jakeholland/firefly/docs/specs/S03-meshclient.md

# S03 · meshclient — embedded Meshtastic client library

## Purpose
A clean, reusable C library that makes this device a Meshtastic *client* — same role as the phone apps — over any byte transport. Wraps framing, the config handshake, node/position/message events, and sending. **Extraction-grade: no firefly includes.**

## Reference
Meshtastic client API docs + the archived Swift client in this repo's `archive/meshtastic-ios-app` branch (working handshake & framing to crib from). Protobufs: `meshtastic/protobufs` pinned submodule-free — vendored generated nanopb sources under `meshclient/proto/` with the generator script `meshclient/tools/gen_nanopb.sh`.

## Interface (`meshclient/include/mc_client.h`)
```c
typedef struct {           // byte transport vtable — UART, TCP, later BLE
  int  (*write)(void *io, uint8_t const *buf, size_t len);
  int  (*read) (void *io, uint8_t *buf, size_t maxlen);   // nonblocking, 0 = nothing
  void *io;
} mc_transport_t;

// Packet metadata Meshtastic already gives a client, translated at this
// boundary into firefly-side enums (issues #33, #35). Protobuf enum values
// never reach core/.
typedef enum { MC_LOC_UNKNOWN, MC_LOC_MANUAL,                 // asserted, not measured
               MC_LOC_INTERNAL, MC_LOC_EXTERNAL } mc_loc_source_t;
typedef enum { MC_RX_PATH_UNKNOWN, MC_RX_PATH_DIRECT,
               MC_RX_PATH_INDIRECT } mc_rx_path_t;

typedef struct {          // per-packet radio measurements, all presence-flagged
  bool has_rssi;  int16_t rssi_dbm;
  bool has_snr;   float   snr_db;
  mc_rx_path_t rx_path;   // rssi/snr attributable to `from` only when DIRECT
} mc_rx_meta_t;

typedef struct {
  void (*on_state)(void *u, mc_state_t s);                     // DISCONNECTED/HANDSHAKE/READY
  void (*on_node)(void *u, mc_nodeinfo_t const *n);            // id, names, hw, battery, rx_path
  void (*on_position)(void *u, uint32_t node, mc_position_t const *p);  // p.loc_source, p.precision_bits
  void (*on_text)(void *u, uint32_t from, uint32_t to, char const *utf8, size_t len);
  void (*on_private)(void *u, uint32_t from, uint32_t to, uint32_t portnum,
                     uint8_t const *payload, size_t len);      // firefly protocol rides here
                     // `to` added by issue #123 ([api]): the MeshPacket's destination,
                     // delivered exactly as on_text delivers it (broadcast / node id /
                     // MC_ADDR_UNKNOWN), so 1:1 private traffic classifies DIRECT.
  void (*on_my_info)(void *u, uint32_t my_node_id);
  void (*on_rx_meta)(void *u, uint32_t from, mc_rx_meta_t const *m);  // every packet w/ a sender
  void *user;
} mc_events_t;

void mc_init(mc_client_t *c, mc_transport_t t, mc_events_t ev, ff_clock_t const *clock);
void mc_tick(mc_client_t *c, uint32_t now_ms);   // pump read/parse/heartbeat; call ~50 Hz
void mc_connect(mc_client_t *c);                  // starts want_config handshake
int  mc_send_text(mc_client_t *c, uint32_t dest, char const *utf8);      // dest=0xFFFFFFFF broadcast
int  mc_send_private(mc_client_t *c, uint32_t dest, uint32_t portnum,
                     uint8_t const *payload, size_t len, bool want_ack);
int  mc_send_position(mc_client_t *c, ff_latlon_t p);        // rarely needed; comms brain owns GPS
mc_state_t mc_state(mc_client_t const *c);
```

## Behavior
- **Framing:** stream protocol `0x94 0xC3 [len_hi] [len_lo] [protobuf FromRadio/ToRadio]`; resync on garbage by scanning for magic; max frame 512 B.
- **Handshake:** on connect send `ToRadio.want_config_id = random`; consume NodeInfo/Config/Channel dump; READY on `config_complete_id` match. Auto-reconnect with 2 s backoff if transport errors or 30 s silence (send heartbeat every 15 s).
- **Decode scope v1:** MyNodeInfo, NodeInfo, Position, MeshPacket(decoded: TEXT_MESSAGE_APP, POSITION_APP, PRIVATE range). Everything else skipped silently but counted (`mc_stats`).
- **nanopb** with static allocation; callback fields sized: names 40 B, text 237 B (Meshtastic max).
- **Packet metadata (added for #33/#35).** Meshtastic already hands a client more than the payload; this library surfaces it instead of dropping it, translated into firefly-side enums:
  - **Position provenance.** `Position.location_source` → `mc_position_t.loc_source`. MANUAL means the position was *asserted* (an installer typed it in), not measured — a fixed-position landmark re-broadcasts the same asserted point forever, so freshness is a category error for it (#33). `LOC_UNSET` and an absent field are the same bytes on the wire (proto3 implicit presence); both fold to `MC_LOC_UNKNOWN`, which is a distinct enum member, not a sentinel. Unrecognized future wire values also fold to UNKNOWN rather than leaking a raw number.
  - **Per-packet RSSI/SNR.** `MeshPacket.rx_rssi`/`rx_snr` → `on_rx_meta`, fired for **every** inbound packet naming a sender — including encrypted payloads and out-of-decode-scope portnums, since the radio measured the signal regardless. Breadth is deliberate: position broadcasts alone arrive on a multi-minute interval, far too slow for a 5 s RSSI trend window. Fires *before* the payload event for the same packet, so callers can correlate by `from` without buffering.
  - **Hop path is the qualifier, not a nicety.** RSSI is measured against whatever signal actually arrived — for a relayed packet that is the *relay's* transmission, not the originator's. `mc_rx_path_t` says whether the reading may be attributed to `from` at all. Derived from `hop_start`/`hop_limit`, plus the sender's `Data.bitfield` as the tell for firmware new enough to populate `hop_start` (pre-2.3.0 never did, so a bare `hop_start == 0` reads UNKNOWN, never DIRECT); `via_mqtt` forces INDIRECT. `NodeInfo` gets the same field from its explicit-presence `hops_away`.
  - **Unknown stays unknown.** Every added field is presence-flagged or has an explicit UNKNOWN member; none uses an in-band sentinel. One irreducible gap is documented rather than papered over: `rx_snr` has implicit presence, so a genuine 0.0 dB reading is byte-identical to an absent field and is therefore reported as `has_snr == false` — under-claiming rather than fabricating.
  - **Implausible is not a measurement.** Both readings are decoded from unvalidated wire bytes, so both are range-gated (`MC_RSSI_MIN_DBM`/`MC_SNR_MIN_DB` and friends, set far wider than any real radio) and reported **absent** when they fall outside — never clamped, never truncated. `rx_snr` additionally rejects NaN, which compares unequal to everything including `0.0f` and would otherwise pass a bare presence test while silently failing every downstream comparison. Saturating instead of absenting would be actively harmful here: `ff_crew`'s close-range predicate is `rssi_dbm > -60dBm`, which a clamped `INT16_MAX` or a truncated `0` both satisfy, fabricating a CLOSE lock out of a malformed packet.
  - **Coordinate precision (#47).** `Position.precision_bits` → `mc_position_t.has_precision_bits`/`precision_bits`, on both decode paths. Meshtastic channels truncate outgoing coordinates to the channel's `positionPrecision` high bits — 13 on the default public channel, a ~5.8 km grid that produced a measured 2.7 km error indistinguishable from a full fix in the coordinates alone; this field is the only wire-level tell. Present ⇒ 1..32. Implicit presence again: wire `0` is byte-identical to absent (and `0` means "position disabled" in channel config, so it never legitimately accompanies coordinates) — both read absent. A value `> 32` is untrusted-RF garbage and reads **absent, not clamped** (a clamp to 32 would assert full precision for a malformed packet). Absent is never "full precision" — it means the sender didn't say. Presence is *not* uniform across paths in practice (hardware-verified, 2× Heltec V3 @ 2.7.26): live packets stamp the field affirmatively even at full precision (`precisionBits: 32` observed on a `positionPrecision: 32` channel), while the same node's nodeDB row replays with the field absent on both truncated and full-precision channels — stock firmware's `PositionLite → Position` conversion never copies it. NodeInfo positions therefore typically read absent even for senders whose live packets state it, and the replay is the cold-boot path.
  - **Deliberately not surfaced:** `NodeInfo.snr`. It is a cached "SNR of the last message we heard" with implicit presence and no reception timestamp (the same path already hardcodes `has_rx_time = false` for want_config replays). A signal reading that cannot be timestamped cannot feed a trend window, and exposing it would invite treating replayed history as a live measurement.
- Transports shipped: `mc_transport_tcp` (POSIX, sim) and `mc_transport_uart` stub landing with S15.

## Acceptance criteria
1. Framing: byte-dribble (1 byte per read) and garbage-prefix fixtures both yield the framed protobuf exactly once; oversize len resyncs without overflow.
2. Handshake against recorded meshtasticd byte capture (`tests/fixtures/handshake.bin`) reaches READY and emits ≥1 on_node + on_my_info.
3. Position packet fixture → `on_position` with correct 1e-7 degree conversion and rx_time.
4. `send_text` produces a ToRadio frame that meshtasticd accepts (e2e, S14 nightly) and byte-golden matches fixture (unit).
5. `on_private` fires for portnum 256–511 with payload passed through untouched.
6. Silence 30 s → reconnect: state sequence READY→DISCONNECTED→HANDSHAKE observed with mock transport.
7. Library has zero includes from `core/` or `app/` except `ff_clock_t` (moves to a shared `platform/` header).
8. Fuzz smoke: 10k random-byte frames parse without crash/UBSan findings.
9. **Position provenance (#33).** Each `LocSource` value reaches `mc_position_t.loc_source` as its firefly-side counterpart, on both the live-packet and the NodeInfo-replay path. An **absent** field, an explicit `LOC_UNSET`, and an unrecognized future value all read `MC_LOC_UNKNOWN` — never `MC_LOC_INTERNAL`, i.e. "the sender said nothing" is never reported as a GPS measurement. `mc_nodeinfo_t.rx_path` follows `hops_away`'s explicit presence: absent reads UNKNOWN, not DIRECT.
10. **Per-packet radio metadata (#35).** `on_rx_meta` fires with `has_rssi`/`rssi_dbm` and `has_snr`/`snr_db` for decoded, out-of-scope, and encrypted packets alike, and before the payload event for the same packet; never for `from == 0`; and a client that leaves the callback NULL is unaffected. Absent RSSI reads `has_rssi == false` while a genuine **0 dBm** reading reads present-and-zero (the case an in-band sentinel would corrupt). Implausible readings read **absent, not clamped**: an RSSI outside `[MC_RSSI_MIN_DBM, MC_RSSI_MAX_DBM]` (notably `65536`, which truncates to the protected `0`), and an SNR that is NaN, ±infinity, or outside `[MC_SNR_MIN_DB, MC_SNR_MAX_DB]`; `snr_db` is zeroed whenever `has_snr` is false, so an ignored flag never yields NaN. Readings at the edge of the physically plausible (−150/+20 dBm, −30/+15 dB) must still read **present**, so the gate can only reject garbage. `rx_path` is DIRECT only when positively established — `hop_start == 0` without the sender's bitfield, and `hop_limit > hop_start`, both read UNKNOWN; `via_mqtt` reads INDIRECT.

11. **Coordinate precision (#47).** `precision_bits` reaches `mc_position_t` presence-flagged, on both the live-packet and the NodeInfo-replay path. Stated values 1–32 read present (1 and 32 inclusive — boundaries are statements, not garbage); wire `0` reads absent (byte-identical to an absent field, proto3 implicit presence); `33` and arbitrarily large values read **absent, not clamped and not reduced mod 32** (`0xFFFFFFFF` would otherwise read 31). When absent, `precision_bits` is zeroed so a flag-ignoring caller can never pass a `>= N` precision gate on leftover wire bytes.

## Slices
a) framing+resync · b) protobuf gen + decode path · c) handshake state machine · d) send path · e) TCP transport + fixture capture tool (Python script recording meshtasticd session) · f) packet metadata: position provenance + per-packet RSSI/SNR/hop path (AC9, AC10; issues #33, #35) · g) coordinate precision (AC11; issue #47).

**f and g make the data available; they do not consume it.** Wiring `on_rx_meta` into `ff_crew_on_rssi`, and giving `ff_crew` an asserted-position state off the live/stale/lost axis, both belong to S16 slice b1 (callback wiring) — see `docs/specs/S16-app-shell.md`. Until that lands, the Radar face's CLOSE mode still has no path from a radio to the screen. Likewise the *consumer* of precision — the Radar face refusing to render a confident metre-level distance from kilometre-level data — stays with issue #47, alongside the Firefly-channel provisioning that makes full precision available at all.

## Amendments

### `mc_transport_t.write()` backpressure contract (debt/meshclient-contracts)

The vtable's `write()` had no documented contract for a partial or zero
return: `mc_write_bytes`/`mc_send_frame` (`mc_client.c`) treated any
`write() <= 0` as a hard failure and escalated straight to reconnect. Only
`mc_transport_tcp` happened to satisfy that, by retrying `EAGAIN`/
`EWOULDBLOCK` internally up to 200 times so its own `write()` never
actually returns 0. The UART transport landing with S15 will naturally
return 0 for "TX ring full" — treating that as a hard failure would fire a
reconnect storm every time the device's own output momentarily outpaced
the ring.

**Contract, now stated in `mc_client.h`'s `mc_transport_t` doc comment:**
`write()` returns the number of bytes accepted, `0..len`. `0` means
"accepted nothing right now, try again later" — **not** an error. A
negative return is a hard transport failure and is escalated immediately,
no retry.

`mc_write_bytes()` now retries a `0` return up to `MC_WRITE_ZERO_RETRY_BUDGET`
(64, `mc_client.c`) times — a *call* budget, not a wall-clock one: the
retry loop has no clock of its own in scope, no yield point, and no sleep
between attempts, so a millisecond-resolution deadline could read the same
timestamp for the entire loop and fail to bound anything. 64 calls is
chosen to comfortably outlast one transport's momentary stall (a UART TX
ring draining at its own pace) without turning a single frame's
back-pressure into a spurious reconnect, while a permanently stuck
transport still fails in a small, bounded number of calls rather than
spinning forever. `mc_transport_tcp` is unchanged — it still never returns
0, so this budget is never exercised on the shipped dev transport.

Tests: `S03_debt_write_backpressure_below_budget_sends_frame_no_reconnect`,
`S03_debt_write_backpressure_budget_exhausted_triggers_reconnect`,
`S03_debt_write_backpressure_transport_stuck_forever_fails_at_exactly_budget`
(a transport that returns 0 unconditionally, forever — added after review
on #170 so the budget pin isn't coincidental to a countdown mock that
happens to recover exactly at the boundary),
`S03_debt_write_negative_return_fails_immediately`
(`meshclient/tests/test_meshclient.c`).

### Honest `decode_errors` on the live Position path (debt/meshclient-contracts)

`mc_process_mesh_packet`'s `POSITION_APP` branch counted `decode_errors++`
whenever `pb_decode()` succeeded but the message lacked
`latitude_i`/`longitude_i` — indistinguishable, in the stats, from genuine
protobuf corruption. A Position broadcast with no coordinates is a
legitimate "no GPS fix yet" message (both fields are proto3 implicit
presence, so "absent" and "explicit zero" are the same wire bytes); it is
not malformed. The NodeInfo replay path already got this right — it
silently emits nothing for the same missing-coordinates condition, with no
counter touched at all.

**Fix:** `decode_errors` now increments *only* when `pb_decode()` itself
fails. A well-formed, no-fix Position emits no `on_position` event and
touches no counter — matching the NodeInfo path exactly, not even
`decode_skipped` (the portnum *is* in decode scope; nothing was skipped,
there was simply nothing to report).

Tests: `S03_debt_position_no_fix_yet_does_not_count_as_decode_error`,
`S03_debt_position_corrupt_protobuf_counts_decode_error`
(`meshclient/tests/test_meshclient.c`). Mutation-tested: reverting to the
old single-branch `decode_errors++` makes
`S03_debt_position_no_fix_yet_does_not_count_as_decode_error` fail
(`Expected 0 Was 1`) and nothing else.

### Bounded `mc_tick()` drain — `MC_TICK_MAX_FRAMES` (debt/meshclient-contracts)

`mc_tick()`'s read loop previously drained the transport completely in one
call. meshtasticd's `want_config` response can burst a NodeInfo dump of
the whole mesh's node database in one delivery, and `mc_tick()` shares its
calling tick with UI rendering (`ff_shell.c`'s `ff_shell_tick`) — decoding
an unbounded burst back-to-back in one call could stall that shared tick.

**Fix:** `mc_tick()` now dispatches at most `MC_TICK_MAX_FRAMES` (32,
documented in `mc_client.h` next to `mc_client_t`) complete frames per
call. 32 is chosen against the largest realistic burst: even a 100-node
want_config dump (on the order of Meshtastic's stock node-database size on
typical hardware) finishes draining in ~4 calls — well under 100 ms at the
spec's ~50 Hz cadence — while any single `mc_tick()` call never does more
than 32 frames' worth of `pb_decode()` + dispatch.

**Implementation (revised after review on #170):** the first version of
this fix read the transport one byte at a time to make "nothing lost when
the cap lands mid-burst" trivially true, but that traded away the actual
goal — a 4160-byte/40-frame burst went from 66 `transport.read()` calls
(pre-fix, 64-byte chunks) to 4161 (one recv() syscall per byte on TCP), a
regression on cheap-per-tick-work on the shared UI tick. `mc_tick()` now
reads `MC_TICK_READ_CHUNK`-sized chunks again (64 bytes, matching the
pre-existing chunk size), and the "nothing lost" guarantee is carried by
`mc_client_t.tick_carry_buf`/`tick_carry_len`/`tick_carry_pos` instead of
by the read granularity: `mc_framer_t.buf` only ever accumulates the ONE
frame currently in progress, so it can't hold raw leftover bytes spanning
a chunk boundary — when the cap lands mid-chunk, the unconsumed remainder
is copied into `tick_carry_buf` and fed to the framer FIRST on the next
`mc_tick()` call, before any further `transport.read()`. No byte is ever
read from the transport without being fed to the framer either within the
same call or (via the carry) the next one, and frame order is preserved
because the carry is always drained before fresh reads resume.

Tests (`test_meshclient.c`):
- `S03_debt_mc_tick_bounded_drain_caps_frames_per_call` — feeds
  `MC_TICK_MAX_FRAMES + 8` (40) frames / 1000 bytes into a fake transport;
  the first `mc_tick()` call dispatches exactly 32, the second dispatches
  the remaining 8, payload ordering checked end-to-end. The same test also
  pins the read-call-count regression: total `transport.read()` calls
  across both `mc_tick()` calls equals `ceil(1000/64) + 1 = 17` (both the
  formula and the literal `17` are asserted), never the review's reported
  4161-calls-for-a-similar-burst shape.
- The existing byte-dribble/resync (AC1) tests exercise `mc_framer_feed()`
  directly and are unaffected; the AC8 fuzz-smoke test calls `mc_tick()`
  in a loop until its mock transport drains, since a single call is not
  guaranteed to drain everything.

Mutation-tested:
- Dropping the carry (stashing nothing, just `break`ing on cap-mid-chunk)
  → `S03_debt_mc_tick_bounded_drain_caps_frames_per_call` fails
  (`Expected 40 Was 38`, frames genuinely lost).
- Restoring byte-at-a-time reads → the same test's read-call-count pin
  fails (`Expected 17 Was 1001`).
Both mutations were reverted with targeted edits after a fresh rebuild
confirmed the failure (object-file hash checked to rule out a stale
binary).

### `FromRadio.rebooted` is an immediate session loss, not a silence timeout (debt/S03-reboot-session-loss, NAME-in-Settings bench finding 2026-09-06)

Bench finding, real puck + comms brain (Meshtastic 2.7.26), frame-level
instrumentation: pushing a Meshtastic `set_owner` admin write (S11's NAME
feature, `mc_send_set_owner`) a second time in the same session got no
routing ack and no `get_owner_response` reply, forever — even though the
comms brain's owner really changed every time (confirmed via the CLI).
Root cause: Meshtastic's `AdminModule` schedules a device reboot a few
seconds after `set_owner` (`saveChanges()` → `rebootAtMsec()`, when no
edit transaction is open). The PhoneAPI session on the other side of
that reboot is fresh and silently ignores this client's packets until a
new `want_config` handshake — but this library's own 30 s no-RX-bytes
watchdog (`mc_tick()`, above) never noticed, because OTHER `FromRadio`
traffic (`queueStatus` frames) kept arriving right through the reboot
and kept resetting `last_rx_ms`.

**Fix**: `mc_process_from_radio()` now handles `FromRadio.rebooted`
(tag 8 — Meshtastic's own explicit "the radio just rebooted" tell) as an
immediate session loss: it calls `mc_begin_handshake()` directly rather
than waiting on the silence watchdog that this exact scenario defeats.
`mc_begin_handshake()` already does everything a fresh reconnect needs —
`mc_framer_init()` (drop anything mid-frame), a brand-new random
`want_config_id` (never reuses the pre-reboot nonce), and
`mc_set_state(MC_STATE_HANDSHAKE)`, which fires `on_state` through the
SAME path an ordinary link drop uses. No second, reboot-specific event
was added: a caller watching link state alone (e.g. `ff_shell.c`'s
`FF_SHELL_LINK_*`) sees the ordinary RECONNECTING → CONNECTED sequence
around a reboot. Not counted as `mc_stats_t.reconnects` (that counter is
for the backoff-reconnect path specifically) or as
`decode_skipped`/`decode_errors` — a well-formed, understood message,
not a failure this library itself experienced. `mc_process_from_radio()`
and the internal `mc_tick_feed_byte()` helper both gained a `now_ms`
parameter to thread the tick's own timestamp through to
`mc_begin_handshake()` rather than re-reading the clock a second time.

Tests (`test_meshclient.c`):
- `S03_debt_reboot_frame_after_ready_drops_state_and_reissues_want_config`
  — a `rebooted` frame after READY drops straight to HANDSHAKE with a
  brand-new `want_config_id` (asserted different from the pre-reboot
  one) and a real `want_config` `ToRadio` frame is re-encoded onto the
  wire (decoded back off `mock_io_t.tx_buf` — real encode/decode, not a
  mock assertion). `my_node_id`/`has_my_node_id` are unaffected (same
  device, same session identity) and `mc_stats_t.reconnects` stays 0.
- `S03_debt_reboot_stale_config_complete_is_ignored_per_handshake_rules`
  — "frames before the new config_complete are handled per the
  handshake rules": a `config_complete` naming the STALE, pre-reboot
  nonce must not complete the NEW handshake, the same rule
  `S03_AC2_handshake_wrong_nonce_stays_in_handshake` already pins for an
  ordinary connect.
- `S03_debt_reboot_then_matching_config_complete_reaches_ready_again` —
  the full round trip: rebooted → fresh handshake → the NEW
  `config_complete` (matching the nonce the reboot handling just picked)
  reaches READY again, exactly like an ordinary cold connect.

The app-level consequence (NAME confirmation polling must not waste a
`get_owner_request` while mid-reboot, and a self-`NodeInfo` replay from
the reconnect's own `want_config` dump is a first-class confirmation) is
`ff_shell.c`'s concern, documented in `docs/specs/S11-settings.md`'s
"Confirmation fix round 4" amendment and `docs/hardware/comms-brain.md`.

### A handshake needs its own deadline — the silence watchdog cannot see a stalled one (debt/S15c-handshake-stall, bench finding 2026-09-13)

Bench finding, real puck (Waveshare ESP32-S3 UI brain) + XIAO comms
brain running Meshtastic 2.7.26 over UART1 GPIO43/44. A fresh boot
handshaked normally (`NONE → RECONNECTING` at 2.86 s, `→ CONNECTED` at
2.88 s). About 7 minutes later, with no USB console attached and the
display dimmed to idle, the link dropped once and then sat in
`RECONNECTING` for 20+ minutes. Throughout that window `diag` reported
`frames_ok` climbing steadily (84 → 92 → 138), `decode_err=0`,
`last_frame_ms` 0.4–11 s, `reconnects=1`, and the `heard` list still
gaining new nodes — so `FromRadio` frames were arriving, framing,
decoding and dispatching the entire time. Only `send`/`dm` were affected,
reporting "queued" and never transmitting, because the shell gates sends
on READY. A reset returned to CONNECTED in 20 ms.

**Root cause** (`mc_client.c`, `mc_tick()`): the client's only liveness
watchdog was "no bytes read for 30 s", measured against `last_rx_ms` —
and `last_rx_ms` is refreshed by ANY inbound byte, in ANY state. A
handshake whose `want_config` went unanswered (the request lost on the
wire, or the `config_complete` reply lost — the drop coincided with S26f
light-sleep/idle dimming, and with a saved owner change on the XIAO)
therefore kept its own watchdog permanently fed by the radio's ordinary
traffic, which `mc_process_from_radio()` happily dispatches regardless of
state. Nothing re-issued `want_config`, and nothing could: the client
only ever sent one per handshake. This is the same blind spot the
`FromRadio.rebooted` amendment above was written for, reached without any
reboot to announce — so no explicit tell exists to key off, and a
deadline is the only honest answer.

**Fix**: a second watchdog, on the handshake itself, measured from when
the `want_config` frame actually went out (`mc_client_t.want_config_sent_ms`)
rather than from the last byte in. After `MC_HANDSHAKE_TIMEOUT_MS`
(10 s — ~11x the SLOWEST answer actually observed, the 0.9 s deliberate
re-handshake, and ~500x the 20 ms cold-boot one) with no `config_complete`,
the client re-sends `want_config`, up to `MC_HANDSHAKE_MAX_RETRIES` (3)
times per handshake; a spent budget escalates to the ordinary
`mc_fail_and_schedule_reconnect()` path, which re-dials with a fresh
nonce and a fresh budget. The retry budget bounds one ATTEMPT; the
reconnect loop outside it is what never gives up, so a drop always
converges to READY while the radio is alive.

Two deliberate choices inside the retry:
- **The nonce is held still, not rotated.** Meshtastic's PhoneAPI echoes
  back whatever `want_config_id` it was given, so keeping it means BOTH
  possible answers complete the handshake: a reply to the re-send, and a
  reply to the original request that was merely slow rather than lost. A
  rotated nonce would discard the latter at the
  `config_complete_id == want_config_id` gate (counting it
  `decode_skipped`) and buy another full timeout of stall. Rotation is
  only correct when the session is KNOWN to be gone — a reboot or a full
  reconnect — and both of those go through `mc_begin_handshake()`, which
  does rotate.
- **The framer is not re-initialized.** By construction of this bug,
  framing is working; re-initing could only discard a legitimate frame
  currently mid-flight.

**`[api]`**: `mc_stats_t` gains `handshake_retries` (monotonic since
boot, re-sends across every handshake), surfaced through
`ff_app_diag_t.handshake_retries`, the bench console's `diag` (a new
`frames_ok/decode_err/reconnects/hs_retries` counters line — the Link
section is now split identity/counters for the same `-Wformat-truncation`
budget reason the Mesh section already is), and
`ff_shell_handshake_retries()` (a cheap accessor the esp32s3 target reads
once per frame to log each retry as it happens, since `meshclient` and
`app` stay target-agnostic and cannot log for themselves). The
distinction from `reconnects` is the diagnostic value: `reconnects`
counts times the link was declared dead and re-dialled; this counts times
the link was ALIVE but the session handshake on top of it went
unanswered — precisely the shape that used to be invisible.

Tests (`test_meshclient.c`), all driving a scripted `FromRadio` stream:
- `S03_debt_handshake_stall_reissues_want_config_and_reaches_ready` — the
  repro. Handshake OK → drop → frames RESUME with no `config_complete` in
  them → the client re-asks on the wire and reaches READY once the stream
  finally answers. The load-bearing assertion is that `reconnects` stays
  at 1 across the whole stall: the flowing traffic must keep the 30 s
  silence watchdog asleep, or the test would pass on the old re-dial path
  while the real bug stood.
- `S03_debt_handshake_retry_keeps_nonce_so_a_late_answer_still_lands` —
  pins the nonce decision: a late answer to the ORIGINAL request still
  reaches READY, with `reconnects` at 0.
- `S03_debt_handshake_retry_budget_escalates_to_a_fresh_reconnect` — a
  handshake nobody ever answers spends exactly `MC_HANDSHAKE_MAX_RETRIES`
  and then escalates to a full reconnect (new nonce, budget reset), which
  completes normally when answered.
- `S03_debt_handshake_answered_within_timeout_never_retries` — the
  negative: a busy handshake (a multi-tick NodeInfo dump) is not a
  stalled one, and a READY link never re-issues `want_config` however
  long it runs.

Retry counts are asserted by decoding every `ToRadio` frame back off
`mock_io_t.tx_buf` and counting the `want_config` ones, not by trusting
`mc_stats_t.handshake_retries` — a retry that bumps a counter without
actually re-asking the radio would fix nothing, and is exactly the
mutation a stats-only assertion would wave through.

The shell half (`test_shell.c`,
`feat_outbox_flushes_after_a_stalled_handshake_recovers`) pins the other
symptom: texts queued during the stall stay queued while the link is
reconnecting — a tick is not a ready edge — and all of them flush, oldest
first, on the not-ready → ready edge when the link converges.

Mutation checks (fresh rebuilds each time; `mc_client.c.o` hashed rather
than the executable, and reverted with targeted edits — both per
`AGENTS.md`'s standing brief):
1. Handshake watchdog disabled outright → the repro plus the nonce and
   budget tests fail (3/4); the negative test correctly still passes.
2. Deadline measured against `last_rx_ms` instead of `want_config_sent_ms`
   — i.e. the original defect reintroduced → identical 3/4 failure. This
   is the proxy check that matters: it proves the scripted stream really
   does keep `last_rx_ms` alive, so a traffic-fed deadline can never fire
   and the tests are not passing for the wrong reason.
3. Nonce rotated on retry → only
   `S03_debt_handshake_retry_keeps_nonce_so_a_late_answer_still_lands`
   fails, exactly the property it exists for.
After reverting, `mc_client.c.o` hashed back to the pre-mutation value
and all 107 `test_meshclient` cases passed.

### Mid-frame resync timeout — a byte gap now costs one frame, not two (debt/link-churn-2026-09-16, festival field-test finding)

Bench finding, real puck + comms brain, 4h17m uptime: `diag` showed 315
`reconnects` / 662 `hs_retries` / 45 `decode_err` out of 1879 frames — a
reconnect roughly every 49s, suspiciously close to the handshake-stall
ladder's own ~42s escalation ceiling (§2 of
`scratchpad/link-churn-2026-09-16.md`, the investigation this fix
implements), meaning the true disruption rate was almost certainly much
higher than the counter showed. Root cause, established by that
investigation and confirmed here: `docs/specs/S26-device-lifecycle.md`'s
own slice (f) says outright that ESP32-S3 light sleep loses in-flight
inbound UART bytes ("the RX bytes that trigger a wake are lost"), and
this file's framer (`mc_framing.c`, `MC_FRAMER_PAYLOAD` state) had **no
timeout on a mid-frame byte gap** — it kept writing whatever arrived next
into the accumulator regardless of how long the wait was, so a light-sleep
window landing mid-frame spliced the FOLLOWING frame's own magic/length
header onto the tail of the frame in progress. That Frankenstein blob
then failed `pb_decode()` in `mc_tick_feed_byte()` (`decode_errors++`) —
and critically, it also consumed the next frame's header, so **one byte
gap cost TWO frames**, not one: the truncated frame, and the well-formed
one immediately after it that never got a chance to be recognized.

**The fix**: `mc_framer_feed()` gains a third parameter, `now_ms` — the
same explicit-caller-supplied-clock convention every other `mc_client`
entry point already uses (`ff_clock_t`; the framer itself still never
calls a clock). `mc_framer_t` tracks `last_byte_ms`, the timestamp of the
most recent byte accepted while a frame is in progress (any state other
than `MC_FRAMER_START1`); if the next byte arrives more than
`MC_FRAMER_RESYNC_TIMEOUT_MS` (50 ms — a judgement call, not a derived
constant; see that macro's own doc comment in `mc_framing.h` for the
full justification against the wire's actual byte time at 115200 baud,
firmware scheduling jitter, and the light-sleep window durations that
actually cause the gaps) after the last one, the frame in progress is
discarded and the state machine resets to `START1` **before** the new
byte is processed — so if that byte happens to be the next frame's own
`0x94` (exactly the splice scenario above), it is recognized as a fresh
frame start immediately, rather than being eaten as bogus payload. Net
effect: a byte gap now costs exactly the ONE frame it interrupted; the
parser resynchronizes on the very next header instead of the one after
that. This is a per-byte INACTIVITY timeout, not a total-frame deadline —
the clock resets on every byte accepted while mid-frame — so a
legitimately slow-but-continuous sender (real, if unlikely, on this
fixed-baud board-to-board link) is never punished, only an actual gap
longer than the timeout is.

**`[api]`**: `mc_framer_feed()`'s signature changes (adds `now_ms`) — every
call site in-tree updated (`mc_client.c`, `fuzz_mc_framing.c`,
`test_meshclient.c`'s existing AC1 tests, none of which needed behavioral
changes beyond supplying a monotonically-nondecreasing clock value).
`mc_framer_t` gains `last_byte_ms` (internal bookkeeping) and
`timeout_discards` — a counter **distinct from `resync_count`**, which
already existed and keeps its existing, narrower meaning ("garbage-prefix
or oversize declared length seen while scanning"); `timeout_discards`
means "a frame that legitimately began was abandoned because it stalled
too long," a different failure shape a bench operator needs told apart
from ordinary line noise. `mc_stats_t` gains `frames_timeout_discarded`
(mirroring the existing `frames_resynced` ← `resync_count` passthrough in
`mc_get_stats()`), and both counters are now surfaced through `diag` (see
this repo's `docs/specs/S26-device-lifecycle.md` amendment for the
sleep-inhibit half of this same fix, and `ff_debug_console.c`'s own
comment for the exact `resync=`/`timeout=` field names appended to the
existing `frames_ok=… decode_err=… reconnects=… hs_retries=…` line —
appended, not reordered, since a bench script parses that line).

**Rejected**: raising the timeout "for safety" — the whole point is to
detect a stall well before the NEXT scheduled light-sleep wake (300ms-
1500ms, `ff_idle.h`'s fast/slow windows) could deliver the colliding
frame, so a timeout anywhere near that scale would defeat the fix for the
fast-window case specifically. Also rejected: applying the timeout only
inside `MC_FRAMER_PAYLOAD` (not the 2-byte magic / 2-byte length header
states) — a gap could in principle land inside the 4-byte header just as
easily as inside the payload, and excluding those states would leave that
narrow but real window unprotected for no benefit; the fix applies the
same per-byte check uniformly to every state except `START1` (ordinary
idle scanning between frames, never a stall).

Tests (`test_meshclient.c`, new `S03_AC1_timeout_*` cases — the existing
`S03_AC1_*` byte-dribble/garbage/oversize-len tests were updated in place
to pass a monotonically-increasing `now_ms` and are otherwise unchanged):
- `S03_AC1_timeout_frame_interrupted_past_timeout_is_discarded_and_resyncs`
  — THE REPRO: frame A truncated mid-payload, a gap past the timeout,
  then frame B arrives in full immediately after. Frame B is recovered
  intact; `timeout_discards` is exactly 1; `resync_count` (the OTHER
  counter) stays 0, confirming this is a clean timeout discard, not
  garbage-scanning.
- `S03_AC1_timeout_frame_interrupted_within_timeout_still_completes` — a
  pause comfortably under the timeout must not lose the frame: the
  "legitimately slow-but-continuous sender" case.
- `S03_AC1_timeout_gap_exactly_at_boundary_is_not_a_timeout` — pins the
  exact comparison (`>`, not `>=`): gap == timeout completes normally,
  gap == timeout + 1 discards. Both halves live in one test so a future
  change to the comparison operator cannot flip one half green by
  accident.
- `S03_AC1_timeout_back_to_back_frames_no_gap_not_regressed` — ordinary
  continuous traffic (no artificial gap at all) must keep working exactly
  as before this fix.
- The AC8 fuzz harness (`fuzz_mc_framing.c`) now advances a simulated
  `now_ms` per byte, occasionally jumping past the timeout, so the
  resync-on-stall path is fuzzed alongside the garbage/oversize-len paths
  it already covered; `timeout_discards` joins `resync_count` in that
  harness's monotonic-counter invariant.

Companion fix (report's #3, `docs/specs/S26-device-lifecycle.md`'s own
amendment): inhibiting light sleep while a handshake is in flight reduces
how OFTEN this mechanism gets exercised in the first place, but does not
replace it — a byte gap can still land mid-frame from other causes (a
forced bench `sleep` command, a future wake source, ordinary scheduling
jitter), so the framer-level fix stands on its own regardless of what
inhibits sleep.
