jakeholland/firefly/docs/specs/S25-power-latch.md

# S25 — Power latch + soft power button (`ff_power`)

Status: draft (2026-09-01). Device-target only (`targets/esp32s3`). Slice (a)
— the battery keep-alive latch — is the whole of this first cut; the button
slices (b+) are scoped here but deferred.

## Why

The Waveshare ESP32-S3-Touch-LCD-1.46 does **not** hard-wire the battery to
the system rail. A soft-latch power circuit gates it: pressing **PWR**
momentarily powers the rail (enough to start booting), and firmware must then
drive the **SYS_EN** hold line high to keep the latch closed. Release SYS_EN
(or hold PWR past the panel's ~6 s hardware force-off) and the rail drops.

The firmware never drove SYS_EN, so on battery the puck died the instant the
user released PWR — it only ran while the button was physically held (the user
was closing the latch by hand) or while USB fed the rail directly (bypassing
the latch entirely). This is fatal for the Lost Lands field test, which is
battery-only. Waveshare's own board driver
([`PWR_Key.c`](https://github.com/yaosy1997/ESP32-S3-Touch-LCD-1.46-Test/blob/main/main/PWR_Key/PWR_Key.c))
is the authority for the pins and sequence.

## Hardware contract (from the board's reference driver)

Both signals are **direct ESP32-S3 GPIOs**, not TCA9554 expander pins — so the
latch has no dependency on the I2C bus / expander bring-up and can be asserted
in the first microseconds of `app_main`:

- **GPIO7 — SYS_EN / PWR_Control** (output). Drive **HIGH** to latch battery
  power on; drive **LOW** for a soft power-off (cuts the rail on battery; on
  USB the board stays up but the latch is released).
- **GPIO6 — PWR key** (input). The PWR button state, read for press /
  long-press detection. Reserved for slice (b); not touched in slice (a).

Neither pin is in the display/touch pin map (`ff_display.c`: 4, 5, 10, 11, 18,
21, 40–46) nor an ESP32-S3 strapping/flash pin, so both are free.

## Slice (a) — the latch (this cut)

A device-only `ff_power` component exposing one call:

```c
esp_err_t ff_power_latch_on(void); /* configure GPIO7 output, drive HIGH */
```

`app_main` calls it as its **first statement**, before the shell alloc and all
peripheral bring-up: on battery the window is only until the user's finger
lifts, so the latch must beat the display init's tens-of-ms of delays. Pure
I/O — no `core/` logic (there is no domain decision here, only a pin drive).

### Acceptance criteria

- **AC1** `ff_power_latch_on` configures GPIO7 as a push-pull output and drives
  it high, returning the `gpio_config`/`gpio_set_level` error verbatim on
  failure (logged); success is logged with the pin number.
- **AC2** It is the first thing `app_main` does — before `s_shell_p` alloc and
  before `ff_bringup_panel`. A latch failure is logged but **non-fatal**: the
  puck keeps booting (on USB it runs regardless; on battery it was going to
  die anyway, and a running-but-unlatched puck on the bench is more debuggable
  than a park loop).
- **AC3** Device-only: the component lives under `targets/esp32s3/components`
  and is never compiled into the sim; the sim build + goldens are unaffected.
- **AC4** No behavior change on USB (the rail is USB-fed; the extra latch is
  harmless), and the field/demo split is untouched (this is config-agnostic —
  it runs in every device build, demo or field).

### Verification

No sim unit test is possible (pure GPIO HAL, no host path) — the honest gate,
matching the other `targets/esp32s3` HAL code (`ff_display`), is:
- device `idf.py build` links STAGE 3, both demo and field configs;
- **on glass**: with the battery connected and USB unplugged, the puck stays
  running after the PWR button is released (the symptom that motivated this).

## Deferred slices (scoped, not built)

- **(b) PWR button read + soft power-off.** Poll GPIO6 (debounced) on a
  periodic task; a long press drives GPIO7 low (`ff_power_off`). The
  press-duration state machine (short / long / the reference driver's
  sleep→restart→shutdown tiers) is **domain logic and belongs in `core/`** as a
  pure, unit-tested `ff_power_fsm` fed tick + level; the target only samples
  the pin and enacts the FSM's decision. Ties to the `ff_button` GPIO0 idea so
  PWR (power) and BOOT (UI) share one input-forwarding shape.
- **(c) Battery gauge.** `BAT_Driver` reads pack voltage via ADC; feed an
  honest charge estimate into the status bar (unknown-until-read, never a faked
  full — the honest-data value). Its own slice — see this spec's Amendments
  for the CORE + SHELL half; the device ADC read (Waveshare ADC1 ch7 / GPIO8,
  12 dB atten, 1:3 divider) and the sim hook are a follow-up PR, not built
  here.
- **(d) Deep sleep.** A long-press "off" that `esp_deep_sleep`s with GPIO wake
  instead of cutting the rail, for faster resume. Depends on (b).

## Amendments

- **2026-09-03, PR #180, S25 slice c, core + shell half (`ff_batt`, `ff_shell_set_batt_mv`).**
  Lands the platform-neutral half of the battery gauge — everything the
  device-side ADC-read PR (this slice's own deferred bullet above) will call
  into. No `targets/esp32s3` change in this PR; the sim still never calls the
  new seam and its `batt_pct` stays honestly -1, same as before. **Revised
  during PR review** (two blocking findings, two should-fixes — see below);
  the design described here is the FINAL one that landed, not the PR's first
  draft.

  - `core/include/ff_batt.h` / `core/src/ff_batt.c`: `int8_t
    ff_batt_pct_from_mv(uint16_t pack_mv)` — a single-cell LiPo open-circuit
    voltage table (3300→0%, 3500→5%, 3600→10%, 3700→30%, 3800→50%, 3900→65%,
    4000→80%, 4100→92%, 4200→100%, piecewise-linear between points, clamped
    at the ends), sourced from the same breakpoints this project's own
    fuel-gauge reference guides (Adafruit's MAX1704x/LC709203F "Custom
    Battery Profile" learn guides, SparkFun's near-identical LiPo Fuel Gauge
    table) already point to — not a datasheet for a specific cell, since this
    project has not picked one. Returns -1 (unknown) for `pack_mv == 0` or
    outside a `[2500, 4600]` mV plausibility window — a reading out there is
    a broken/absent sense line, not an extreme charge level, and is reported
    as unknown rather than clamped into a plausible-looking percent
    (CLAUDE.md's "honest data over pretty data").
  - `ff_batt_filter_t` + `ff_batt_filter_init`/`ff_batt_filter_push`: a
    4-sample PRE-FILLED moving AVERAGE in the mV domain (not a moving
    median — the review's first blocking finding, below) plus Schmitt-style
    hysteresis on the resulting percent, so the shown percent does not
    visibly tick on ordinary ADC noise. The first-ever real reading shows
    immediately (no warm-up wait — "unknown-until-read, then real", this
    spec's own slice (c) framing: a freshly pre-filled window's average
    equals that one sample). A gap of >= 30 s since the previous push resets
    the averaging window instead of blending a stale pre-gap reading with a
    fresh post-wake one (`FF_BATT_FILTER_STALE_GAP_MS`). A sense line that
    goes dead (an implausible/zero reading `FF_BATT_FILTER_DEAD_AFTER` (3)
    times in a row) reverts the display to -1 rather than continuing to show
    a number frozen from before it died (the review's should-fix #3).
  - `app/include/ff_shell.h` / `ff_shell.c`: `[api] void
    ff_shell_set_batt_mv(ff_shell_t *sh, uint16_t pack_mv, uint32_t now_ms)`
    — a push API (`ff_shell_set_heading`'s precedent), running the reading
    through the core filter IMMEDIATELY at push time (not deferred to the
    next tick, unlike `heading_deg`/`my_pos`: the filter needs to see every
    actual reading as its own timed event, not resampled at the shell's tick
    rate — see `ff_shell.c`'s `batt_filter` field comment). `now_ms` is the
    CALLER's own clock reading at the moment of the read, not (as the PR's
    first draft had it) `sh`'s own last-tick clock — the review's should-fix
    #4: `sh->now_ms` defaults to 0 before the shell's first tick, so a
    battery read before that first tick, followed by an ordinary tick and a
    second read shortly after, could look like a many-second gap against the
    stale "time 0" the first read was recorded at and spuriously trip the
    stale-gap reset. The filtered result reaches `ff_shell_view()`'s
    `radar.batt_pct` on the next `ff_shell_tick`, replacing the `-1`
    `ff_shell.c` hardcoded at ~line 1630 ("no battery ADC on either target
    yet"). Before the first push, `batt_pct` stays -1, honestly rendering
    "--%" on both Radar's status bar and the launcher's status row.
  - `shell_render_key`'s LAUNCHER branch (the opaque-overlay render-key mask
    that keeps a live radar arrow / feed churn underneath the launcher from
    rebuilding its tree under a finger) gained a THIRD restored scalar,
    `radar.batt_pct`, alongside the pre-existing `active_face` and unread-
    badge/banner exceptions: the launcher's status row (S26 slice e) renders
    `batt_pct` verbatim, so before this fix a battery reading that changed
    while the launcher was showing (the common case — the launcher is home)
    left the render key byte-identical and the row sat stale, the same
    clobber class the banner exception (issue/PR #157) already fixed for a
    different field.

  **Review findings that changed the design** (docs/review/code-review.md
  item 6, "the proxy" — both blocking findings were measured, not reasoned
  about: the reviewer ran the actual filter against an adversarial input and
  counted displayed transitions):
  - **Blocking #1 — moving-median oscillation.** The PR's first draft used a
    5-sample moving MEDIAN. Fed an input alternating between two mV values
    every push (3720 mV / 3650 mV, 2 s apart — the load-sag pattern a radio
    TX duty cycle actually produces), a median's majority flips every single
    sample once the window is full of alternating values, producing 29/29
    displayed changes over a 60 s run — the exact flicker the hysteresis was
    supposed to prevent. Fixed by switching to a small (4-sample) PRE-FILLED
    moving AVERAGE in the mV domain: averaging is far less sensitive to
    perfect alternation (an even-sized window of alternating inputs
    converges toward the true mean instead of flip-flopping), and
    pre-filling every window slot with the first reading (rather than
    growing the window one sample at a time) avoids a SECOND, unrelated
    instability the growing-mean design change introduced on its own first
    pass — a variable per-sample weight (1/2, then 1/3, then 1/4) during
    warm-up that bounced the display through 3 values before settling. The
    window size (4, not the original draft's 5 or the review's own
    example-suggested 8) was chosen by literally simulating this filter
    against a battery of alternating stress pairs spanning the OCV table and
    picking the smallest window whose worst case held to the review's
    <= 2-change budget.
  - **Blocking #2 — symmetric low-threshold exemption strobed the alert.**
    The PR's first draft exempted BOTH directions of a `FF_BATT_LOW_PCT`
    crossing from the ordinary hysteresis (prompt on the way down, equally
    prompt on the way back up). Fed an input alternating right at the
    boundary (3625 mV = 15% / 3630 mV = 16%), that produced 29/29 flips of
    the amber low-battery state. Fixed by making the exemption ASYMMETRIC:
    a downward crossing into low still promotes immediately and
    unconditionally (the alert must never be delayed, even by 1 point), but
    an upward exit from low now requires the filtered value to clear
    `FF_BATT_LOW_PCT + FF_BATT_HYSTERESIS_PCT` (17) — a full hysteresis
    margin past the boundary, not merely past it — before the display is
    allowed to leave the low band. The 3625/3630 alternation now settles at
    15% (or 16%, phase-dependent) and never leaves it once it lands.

  **Acceptance criteria** (mirroring this spec's own "unknown-until-read,
  never a faked full" framing for slice (c)):
  - **AC1** `batt_pct` is `-1` (unknown) until the first
    `ff_shell_set_batt_mv` call; the very first real reading then shows
    immediately, no multi-sample warm-up delay. Tests:
    `before_any_push_display_is_unknown`, `first_sample_shows_immediately`
    (`core/tests/test_batt.c`); `S25c_batt_mv_reflects_filtered_value_and_dirties_launcher_key`
    (`app/tests/test_shell.c`).
  - **AC2** the mV→percent table is honest and exact at its published
    points, interpolates linearly between them, and reports unknown (not a
    clamped guess) outside the plausibility window. Tests:
    `table_point_3700_is_30_pct`, `table_boundaries_by_literal`,
    `interpolation_midpoint`, `clamps_below_table_to_zero`,
    `clamps_above_table_to_hundred`, `unknown_when_zero`,
    `unknown_below_plausibility_window`, `unknown_above_plausibility_window`
    (`core/tests/test_batt.c`).
  - **AC3** ordinary reading noise (a sub-hysteresis wobble) never changes
    the displayed percent, so it never flickers the status bar/row or dirties
    a render key over noise alone — including ADVERSARIAL, perfectly
    alternating noise (the review's own literal simulation acceptance test:
    a 3720/3650 mV alternation every 2 s for 60 s must produce <= 2
    displayed changes after the first reveal; the fixed filter measures 2).
    Tests: `one_percent_wobble_does_not_move_display`,
    `S180_alternating_3720_3650_settles_within_two_changes`
    (`core/tests/test_batt.c`); the wobble assertion inside
    `S25c_batt_mv_reflects_filtered_value_and_dirties_launcher_key`
    (`app/tests/test_shell.c`).
  - **AC4** `FF_BATT_LOW_PCT` (`ff_radar.h`) crossing DOWNWARD into low is
    never masked by the display hysteresis, even for a sub-threshold move —
    but crossing back UP out of low requires clearing a full hysteresis
    margin past the boundary (asymmetric on purpose; see Blocking #2 above),
    so a reading hovering right at the boundary settles into the low band
    and holds rather than strobing the alert (the review's own literal
    simulation acceptance test: a 3625/3630 mV alternation every 2 s for
    60 s must settle at <= 15% and never leave the low band; the fixed
    filter measures 0 changes after the reveal). Tests:
    `crossing_to_low_shows_promptly_despite_small_delta`,
    `crossing_out_of_low_requires_the_full_exit_margin`,
    `S180_alternating_3625_3630_settles_at_or_below_low_and_stays`
    (`core/tests/test_batt.c`).
  - **AC5** (added by the review's should-fix #3) a sense line that stops
    reporting a plausible reading — `FF_BATT_FILTER_DEAD_AFTER` (3)
    consecutive implausible/zero pushes — reverts the display to -1 rather
    than continuing to show a stale percent as current. Tests:
    `dead_sense_line_reverts_to_unknown_after_the_threshold`,
    `fewer_than_threshold_bad_samples_does_not_revert`,
    `mutation_target_dead_revert_is_load_bearing` (`core/tests/test_batt.c`).
  - **AC6** (added by the review's should-fix #4) `ff_shell_set_batt_mv`
    uses its caller-supplied `now_ms` for every filter decision, never a
    cached shell clock reading — so a battery push before the shell's first
    tick, followed by a tick and a second push shortly after, does not
    spuriously trip the stale-gap reset. Test:
    `S25c_set_batt_mv_before_first_tick_does_not_spuriously_reset`
    (`app/tests/test_shell.c`).

- **2026-09-03, S25 slice c, device + sim half (`ff_power` battery-sense
  ADC, ctl `batt_mv`).** The follow-up this spec's slice (c) bullet (and
  PR #180's own amendment above) named: reads the Waveshare board's
  battery-sense ADC on `targets/esp32s3` and drives `ff_shell_set_batt_mv`
  from `app_main`'s render loop; gives the sim a `batt_mv` ctl command so
  the gauge can be exercised with no physical battery. No `core/`/`app/`
  change (that landed in PR #180) — this PR only samples and forwards.

  - **Hardware, cited** (Waveshare's own reference driver for this exact
    board, `BAT_Driver.c`:
    https://github.com/yaosy1997/ESP32-S3-Touch-LCD-1.46-Test/blob/main/main/BAT_Driver/BAT_Driver.c):
    ADC1 channel 7 (**GPIO8**), `ADC_ATTEN_DB_12`, `ADC_BITWIDTH_DEFAULT`,
    a 1:3 resistive divider, plus a small measured correction Waveshare's
    own code applies on top of the naive ×3 (divide by 0.990476 — their
    silicon's actual divider ratio is not exactly 3:1). Single-cell LiPo,
    no fuel-gauge IC — the divider math is the entire sensor.
  - `ff_power.h`/`.c` (`targets/esp32s3/components/ff_power`, +`esp_adc` in
    its `CMakeLists.txt` `REQUIRES`): `esp_err_t ff_power_batt_init(void)`
    brings up an ADC1 oneshot unit + channel 7, then tries calibration
    tiered curve-fit → line-fit → none (mirroring ESP-IDF's own `esp_adc`
    oneshot example; ESP32-S3 only ever compiles the curve-fit scheme in —
    the line-fit branch is inert on this chip, kept `#if`-guarded for the
    same portability reason the SDK's own example keeps it). Non-fatal on
    failure or on no calibration scheme (logged either way; a puck with no
    battery ADC still boots). `uint16_t ff_power_batt_mv(void)` averages
    `FF_BATT_ADC_SAMPLES` (8) raw `adc_oneshot_read`s, calibrates the
    average, then converts pin mV → PACK mV via ONE named integer constant
    (`FF_BATT_PACK_MV_PER_CAL_MV_X1E6` = round(3.0 / 0.990476 × 1e6) =
    3028847 at full double precision, composing the ×3 divider and the
    ÷0.990476 correction above; a `uint64_t` intermediate avoids
    overflow — review fix: an earlier revision truncated this to
    3028835, one part in ~33000 low). Returns 0 (unknown) on any
    failure or before calibration succeeds — never a fabricated figure.
    Pure HAL: no percent math here, matching `ff_power.h`'s existing
    house rule. Hoisted into its own ESP-free header,
    `ff_power_batt_conv.h`, specifically so a HOST test
    (`targets/sim/tests/test_batt_pack_mv.c`) can pin the conversion by
    literal — cal 1300 → 3938, cal 0 → 0, the `uint16_t` clamp, and the
    round-half-up rule at an exact tie (mutation-checked: the constant
    off by ±1% fails this test). The first successful reading logs
    (`ESP_LOGI`, once) the raw average, calibrated pin mV, and pack mV,
    labelled with which calibration scheme is actually in effect
    (curve / line / NONE), so bring-up can sanity-check against a
    multimeter.
  - `app_main.c`: `ff_power_batt_init()` is called right after the power
    latch (S25 slice a) and logged, non-fatal on failure. One reading is
    pushed via `ff_shell_set_batt_mv` immediately after `ff_shell_init`
    (so the very first face flushed to glass already has it), and again
    every `FF_BATT_SAMPLE_PERIOD_MS` (a named constant, 2000 ms) in the
    main render loop via `ff_time_reached` — the same wraparound-safe
    periodic-deadline convention every other FSM in this file uses.
    app_main only samples and forwards; the core filter (PR #180's
    `ff_batt_filter_t`) decides what is actually shown.
  - Sim: `targets/sim/ctl_server.h`/`.c` gain a `batt_mv` ctl command
    (`{"cmd":"batt_mv","mv":<0..65535>}`, documented in
    `firmware/tools/dev/CTL.md`) that forwards straight to
    `ff_shell_set_batt_mv` (`ctl_loop.c`'s `ctl_loop_batt_mv`) — the sim's
    own affordance for driving the gauge with no ADC hardware, same class
    as `wall`'s bench time-travel and `flare`'s synthetic inbound. New
    test `targets/sim/tests/test_ctl_batt.c` drives it end to end through
    a real ctl/LVGL session: `batt_mv 3700` renders Radar's "30%" (muted);
    `batt_mv 0` renders "--%"; `batt_mv 3400` renders "3%" amber (at/under
    `FF_BATT_LOW_PCT`). Mutation-checked: dropping the
    `ff_shell_set_batt_mv` forward inside `ctl_loop_batt_mv` fails the two
    positive-reading tests (`Expected 30 Was -1` / `Expected 3 Was -1`),
    confirming the test actually exercises the forward and not a proxy.

  **On-glass verification** (no sim unit test can reach the real ADC —
  same posture as slice (a)'s own Verification section):
  - **(a)** Boot log shows the S25c battery-ADC init line
    (`ok`/error name) and, once the render loop's first periodic sample
    fires, the "S25c first battery reading" line — raw average, which
    calibration scheme (curve/line/NONE), calibrated pin mV, and pack mV.
  - **(b)** With a charged battery connected, Radar's/the launcher's
    status bar shows a plausible, non-flickering percent. If a multimeter
    on the pack is available, its reading (mV) should be within ~50 mV of
    the boot log's `pack_mv` — a larger gap means the divider/correction
    constant needs re-deriving for this specific board rather than
    trusted from Waveshare's own measurement.
  - **(c)** Unplug USB (battery only) and watch the percent hold steady
    (no flicker) for at least a minute — the moving-average +
    Schmitt-hysteresis filter (PR #180) doing its job against real load
    noise (radio TX, backlight PWM, LVGL redraw).
  - **(d)** A reading at or under `FF_BATT_LOW_PCT` (15%) shows the amber
    low-battery tint on both Radar's status bar and the launcher's status
    row. May be verified either by draining a real pack to that range, or
    — faster, and what this PR's own CI coverage already exercises — by
    simulating it in the sim via `{"cmd":"batt_mv","mv":3400}` (interpolates
    to 3%) and confirming the same amber tint renders there; the on-glass
    step is only to confirm the real ADC path reaches the same low reading
    honestly when the pack is actually low, not to re-prove the color
    logic itself.

- **2026-09-16, puck/latch-hold-and-crash-evidence — the pad-hold fix
  (owner's field report) + crash/last-session evidence.**

  **The owner's report.** On battery at Lost Lands bring-up, the puck
  "went black; tapping didn't wake it; I held the PWR button a couple of
  seconds and saw the Firefly logo" — the boot splash, meaning the puck
  had gone fully OFF (the SYS_EN latch had opened and the rail had
  collapsed), not asleep. The next boot reported `ESP_RST_POWERON`,
  which is simply true of *that* boot (a real PWR press re-started a
  dead rail) and says nothing about what caused the ORIGINAL drop.

  **Mechanism.** Slice (a)'s `ff_power_latch_on()` (above) drove GPIO7
  high but never called `gpio_hold_en()`. On any digital-core reset —
  `CONFIG_ESP_TASK_WDT_EN=y`'s watchdog trip, a panic
  (`CONFIG_ESP_SYSTEM_PANIC_PRINT_REBOOT`), or a plain `esp_restart()` —
  every GPIO returns to its power-on-reset state for the moment between
  the old image releasing the pin and the new image's `app_main` calling
  `ff_power_latch_on()` again. On USB the rail is fed externally and
  simply reboots (this has never been observed on the bench, which had
  no way to catch it). On battery, nothing else holds SYS_EN during that
  window, so the rail collapses — the chip loses power before its own
  next boot can re-assert the latch, and that next boot is a real
  power-on, indistinguishable in `esp_reset_reason()` from a deliberate
  PWR press. The ORIGINAL reset reason (WDT trip vs. panic vs.
  `esp_restart()` vs. an actual brownout) is lost with it.

  **The fix — pad hold survives the reset (verified: host; expected:
  battery bench).** `ff_power_latch_on()` now calls `gpio_hold_en(GPIO7)`
  immediately after driving it high (`ff_power_latch_seq_on`,
  `targets/esp32s3/components/ff_power/include/ff_power_latch_seq.h`);
  `ff_power_off()` now calls `gpio_hold_dis(GPIO7)` *before* driving it
  low (`ff_power_latch_seq_off`) — reversing that order would make
  power-off return `ESP_OK` while silently not actually happening
  (ESP-IDF's own `gpio_hold_dis()` doc note: a write while still held
  does not reach the pad). Cited from ESP-IDF's `gpio_hold_en()` doc
  comment (`esp-idf/components/esp_driver_gpio` — fetched against this
  project's pinned v5.3.5): *"This function can be used to retain the
  state of GPIOs when the power domain of where GPIO/IOMUX belongs to
  becomes off. For example, chip or system is reset (e.g. watchdog
  time-out, Deep-sleep events are triggered), or peripheral power-down
  in Light-sleep."* That sentence names a watchdog reset explicitly; a
  panic reboot and `esp_restart()` take the same digital-core-reset path
  (the RTC/IO_MUX domain the hold state lives in is not powered off by
  any of the three), so GPIO7 is expected to stay high through all
  three. **Brown-out**: `CONFIG_SOC_BROWNOUT_RESET_SUPPORTED=y`'s BOD
  circuit also triggers a chip/system reset (not a full RTC-domain power
  cycle) on this SoC, so the same citation is expected to cover it too —
  this project has not found ESP-IDF documentation that says so in as
  many words for brownout specifically, so treat it as expected, not
  verified, same as the WDT/panic/`esp_restart` cases below. **What pad
  hold does NOT cover**: an actual loss of chip power (battery physically
  disconnected, or the rail collapsing before `ff_power_latch_on` ever
  runs on a cold boot) — a pad latch inside a chip that has lost power
  cannot preserve anything; this fix narrows the failure to "digital-core
  resets while already latched," it does not make every dark-puck report
  impossible. **Deep sleep**: this codebase does not use
  `esp_deep_sleep` anywhere today (only light sleep, in the BOOT-edge ISR
  interaction, `ff_power.h`'s `ff_power_boot_isr_suspend_for_sleep` doc
  comment) — `gpio_deep_sleep_hold_en()` is NOT called, and per ESP-IDF's
  own docs the per-pin `gpio_hold_en()` alone is not sufficient to
  survive actual Deep-sleep on this chip family; if deep sleep is ever
  added (the deferred slice (d) above), `gpio_deep_sleep_hold_en()` must
  be added alongside it.

  **Verified**: `firmware/targets/sim/tests/test_power_latch_seq.c`
  (host, `ctest`, both AppleClang and `gcc-14`) pins the ON sequence
  (set-high then hold-en, short-circuiting if set-high fails) and the
  OFF sequence (hold-dis then set-low, short-circuiting if hold-dis
  fails) against a recording mock HAL — this is a pure ordering test, not
  a hardware test; it cannot observe whether the real
  `gpio_hold_en`/`gpio_hold_dis` calls behave as ESP-IDF's docs describe
  on this specific board.

  **Still expected, not verified — the owner's own bench test**: on
  battery, Settings → POWER → REBOOT must show the Firefly splash and
  come back on its own, with no PWR press. This has not been run (no
  device build was available in the environment this fix was written
  in — see the PR body); it is the test that would have caught the
  original bug and is the one that should gate merging this.

  **Crash/last-session evidence (same incident, a second, independent
  mitigation)**: because a digital-core reset that beats this fix
  entirely (a true power loss before the hold is in place, or any
  reset type ESP-IDF's hold docs don't cover) still destroys the
  original reset reason, this same branch adds two independent ways to
  reconstruct what happened after the fact — an ESP-IDF core dump to
  flash (`CONFIG_ESP_COREDUMP_ENABLE_TO_FLASH`) surfaced as one line in
  `diag` and the Diagnostics face, and a `core/include/ff_session_log.h`
  NVS heartbeat + `clean_shutdown` flag (written every 60 s, and set
  just before the POWER OFF/REBOOT paths run) that reconstructs "the
  last session stopped unexpectedly, N hours in, at M mV" even when no
  panic/coredump fired at all (a silent brownout, e.g.). See those
  modules' own doc comments and the PR body for what's verified (host
  tests) vs. expected (needs the owner's device to confirm the on-glass
  summary lines actually render against a real crash/unclean stop).

  **Completing the wiring (same PR, finished after the environment's
  network outage).** The above landed as a WIP with the core `ff_power`
  latch-hold sequence and the `ff_session_log` module built and
  unit-tested, but not yet wired to a device build, a console command,
  or a screen. This pass closes those gaps:
  - `sdkconfig.defaults` — `CONFIG_ESP_COREDUMP_ENABLE_TO_FLASH=y` +
    `_DATA_FORMAT_ELF=y` + `_CHECKSUM_CRC32=y`. No custom
    `partitions.csv`: this repo's existing
    `CONFIG_PARTITION_TABLE_SINGLE_APP_LARGE=y` plus the coredump choice
    together resolve (ESP-IDF's own `partition_table/Kconfig.projbuild`
    default rule) to the SDK's built-in
    `partitions_singleapp_large_coredump.csv`. Layout confirmed by
    actually generating the table (`gen_esp32part.py`), not assumed:
    `nvs` 0x9000/24K, `phy_init` 0xf000/4K, `factory` 0x10000/1500K
    (**unchanged** from today), `coredump` 0x187000/64K — table ends at
    0x197000, ~14 MB of the 16 MB flash still free. See the PR body for
    the owner's local-sdkconfig drift-rule lines (S15's own rule: a
    generated `sdkconfig` that already has these keys decided will not
    pick up the new default from `idf.py reconfigure` alone).
  - `app_main.c` — `esp_reset_reason()` translated to
    `ff_reset_reason_t` and logged every boot; `esp_core_dump_image_
    check`/`get_summary`/`get_panic_reason` build the one-line "Last
    crash: ..." when a valid dump exists; `ff_session_log_load` reads
    the previous session's record before this session's first
    heartbeat overwrites it, formatting "Last time: ..." via
    `ff_session_log_format_last_time`. All three reach `ff_shell_diag_
    debug`/DIAGNOSTICS via one new push call, `ff_shell_set_boot_
    evidence` (called once, right after `ff_shell_init`). The 60 s
    heartbeat and the two `clean_shutdown` save sites
    (`ff_power_off_cb`, and immediately before the render loop's own
    `esp_restart()` call) are also new in this pass.
  - `diag`/DIAGNOSTICS — `ff_app_diag_t` gained an eighth section, "Boot
    evidence": `boot_reset_reason` (always known), `last_crash`/
    `last_session` (each "none" until there is something honest to
    report). Rendered as three new DEVICE rows in `scr_settings.c`
    (RESET REASON / LAST CRASH / LAST TIME, after MIC ON-TIME) and one
    new reply line in `dbgconsole_diag`. A new bench command, `diag
    clear` (`FF_DBGCMD_DIAG_CLEAR`), erases the crash evidence — the
    device core dump (`esp_core_dump_image_erase()`, via a new
    `ff_shell_cfg_t.diag_clear_crash` hook, NULL/no-op on the sim) and
    the live `last_crash` line (`ff_shell_diag_clear_crash`) — so a
    read crash does not keep reporting itself forever.
  - Interpretation call: `ff_session_log.h`'s own top comment originally
    scoped `ff_reset_reason_name` to "the boot-time startup LOG line...
    and nowhere else", deliberately excluding it from the Diagnostics/
    `diag` "last time" line (which describes the PREVIOUS session's
    stop, not this boot's own start). The owner's brief asked for THIS
    boot's reset reason to also appear in `diag`/Diagnostics — done as
    a SEPARATE field (`boot_reset_reason`) alongside, never folded into
    `ff_session_log_format_last_time`'s own string, so that module's
    "describes the previous session only" contract still holds; only
    the caller-facing scope note was wrong, not the module design.
  - Brown-out level (item 4 of the owner's brief) — **no change**. The
    owner's local `sdkconfig` has `CONFIG_ESP_BROWNOUT_DET_LVL_SEL_7=y`
    (`CONFIG_ESP_BROWNOUT_DET_LVL=7`, ~2.44 V) — read directly from that
    file, not assumed. That is ESP-IDF's own stock default
    (`default ESP_BROWNOUT_DET_LVL_SEL_7`,
    `esp_system/port/soc/esp32s3/Kconfig.system`), and `sdkconfig.
    defaults` in this repo has never overridden it, so there is no
    drift to report and nothing to change here — a brownout-level
    change is exactly the kind of physical-margin tradeoff this repo's
    "no change unless clearly safe" rule reserves for the owner's own
    call, and there is no evidence in this incident (a >=10 min runtime
    on a full battery, per the owner's own report) that the detector
    threshold itself was the problem.
  - Still not run: the owner's own on-glass bench test (Settings ->
    POWER -> REBOOT on battery). See the PR body.
