jakeholland/firefly/docs/hardware/comms-brain.md

# Comms brain: wiring and setup

The UI puck (Waveshare ESP32-S3-Touch-LCD-1.46) talks to the comms brain
(Seeed XIAO ESP32S3 + Wio-SX1262 running stock Meshtastic) over a 4-wire UART
link at 115200 8N1, 3.3 V logic both sides, no level shifter. Wiring diagram
(same content, drawn): https://claude.ai/code/artifact/3fcda222-93b5-41fb-9b63-eed48aa1336a

Pin facts verified 2026-09-04 from docs.waveshare.com (ESP32-S3-Touch-LCD-1.46),
wiki.seeedstudio.com (XIAO ESP32S3) and meshtastic/firmware
`variants/esp32s3/seeed_xiao_s3/variant.h`.

## Pin map

| Wire | Puck header | XIAO pin | Meshtastic setting |
|---|---|---|---|
| data | TXD · GPIO43 | D3 · GPIO4 | `serial.rxd 4` |
| data | RXD · GPIO44 | D1 · GPIO2 | `serial.txd 2` |
| ground | GND | GND | |
| power  | 3V3 (or shared battery, see below) | 3V3 (or BAT+) | |

- The puck's console is USB-Serial-JTAG ONLY as of the S15c review round (`firmware/targets/esp32s3/sdkconfig.defaults`/`sdkconfig.ci`: `CONFIG_ESP_CONSOLE_USB_SERIAL_JTAG=y`, secondary NONE) — a fresh checkout's UART header pins GPIO43/44 are free for exactly this reason. ESP-IDF's stock default before that fix kept UART0 (GPIO43/44's own default peripheral) as the PRIMARY console with USB-Serial/JTAG only a secondary mirror, so the boot log was actually sharing these pins; see `docs/specs/S15-esp32s3-target.md`'s Amendments for the full reasoning (shared-FIFO corruption risk) and the maintainer action items below.
- **If your board's `sdkconfig` predates this fix** (drift rule, `docs/specs/S15-esp32s3-target.md`): a fresh `sdkconfig.defaults` entry does not reach an already-generated `sdkconfig`. Delete every `CONFIG_ESP_CONSOLE_*` key from the board's `sdkconfig` (or `idf.py fullclean` + reconfigure) and set `CONFIG_FF_LINK_UART=y` by hand before wiring up the comms brain — otherwise the boot log is still on GPIO43/44 despite this file's own claim above, and `FF_LINK` silently stays `NONE`.
- **Same drift rule, new instance (A02 slice D, 2026-09-13):** the SHOW CODE face needs `CONFIG_LV_USE_QRCODE=y`. It is in `sdkconfig.defaults`, but a board `sdkconfig` generated before that entry existed still holds `# CONFIG_LV_USE_QRCODE is not set` and that value wins — verified on the bring-up board, where the build fails to compile `scr_settings.c`. Enable it in `idf.py menuconfig` (Component config → LVGL configuration → 3rd party libraries → QR code), or delete the key from the board's `sdkconfig` and rebuild. `scr_settings.c` has an `#error` that says this, so the failure names the config rather than LVGL.
- A residual, un-Kconfig-able boot-garbage window remains regardless: the ROM's own first-stage boot banner is hardware-fixed to UART0's default pins and prints before any Kconfig setting is even read. Brief, one-time per boot, and absorbed by whichever side's framer resync counter sees it — see the S15 Amendment for the full reasoning. This is why the mesh link itself stays on UART1 (`FF_UART_PORT` default), not UART0, even with the console moved off it.
- **Do not use the XIAO's D6/D7 (GPIO43/44)**: Meshtastic's `seeed_xiao_s3` variant
  assigns them to the L76K GPS (`GPS_TX_PIN 43`, `GPS_RX_PIN 44`). This supersedes
  S15 deliverable 3's "D6/D7" wording.
- D2 (GPIO3) is skipped (strapping pin). D8–D10 (GPIO7/8/9) are the radio's SPI;
  NSS 41, RST 42, BUSY 40, DIO1 39, RXEN 38 are on the B2B connector.

## Power

- **Option B (recommended for the field):** one LiPo, Y-split to both boards'
  battery inputs (puck MX1.25; XIAO BAT+/BAT- pads on the back). Each board keeps
  its own regulator. Charge through ONE board's USB at a time (two chargers on
  one cell must not run together). The XIAO stays on when the puck latches off.
- **Option A (bench):** puck `3V3` header → XIAO `3V3` pin. The puck's MP1605 buck
  is rated 2 A; the SX1262 TX burst is ~120 mA. The XIAO's 3V3 pin is its
  regulator OUTPUT; back-feeding it is common on XIAO but not documented by Seeed —
  measure before trusting it in the field.
- Never use the puck's `5V` pin on battery (USB-only). Never power the Wio-SX1262
  without its antenna.

## Configure the XIAO once (USB, Python CLI)

Flash stock Meshtastic "Seeed XIAO S3" with the web flasher, then:

```
meshtastic --set lora.region US
meshtastic --set serial.enabled true --set serial.mode PROTO \
           --set serial.baud BAUD_115200 --set serial.txd 2 --set serial.rxd 4
meshtastic --set bluetooth.enabled false        # optional, saves power
meshtastic --set-owner "Jake"
meshtastic --ch-set name Firefly --ch-set psk random --ch-index 0   # SUPERSEDED 2026-09-13 - see "Pairing (crew roster)" below
meshtastic --set position.position_broadcast_secs 120 \
           --set position.position_broadcast_smart_enabled true \
           --set position.broadcast_smart_minimum_interval_secs 30
```

PROTO mode exposes the protobuf client API (the same one the phone app uses) on
those pins; the puck's meshclient (S03) speaks it.

**Position broadcast interval, 2026-09-07 (presence-heard-vs-position,
`docs/specs/S02-core-crew.md`'s amendment).** The last three `--set`s above
are new: stock Meshtastic's own default is `position_broadcast_secs 900`
(15 min), which is *longer* than this project's own (pre-amendment)
10-minute LOST threshold — a stationary friend was guaranteed to read LOST
on the Radar/CREW page between their own radio's broadcasts, independent of
anything the puck firmware did. `position_broadcast_secs 120` sets a 2-minute
worst-case interval; `position_broadcast_smart_enabled true` (already the
Meshtastic default, set explicitly here for clarity) means a STATIONARY node
sends far less often than that — smart broadcast only re-sends early on
meaningful movement, so this mostly matters for a moving node crossing the
mesh; `broadcast_smart_minimum_interval_secs 30` floors how often even a
constantly-moving node can re-send, so a jittery GPS fix can't spam the
channel. Field names verified against the installed `meshtastic` CLI
(`/Users/jakeholland/.local/bin/meshtastic`, v2.7.11)'s own protobuf config
definitions (`meshtastic.protobuf.config_pb2`): `position.position_broadcast_secs`,
`position.position_broadcast_smart_enabled`,
`position.broadcast_smart_minimum_interval_secs`.

**Airtime note for an 8-node crew.** A Meshtastic position packet is small
(tens of bytes); at the "Long Fast" default LoRa preset commonly used in
the US915 region (SF11/BW250), a packet that size occupies roughly a
quarter- to half-second of airtime — an approximation from public
Meshtastic community figures, not hardware-measured on this project's own
radios, and worth confirming in the field before committing to it. Worst
case (every one of 8 crew nodes moving continuously, all re-sending at the
120 s ceiling) is on the order of 8 packets per 2 minutes shared across the
whole channel — a small fraction of LoRa's air, well under typical regional
duty-cycle/fair-use expectations, but not zero: smart broadcast is what
keeps a STATIONARY festival crew's actual traffic far below this worst
case, which is the common case this interval is tuned for. If a future
festival's crew grows well past 8, or the interval is dropped further,
re-check this estimate rather than assuming it still holds.

## Bring-up order

1. Before the boards arrive: jumper puck TXD↔RXD on its header, flash with
   `CONFIG_FF_UART_LOOPBACK_SELFTEST=y`, confirm the loopback PASS line in the
   boot log (proves the driver + header pins alone).
2. Flash + configure the XIAO over USB (above). Antenna on. Confirm it in the
   Meshtastic app/CLI.
3. Power both off. Wire the four lines. Check the cross: puck TXD → XIAO D3,
   puck RXD ← XIAO D1.
4. Power up. Puck log: `link: UART… TXD=43 RXD=44 115200`, then the meshclient
   handshake and READY within a few seconds. Silence = TX/RX swapped; garbage +
   rising resync counters = wrong baud.
5. A second node (T1000-E / Heltec) sends a position → Radar within 10 s (S15 AC2).

## Pairing (crew roster) — superseded 2026-09-13 by auto-crew

**This section described a bench/field stopgap (`CONFIG_FF_DEV_TRUST_CHANNEL`)
that is now the shipped behaviour under a different name.** See
`docs/specs/S02-core-crew.md`'s 2026-09-13 amendment and
`docs/specs/A02-crew-join.md`.

What changed: membership is no longer "channel membership + an explicit
crew list". **Possession of the crew channel's key is membership** — a
node the radio decrypted on the crew channel has proved it holds a key
that only came from someone who had the crew code, and the roster may
grow on that proof. `CONFIG_FF_DEV_TRUST_CHANNEL` is replaced by
`CONFIG_FF_CREW_AUTO_ON_CHANNEL`, **default y**, with a per-node hide
list (`ff_hidden.h`) for stragglers. The old option is deleted rather
than deprecated; the sim's `ffsim --dev-trust-all` is unaffected and
keeps its single-node-harness meaning.

What that means for the setup block above: the `--ch-set name` line no
longer takes a free-text name. The crew channel's name **is** the crew
code (A02 §1.3 — Meshtastic mixes the channel name into the on-air
channel hash, so a name mismatch makes two radios with the same key
invisible to each other), and both the name and the PSK are derived
from the code:

```
# Provision a radio by hand onto crew code FIRE-4K9M7X
# (PSK from docs/specs/fixtures/A02-crew-codes.json — never retyped by hand)
meshtastic --ch-index 0 \
           --ch-set name FIRE-4K9M7X \
           --ch-set psk base64:dDzJg7oyaJL7kbZwC5/z0I1+ACVos/J420MkSiSecdo= \
           --ch-set module_settings.position_precision 32
```

The `position_precision` line is not optional and not decoration: A02
§1.5 requires the crew channel to state 32 explicitly. `--ch-set` edits
the slot in place, so a radio whose index 0 already carries a precision
(0, or a km-scale value from a previous import) keeps it unless this
line overwrites it — the crew would be encrypted, mutually audible, and
silently sharing positions truncated to a grid. Do not rely on the
"absent means 32" firmware default; absent is only absent on a *fresh*
slot.

or, equivalently and preferably, import the crew's Meshtastic link
(Firefly app → Crew → Advanced → **Copy Meshtastic link**), e.g. with
`meshtastic --seturl <link>`.

**The link carries LoRa config too — do not strip it.** This
contradicted an earlier draft of this doc (and of A02 §1.8), which said
the link carried "no LoRa config" on the theory that region/modem preset
on the importing radio are none of a crew join's business (A02 §1.7,
still true for Firefly's OWN join path — admin `set_channel` never
touches them). That reasoning does not extend to this link: bench-found
2026-09-14, `--seturl` (and the official apps' URL import) **replace**
the target radio's entire `lora_config` with whatever the URL carries —
an absent `lora_config` does not mean "leave it alone", it writes an
EMPTY one (`region UNSET`, `use_preset false`), and a radio with region
`UNSET` cannot hear anything (measured on a Heltec V3). So the exported
link now carries the *exporting* radio's own, current `lora_config`
(region, modem preset, hop limit, tx enabled), copied verbatim — never a
guess, and refused (Copy Meshtastic link is disabled) while the
exporting radio's own region is `UNSET`. If you are instead hand-editing
`--ch-set` as above, this does not apply: `--ch-set` only ever touches
the channel slot you name, never `lora_config`.

Region still comes from the flash-time setup above and is never
auto-set from a phone's locale; a radio with `region UNSET` blocks the
app's Start/Join flow on a one-step picker rather than being guessed
at.

## Field festpack (CONFIG_FF_FIELD_PACK)

A live (non-demo) build loads the real field festpack by default: `CONFIG_FF_FIELD_PACK=y`
(default `y`, `depends on !CONFIG_FF_DEMO_MODE` — mutually exclusive with demo
mode, enforced by both the Kconfig `depends on` and a compile-time `#error`
in `app_main.c`) embeds `firmware/assets/field/lost-lands-2026.festpack.json`
(a verbatim copy of fest-almanac's real Lost Lands 2026 pack — see that
directory's own README for how to refresh it; never hand-edit it) and, on
boot, parses it into the shell via `ff_shell_load_pack` at the same point a
demo build's `ff_demo_seed` runs. That is ALL it does: no crew, no
positions, and no clock are seeded (honest data — `CLAUDE.md`) — only the
festpack itself, so the MAP face gets a real origin and Settings gets a real
UTC offset, from the real mesh. Watch for `firefly: S05 field pack loaded: ...`
(or the parse-error log line) in the boot log to confirm it took.

**Wall-clock consequence:** loading the pack also tightens the S18 wall-clock
plausibility window to the festival's own dates via `ff_wall_window_from_pack`
(±14 days either side of `start_doy`/`end_doy`). For Lost Lands 2026 (Sep
18–20) that window is **2026-09-04T00:00:00Z through 2026-10-05T00:00:00Z**
(unix 1788480000 through 1791158400, exclusive ceiling) — every mesh
timestamp outside it is rejected by the plausibility gate at ANY trust tier
(the same gate `CONFIG_FF_DEV_TRUST_CHANNEL` above has no effect on). A bench
run before **2026-09-04** would have had every incoming timestamp rejected
and the wall clock stuck on the fixed bootstrap window — keep that in mind
scheduling any pre-field bench test.

## Bench console

An opt-in line-command console lets an end-to-end test (or a human at a
terminal) trigger sends, flares, and state dumps over the puck's USB
port — no touchscreen tap needed. Off by default (never ship it on for
a field build): set `CONFIG_FF_DEBUG_CONSOLE=y` (`idf.py menuconfig` →
Firefly bring-up → "Bench/debug console", or by hand in `sdkconfig`).

It reads line commands off the USB-Serial-JTAG port — the SAME port
that already carries the boot log — and is polled only while USB is
connected (the S26f amendment's own connection sample), so it changes
nothing about battery/field operation. Connect with any plain serial
terminal at the puck's USB-Serial-JTAG port (e.g. `idf.py monitor`, or
`screen /dev/tty.usbmodem* 115200` — the console doesn't care about
baud, it's USB-CDC), type a command, press Enter.

Commands (replies are `dbg: `-prefixed; an unrecognized or malformed
line replies `dbg: ? try help`):

| Command | Effect |
|---|---|
| `help` | list the commands below |
| `me` | my node id, link state, my position (ok/lat/lon/age), wall clock (latched?/trust/unix now) |
| `roster` | paired crew: id, name, presence, position |
| `heard` | heard-but-unpaired node ids |
| `send <text>` | crew broadcast — the same send mechanism the composer's SEND button uses |
| `dm <node_hex> <text>` | addressed send to one node (hex, optional `!` or `0x` prefix) |
| `flare` | start a quick flare (same path as the physical 5-tap gesture) |
| `flare cancel` | cancel a flare in progress |
| `wall` | wall-clock latch dump: latched, trust tier, UTC offset, last observation's source node |
| `i2c` | shared I2C bus scan (0x08-0x77, known addresses named) plus a one-shot compass status line |
| `cal` | compass calibration ritual status: active?, progress %, sample count, can-finish?, and whether a calibration is currently stored |
| `cal start` | begin a calibration session (S12 step 3, the figure-eight ritual) |
| `cal finish` | attempt to end the session: persists on >=70% octant coverage, otherwise leaves the old calibration untouched and the session active |
| `cal cancel` | abandon the session; the stored calibration (if any) is untouched |
| `cal clear` | drop the STORED calibration back to identity/uncalibrated |
| `name` | NAME in Settings: stored puck name, mesh-reported name (if any), confirmed/pending, and whether the name was silently adopted from the mesh at boot |
| `name <text>` | commit `<text>` through the EXACT SAME path the Settings NAME row's DONE button uses — sanitize (letters/digits/space), persist, push the Meshtastic owner update — so the mesh push can be bench-tested against real nodes over USB |
| `crew` | A02 slice D2: the crew code the radio reports, which channel index it resolved to, the radio's LoRa region (`?` = not reported yet, `unset` = the real UNSET reading), whether a pre-crew snapshot exists, which controls are offered, and the current/last START or LEAVE operation's phase, failure reason and attempt count |
| `crew start` | A02 slice D2: mint a crew code from the puck's CSPRNG, write the derived channel to the comms brain (`AdminMessage.set_channel`), and verify it by re-reading the channel table — the EXACT SAME path Settings → CREW → START CREW's confirm button uses. Replies with the `crew` status line |
| `crew leave` | A02 slice D2: restore the pre-crew channel snapshot through the same write-and-verify path. Fails honestly with `fail=no_snapshot` when nothing was ever recorded — it never resets to the factory default under the words "your old settings" |
| `diag` | DIAGNOSTICS: the SAME facts the Settings DIAGNOSTICS page shows — link, my position, mesh link-quality, wall clock, compass, device — as eight `dbg: diag ...` lines (Link split identity/counters, Mesh split roster-RF/airtime), plus (2026-09-16 S26f field fix) a ninth `dbg: diag wakes n=<count>; ...` line summarizing the last up to 8 light-sleep wake causes (both scheduled and forced by `sleep`) |
| `mic` | S30: one-shot mic status + level (present/running/rate/frames/errors/age, RMS/peak/envelope dBFS) — honest `present=0` when absent |
| `mic on` / `mic off` | S30: start/stop the onboard I2S1 mic reader (off by default) |
| `mic watch <secs>` | S30: print RMS/peak/envelope once per 250ms for `<secs>` (1-30) seconds, then stop — see `docs/specs/S30-audio-input.md` for the full command reference and the bench acceptance protocol |
| `sleep` / `sleep <ms>` | 2026-09-16 S26f field fix: force ONE light-sleep cycle right now, ignoring the USB-connected inhibit (every wake source stays armed) — reports the wake cause, the touch-INT GPIO level sampled just before sleep and just after wake, and the elapsed time. `<ms>` (50-60000) overrides the default 1500ms timer-wake period. The reply may be lost (USB drops during the sleep itself) — reconnect and read `diag`'s `wakes` line if so. See `docs/specs/S26-device-lifecycle.md` slice (f)'s dated amendment for the full bug + bench evidence |
| `tpint` | 2026-09-16 S26f field fix: poll the touch-INT GPIO level for a fixed 5s window — tap the glass during that window to see whether the line moves |

Every acting command dispatches through `ff_shell_intent` (the SAME
`FF_INTENT_QUICK_FLARE`/`FF_INTENT_FLARE_END` intents the physical
5-tap gesture and the sender overlay's CANCEL button use) or one of the
debug-only seams — `ff_shell_debug_send_text` for `send`/`dm`,
`ff_shell_debug_set_name` for `name <text>` (both `app/include/
ff_shell.h`) — never a new roster-growth path, never a direct mesh send
bypassing the shell. See that header's doc comment and
`app/include/ff_debug_console.h` for the full seam discipline, and
`core/include/ff_dbgcmd.h` for the line parser (table-driven, bounded,
CRLF-tolerant, unit-tested independent of any shell).

Example session (paired with one crew member, `Dana`, `!0000da1a`):

```
me
dbg: me node=!00001000 link=CONNECTED
dbg: me pos ok=1 lat=40.712800 lon=-74.006000 age_ms=1500
dbg: me wall latched=1 trust=TRUSTED unix=1789768900

roster
dbg: roster n=1
dbg: roster id=!0000da1a name=Dana presence=LIVE has_pos=1 lat=40.700000 lon=-74.010000

send crew, meet at the tent
dbg: send ok dest=broadcast

dm da1a on my way
dbg: dm ok dest=!0000da1a

flare
dbg: flare started dur_s=300

flare cancel
dbg: flare cancelled

wall
dbg: wall latched=1 latch_unix=1789768800 trust=TRUSTED offset_min=-240 assumed=0 last_src=!0000da1a rejected=0

i2c
dbg: i2c 0x20 io-expander, 0x2c qmc5883p, 0x51 rtc, 0x53 touch, 0x6b qmi8658
dbg: compass mag=qmc5883p imu=found heading=127 cal=identity

cal start
dbg: cal started

(rotate the puck in a figure eight, then check progress)
cal
dbg: cal active=1 progress_pct=88 samples=340 can_finish=1 cal=identity

cal finish
dbg: cal finished ok progress_pct=100 samples=390

cal
dbg: cal active=0 cal=custom

name
dbg: name stored=(unset) mesh=unknown confirmed=0

name Jake
dbg: name stored=Jake mesh=unknown confirmed=0

(the comms brain's own NodeInfo replay arrives a moment later)

name
dbg: name stored=Jake mesh=Jake confirmed=1

diag
dbg: diag link=CONNECTED node=!00001000 name=DANA/Dana last_frame_ms=800 frames_ok=12045 decode_err=2 reconnects=1
dbg: diag pos src=internal ok=1 lat=39.937100 lon=-82.415200 alt_m=287 sats=9 precision_bits=32 age_ms=4200
dbg: diag mesh crew=1 heard=0 rssi_dbm=-61 snr_db=7.5 direct=1 rf_age_ms=1500
dbg: diag mesh chan_util_pct=12 air_util_tx_pct=3 telemetry_age_ms=60000 pos_bcast_age_ms=4200
dbg: diag time latched=1 trust=trusted src_node=!00001000 offset_min=-300 assumed=0 local=9:46 pm
dbg: diag compass mag=QMC5883P present=1 imu=ok heading_deg=87 cal=set
dbg: diag device batt_mv=3900 batt_pct=82 uptime_s=5025 fw=8c94bef2057c/2026-09-07 free_heap=123456

xyzzy
dbg: ? try help
```

(The scan line above is a real bench capture, 2026-09-05, from a puck
with a current-production GY-273 clone wired up — see "Chip
auto-detection" below for why this board answers at `0x2c` rather than
the `0x0d`/`0x1e` an older clone would.)

`i2c` is a bench diagnostic, not a shell command in the seam-discipline
sense above — it reaches no `ff_shell_*` getter at all. Named addresses:
`0x0d qmc5883l` / `0x1e hmc5883l` / `0x2c qmc5883p` (GY-273
magnetometer — whichever chip `ff_compass_init` actually finds; see the
"Compass" section below), `0x20 io-expander` (TCA9554), `0x51 rtc` (an
aftermarket RTC module on the back header), `0x53 touch` (SPD2010),
`0x6b qmi8658` (onboard IMU). An address not in this list prints bare
(just the hex) rather than a guess. The scan is a two-line diagnostic
on purpose: the bus sweep (what is actually wired up and ACKing)
immediately followed by the compass driver's own one-shot status (what
it believes it found and its last heading/calibration state) — so a
bench engineer sees in one command whether an unresponsive
magnetometer is a wiring problem (never shows up in the scan) or a
driver problem (shows up in the scan but the compass line still
reports `mag=absent`). The compass line's `mag=` field names the
actual chip (`qmc5883l`/`hmc5883l`/`qmc5883p`) rather than a bare
"found", so a bench engineer doesn't have to cross-reference the scan
line above it to know which part responded. On a target with no I2C
bus at all (the sim build), the whole command replies with a single
honest line: `dbg: i2c unavailable on this target`.

## NAME → Meshtastic owner (how the puck's name reaches the mesh)

The Settings "NAME" row (and the bench console's `name <text>`) commit
to two places, in order:

1. **Locally** — `ff_settings_t.my_name`, persisted through the same
   `FF_SETTING_MY_NAME` write-through seam every other setting uses (S16
   slice e). This is what the puck itself remembers.
2. **The comms brain** — a Meshtastic `AdminMessage` carrying
   `set_owner: User{ long_name, short_name }`, sent over the SAME UART
   connection this device already uses as a Meshtastic *client* of the
   comms brain (S03's meshclient library — `mc_send_set_owner`,
   `firmware/meshclient/include/mc_client.h`), addressed to the comms
   brain's OWN node id (`ff_shell_my_node_id`). `want_ack` is always
   true and the packet id comes from the same seeded generator every
   other send on this connection uses.

**Why no admin key is needed.** A client attached over UART/Serial/BLE
— which is exactly this device's relationship to the comms brain, the
same one the official phone app has — gets its outgoing packets'
`MeshPacket.from` zeroed by the comms brain's own firmware before
anything else touches them:

```
// meshtastic/firmware, src/mesh/MeshService.cpp:188 (MeshService::handleToRadio)
p.from = 0;                          // We don't let clients assign nodenums to their sent messages
```

`AdminModule::handleReceivedProtobuf` (`src/modules/AdminModule.cpp`)
only requires a session passkey when `mp.from != 0`:

```
} else if (mp.from == 0) {
    if (config.security.is_managed) { ... }        // local admin: passkey NOT required
}
...
if (mp.from != 0 && !messageIsRequest(r) && !messageIsResponse(r)) {
    if (!checkPassKey(r)) { ... }                   // remote admin: passkey required
}
```

So a `set_owner` this device submits over its own UART connection to
the comms brain arrives with `from == 0` and is trusted without a key
exchange — the exact same "local admin" trust the phone app's own
`set_owner` flow relies on. Verified by reading `meshtastic/firmware`
tag `v2.7.26` (commit `54e0d8d0`) — the same firmware version this
repo's own S03 spec amendments hardware-verified other wire behavior
against (`docs/specs/S03-meshclient.md`, precision_bits/rx_snr).
`mc_send_set_owner`'s own doc comment (`mc_client.h`) carries this same
citation next to the code it justifies.

**Short name derivation** (`ff_meshname_derive_short`,
`core/include/ff_meshname.h`): the first 4 alphanumeric characters of
the long name, uppercased, in that order — non-alphanumeric characters
(spaces, punctuation) are dropped BEFORE truncating, not after, so a
name like "Jake H" derives from the full alphanumeric run ("JakeH")
rather than losing the H to an early space. A name with fewer than 4
alphanumeric characters is never padded with anything fabricated.
Examples: "Taylor" → "TAYL", "Jake" → "JAKE", "Jo" → "JO".

**Confirmation is never assumed.** Accepting a `set_owner` for send
proves nothing about whether the comms brain actually applied it —
`ff_shell.c` never marks the row confirmed until a matching reply
actually says so (`ff_shell_mesh_name_status`/`shell_mesh_name_confirmed`
— the ONE derivation both the Settings row's pill and the bench
console's `name` command read, never two independent guesses). See "How
confirmation works" immediately below for what "a matching reply" means
in practice and why the original design needed a fix.

**Changing your name restarts the comms brain (≈5–10 s off the mesh).**
Meshtastic's `AdminModule` reboots the comms brain a few seconds after
every `set_owner` admin write (see "Root cause found" below) — this is
normal Meshtastic behavior, not a puck bug, and it happens on every
name change, not just the first. During that window the comms brain is
briefly unreachable for everything, not just the name push (no
messages, no position updates either); the NAME row's pill honestly
reads `...` (pending) through it and flips to a checkmark once the
reconnect completes and either the mesh's own NodeInfo replay or a
follow-up `get_owner_request` confirms the new name.

### How confirmation works (bench fix, 2026-09-06)

**The bench finding.** A real puck + comms brain (Meshtastic 2.7.26)
proved the push itself works — `meshtastic --info` against the comms
brain showed the new owner immediately after a `name <text>` — but the
row's pill sat on `...` (pending) indefinitely. Cause: `AdminModule::
handleSetOwner` updates the comms brain's own `nodeDB`/owner in place
and does **not** re-broadcast a fresh self NodeInfo afterward. The next
one a connected client (this puck) would see is either the next
want_config handshake (a reconnect) or the periodic, hours-scale NodeInfo
broadcast — neither of which happens promptly after a wearer taps DONE.
The ORIGINAL "wait for a self NodeInfo" confirmation design (previous
section) was honest — it never confirmed something that hadn't
happened — but it was also useless, because the thing it was waiting for
essentially never arrived within a session.

**The fix.** A successful `set_owner` send now immediately follows up
with its own read: `AdminMessage.get_owner_request` addressed to this
node's own id (`mc_send_get_owner_request`, `meshclient/include/
mc_client.h` — same local-admin, no-key-needed path as `set_owner`
itself, `want_ack` false since the response payload IS the answer). The
reply (`get_owner_response`, a `User`) arrives via a new `mc_events_t.
on_owner` event, and `ff_shell.c`'s `shell_ev_owner` treats it EXACTLY
like a self NodeInfo for confirmation purposes — same cache
(`mesh_owner_name`), same comparison (`shell_mesh_name_confirmed`). The
original self-NodeInfo path (previous section — the want_config replay
on reconnect, or a live update following `MeshService::reloadOwner`'s
own `nodeDB->updateUser` push back to this connected client) is kept as
a SECOND, independent confirmation source — whichever arrives first (or
either one, on a later reconnect) can confirm.

**Retry/timeout.** If no `get_owner_response` arrives within ~10 s
(`FF_NAME_OWNER_REQ_TIMEOUT_MS`, `ff_shell.c`), the request is retried,
up to 3 retries (`FF_NAME_OWNER_REQ_MAX_RETRIES`) — 4 requests total. If
the budget is exhausted with still no reply, the row/console keep
reading the honest `...` pending state forever: this fix closes the
"confirmation never happens" gap, it does not open a new way to
FABRICATE one. A wearer/coordinator can always retry manually by
re-committing the same name (DONE, or the bench console's `name
<text>`), which starts a fresh push-and-poll cycle.

**Mesh-delivery ACK/NAK.** Independently of the `get_owner_response`
round trip, the `set_owner` WRITE's own mesh-level delivery outcome
(Meshtastic `Routing.error_reason`, correlated to the outgoing packet id
via a new `mc_events_t.on_routing_ack` event) is now surfaced too: a NAK
renders as a distinct `!` (amber) on the pill and `ack=nak` on the bench
console — honestly different from the ordinary `...` pending state,
which would otherwise look identical to "still waiting, give it a
moment". This is a ROUTING-layer fact (did the write reach the comms
brain's admin module at all), separate from and not a substitute for the
`get_owner_response`/self-NodeInfo confirmation above — a NAK'd write is
never treated as pending-but-fine, and an ACK'd write is never, by
itself, treated as confirmed (`ff_mesh_name_ack_t`'s own doc comment,
`ff_shell.h`, has the full three-state rationale: NONE/OK/NAK, where
NONE means "no routing reply yet", not "failed").

**Bench console.** `name`'s output line grows three fields:

```
dbg: name stored=<my_name> mesh=<mesh_owner_name|unknown> confirmed=<0|1>[ (from_node)] pushed=<none|long/short> ack=<none|ok|nak> reply=<none|long/short>
```

- `pushed=` — what the CURRENT push cycle actually sent (reset by the
  NEXT `name <text>`/DONE, never accumulated across pushes); `none`
  before any push this session.
- `ack=` — the routing outcome of that push's `set_owner` write; `none`
  until a routing reply for it arrives.
- `reply=` — the most recent `get_owner_response` this push's own
  follow-up request received, if any; `none` until it does. May differ
  from `mesh=`/`confirmed=` if something else changed the owner in
  between (that mismatch is itself honest bench info, not an error).

**Fallback.** The Meshtastic phone app and CLI (`meshtastic
--set-owner "<name>" --set-owner-short "<short>"`) remain a fully
independent way to set the SAME owner identity directly against the
comms brain — this feature is additive, not a replacement path, and
either one can correct the other's mistake.

### How confirmation works, round 2 (bench fix, 2026-09-06, after commit `51e4ae1`)

The round-1 fix above shipped, then a real bench run (real puck, real
comms brain, Meshtastic 2.7.26) found it neither worked nor was fully
honest. Two independent bugs:

**Bug 1 — `get_owner_request` never got a reply.** `name Jake H` showed
`pushed=Jake H/JAKE ack=ok` within 3 s (the `set_owner` write really
lands — `meshtastic --info` confirmed it) but `reply=none` after 21 s
and across every retry: this device's own follow-up question was never
answered. Cause, read straight from `meshtastic/firmware` tag
`v2.7.26.54e0d8d0`, `src/modules/AdminModule.cpp`:

```
void AdminModule::handleGetOwner(const meshtastic_MeshPacket &req)
{
    if (req.decoded.want_response) {
        meshtastic_AdminMessage res = meshtastic_AdminMessage_init_default;
        res.get_owner_response = owner;
        res.which_payload_variant = meshtastic_AdminMessage_get_owner_response_tag;
        setPassKey(&res);
        myReply = allocDataProtobuf(res);
        ...
    }
}
```

`AdminModule` only builds and queues a `get_owner_response` when the
INCOMING request's `Data.want_response` bit is set — the same bit the
Python CLI sets via `wantResponse=True` on every admin read. This
library's `mc_send_get_owner_request` never set it on any send, so a
real `AdminModule` silently declined to reply every time; the
mock-only test harness that originally validated round 1 doesn't
enforce this check the way real firmware does, so nothing caught it
before the bench.

**Fix**: `mc_send_data_packet_ex` (`meshclient/src/mc_client.c`) gained
a `want_response` parameter, threaded onto `meshtastic_Data.
want_response` on the encoded packet; `mc_send_get_owner_request` is
the ONE caller that passes `true`. Verified by decoding the actual
outgoing packet back off the wire in
`feat_get_owner_request_encodes_the_request`
(`meshclient/tests/test_meshclient.c`), not just asserting the call
returned 0.

**Bug 2 — a false positive**, found on the same bench run, independent
of bug 1: `name Jake` (re-pushing the puck's OWN CURRENT name — this
feature's documented retry mechanism for a push that may have silently
failed) reported `confirmed=1` **instantly**, with `ack=none
reply=none` — before any reply could possibly have arrived yet. Cause:
`shell_mesh_name_confirmed` compared the stored name against the
CACHED `mesh_owner_name` with no notion of *when* that cache was last
written relative to the push it was supposedly confirming. A value left
over from an EARLIER confirmation (or the boot prefill) that happened
to already equal the newly-pushed text read as "confirmed" for a
brand-new push nothing had actually answered yet.

**Fix**: a push-generation counter. `name_pushed_seq` (`ff_shell.c`)
increments once per attempted push; `mesh_owner_name_seq` is stamped
with the CURRENT generation every time `mesh_owner_name` is written —
both by the self-NodeInfo path (`shell_ev_node`) and the
`get_owner_response` path (`shell_ev_owner`). `shell_mesh_name_confirmed`
now additionally requires `mesh_owner_name_seq >= name_pushed_seq`: an
observation stamped from an EARLIER generation is stale and reads as
pending, never confirmed, regardless of what string it holds. Both
counters start at 0 and neither resets independently of the other, so
the pre-any-push case (an observation stamped 0 vs. generation 0) still
compares equal — this is exactly what keeps the boot-prefill
"(from_node)" ✓ semantics working: an observation arriving before the
wearer has ever pushed anything is not stale relative to "no push yet".

A new state, `mismatch`, was added alongside `confirmed`/pending/NAK: a
FRESH observation (same freshness test as `confirmed`) that does NOT
match the pushed name — e.g. someone else re-set the owner in between.
This is distinct from a routing NAK, which is silent on what the admin
module's owner actually ended up being; it is also distinct from plain
pending, which means no fresh observation has arrived at all yet.

**Bench console.** `name`'s output line gains two more fields:

```
dbg: name stored=<my_name> mesh=<mesh_owner_name|unknown> confirmed=<0|1>[ (from_node)] seq=<N> pushed=<none|long/short> ack=<none|ok|nak> reply=<none|long/short> mismatch=<0|1>
```

- `seq=` — the push-generation counter itself (0 before any push this
  session), the bench-visible form of the stale-equality fix above.
- `mismatch=` — see the state's own description just above.

**Mutation-verified, both bugs, against the pre-fix code**: removing
the `mesh_owner_name_seq >= name_pushed_seq` clause fails exactly
`S_name_recommitting_the_same_name_does_not_falsely_confirm_from_stale_mesh_state`
and `S_name_recommit_stale_self_nodeinfo_does_not_falsely_confirm_either`
(`test_shell.c`) plus
`dbgconsole_name_recommitting_the_same_name_does_not_falsely_confirm_from_stale_mesh_state`
(`test_debug_console.c`) — nothing else in either 248/34-test suite;
reverting `mc_send_get_owner_request`'s `want_response` back to `false`
fails exactly `feat_get_owner_request_encodes_the_request`
(`test_meshclient.c`) and nothing else in the 91-test meshclient suite.
Both mutations reverted after confirming.

### How confirmation works, round 3 (bench fix, 2026-09-06, after commit `eb1cb06`)

The round-2 fix above shipped. A real bench run (same puck, same comms
brain, Meshtastic 2.7.26) found: the FIRST `name` push after boot
confirmed perfectly — `ack=ok`, a reply within 3 s. Every push after
that, in the SAME session, sat on `ack=none reply=none` forever, even
past the app's full retry budget, despite the comms brain's owner
genuinely changing every time (`meshtastic --info` ended at
`Jake (JAKE)`, matching the LAST push):

```
name Jake H  → seq=1 … after 3 s:  ack=ok  reply=Jake H/JAKE  confirmed=1  (perfect)
name Jake    → seq=2 … after 5s, 30s: ack=none reply=none confirmed=0
name Jake Z  → seq=3 … after 4/12/24/36s: ack=none reply=none
name Jake    → seq=4 … after 4/16/28s: ack=none reply=none
```

**Root cause (found via the sim harness, not by guessing at
undocumented firmware behavior).** `ff_shell_tick`'s `get_owner_request`
retry loop discarded `send_get_owner_request`'s return code — it
counted every scheduled retry attempt against
`FF_NAME_OWNER_REQ_MAX_RETRIES`'s budget whether or not the send
actually reached the wire. A quiet two-node bench (just the puck and
the comms brain, no other mesh chatter) trips this device's own
`mc_client` 30 s no-RX-bytes watchdog into a silent reconnect once
nothing else arrives for that long — exactly the gap a bench operator
leaves between typed commands once a push has confirmed and the mesh
goes quiet again. Any retry attempted while that reconnect is in
flight legitimately fails (`send_get_owner_request` returns nonzero,
the same `state != MC_STATE_READY` gate `mc_send_get_owner_request`
itself already documents) — and the pre-fix code spent the ENTIRE
retry budget on those failed attempts. Once the reconnect completed and
the transport was READY again, there was no budget left to ever ask
again: the row read pending forever despite the comms brain being
perfectly reachable and answering-ready.

**Fix.** `ff_shell_tick`'s retry block (`ff_shell.c`) now only counts a
retry / advances the poll deadline when `send_get_owner_request`
actually returns 0 (a genuine send that reached the wire); a failed
attempt leaves the retry count and deadline untouched, so the SAME
timeout condition simply re-fires next tick — a cheap same-thread state
check, no I/O, while the transport stays down — until it recovers, with
the full retry budget still intact for the reply that follows.

**Tests.** `test_shell.c`'s
`S_name_owner_request_retry_failures_do_not_burn_the_retry_budget`
reproduces the exact bug (more transport-down retry attempts than the
whole budget would allow, then a recovery) and **must fail** on the
pre-fix code — mutation-verified: reverting the fix (restoring the
unconditional `retries++`/`sent_ms = now_ms`) fails exactly this test
and none of the other 250 in the 251-test suite. Two more tests close
the remaining task-brief scenarios and both **already passed before
this fix**, which is itself useful evidence about where the bug was
NOT: `S_name_second_push_in_the_same_session_also_confirms_via_its_own_reply`
(two different names pushed back to back in one session, each getting
its own fresh outgoing packet id, each independently confirming off its
own ack + reply) and `S_name_commit_abandons_a_still_pending_previous_poll`
(a second push committed while the first push's poll is still
outstanding — the old poll's late ack/reply must never confirm or
mismatch-flag the NEW push, which confirms only off its own round
trip). `test_meshclient.c` gains
`feat_two_consecutive_set_owner_round_trips_in_one_session_both_confirm`
— the same two-round-trip scenario through REAL wire encode/decode
(building actual `ToRadio`/`FromRadio` frames, not the app-layer mock)
— which also already passed pre-fix, confirming the meshclient
library's decode dispatch carries no per-session "already answered
once" state.

**Gates.** clang + gcc-14 sim builds green, zero warnings both.
`ctest`: 74/74 test binaries both compilers (251-test `test_shell`,
92-test `test_meshclient`). `run_goldens.sh`: 90/90 fixtures,
byte-identical — no UI changed. esp32s3 device build
(`CONFIG_FF_DEBUG_CONSOLE=y`) compiles clean, zero warnings, **not
flashed**.

**Honesty note on scope.** This fix is a concrete, sim-provable defect
whose timing is consistent with the bench transcript (the ~30s/~32s
gaps between checks line up with `mc_client`'s own 30 s reconnect
watchdog on a quiet mesh, and push 1 always working matches its reply
arriving in 3 s — well inside the 10 s window, before any reconnect
could have fired). It is **not** independently bench-verified as the
sole cause of every symptom above: in particular, a fresh push's OWN
immediate `set_owner` routing ack failing on a session that, by this
theory, had already finished reconnecting before the push was even
typed is not fully explained by this fix alone, and could not be
reproduced in sim absent a real radio (both the app-layer state machine
and the meshclient wire-decode layer check out clean in every sim
reproduction attempted — see the two already-passing tests above). If
`ack=none` on a push's own first attempt persists on the next real bench
run after this fix, the next places to look are the esp32s3 target's
own UART driver/RX path (untested by the sim harness) or a genuine
Meshtastic firmware resource limit on concurrently-tracked local
`want_ack` packets — neither reasoned about further here for lack of a
way to verify without real hardware.

**Correction (2026-09-06, see "Root cause found" below).** The
"honesty note" above turned out to be exactly right that this fix was
not the sole cause: a follow-up bench run against real
frame-level instrumentation (a raw TXLOG/FRAMELOG/RXLOG transcript, not
just the `name` console's summary) found the actual mechanism —
Meshtastic's `AdminModule` reboots the comms brain a few seconds after
`set_owner`, and the PhoneAPI session on the far side of that reboot
silently ignores this device until a fresh `want_config` handshake. The
round-3 fix above is still real and still worth keeping (a quiet bench
DOES also trip the 30 s watchdog, and burning the whole retry budget on
a transport that isn't ready yet is a genuine bug independent of the
reboot), but it was not what the round-3 bench transcript's own
`ack=none reply=none forever` symptom actually reproduces —
`FromRadio.rebooted` is unrelated to the 30 s silence timer and fires
long before it would ever trip. See the new section below for the real
mechanism, the fix, and why the round-3 transcript is fully explained by
it.

### Root cause found: the comms brain reboots after every `set_owner` (bench fix, 2026-09-06, after commit `b828c84`)

A bench run with raw frame-level instrumentation (logging every
TX/decoded-`FromRadio`/RX event, not just the `name` console's summary)
finally caught the real mechanism, on the SAME real puck + comms brain
(Meshtastic 2.7.26) every round above used:

```
push1  TX set_owner id=…14 (ADMIN, want_ack)   TX get_owner_request id=…15 (want_response)
       FRAMELOG variant=11 ×3 (queueStatus)  FRAMELOG variant=2 → routing ACK for …14
       FRAMELOG variant=2 → ADMIN get_owner_response for …15  → confirmed ✓ (within 3 s)
push2  (8 s later) TX set_owner …16, TX get_owner_request …17
       FRAMELOG len=2 variant=8            ← FromRadio.rebooted = true  : THE NODE REBOOTED
       …then only variant=11 (queueStatus) frames for every later TX; no ACK, no reply, not even
       Taylor's ack for a DM; the shell's link state never changes (bytes keep arriving so the
       no-RX watchdog never fires), so the puck never re-handshakes.
```

**Root cause.** Meshtastic's `AdminModule` saves an owner change and
schedules a device reboot a few seconds later (`saveChanges()` →
`rebootAtMsec()`, when no edit transaction is open). Push 1 lands and is
answered just before that reboot fires; push 2 lands *in* the reboot
window and is lost. After the reboot, the far side's `PhoneAPI` session
is fresh and ignores every packet this device sends until a NEW
`want_config` handshake — but `mc_client`'s own 30 s no-RX-bytes
watchdog never notices, because OTHER `FromRadio` traffic (`queueStatus`
frames, `variant=11` above) keeps arriving right through the reboot and
keeps resetting the silence timer. The comms brain applies every push
correctly the whole time (`meshtastic --info` always shows the latest
name) — the owner data was never the problem; the puck's OWN session
handling was.

This also fully explains round 3's own bench transcript above without
needing its own theory: `ack=none reply=none forever, even past the
retry budget` on the SECOND and later pushes in a session is exactly
what "the far side rebooted and stopped listening" looks like from the
puck's side, and it explains why push 1 in EVERY round's bench run
always worked (it's answered before the reboot fires) while later pushes
in the same session did not.

**Fix.**

1. **`mc_client.c`** (`meshclient`): `FromRadio.rebooted` (tag 8,
   Meshtastic's own explicit "the radio just rebooted" tell) is now
   treated as an immediate session loss, not a silence timeout: the
   client drops straight into a fresh `want_config` handshake
   (`mc_begin_handshake`, a brand-new random `want_config_id` — never the
   pre-reboot nonce), the SAME way any other link drop is observed
   (`mc_events_t.on_state(MC_STATE_HANDSHAKE)`, then `READY` again once
   the new `config_complete_id` matches). No second, reboot-specific
   event was added — a caller watching link state alone sees the
   ordinary RECONNECTING → CONNECTED sequence around a reboot. See
   `mc_client.h`'s `mc_tick()` doc comment for the full citation.
2. **`ff_shell.c`** (NAME confirmation): the `get_owner_request`
   retry/timeout poll (`ff_shell_tick`) now only fires while
   `ff_shell_link()` reads `FF_SHELL_LINK_CONNECTED` — sending while the
   link is down (mid-reboot) is not merely wasted, it is *guaranteed* to
   fail, so the poll stays fully armed instead of attempting it. In the
   common case no extra request is even needed: the self `NodeInfo`
   replay that is part of every `want_config` dump — including the one
   the reboot's own re-handshake just ran — already arrives during the
   handshake, before the link reaches CONNECTED, and now stops the poll
   the same way a `get_owner_response` already does (there is nothing
   left worth asking for once a fresh self `NodeInfo` has answered it).
   The bench console's `name` output gains `link=<NONE|RECONNECTING|
   CONNECTED>` so a bench operator can tell "pending because the comms
   brain rebooted" apart from "pending on a live link, still waiting".
3. Round 3's retry-budget fix (above) is unchanged and still correct —
   a quiet bench mesh legitimately does also trip the 30 s watchdog on
   its own, independent of a `set_owner` reboot, and that fix still
   matters for that case. Its PR text has been corrected (this section)
   rather than rewritten, since the fix itself needed no changes.

**Considered and rejected: an admin edit transaction to avoid the
reboot entirely.** Meshtastic's `AdminMessage.begin_edit_settings` /
`commit_edit_settings` exist to batch several config changes into one
save-and-reboot. Checked against the SAME `meshtastic/firmware` tag
`v2.7.26.54e0d8d0` this whole feature already cites
(`src/modules/AdminModule.cpp`/`.h`) to see whether wrapping `set_owner`
in one would let this device skip the reboot altogether:

```cpp
// AdminModule.h
void saveChanges(int saveWhat, bool shouldReboot = true);

// AdminModule.cpp, handleSetOwner (called for set_owner)
if (changed) {
    service->reloadOwner(!hasOpenEditTransaction);
    saveChanges(SEGMENT_DEVICESTATE | SEGMENT_NODEDATABASE);   // shouldReboot defaults true
}

void AdminModule::saveChanges(int saveWhat, bool shouldReboot)
{
    if (!hasOpenEditTransaction) {
        service->reloadConfig(saveWhat);        // persists to flash
    }                                            // else: "Delay save ... until committed" — NOT persisted
    if (shouldReboot && !hasOpenEditTransaction) {
        reboot(DEFAULT_REBOOT_SECONDS);
    }
}

// commit_edit_settings handler
case meshtastic_AdminMessage_commit_edit_settings_tag: {
    hasOpenEditTransaction = false;             // cleared BEFORE the call below
    saveChanges(SEGMENT_CONFIG | SEGMENT_MODULECONFIG | SEGMENT_DEVICESTATE |
                SEGMENT_CHANNELS | SEGMENT_NODEDATABASE);   // shouldReboot defaults true again
    break;
}
```

**Answer: no, a transaction does not avoid the reboot for a change that
must actually persist.** `handleSetOwner` inside an open transaction
skips both the disk write AND the reboot (`hasOpenEditTransaction` is
still true at that point) — but the change also isn't saved yet.
`commit_edit_settings` is what actually persists it, and by the time
`commit_edit_settings`'s own handler calls `saveChanges`,
`hasOpenEditTransaction` has already been reset to `false` one line
above, so `saveChanges`'s `shouldReboot && !hasOpenEditTransaction`
check is true again and it reboots anyway — just deferred from
"a few seconds after `set_owner`" to "a few seconds after `commit_edit_
settings`" instead of avoided. The only way to truly dodge the reboot
would be to never commit, which never persists the name change either —
not an option for this feature. **Fix 1 (treat `FromRadio.rebooted` as
a session loss) stays the correct and only fix** — reboots happen for
this reason and, per its own doc comment, for others too (a firmware
OTA, a manual power-cycle, a crash) that no transaction could ever
avoid.

**Tests.**
- `meshclient` (`test_meshclient.c`):
  `S03_debt_reboot_frame_after_ready_drops_state_and_reissues_want_config`
  (a `rebooted` frame after READY drops straight to `HANDSHAKE` with a
  brand-new nonce, and a real `want_config` frame is re-encoded onto the
  wire — real encode/decode, not a mock),
  `S03_debt_reboot_stale_config_complete_is_ignored_per_handshake_rules`
  (a `config_complete` naming the PRE-reboot nonce must not complete the
  new handshake — the same rule
  `S03_AC2_handshake_wrong_nonce_stays_in_handshake` already pins for an
  ordinary connect), and
  `S03_debt_reboot_then_matching_config_complete_reaches_ready_again`
  (the full round trip reaches READY again, same as an ordinary cold
  connect).
- `app` (`test_shell.c`):
  `S_name_push_during_reboot_window_polls_only_after_reconnect` (a push's
  own `get_owner_request` goes out, the link drops to RECONNECTING, no
  further attempt fires no matter how long that lasts, and once the
  link reconnects a self-`NodeInfo` replay confirms on its own with no
  extra request needed) and
  `S_name_two_pushes_eight_seconds_apart_both_confirm_across_a_mid_session_reboot`
  (the exact bench transcript's own timing: push 1 confirms normally,
  push 2 eight seconds later triggers a reboot mid-poll, and still ends
  up confirmed via the reconnect's replay).
  `S_name_push_during_reboot_window_polls_only_after_reconnect` **must
  fail** on the pre-fix code (no link gate at all on the retry poll) —
  mutation-verified: removing the `sh->link == FF_SHELL_LINK_CONNECTED`
  clause from `ff_shell_tick`'s retry condition fails exactly this test
  and `S_name_two_pushes_eight_seconds_apart_both_confirm_across_a_mid_session_reboot`
  (2 failures) and nothing else in the 253-test suite; reverted after
  confirming (a stale incremental binary gave a false "still passing"
  result on the first attempt — rebuilding from a touched source file
  reproduced the failure correctly, the exact AGENTS.md caveat about
  stale object files).

**Gates.** clang + gcc-14 sim builds green, zero warnings both. `ctest`:
74/74 test binaries both compilers (253-test `test_shell`, 95-test
`test_meshclient`). `run_goldens.sh`: 90/90 fixtures byte-identical — no
UI changed. esp32s3 device build (`CONFIG_FF_DEBUG_CONSOLE=y`) compiles
clean, zero warnings, **not flashed**.

**Honesty note on scope.** This fix is bench-proven against real
frame-level instrumentation for the reboot mechanism itself
(`FromRadio.rebooted` genuinely arrives, exactly where the transcript
shows it), and the meshclient/shell-level fixes above are sim-provable
by the tests listed. What has NOT yet been re-run on the bench after
this specific fix landing is a fresh end-to-end confirmation that a
push made during the reboot's own handshake window now reliably
confirms on real hardware (as opposed to the sim reproduction above) —
the coordinator's next bench session should re-run the exact two-push,
8-seconds-apart transcript this fix targets.

## The puck's back header (photo, 2026-09-04)

2×10 at 1.27 mm pitch. Left column top→bottom: `13 · 12 · RXD · TXD · G · 3V3 · SDA · SCL · G · BAT`.
Right column: `17 · 16 · 15 · 14 · 1 · 0 · DP · DN · G · 5V`. The four link wires sit
together on left rows 3–6 (RXD 44, TXD 43, G, 3V3). Of the extras: 14/16/17 are the
SD card, 15 is the mic clock; 12/13/0/1 are free GPIO.

**Power option C (via the header):** `BAT` → XIAO `BAT+` pad, `G` → `BAT-`. Measure `BAT`
with the puck OFF first: ~3.7–4.2 V = raw cell (XIAO stays on when the puck latches off);
0 V = behind the latch (XIAO powers down with the puck — preferable). One charger at a time.

**Soldering an IDC ribbon directly:** on a 2×10 IDC, conductors alternate rows
(conductor 1 → pin 1, 2 → the opposite pin, 3 → next down the first row, …); pin 1 is the
red-stripe edge. Confirm each stripped conductor against the silkscreen with a continuity
beep before soldering; only 4–5 conductors are needed (RXD, TXD, G, 3V3, optionally BAT).
Heat-shrink each joint and strain-relieve the ribbon to the case.

## Compass (magnetometer)

S15's heading driver (`firmware/targets/esp32s3/components/ff_compass/`) reads
a GY-273 magnetometer off the SAME back header, plus the board's own onboard
QMI8658 6-axis IMU (soldered to the main PCB, no wiring needed) for tilt
compensation. Before this driver landed, `heading_deg` read -1 forever
(docs/specs/S12-first-run.md's 2026-09-03 amendment) — see
`firmware/targets/esp32s3/components/ff_compass/include/ff_compass.h` for the
full contract and register-level citations; this section is the wiring +
bench-facing summary.

**Wiring:** the GY-273's four pins go on the same back header used for the
comms-brain link above — `VCC`→`3V3`, `GND`→`G`, `SDA`→the header's `SDA`
(GPIO11), `SCL`→the header's `SCL` (GPIO10). `DRDY` is unconnected (this
driver polls, it does not use the data-ready interrupt). This is the SAME
physical I2C bus the SPD2010 touch controller (0x53) and TCA9554 IO expander
(0x20) already share — the compass driver adds its own device(s) onto that
existing bus (`ff_display_i2c_bus()`), it never opens a second I2C master on
these pins.

**Chip auto-detection:** older GY-273 boards actually carry a **QMC5883L**
(I2C address `0x0D`) even when silkscreened "HMC5883L"; a genuine
**HMC5883L** (`0x1E`) does turn up on some. Current-production GY-273
clones increasingly ship a **QMC5883P** instead — QST's successor part, I2C
address `0x2C`, CHIP_ID register (0x00) reading `0x80` — confirmed on the
coordinator's own bench 2026-09-05 (a real puck with a QMC5883P-equipped
GY-273 wired and powered; the `i2c` scan above is that capture). `ff_compass_init`
probes all three at boot via each chip's own identification registers and
logs which it found (or "no magnetometer" if none ACKs/identifies — the
puck still boots and runs; the Radar arrow just cannot point). If something
answers at `0x2C` but its chip id isn't `0x80`, the driver logs the id it
actually got and treats the device as unidentified rather than guessing —
same honesty contract as every other "found but didn't check out" case in
this file. The onboard **QMI8658** IMU is at `0x6B` (alt strap `0x6A`); if
it fails to identify, the driver falls back to an assumed-level accel and
logs `compass: no IMU — assuming level` — tilt rejection is unavailable on
that path (a synthesized always-level reading can never indicate tilt).

**Orientation — verify on the bench.** The magnetometer's mounting
orientation (which physical axis is which) is an ASSUMPTION, documented and
isolated to one small `#define` table in `ff_compass.c` ("Axis mapping:
sensor frame -> board frame"), not verified against a real GY-273 glued into
a case yet. The QMC5883P gets its OWN row in that table
(`FF_MAG_QMC5883P_BOARD_*`, currently seeded with the same values as the
QMC5883L/HMC5883L row since it's the same physical module footprint) —
independently correctable without touching the other chips' mapping, since
its internal die orientation is not assumed identical to theirs. To
check/correct either row:

1. Flash a build with `CONFIG_FF_COMPASS=y` (default) and get to the Radar
   face with at least one paired friend so the arrow renders.
2. Rotate the puck flat (screen up) through a full circle by hand, slowly.
   The arrow should track — pointing at the same real-world friend direction
   regardless of which way the puck is held.
3. If the arrow doesn't move at all: check `ff_compass: no magnetometer` /
   `no IMU` in the boot log first — a wiring or address problem, not an axis
   problem.
4. If the arrow moves but in the wrong direction: 90°-off (arrow leads or
   lags the true rotation) means the X/Y source axes are swapped in the
   `FF_MAG_BOARD_*_SRC` (or, on a QMC5883P board, `FF_MAG_QMC5883P_BOARD_*_SRC`)
   defines; mirrored (arrow turns the opposite way from the puck) means a
   sign needs flipping (the matching `*_SIGN` define). Both are isolated to
   that chip's own row — no other file encodes the mapping, and correcting
   one chip's row never touches another's.
5. Tilting the puck should not make the arrow swing wildly (that's what the
   QMI8658 tilt compensation is for); if it does with the IMU confirmed
   present, check the `FF_IMU_BOARD_*` half of the same table.

**IMU mounting — BENCH-VERIFIED 2026-09-05 (z-sense only).** The QMI8658's
identity mapping was wrong: lying flat, face-up, on the real puck, raw accel
read `(-1721, -260, -7877)` — under the old identity map that lands on board
`-z` (~-1g), which `ff_geo_heading_deg` reads as a ~166° tilt and rejects
every sample (`heading_deg` stuck at -1, always). `FF_IMU_BOARD_X_SIGN` and
`FF_IMU_BOARD_Z_SIGN` are now `-1` (`Y` stays `+1`) — flipping X together
with Z keeps the frame right-handed (a 180° rotation about the board's own
`+y`, i.e. the chip is effectively mounted upside-down relative to the board
frame). With the fix, the same bench pose gives accel `(1714, -257, 7862)` →
board `+z` ≈ `+1g` (level) and a steady heading of 104°. **Still pending:**
this only checks the face-up/face-down (z) sense — the X/Y sense under an
actual physical tilt (nose up/down, roll left/right) has NOT been separately
bench-verified. Do the "tilt without wild swinging" check in step 5 above on
a real puck before trusting tilt compensation; if the arrow rotates the wrong
way (or 90° off) specifically while tilted (not while flat), check
`FF_IMU_BOARD_X_SRC`/`FF_IMU_BOARD_Y_SRC` (axis swap) before assuming another
sign flip is needed.

**Calibration status:** `ff_settings_t.compass_cal` / `.cal_valid`
(`core/include/ff_settings.h`) is the persisted calibration slot; this driver
loads it at boot via `ff_shell_settings()` and applies it if `cal_valid` is
set, else runs uncalibrated (identity — no offset, unit scale, zero
declination). No calibration ritual UI exists yet to ever set `cal_valid`
true (S12's figure-eight ritual, still unimplemented per that spec's own
2026-09-03 amendment) — `ff_compass_set_cal()` is the runtime seam that
ritual will call once it exists. Expect headings to be off by whatever the
local hard/soft-iron environment (case magnets, nearby electronics) imposes
until that ritual ships.
