jakeholland/firefly/docs/specs/S00-index.md

# Spec index & build order

Specs are contracts. Acceptance criteria (AC) become test names (`S01_AC3_...`). Status: ☐ unclaimed ◐ in progress ✅ merged.

| # | Spec | Depends on | Lost Lands MVP? | Status |
|---|---|---|---|---|
| S01 | core/geo — bearing, distance, heading fusion | — | YES | ✅ merged (PR #6) |
| S02 | core/crew — crew model & freshness state machine | S01 | YES | ✅ merged (PR #11) |
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
