jakeholland/firefly/docs/screens/a03-s1a-diagnostics.png

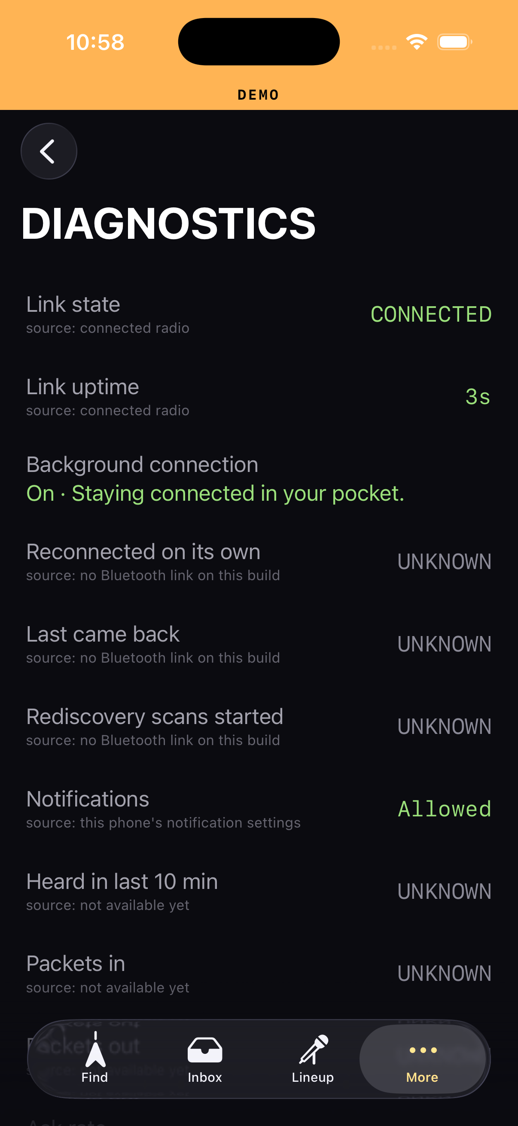
docs/screens/a03-s1a-diagnostics.png
