jakeholland/firefly/docs/screens/a03-s1b-diagnostics.png

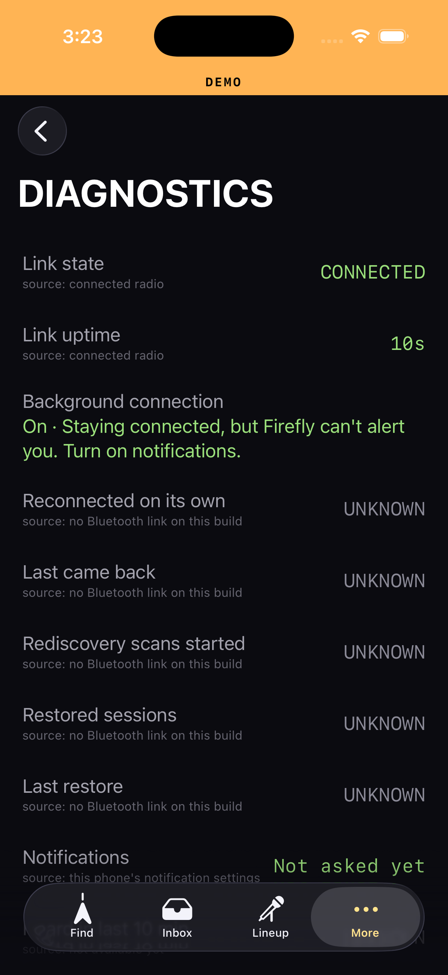
docs/screens/a03-s1b-diagnostics.png
