jakeholland/firefly/docs/screens/demo/inbox.png

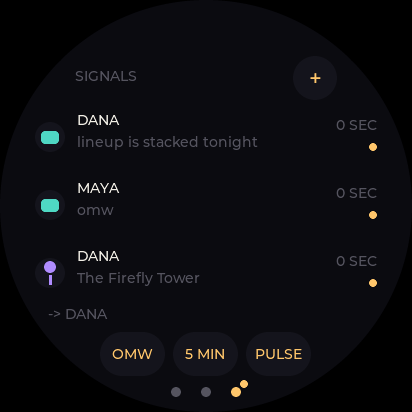
docs/screens/demo/inbox.png
