jakeholland/firefly/docs/screens/demo/lineup.png

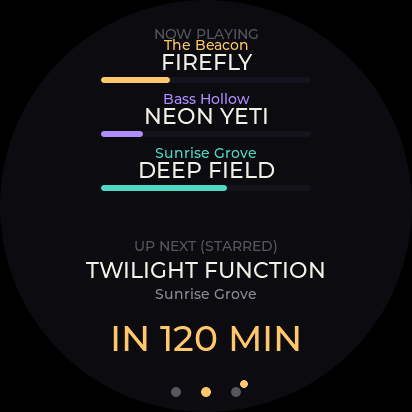
docs/screens/demo/lineup.png
