jakeholland/firefly/docs/screens/demo/map.png

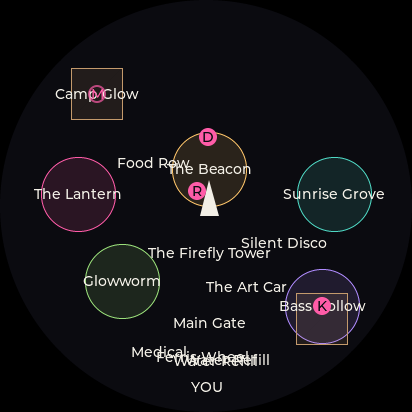
docs/screens/demo/map.png
