jakeholland/firefly/docs/screens/demo/radar.png

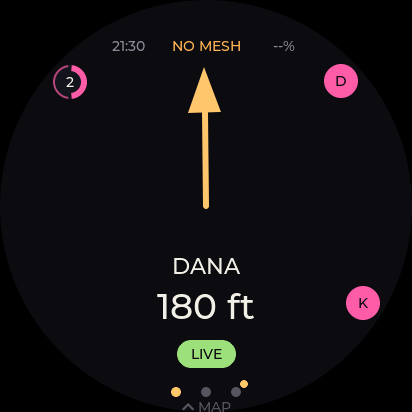
docs/screens/demo/radar.png
