jakeholland/firefly/docs/screens/demo/radar_maya.png

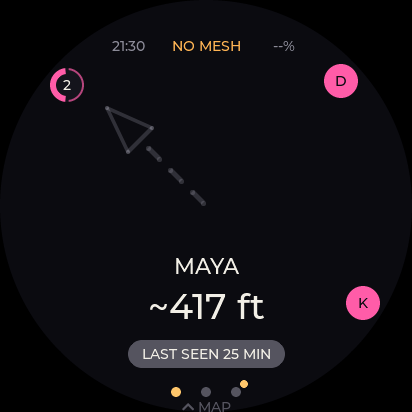
docs/screens/demo/radar_maya.png
