jakeholland/firefly/docs/screens/demo/radar_riley.png

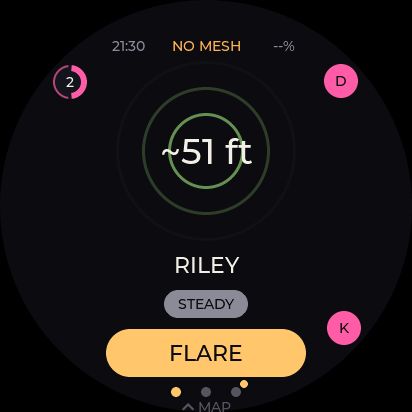
docs/screens/demo/radar_riley.png
