jakeholland/firefly/docs/screens/demo/radar_sam.png

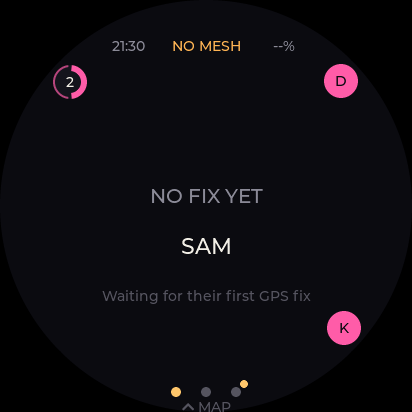
docs/screens/demo/radar_sam.png
