jakeholland/firefly/docs/screens/inbox-thread-crew-before-quick-replies.png

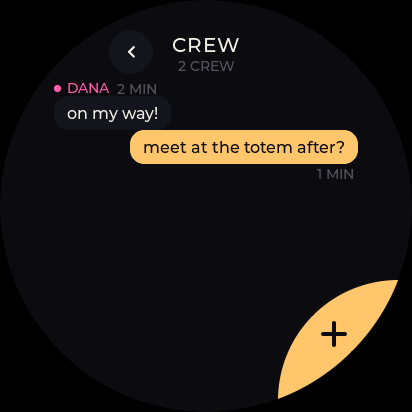
docs/screens/inbox-thread-crew-before-quick-replies.png
