jakeholland/firefly/docs/screens/lineup-bass-canyon-starts-only.png

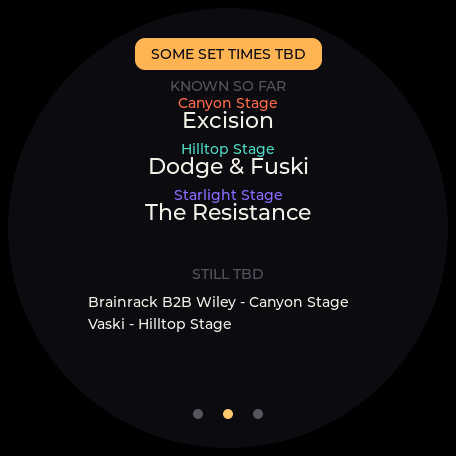
docs/screens/lineup-bass-canyon-starts-only.png
