jakeholland/firefly/docs/screens/radar_close_pressed.png

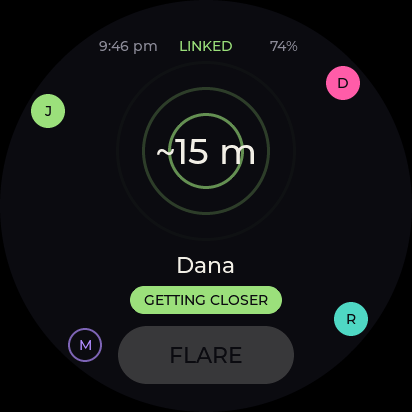
docs/screens/radar_close_pressed.png
