jakeholland/firefly/docs/screens/s22_inbox_crew_presence.png

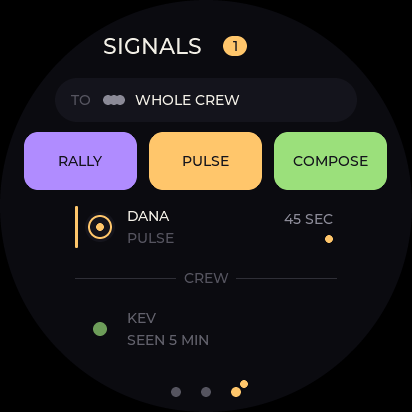
docs/screens/s22_inbox_crew_presence.png
