jakeholland/firefly/docs/screens/s24b-inbox-inbox.png

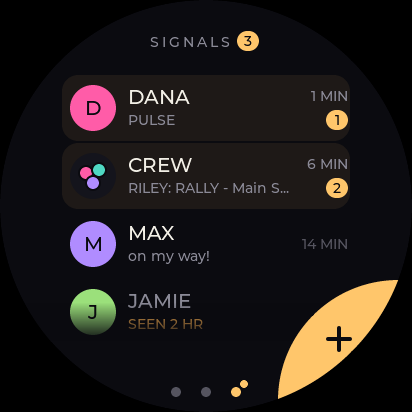
docs/screens/s24b-inbox-inbox.png
