jakeholland/firefly/docs/screens/s24b-inbox-picker.png

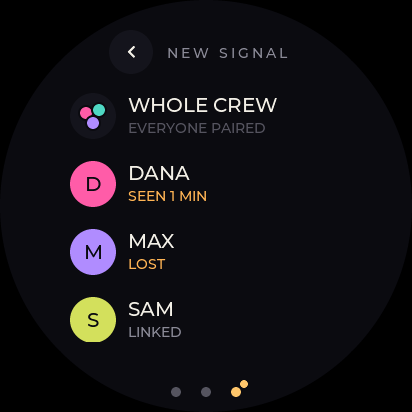
docs/screens/s24b-inbox-picker.png
