jakeholland/firefly/docs/screens/settings_default_pressed.png

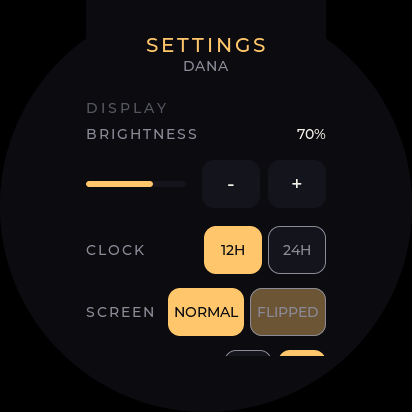
docs/screens/settings_default_pressed.png
