jakeholland/firefly/hardware/case/renders/bay_inside.png

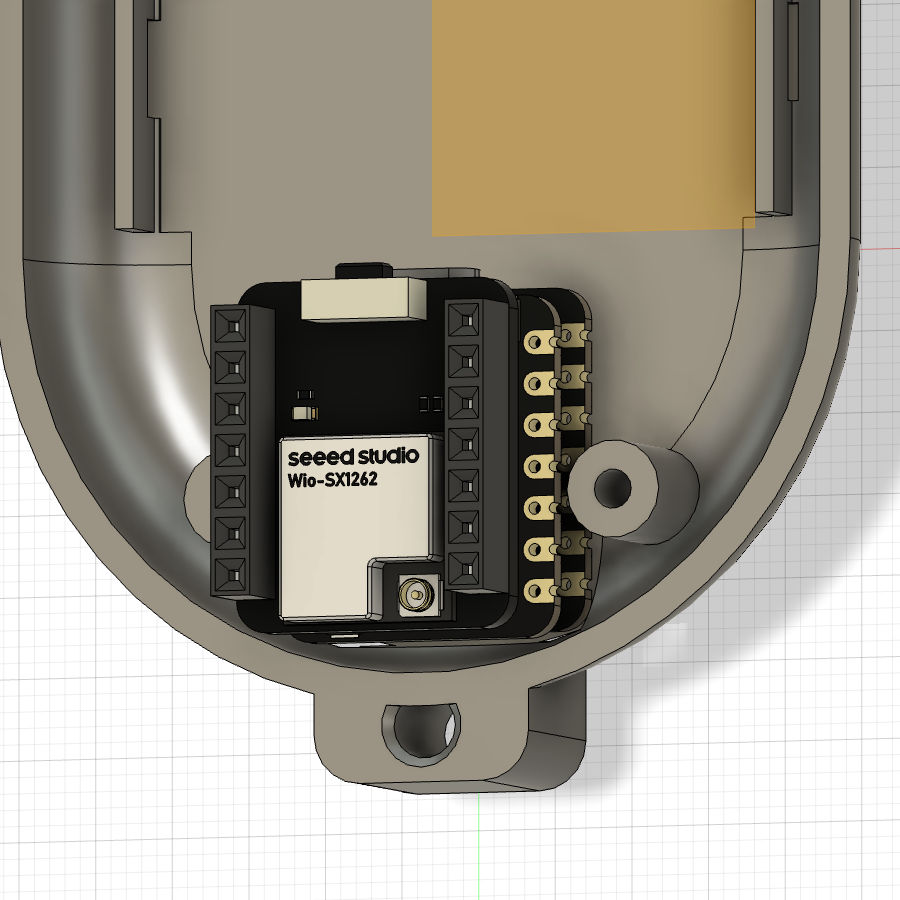
hardware/case/renders/bay_inside.png
