jakeholland/firefly/hardware/case/renders/current_front.png

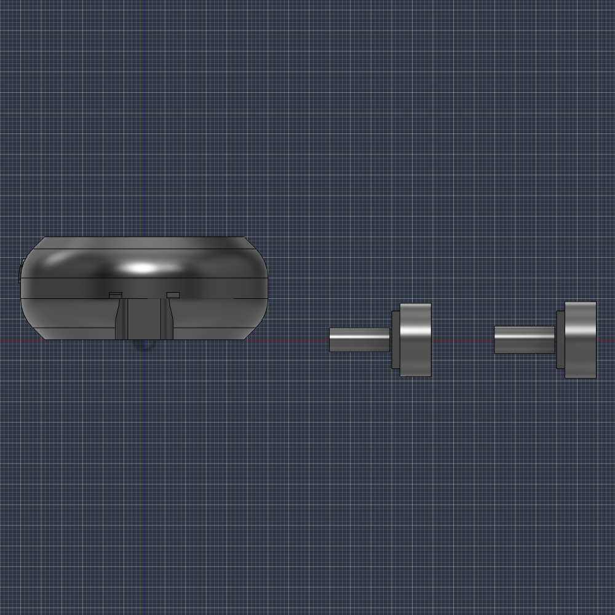
hardware/case/renders/current_front.png
