jakeholland/firefly/hardware/case/renders/current_iso.png

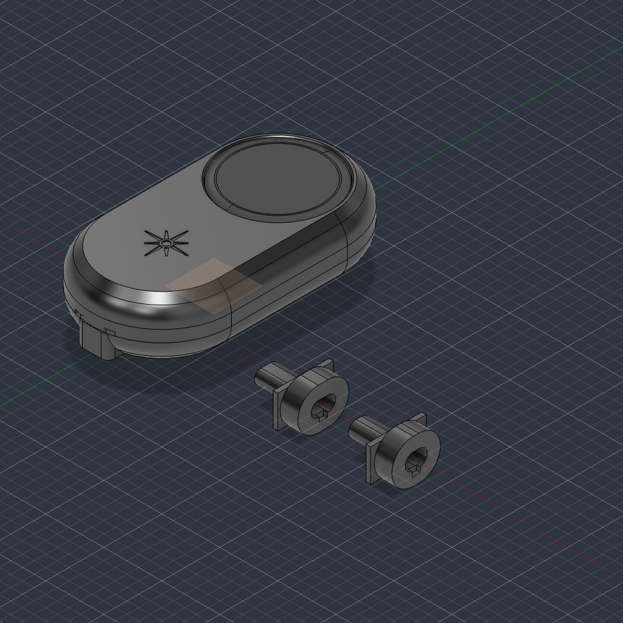
hardware/case/renders/current_iso.png
