jakeholland/firefly/hardware/case/renders/current_right.png

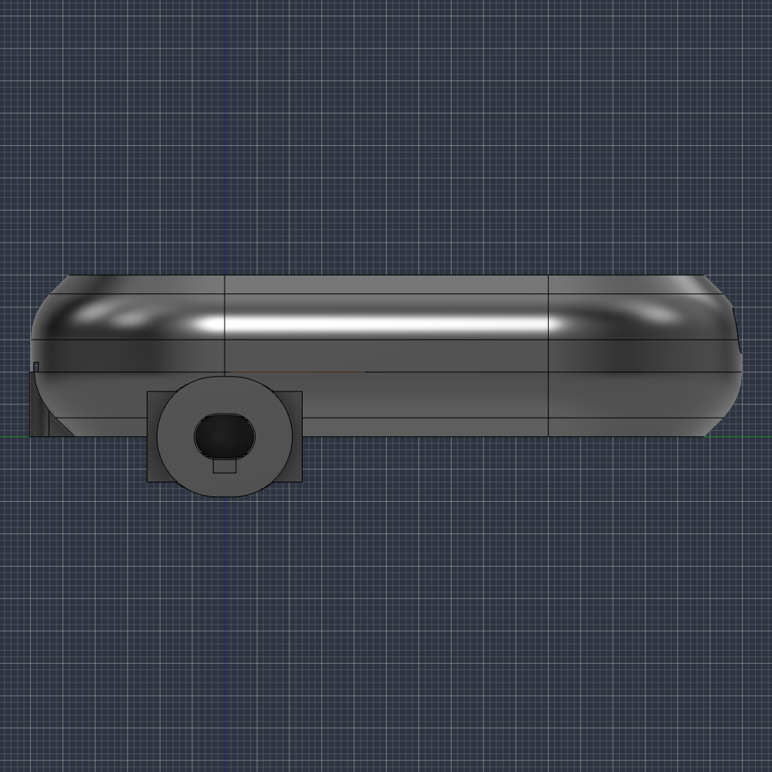
hardware/case/renders/current_right.png
