jakeholland/firefly/hardware/case/renders/current_top.png

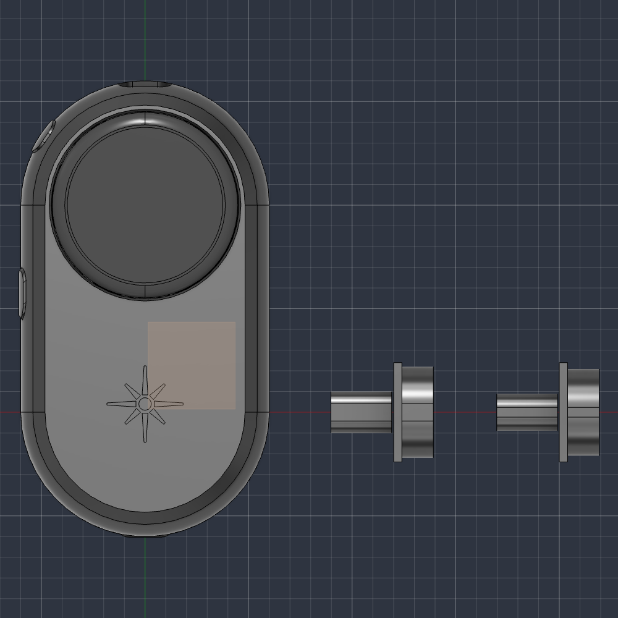
hardware/case/renders/current_top.png
