jakeholland/firefly/hardware/case/renders/home_button_ext.png

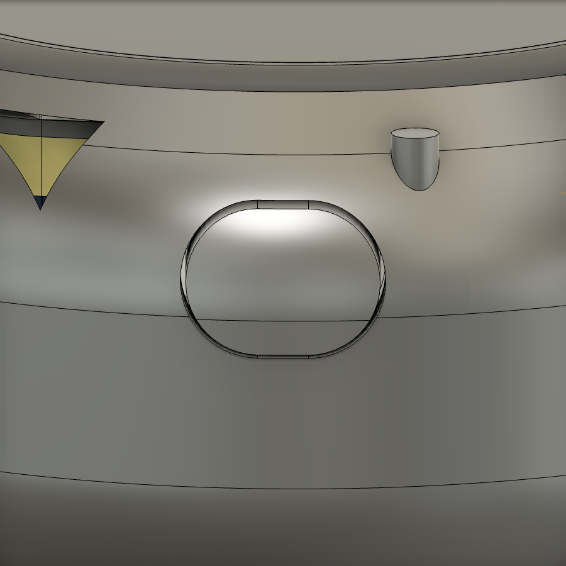
hardware/case/renders/home_button_ext.png
