jakeholland/firefly/hardware/case/renders/lanyard_end.png

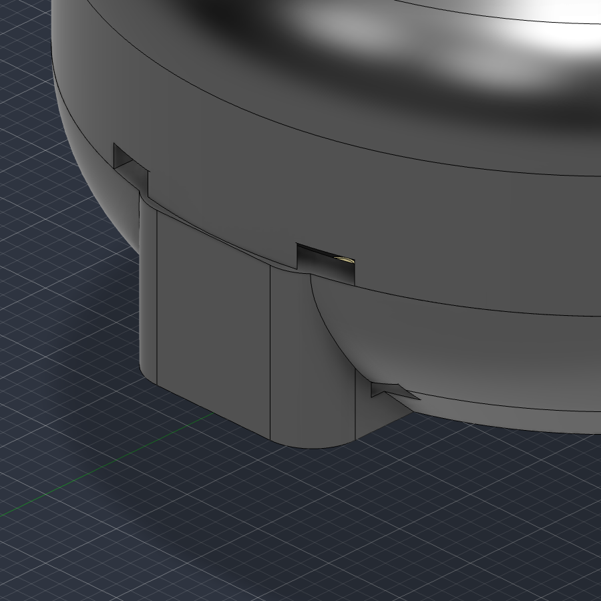
hardware/case/renders/lanyard_end.png
