jakeholland/firefly/hardware/case/renders/pass9_current_front.png

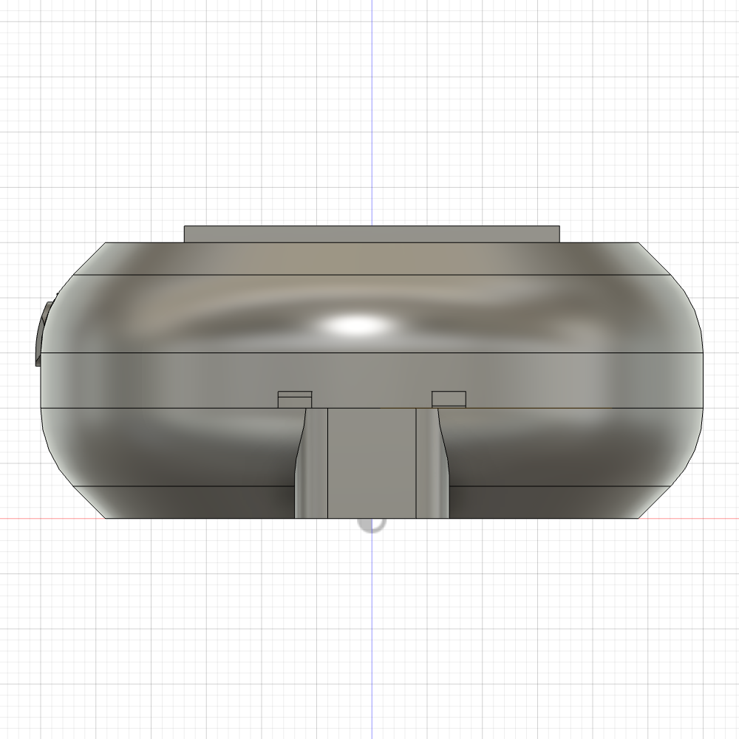
hardware/case/renders/pass9_current_front.png
