jakeholland/firefly/hardware/case/renders/pass9_current_iso.png

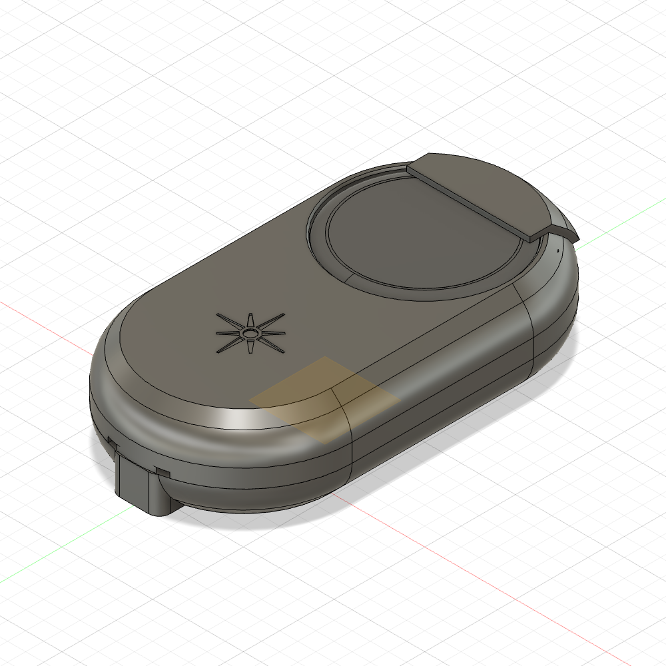
hardware/case/renders/pass9_current_iso.png
