jakeholland/firefly/hardware/case/renders/pass9_current_right.png

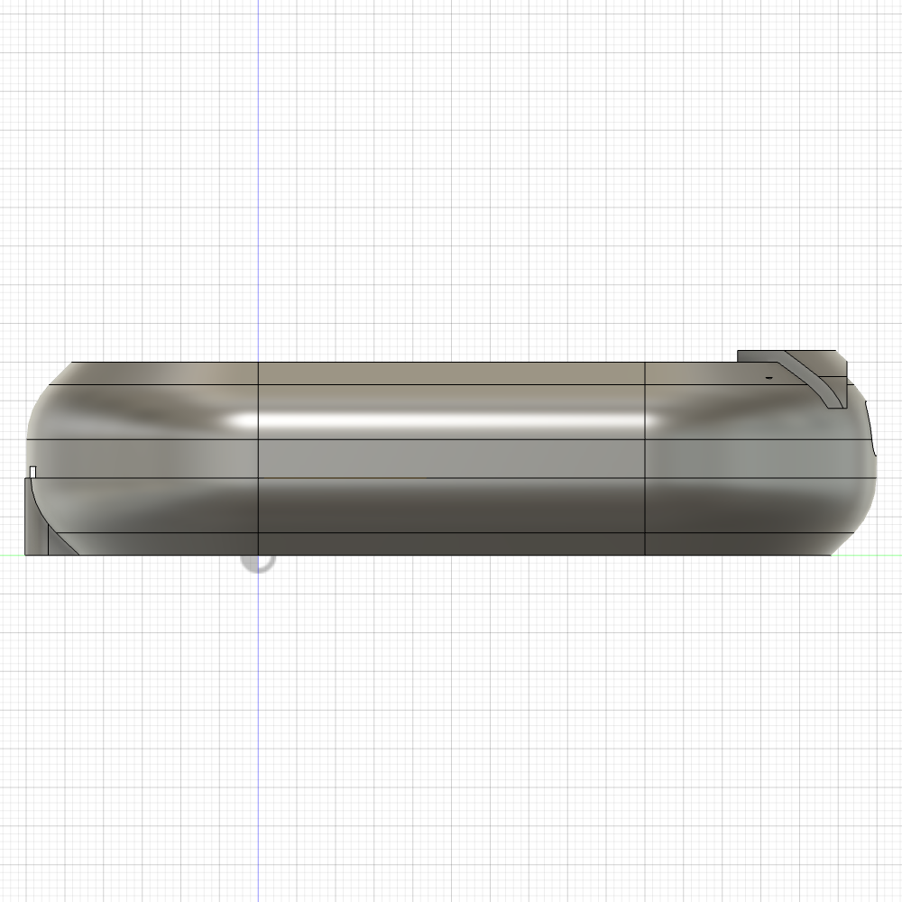
hardware/case/renders/pass9_current_right.png
