jakeholland/firefly/hardware/case/renders/pass9_current_top.png

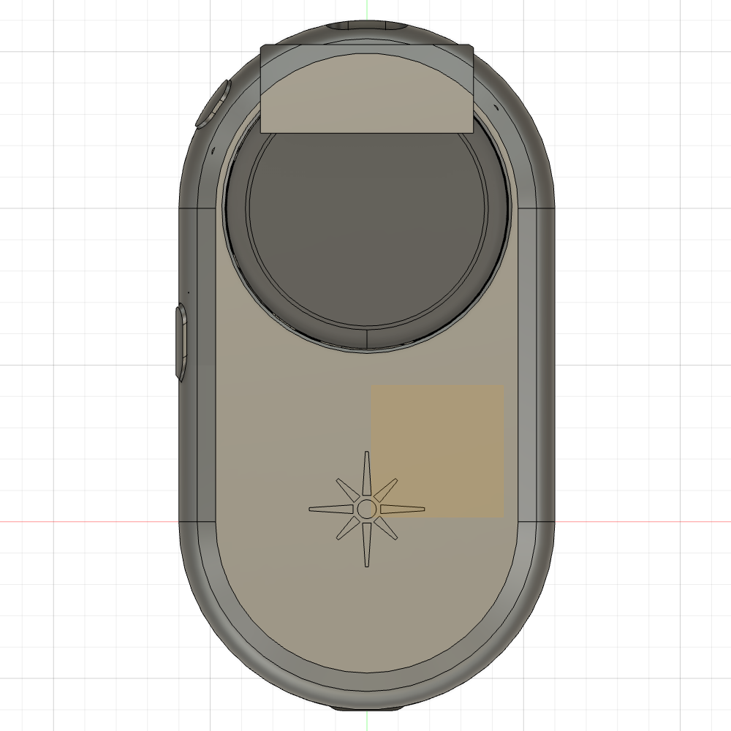
hardware/case/renders/pass9_current_top.png
