jakeholland/firefly/hardware/case/renders/pass9_trim_front.png

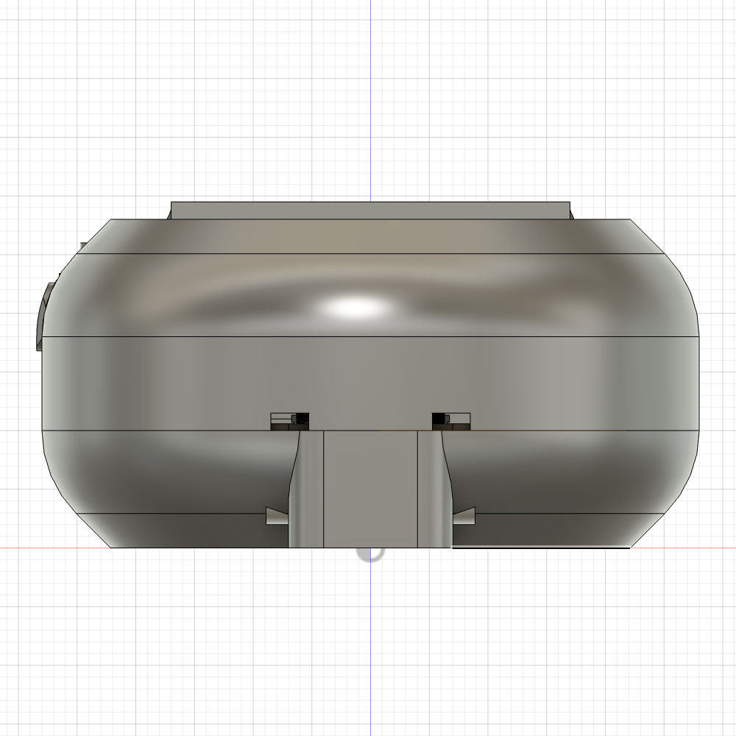
hardware/case/renders/pass9_trim_front.png
