jakeholland/firefly/hardware/case/renders/pass9_trim_iso.png

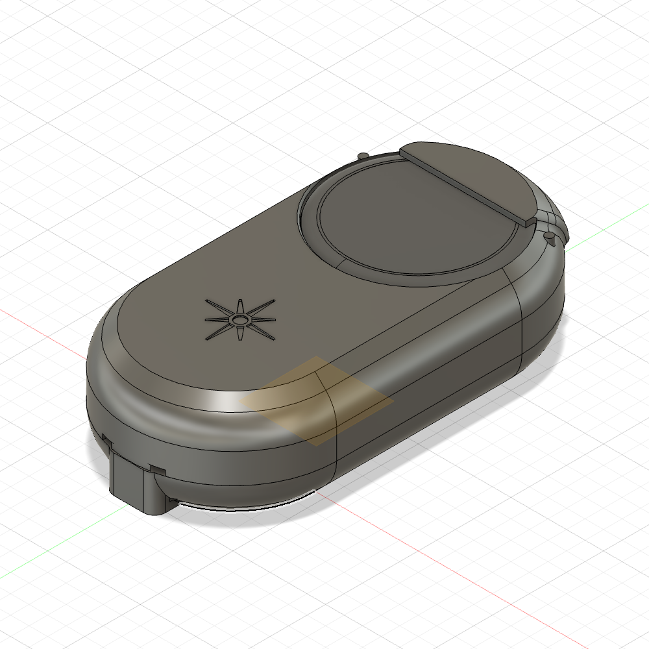
hardware/case/renders/pass9_trim_iso.png
