jakeholland/firefly/hardware/case/renders/pass9_trim_right.png

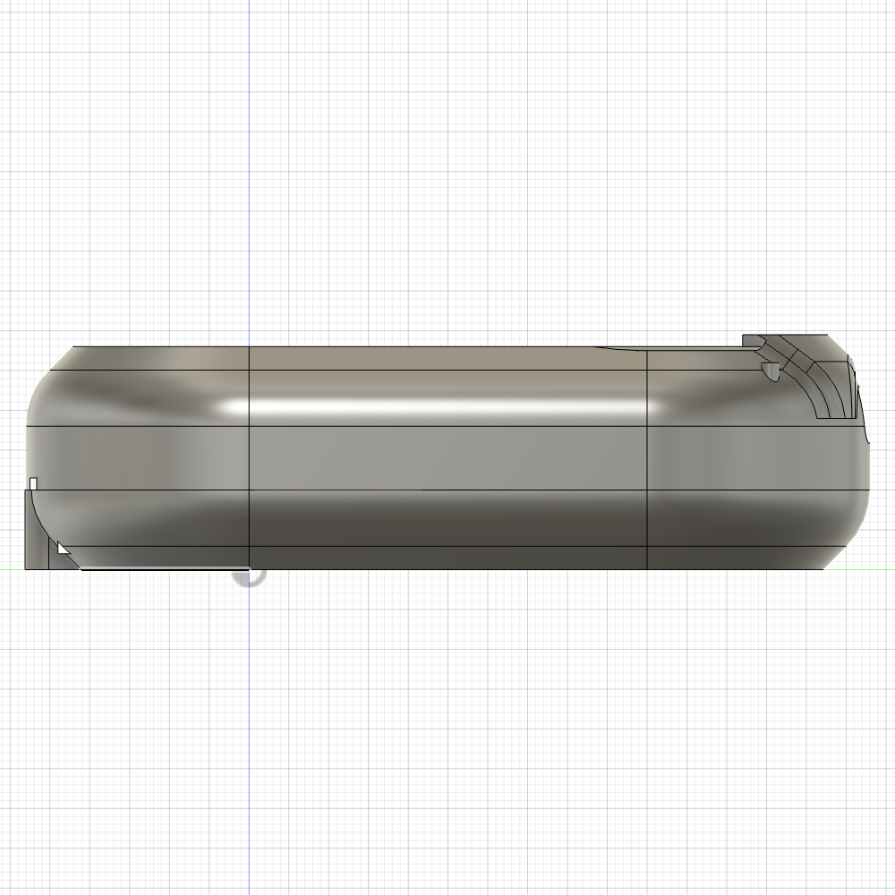
hardware/case/renders/pass9_trim_right.png
