jakeholland/firefly/hardware/case/renders/pass9_trim_top.png

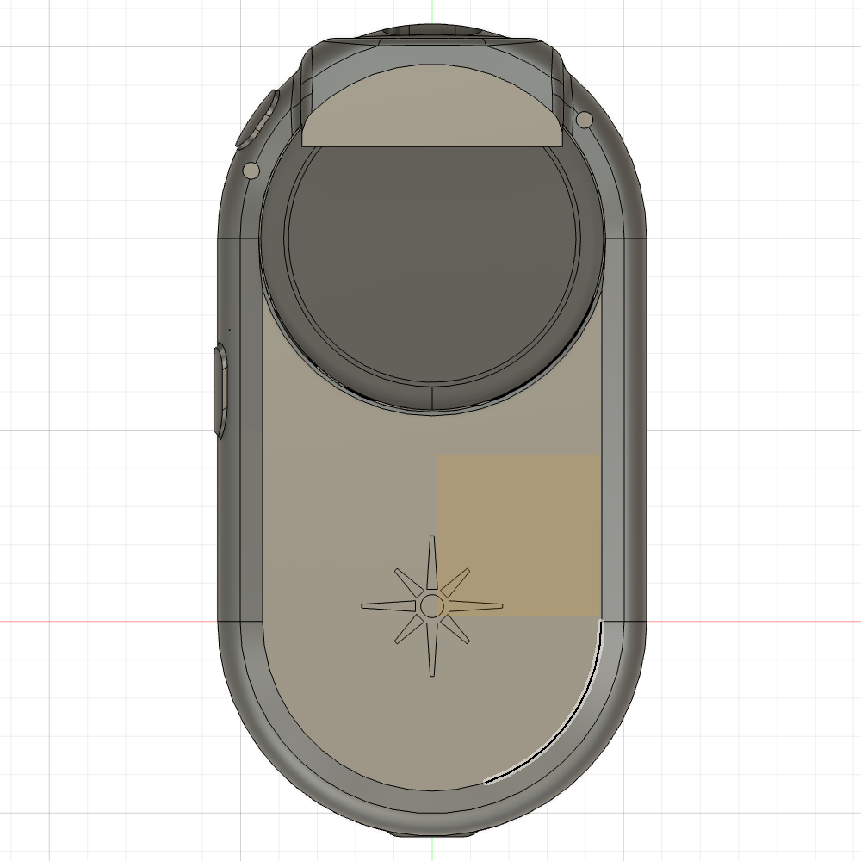
hardware/case/renders/pass9_trim_top.png
