jakeholland/firefly/hardware/case/renders/pass9c_current_front.png

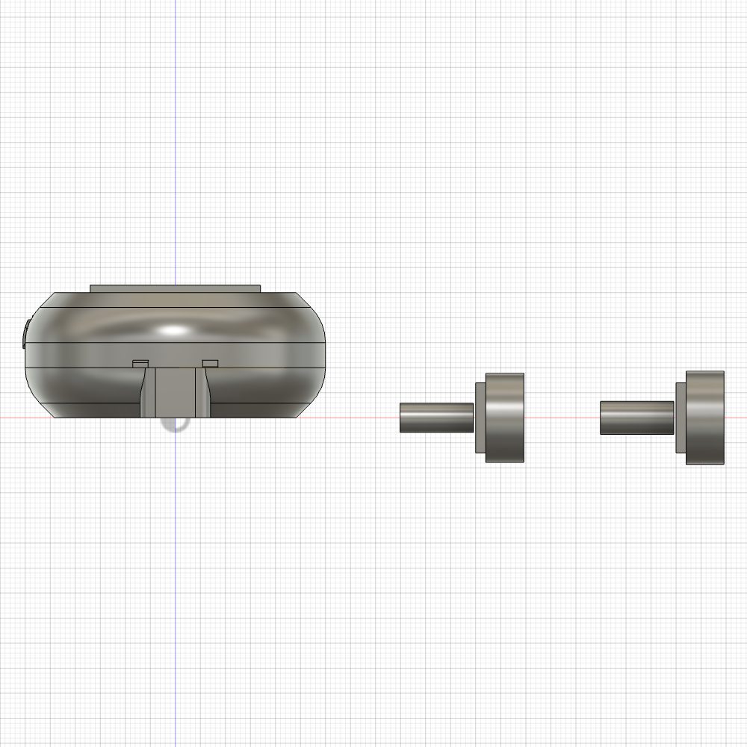
hardware/case/renders/pass9c_current_front.png
