jakeholland/firefly/hardware/case/renders/pass9c_current_iso.png

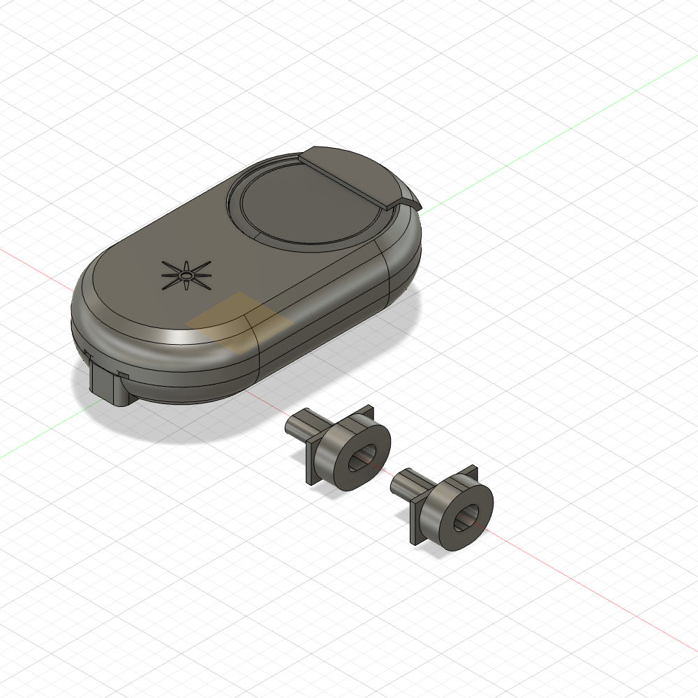
hardware/case/renders/pass9c_current_iso.png
