jakeholland/firefly/hardware/case/renders/pass9c_current_right.png

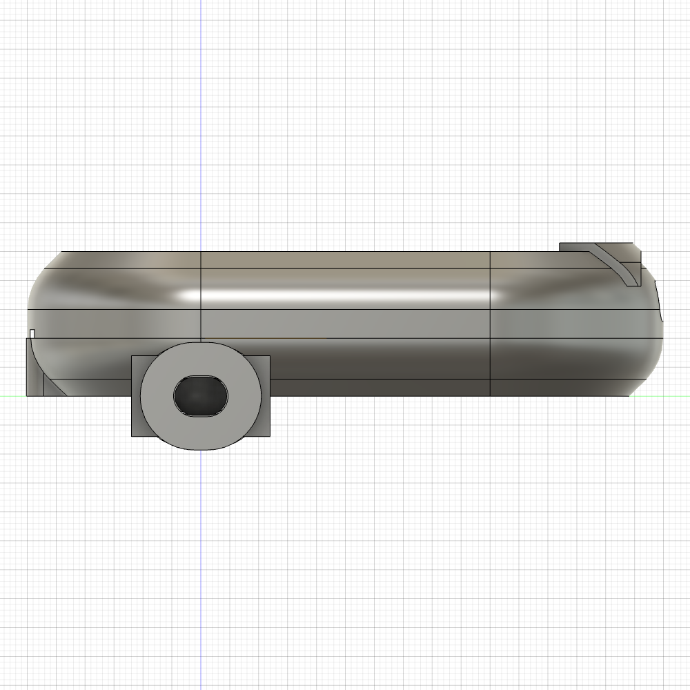
hardware/case/renders/pass9c_current_right.png
