jakeholland/firefly/hardware/case/renders/pass9c_current_top.png

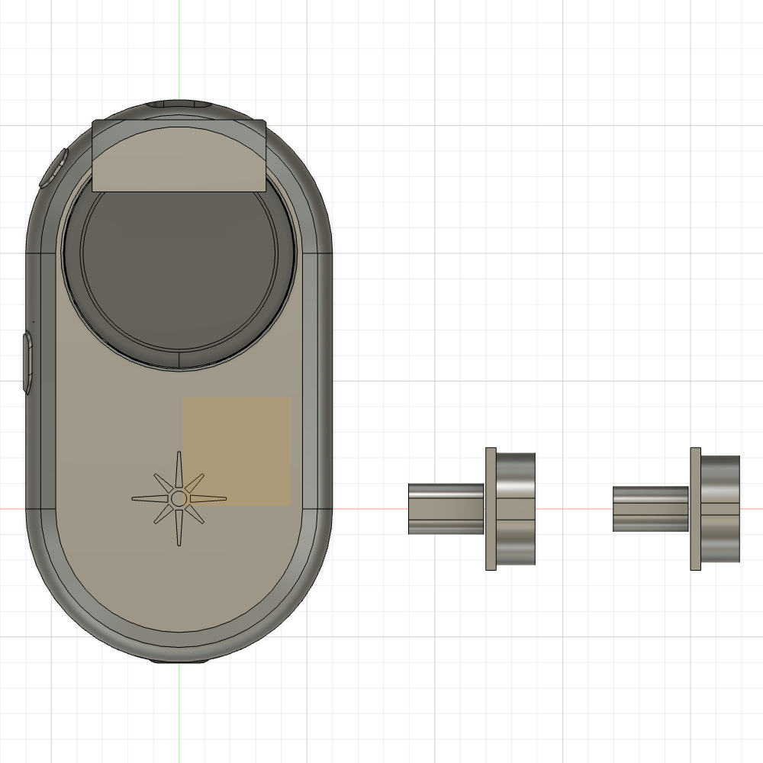
hardware/case/renders/pass9c_current_top.png
