jakeholland/firefly/hardware/case/renders/pass9c_lip_chamfer.png

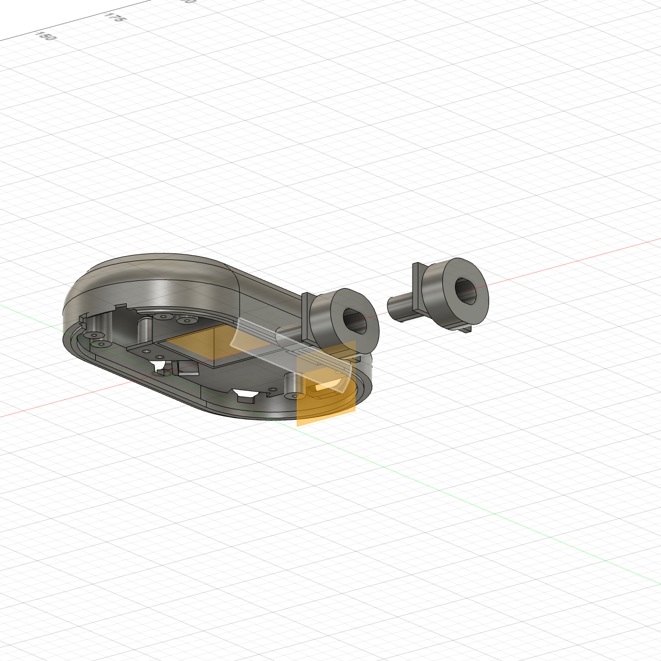
hardware/case/renders/pass9c_lip_chamfer.png
