jakeholland/firefly/hardware/case/renders/pass9c_lip_ring_section.png

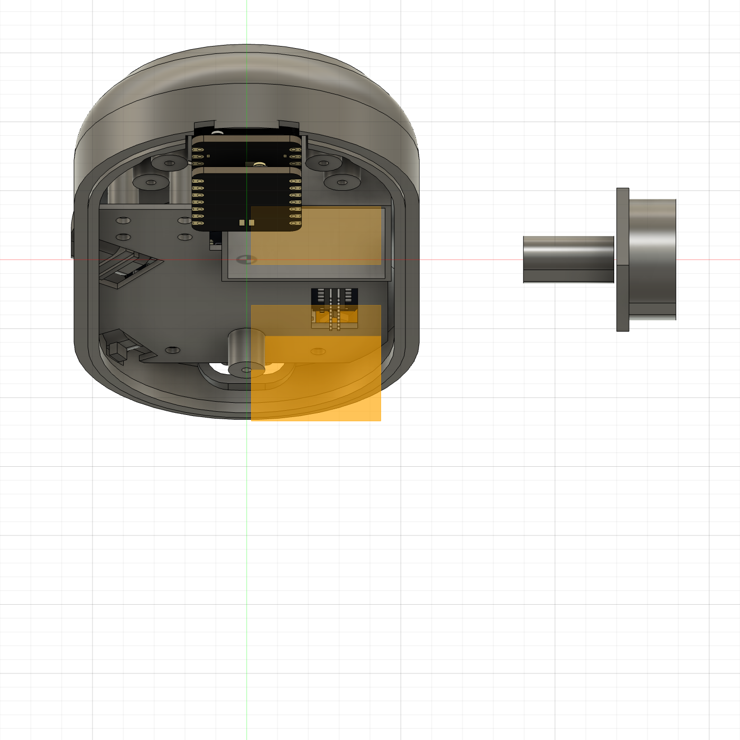
hardware/case/renders/pass9c_lip_ring_section.png
