jakeholland/firefly/hardware/case/renders/pass9c_plate_underside.png

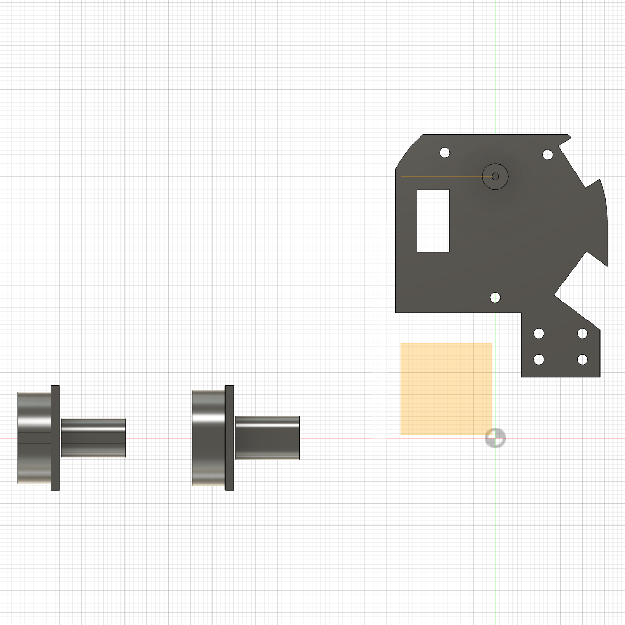
hardware/case/renders/pass9c_plate_underside.png
