jakeholland/firefly/hardware/case/renders/pass9c_posts_closeup.png

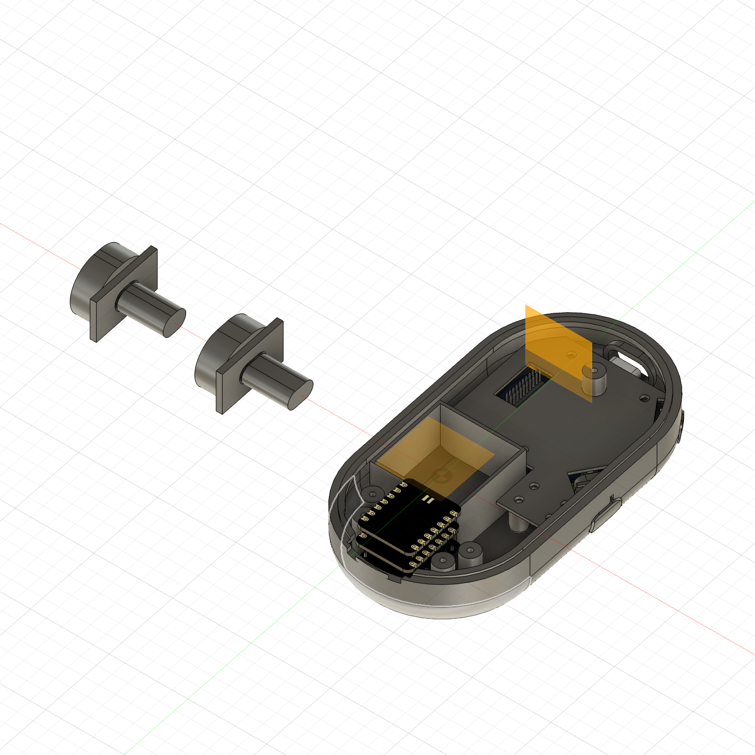
hardware/case/renders/pass9c_posts_closeup.png
