jakeholland/firefly/hardware/case/renders/pass9c_trim_front.png

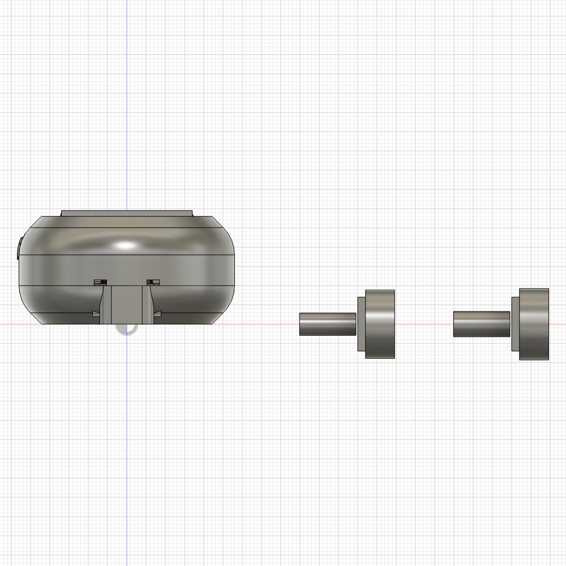
hardware/case/renders/pass9c_trim_front.png
