jakeholland/firefly/hardware/case/renders/pass9c_trim_iso.png

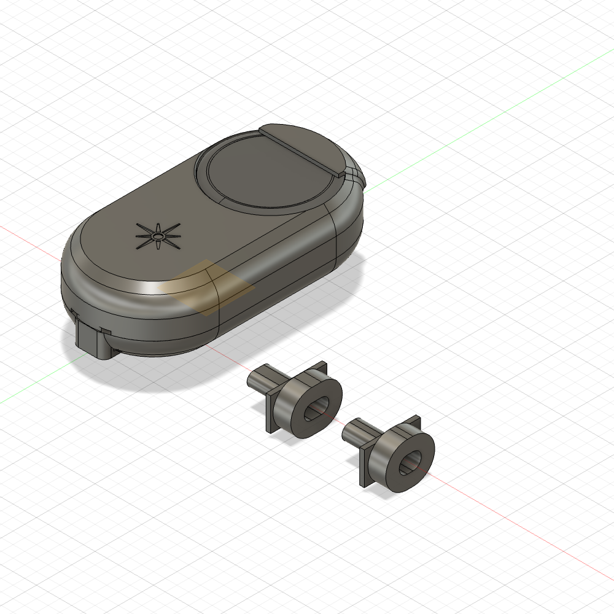
hardware/case/renders/pass9c_trim_iso.png
