jakeholland/firefly/hardware/case/renders/pass9c_trim_right.png

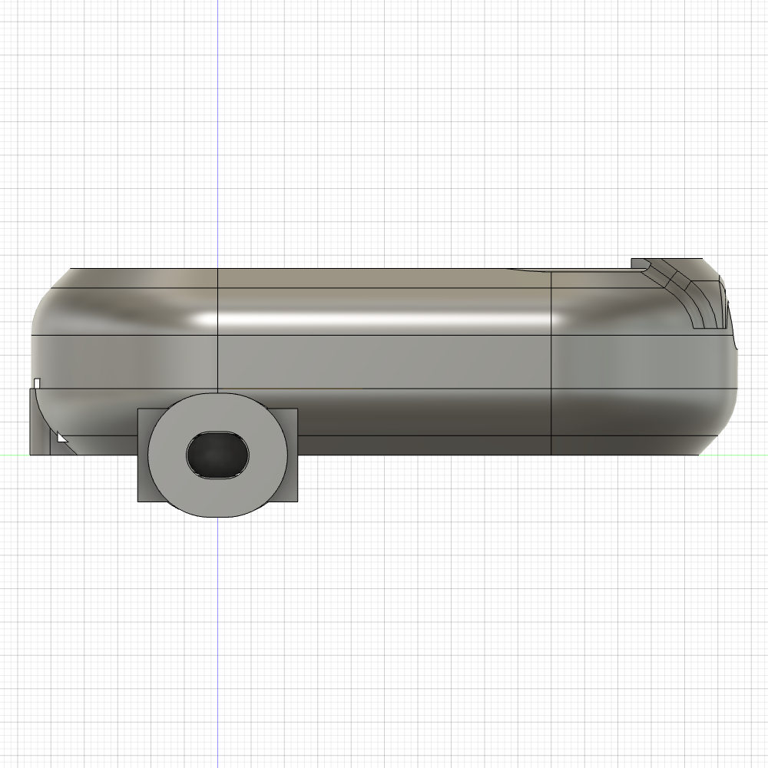
hardware/case/renders/pass9c_trim_right.png
