jakeholland/firefly/hardware/case/renders/pass9c_trim_top.png

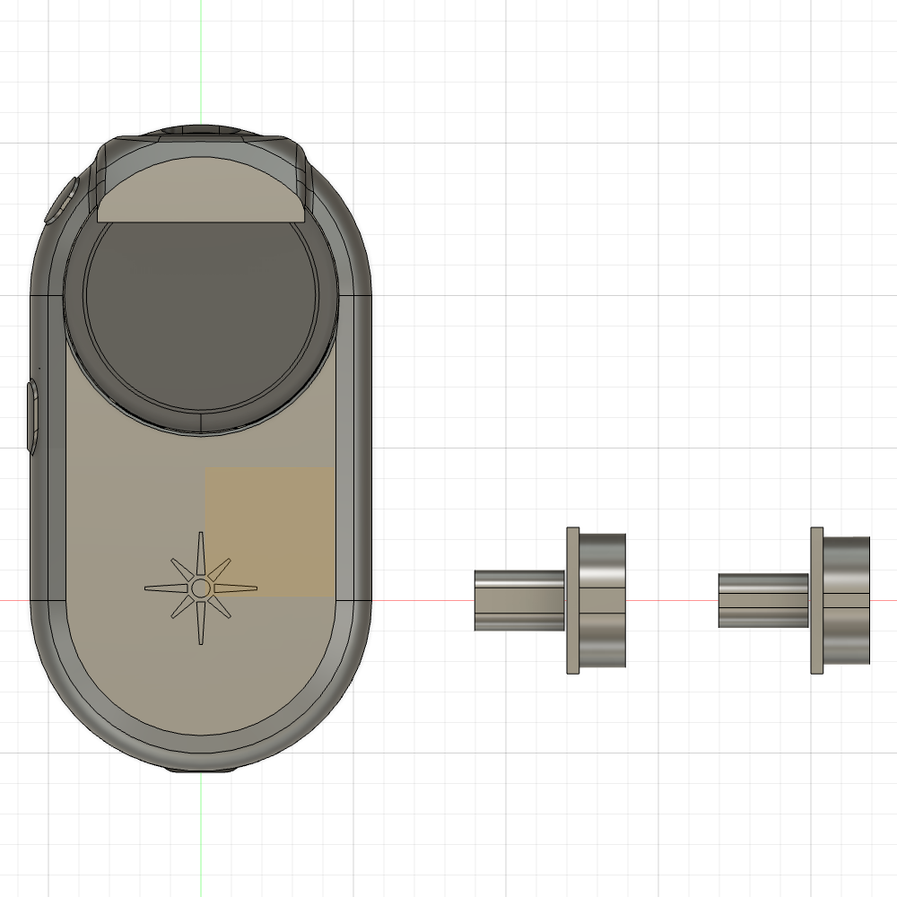
hardware/case/renders/pass9c_trim_top.png
