jakeholland/firefly/hardware/case/renders/pass9d_current_front.png

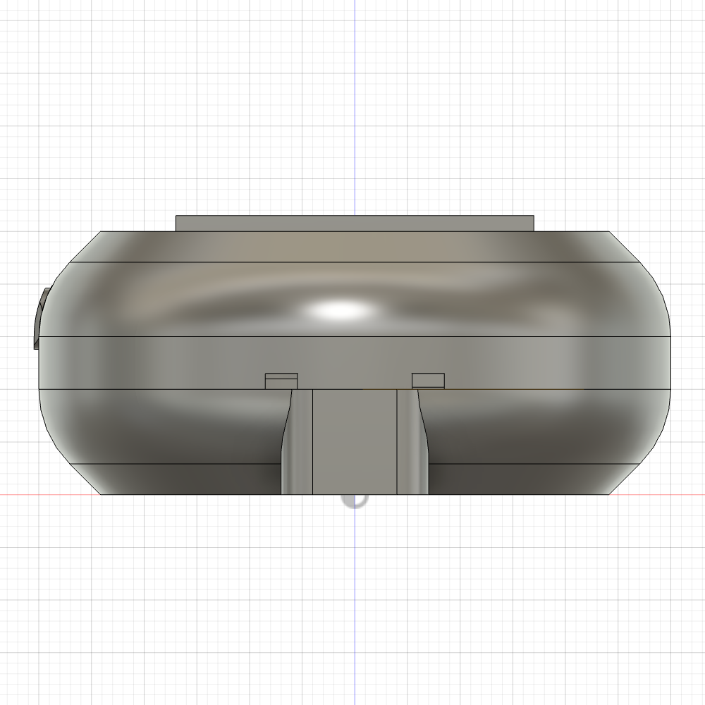
hardware/case/renders/pass9d_current_front.png
