jakeholland/firefly/hardware/case/renders/pass9d_trim_front.png

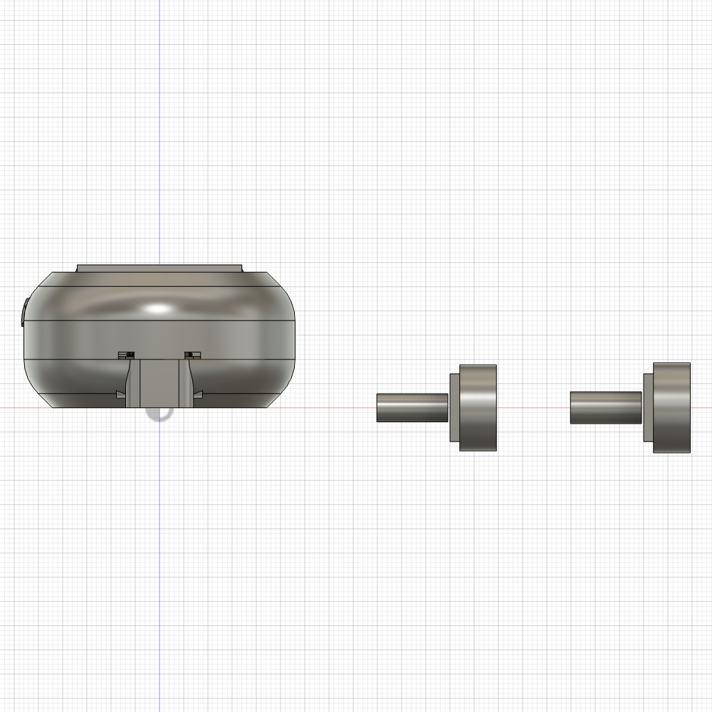
hardware/case/renders/pass9d_trim_front.png
