jakeholland/firefly/hardware/case/renders/pass9d_trim_mechanism_section.png

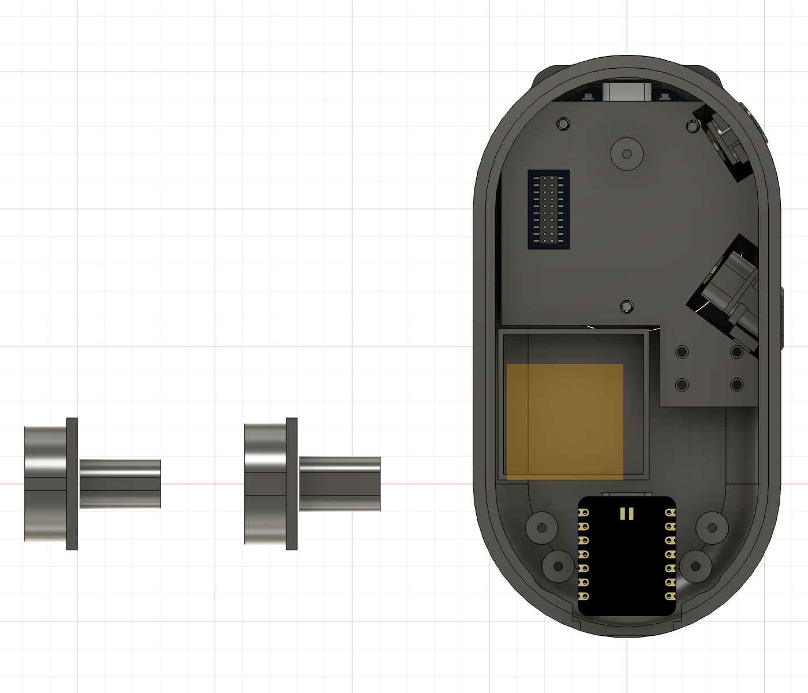
hardware/case/renders/pass9d_trim_mechanism_section.png
