jakeholland/firefly/hardware/case/renders/pass9d_trim_right.png

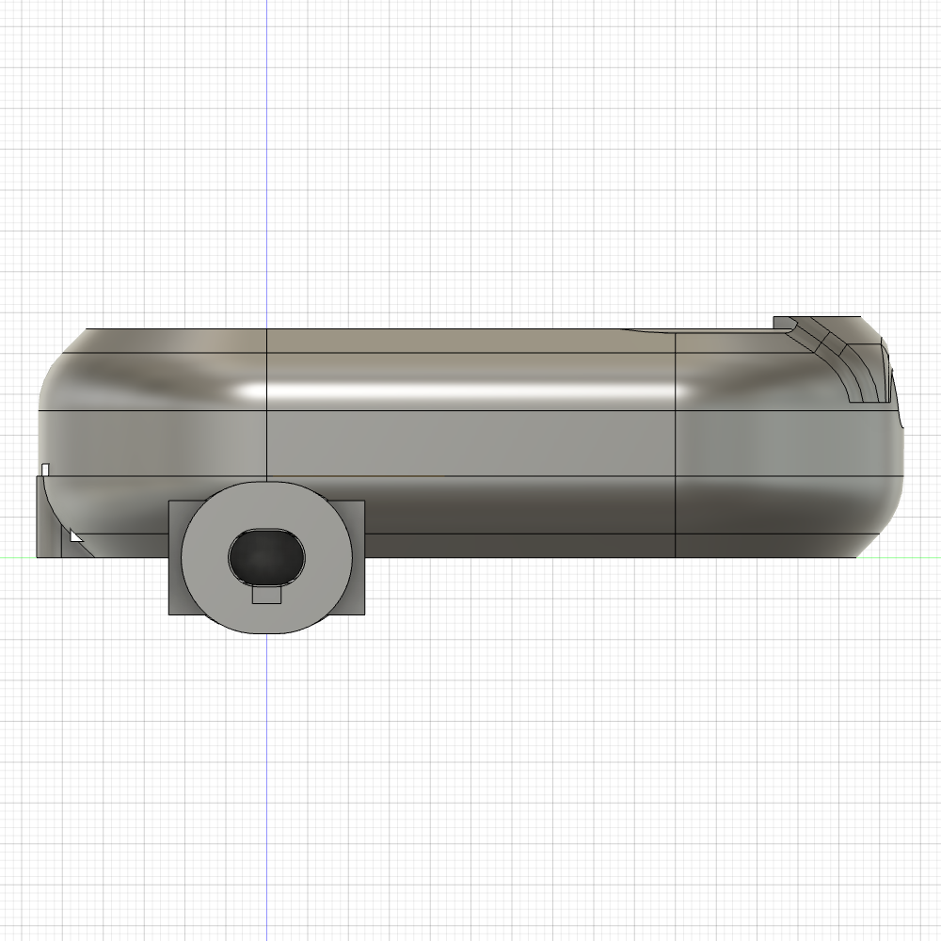
hardware/case/renders/pass9d_trim_right.png
