jakeholland/firefly/hardware/case/renders/pass9e_trim_antenna_routes.png

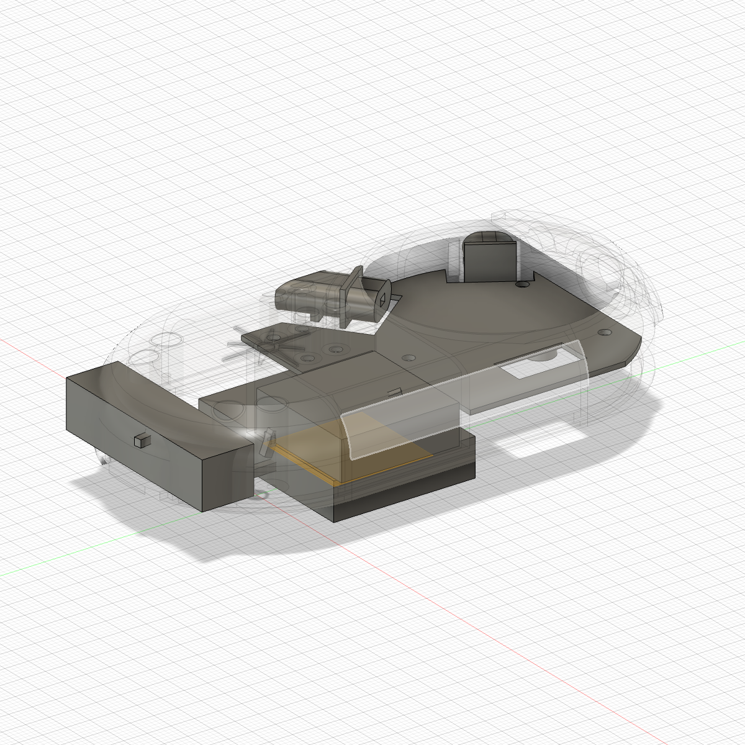
hardware/case/renders/pass9e_trim_antenna_routes.png
