jakeholland/firefly/hardware/case/renders/pass9e_trim_iso.png

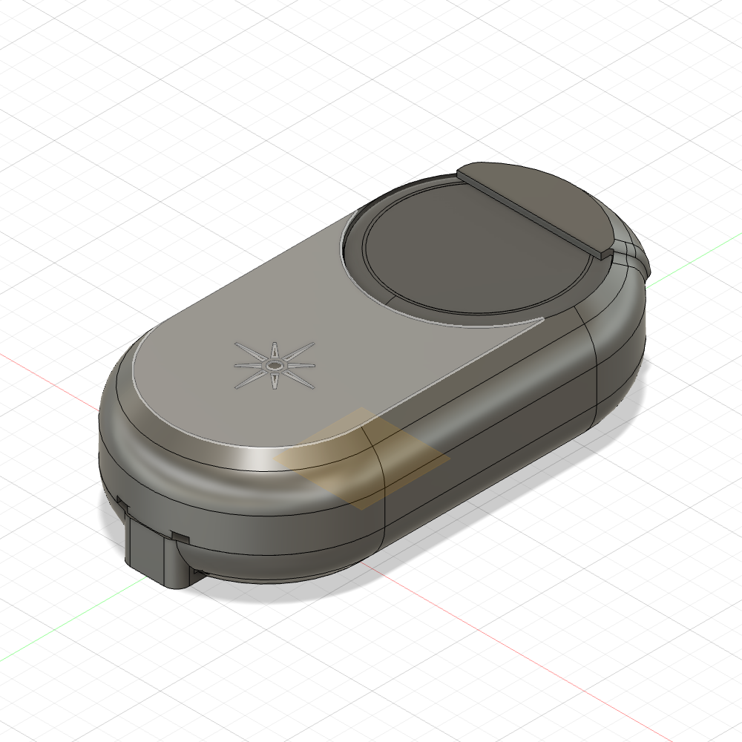
hardware/case/renders/pass9e_trim_iso.png
