jakeholland/firefly/hardware/case/renders/pass9g_current_brow_right.png

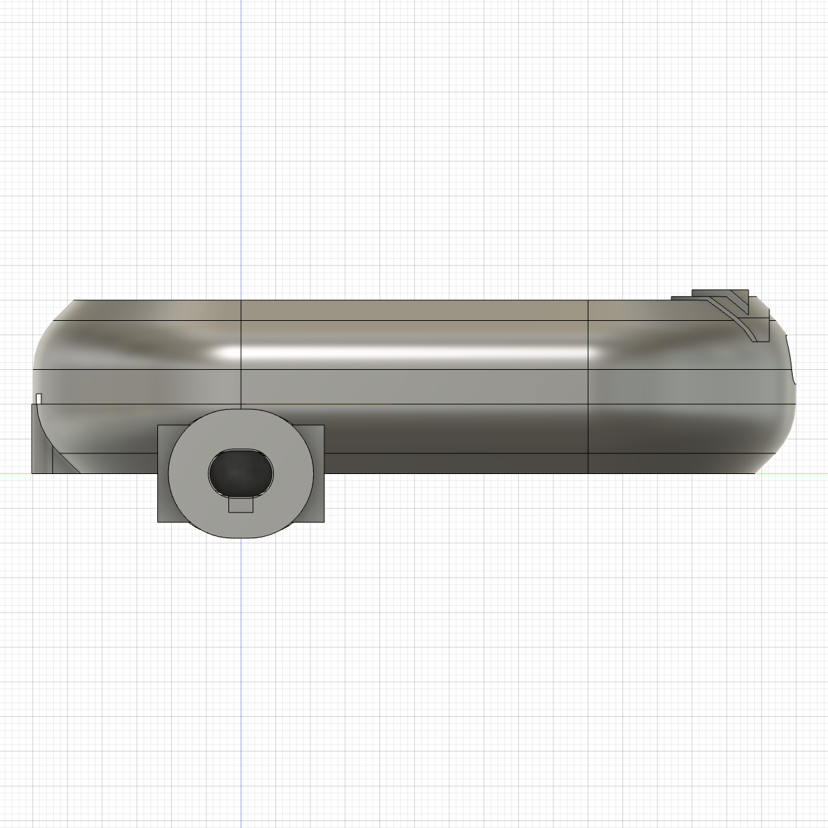
hardware/case/renders/pass9g_current_brow_right.png
