jakeholland/firefly/hardware/case/renders/pass9g_current_inside_bottom.png

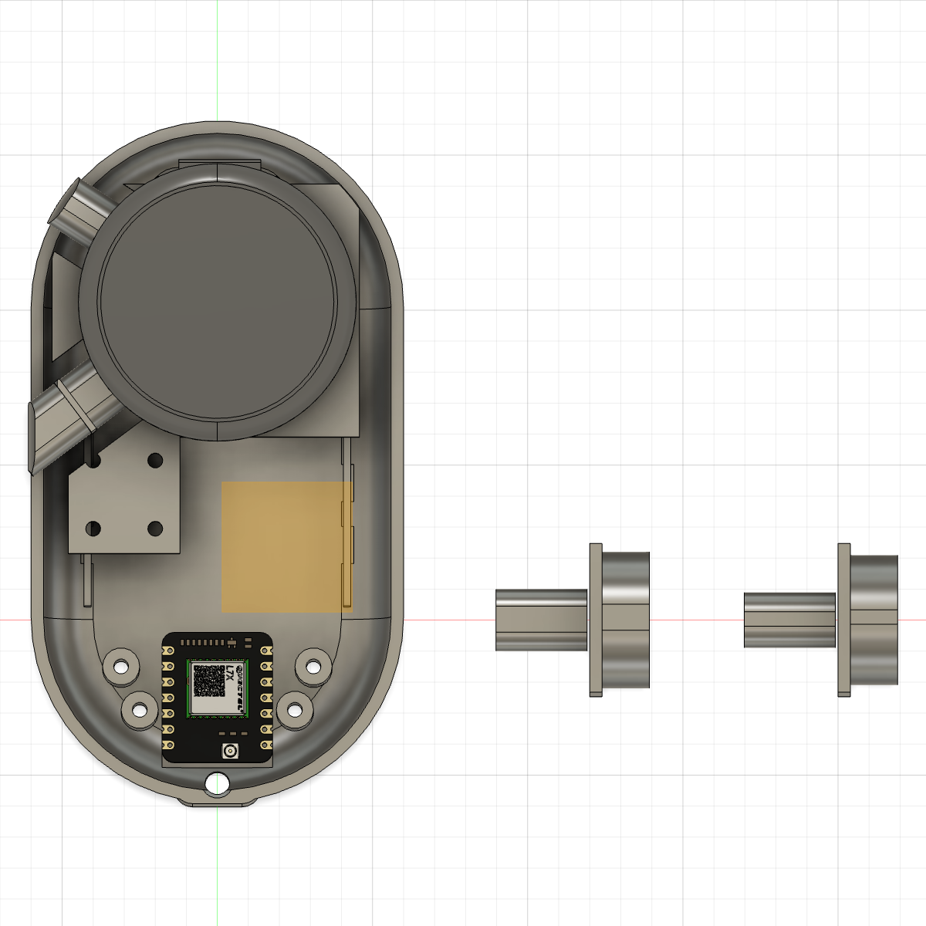
hardware/case/renders/pass9g_current_inside_bottom.png
