jakeholland/firefly/hardware/case/renders/pass9g_current_posts_plate.png

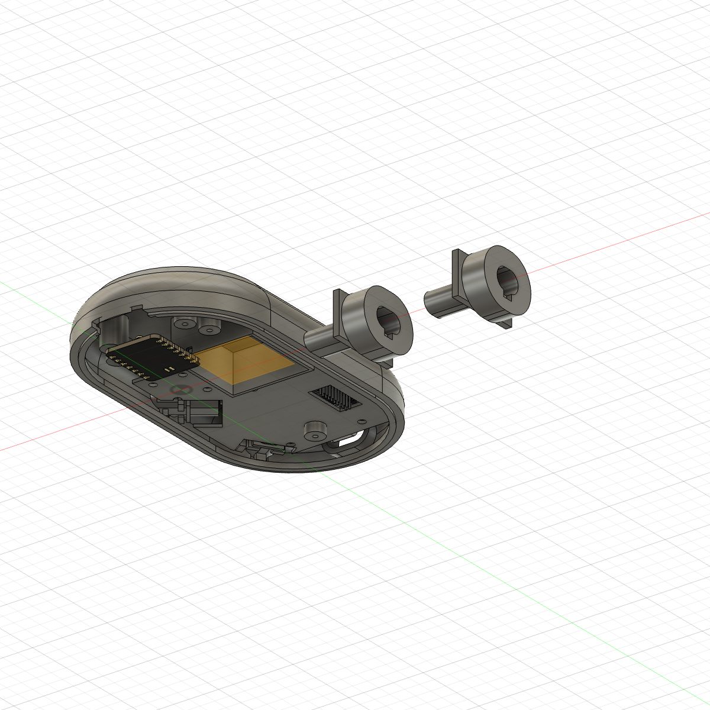
hardware/case/renders/pass9g_current_posts_plate.png
