jakeholland/firefly/hardware/case/renders/pass9g_current_usb_end.png

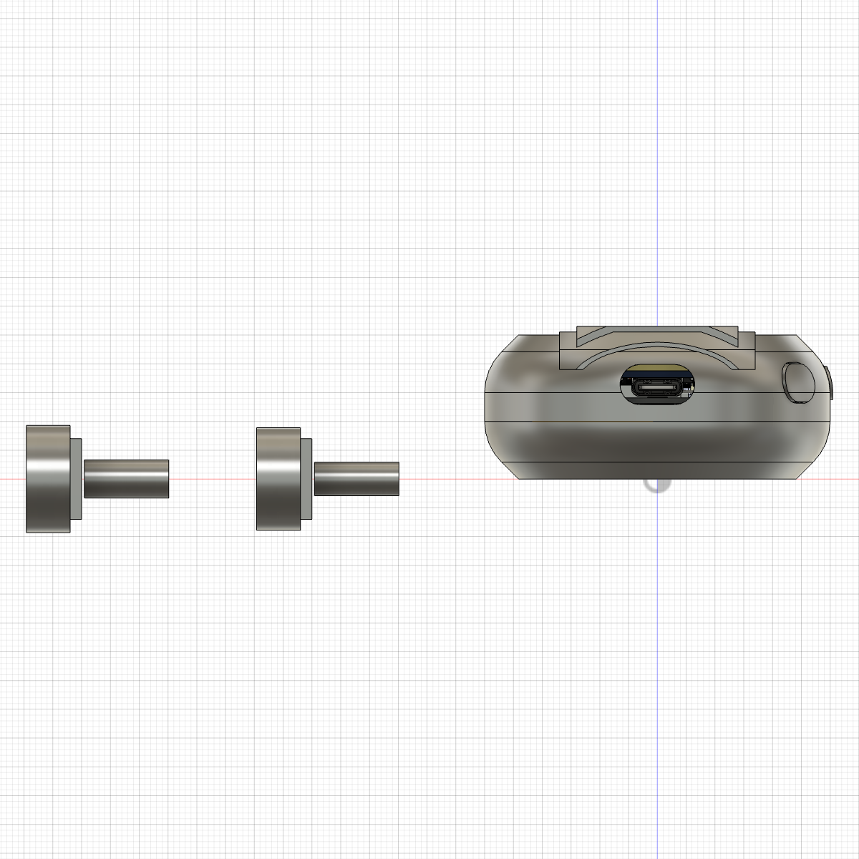
hardware/case/renders/pass9g_current_usb_end.png
