jakeholland/firefly/hardware/case/renders/pass9g_trim_brow_right.png

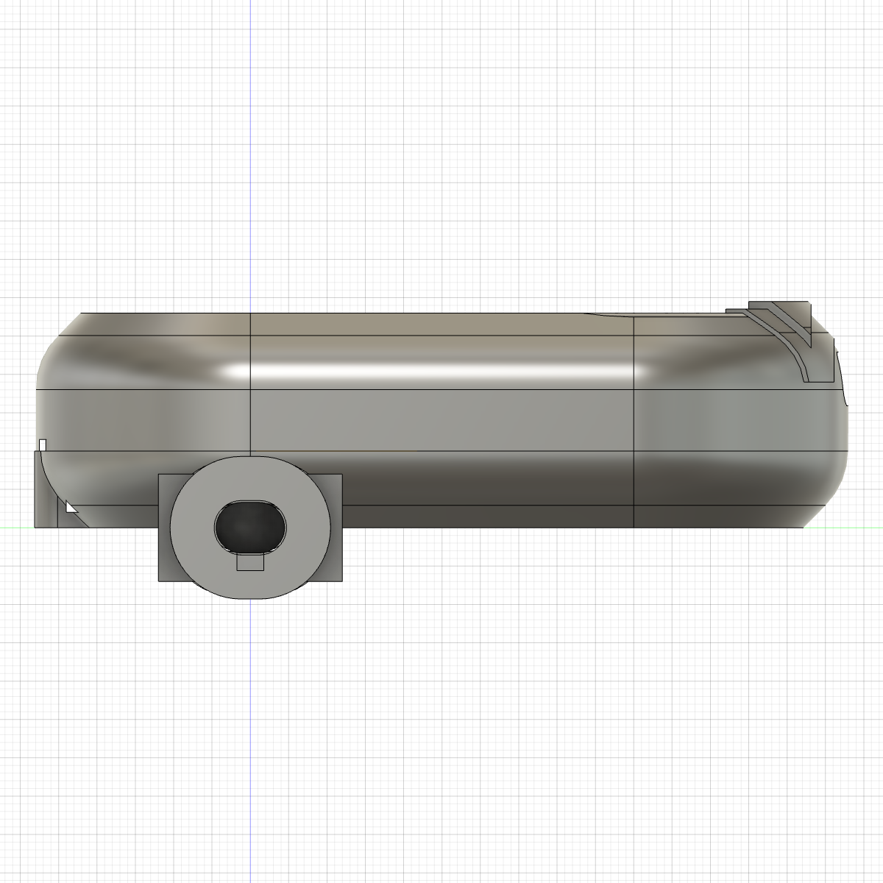
hardware/case/renders/pass9g_trim_brow_right.png
