jakeholland/firefly/hardware/case/renders/pass9g_trim_inside_bottom.png

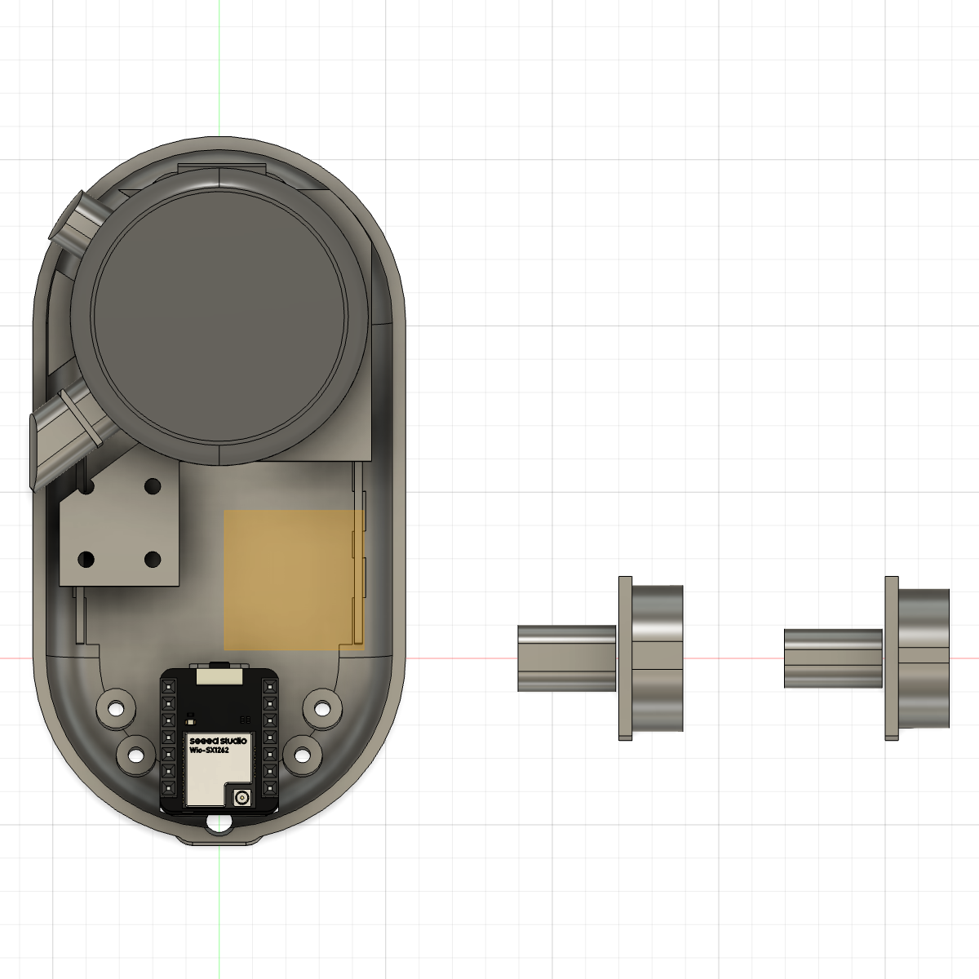
hardware/case/renders/pass9g_trim_inside_bottom.png
