jakeholland/firefly/hardware/case/renders/pass9g_trim_lanyard_end.png

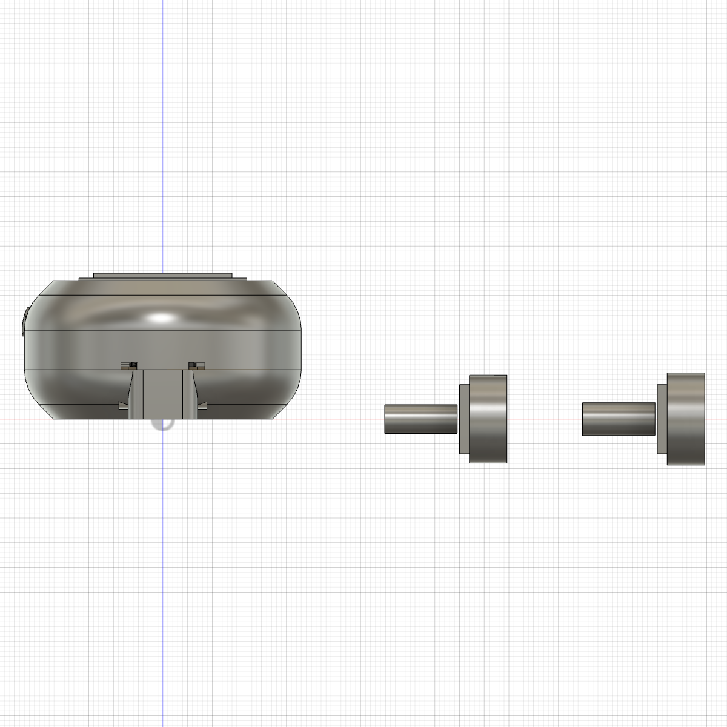
hardware/case/renders/pass9g_trim_lanyard_end.png
