jakeholland/firefly/hardware/case/renders/pass9g_trim_posts_plate.png

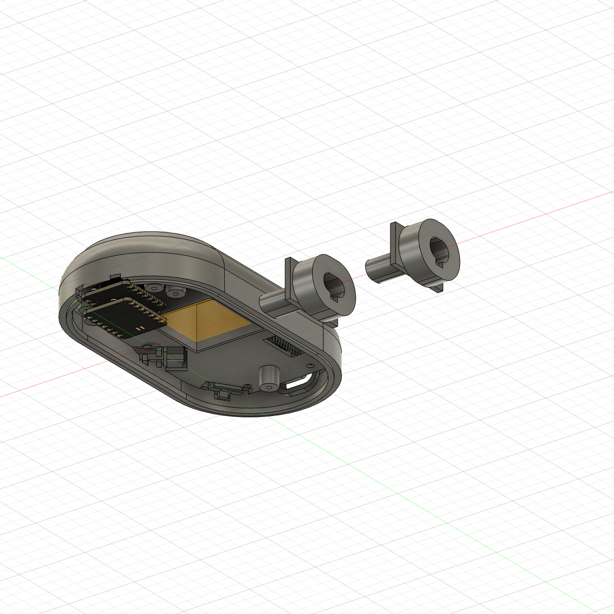
hardware/case/renders/pass9g_trim_posts_plate.png
