jakeholland/firefly/hardware/case/renders/pass9g_trim_usb_end.png

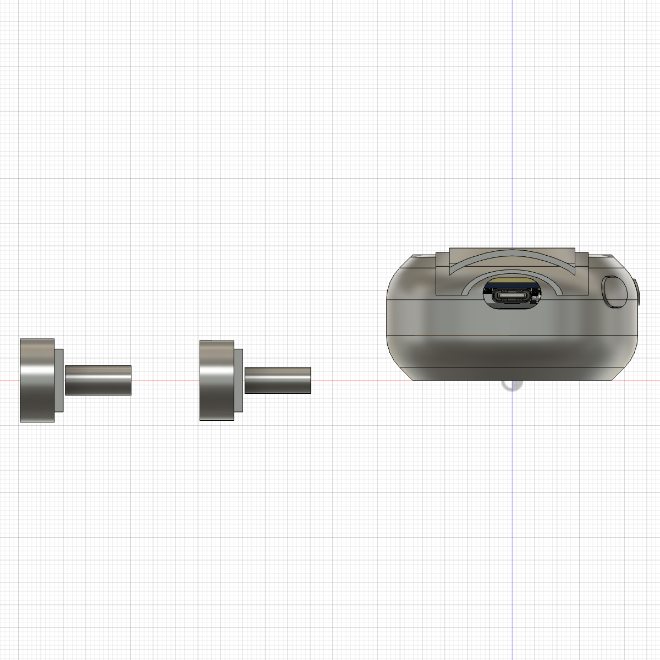
hardware/case/renders/pass9g_trim_usb_end.png
