jakeholland/firefly/hardware/case/renders/pass10_current_front.png

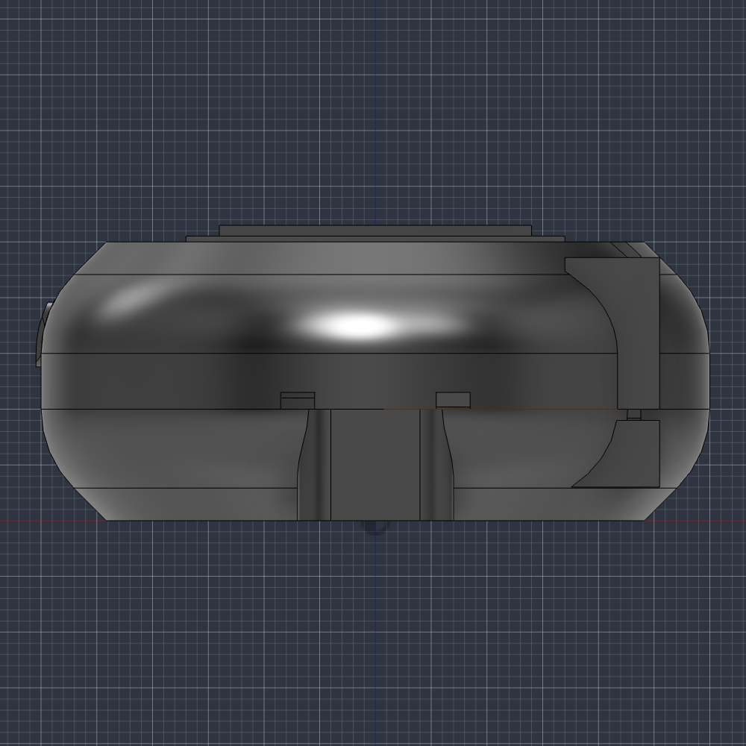
hardware/case/renders/pass10_current_front.png
