jakeholland/firefly/hardware/case/renders/pass10_current_iso.png

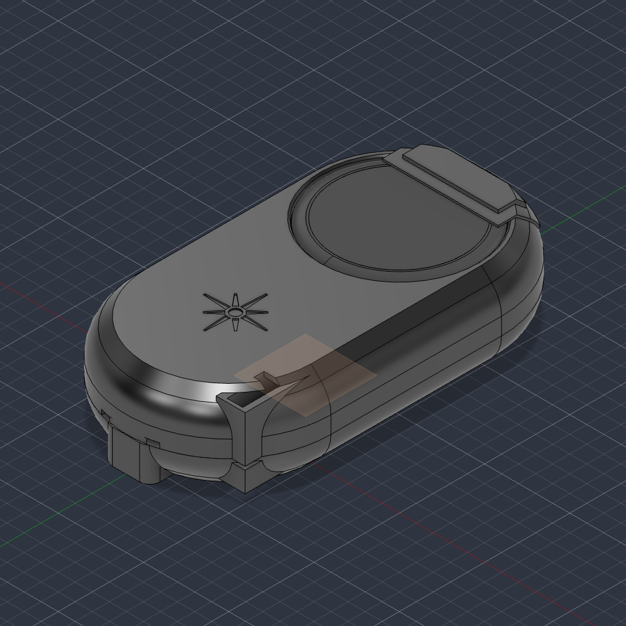
hardware/case/renders/pass10_current_iso.png
