jakeholland/firefly/hardware/case/renders/pass10_current_right.png

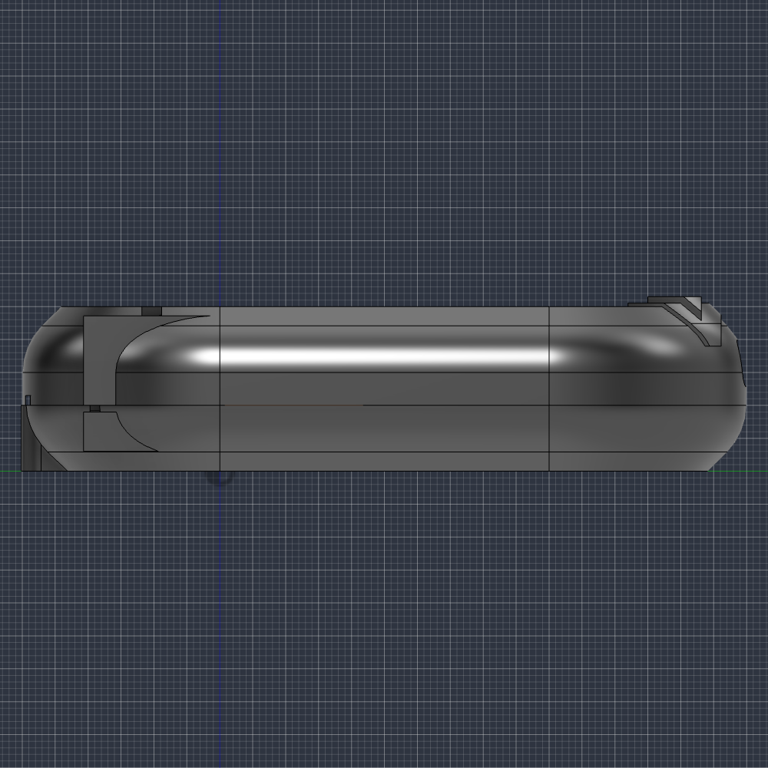
hardware/case/renders/pass10_current_right.png
