jakeholland/firefly/hardware/case/renders/pass10_current_top.png

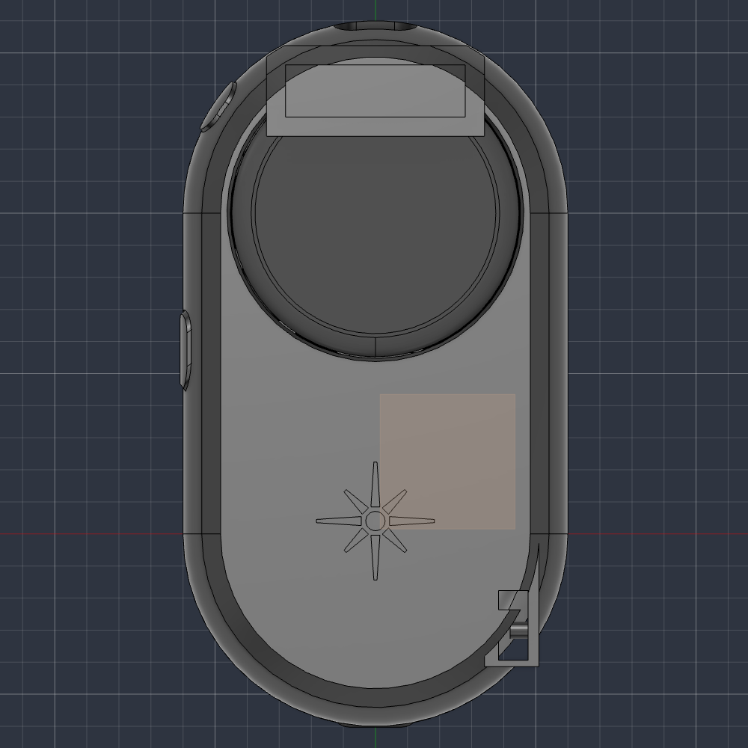
hardware/case/renders/pass10_current_top.png
