jakeholland/firefly/hardware/case/renders/pass10_mag_pocket.png

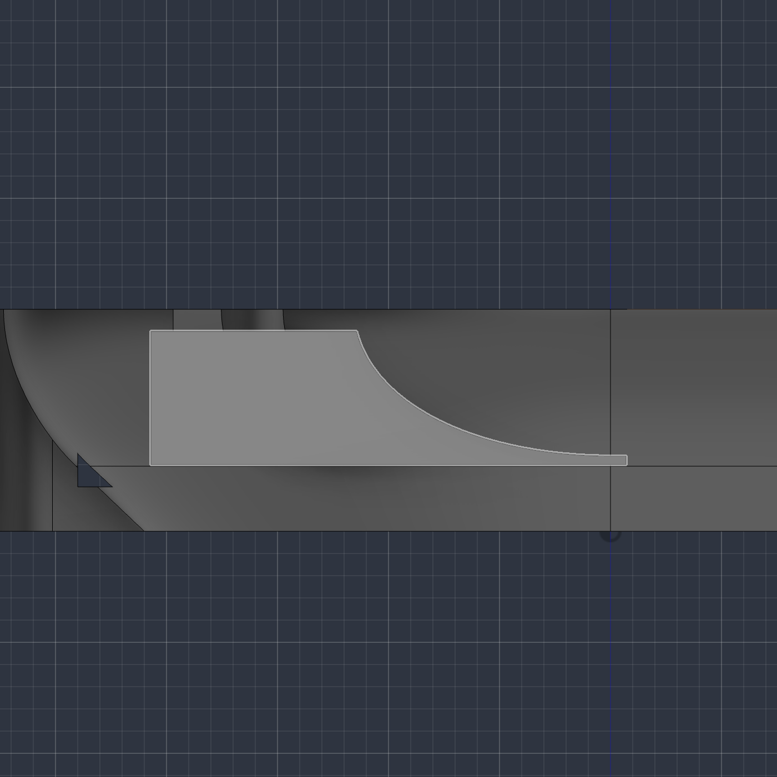
hardware/case/renders/pass10_mag_pocket.png
