jakeholland/firefly/hardware/case/renders/pass10_mag_pocket_open.png

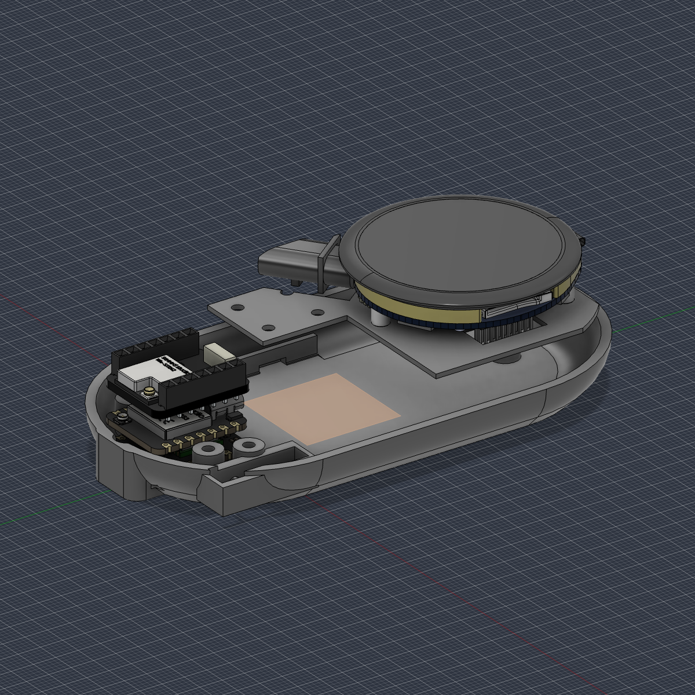
hardware/case/renders/pass10_mag_pocket_open.png
