jakeholland/firefly/hardware/case/renders/pass10_trim_front.png

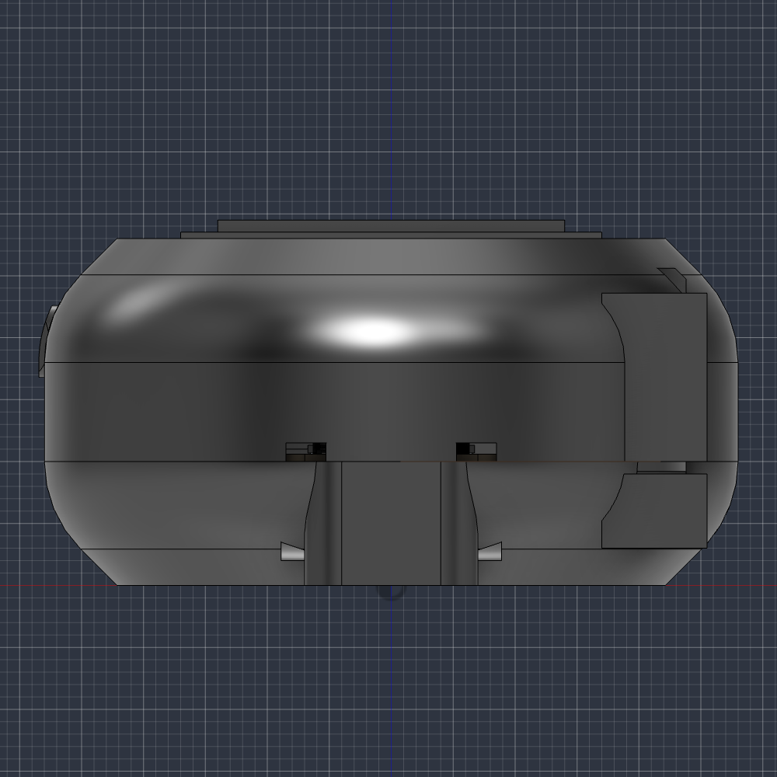
hardware/case/renders/pass10_trim_front.png
