jakeholland/firefly/hardware/case/renders/pass10_trim_iso.png

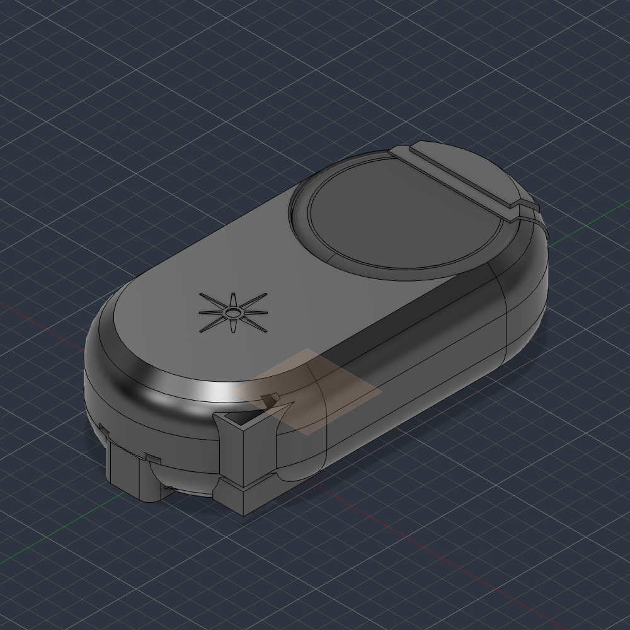
hardware/case/renders/pass10_trim_iso.png
