jakeholland/firefly/hardware/case/renders/pass10_trim_right.png

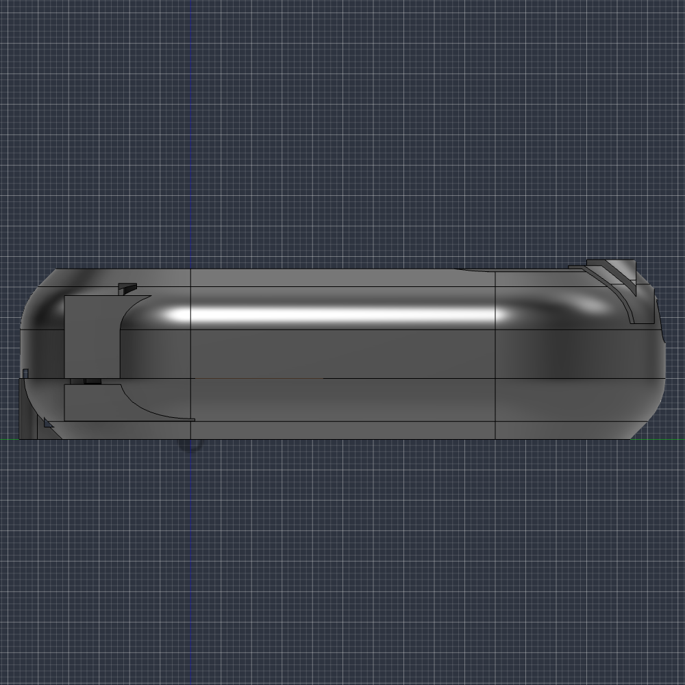
hardware/case/renders/pass10_trim_right.png
