jakeholland/firefly/hardware/case/renders/pass10_trim_top.png

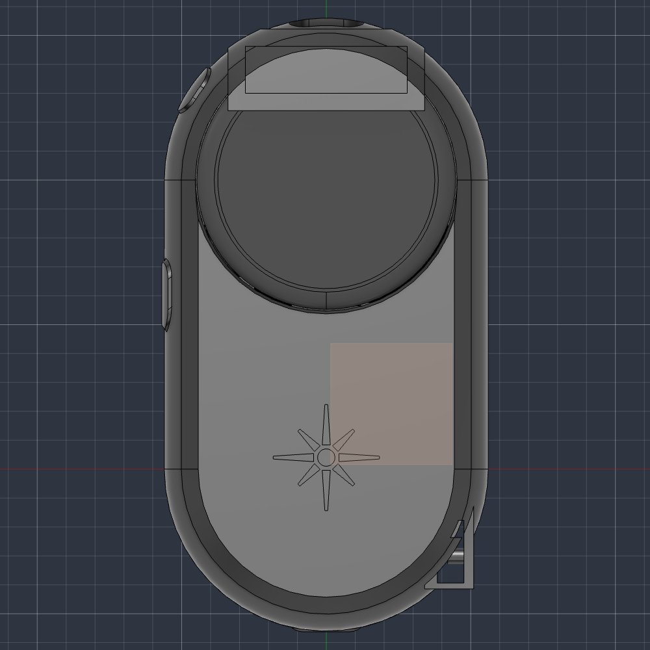
hardware/case/renders/pass10_trim_top.png
