jakeholland/firefly/hardware/case/renders/pass10b_current_right.png

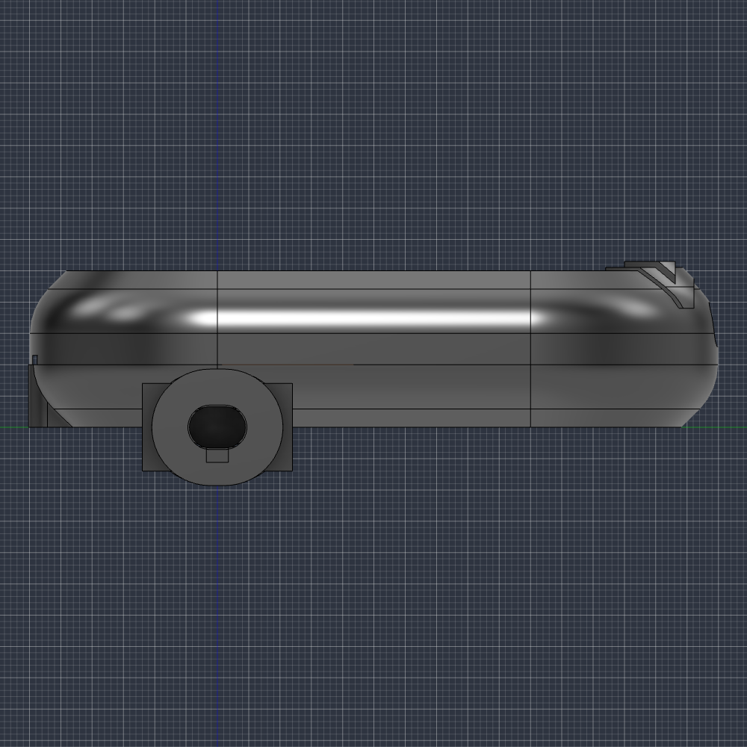
hardware/case/renders/pass10b_current_right.png
