jakeholland/firefly/hardware/case/renders/pass10b_mag_pocket.png

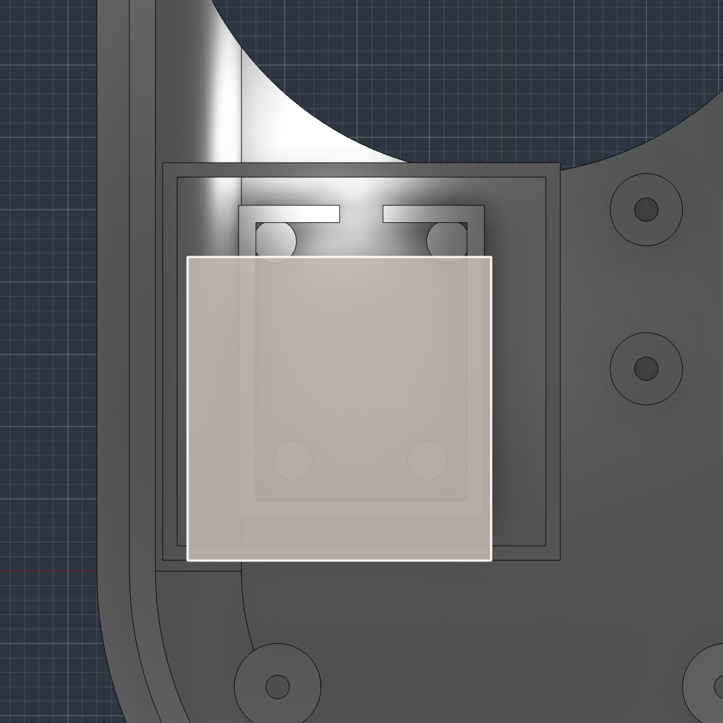
hardware/case/renders/pass10b_mag_pocket.png
