jakeholland/firefly/hardware/case/renders/pass10b_trim_front.png

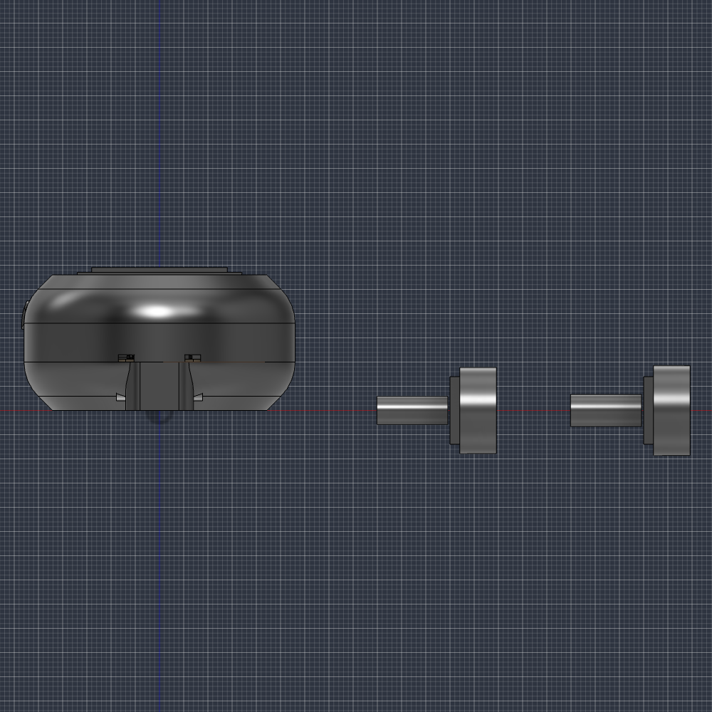
hardware/case/renders/pass10b_trim_front.png
