jakeholland/firefly/hardware/case/renders/pass10b_trim_iso.png

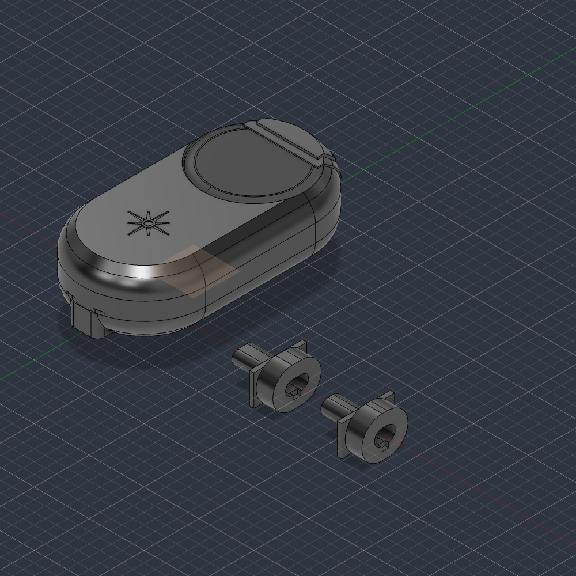
hardware/case/renders/pass10b_trim_iso.png
