jakeholland/firefly/hardware/case/renders/pass11_brow.png

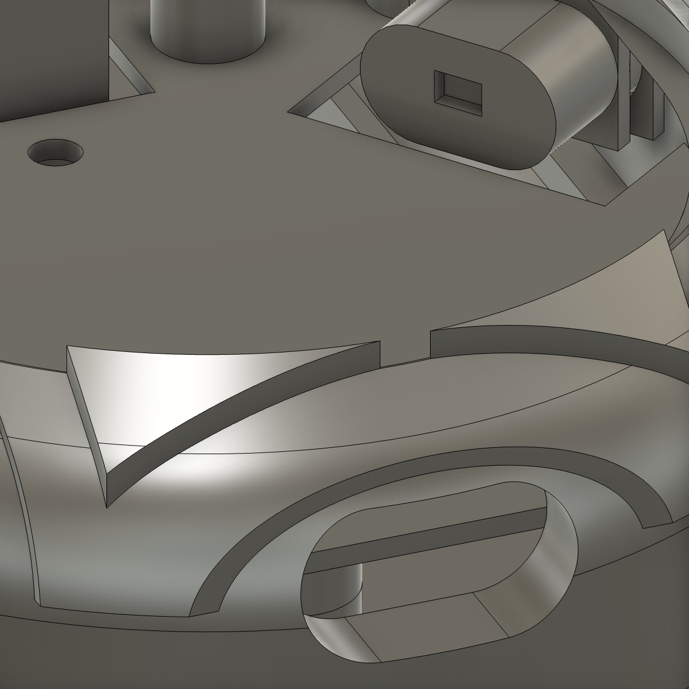
hardware/case/renders/pass11_brow.png
