jakeholland/firefly/hardware/case/renders/pass11_current_front.png

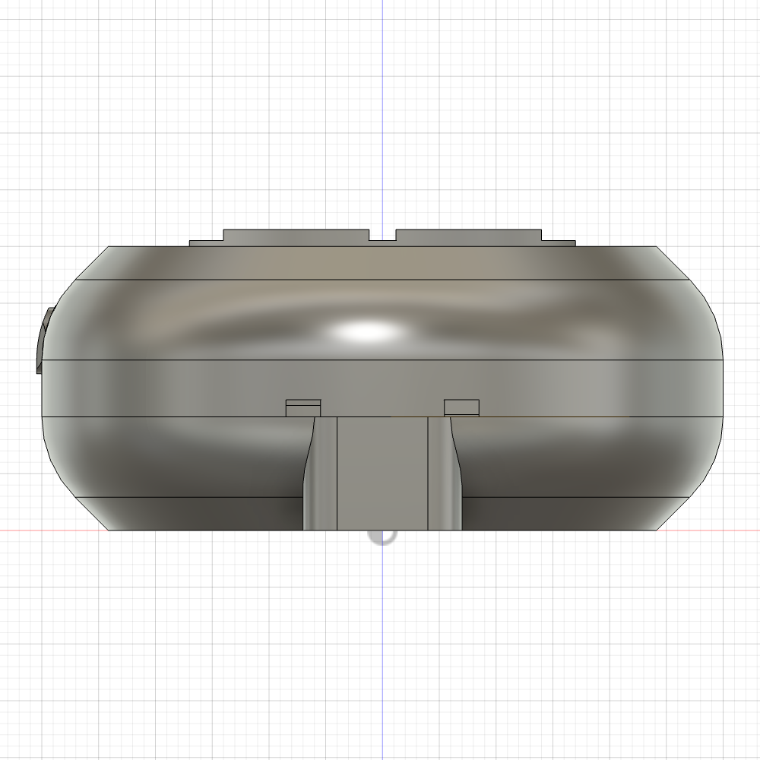
hardware/case/renders/pass11_current_front.png
