jakeholland/firefly/hardware/case/renders/pass11_mag_pocket.png

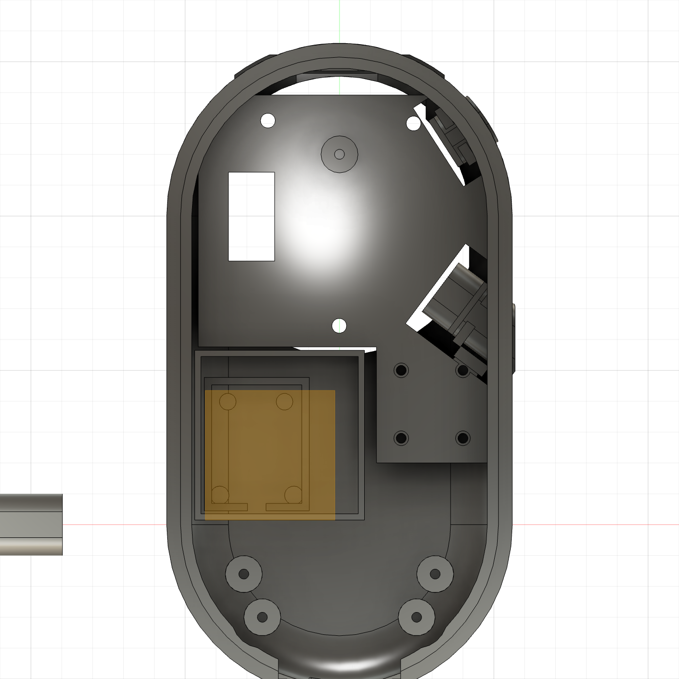
hardware/case/renders/pass11_mag_pocket.png
