jakeholland/firefly/hardware/case/renders/pass11_trim_front.png

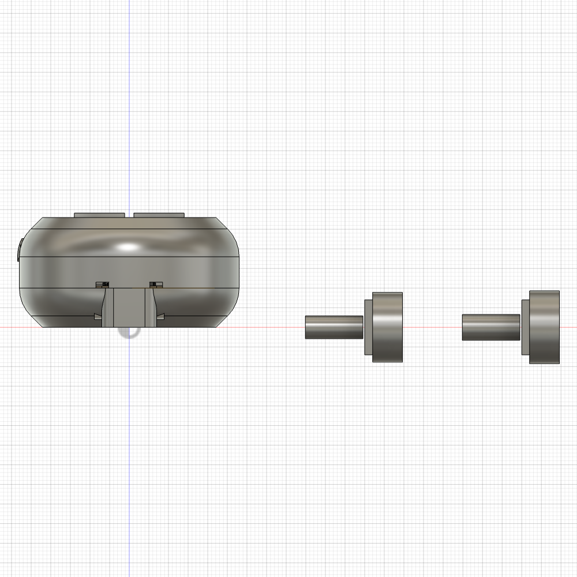
hardware/case/renders/pass11_trim_front.png
