jakeholland/firefly/hardware/case/renders/pass11_window_closeup.png

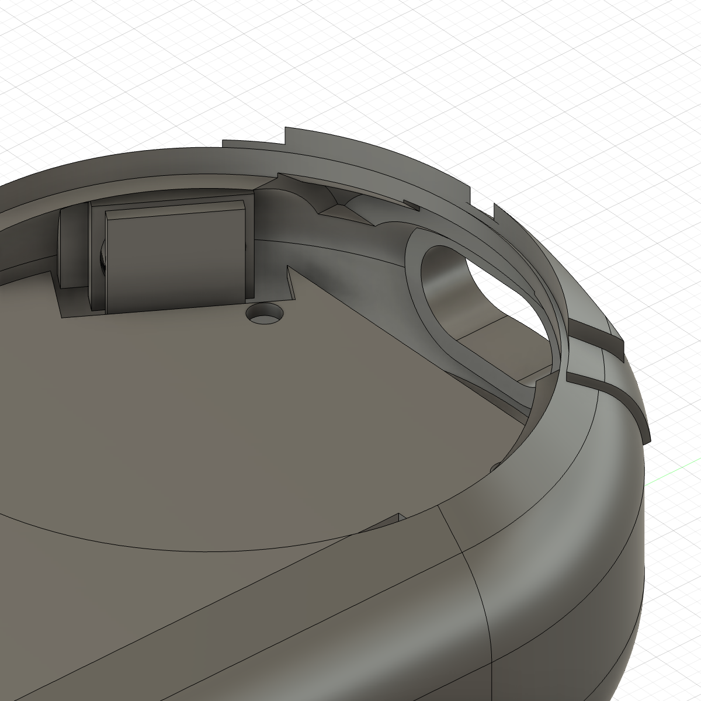
hardware/case/renders/pass11_window_closeup.png
