jakeholland/firefly/hardware/case/renders/pass12_current_front.png

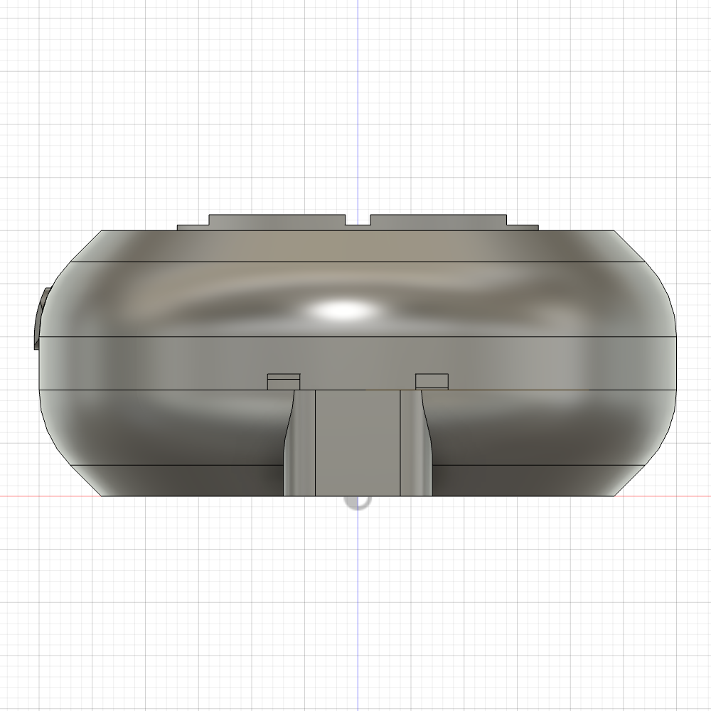
hardware/case/renders/pass12_current_front.png
