jakeholland/firefly/hardware/case/renders/pass12_home_button.png

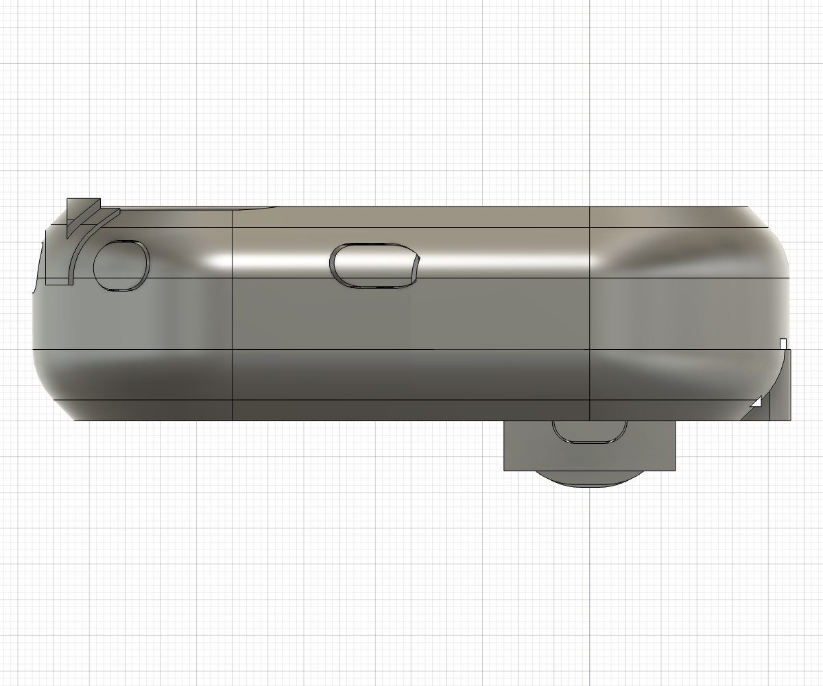
hardware/case/renders/pass12_home_button.png
