jakeholland/firefly/hardware/case/renders/pass12_power_button.png

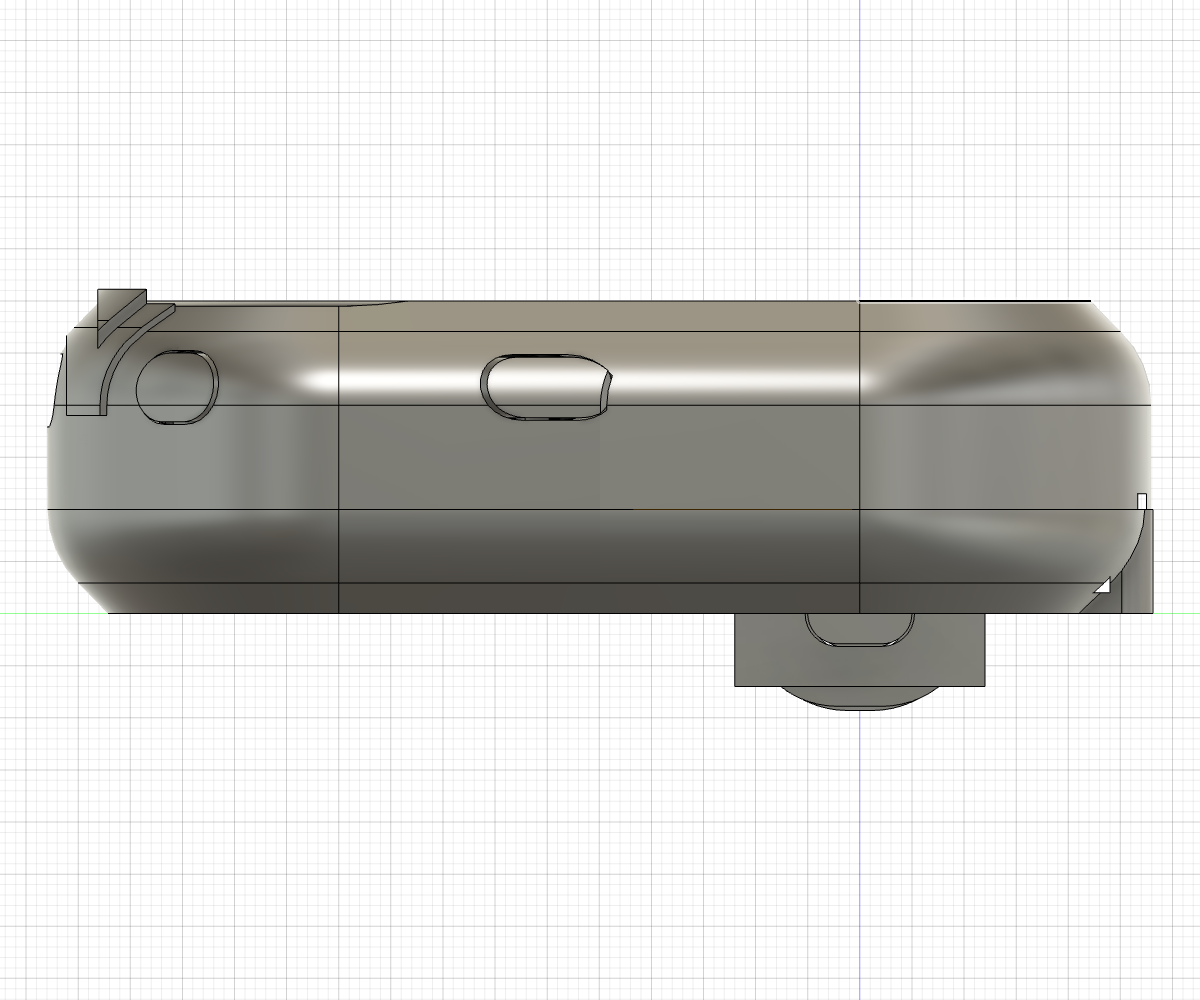
hardware/case/renders/pass12_power_button.png
