jakeholland/firefly/hardware/case/renders/pass12_trim_front.png

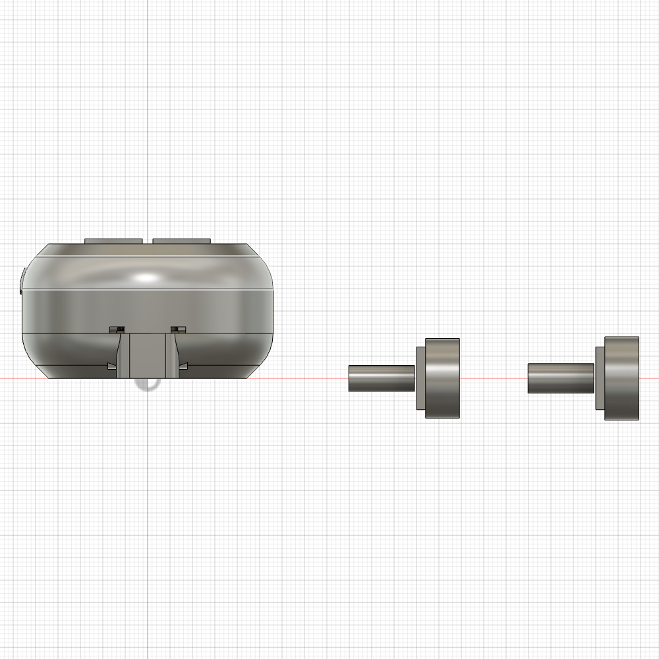
hardware/case/renders/pass12_trim_front.png
