jakeholland/firefly/hardware/case/renders/pass12_trim_right.png

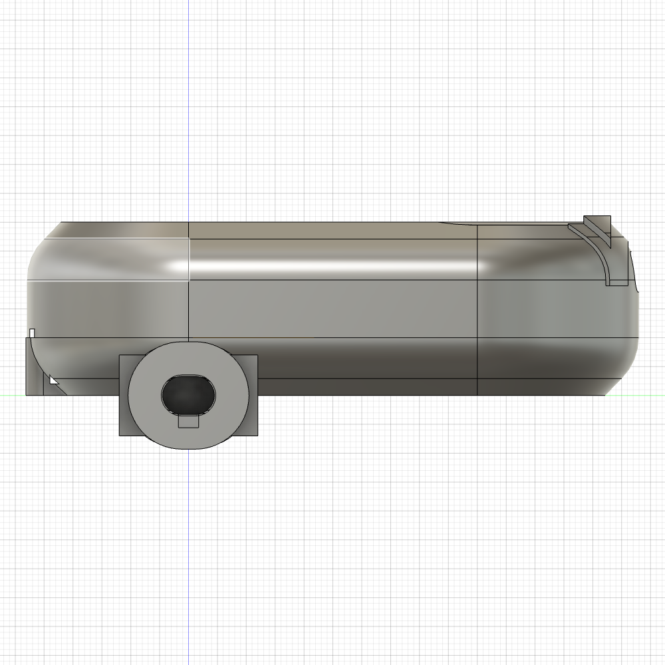
hardware/case/renders/pass12_trim_right.png
