jakeholland/firefly/hardware/case/renders/pass12_usb_end.png

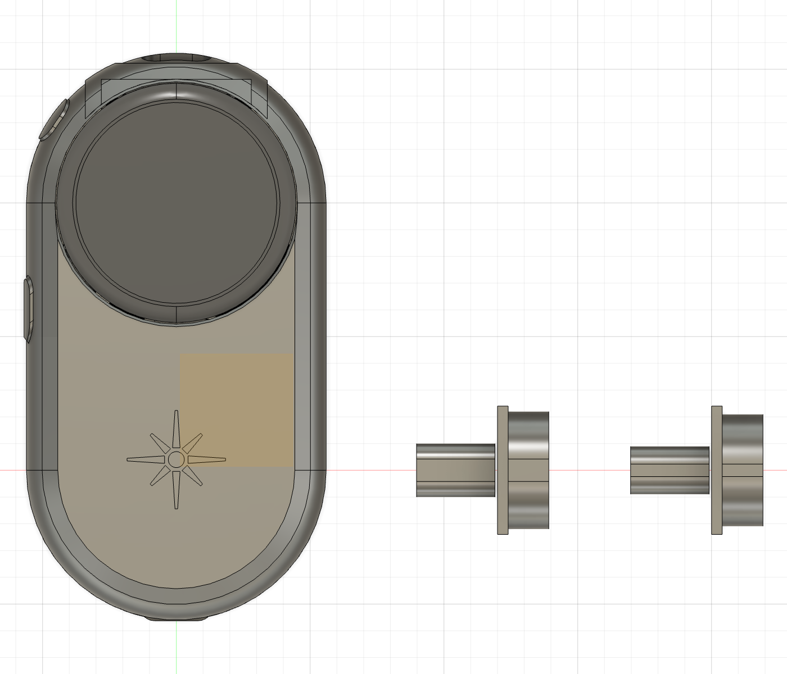
hardware/case/renders/pass12_usb_end.png
