jakeholland/firefly/hardware/case/renders/pass12b_home_button.png

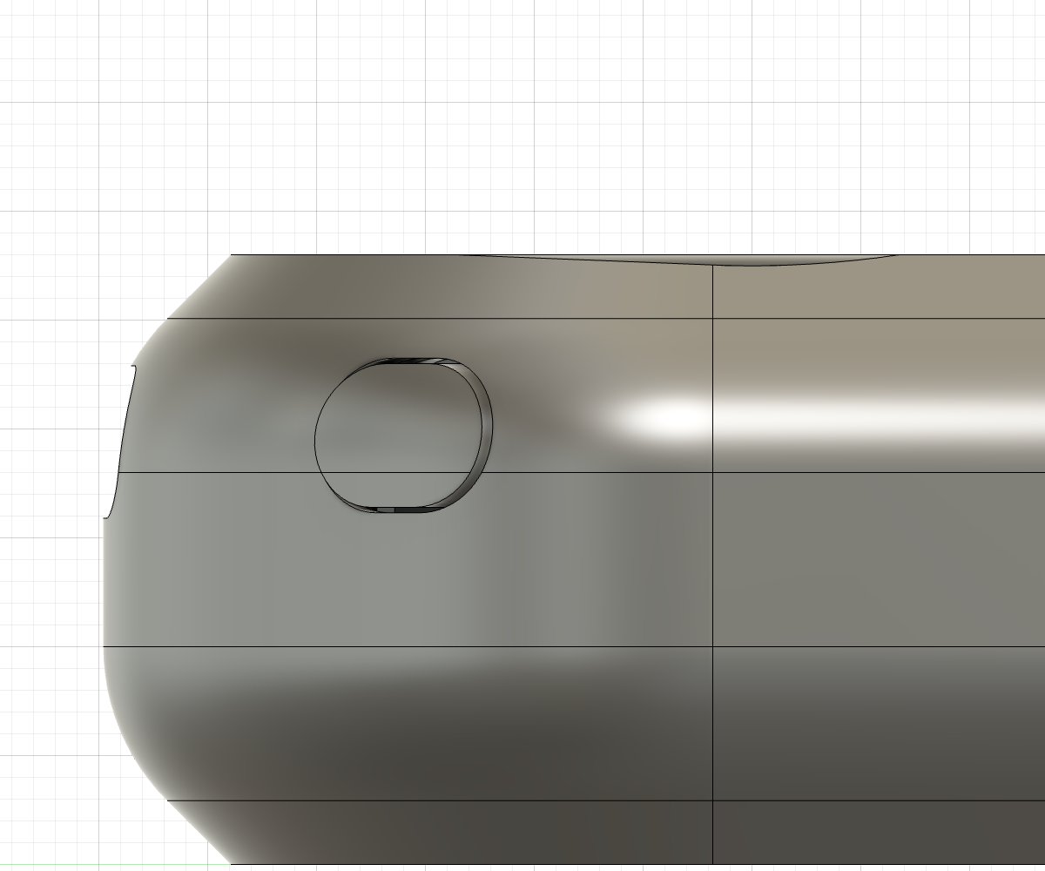
hardware/case/renders/pass12b_home_button.png
