jakeholland/firefly/hardware/case/renders/pass12b_power_button.png

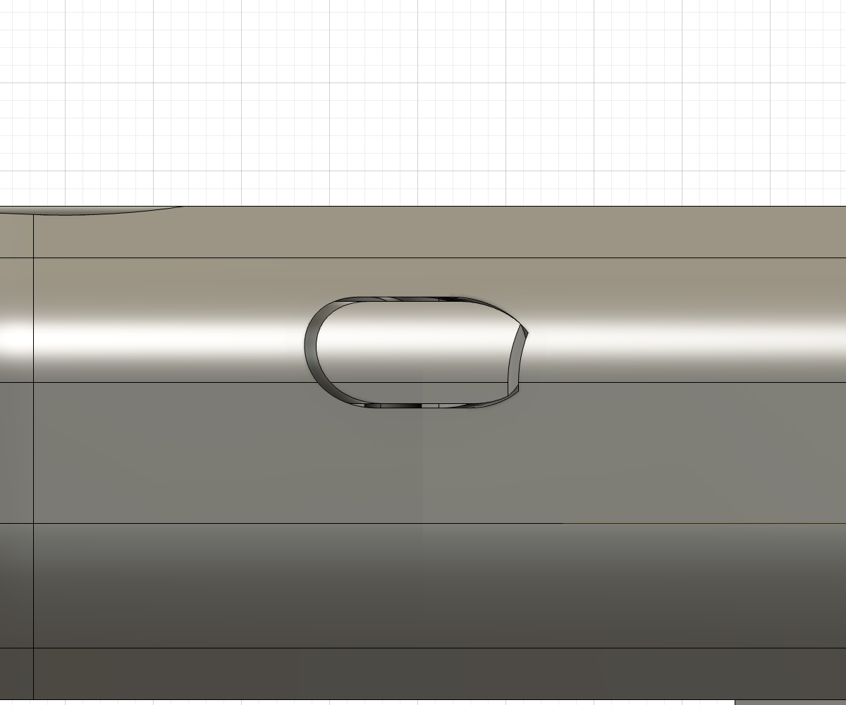
hardware/case/renders/pass12b_power_button.png
