jakeholland/firefly/hardware/case/renders/pass12b_trim_front.png

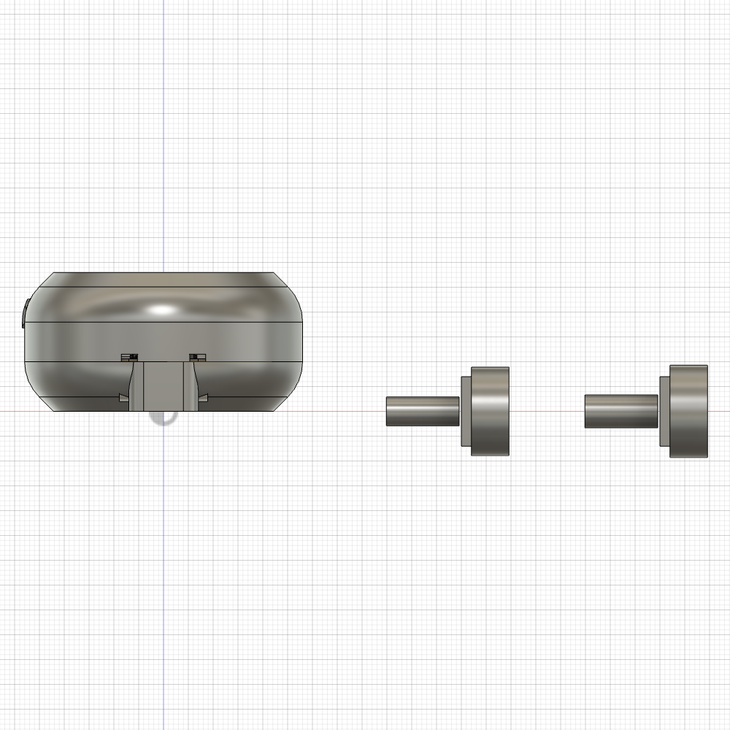
hardware/case/renders/pass12b_trim_front.png
