jakeholland/firefly/hardware/case/renders/pass12b_trim_right.png

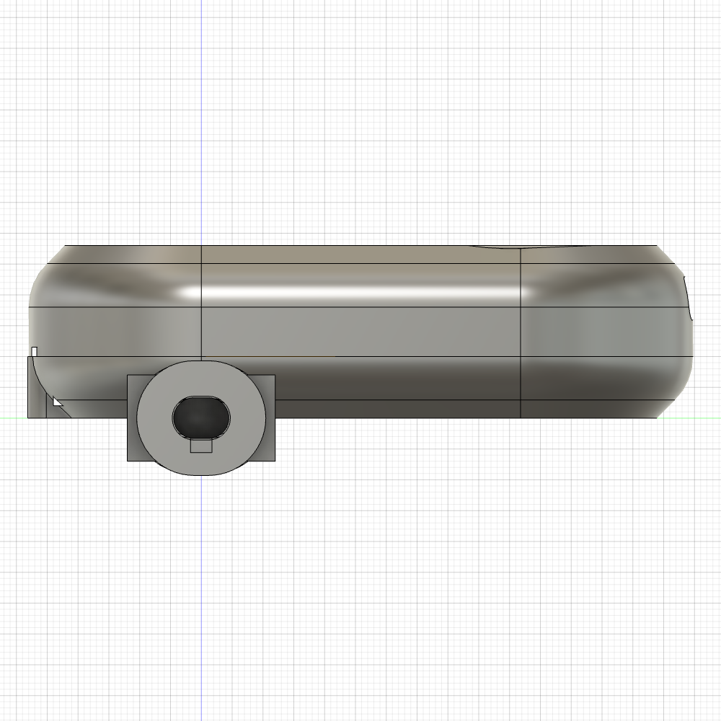
hardware/case/renders/pass12b_trim_right.png
