jakeholland/firefly/hardware/case/renders/pass12b_usb_end.png

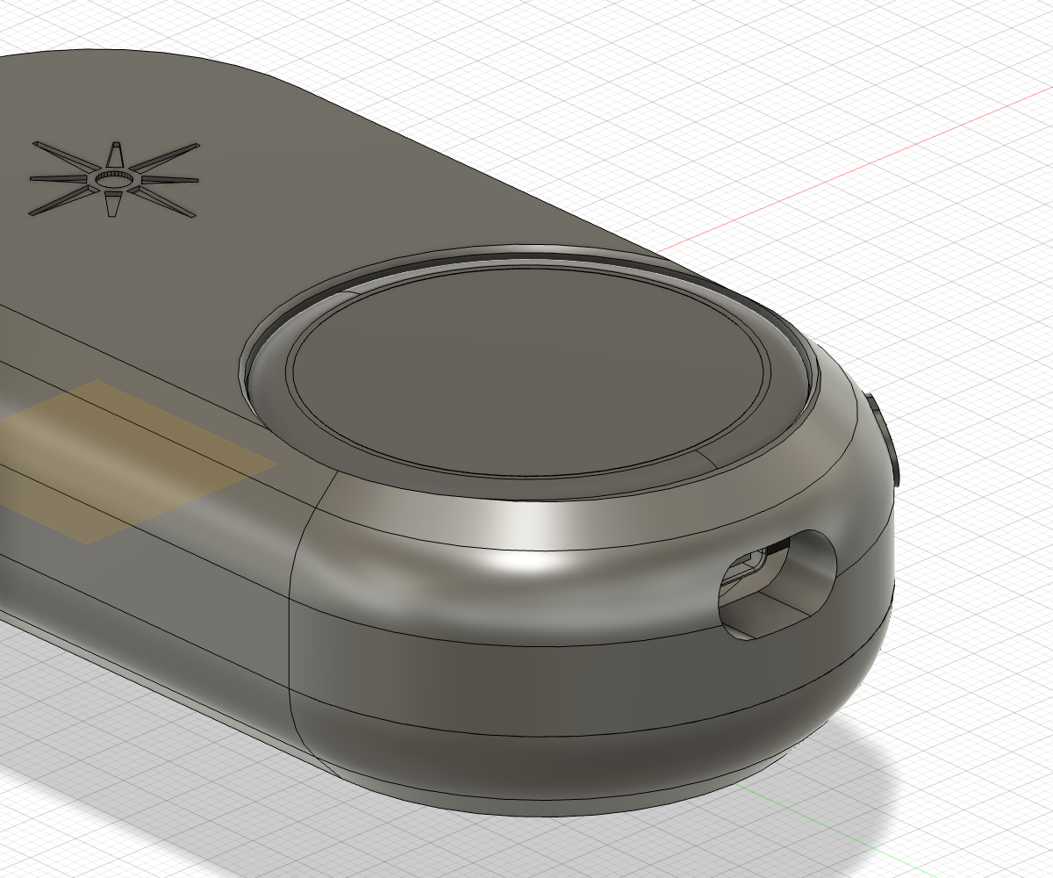
hardware/case/renders/pass12b_usb_end.png
