jakeholland/firefly/hardware/case/renders/pass13_boss_root_closeup.png

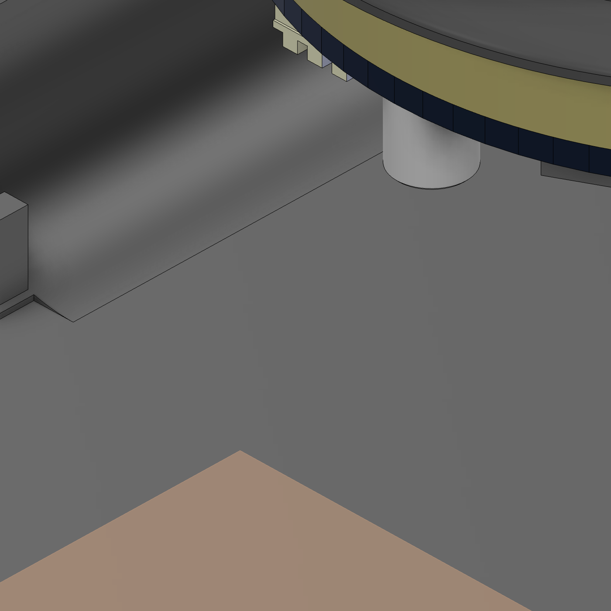
hardware/case/renders/pass13_boss_root_closeup.png
