jakeholland/firefly/hardware/case/renders/pass13_current_plate_battery_window.png

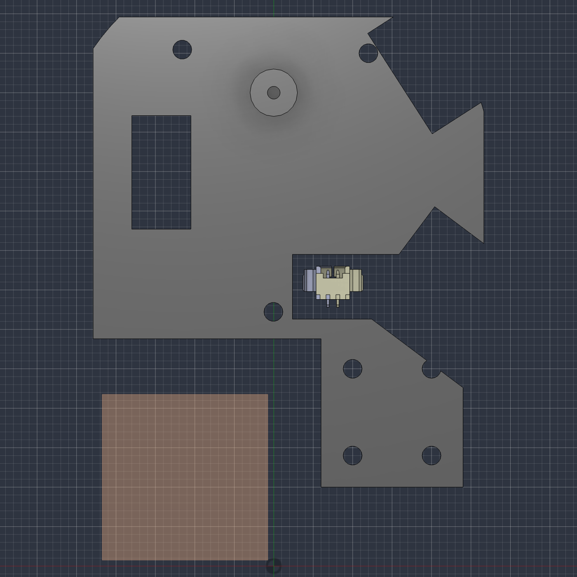
hardware/case/renders/pass13_current_plate_battery_window.png
