jakeholland/firefly/hardware/case/renders/pass13_post_root_closeup.png

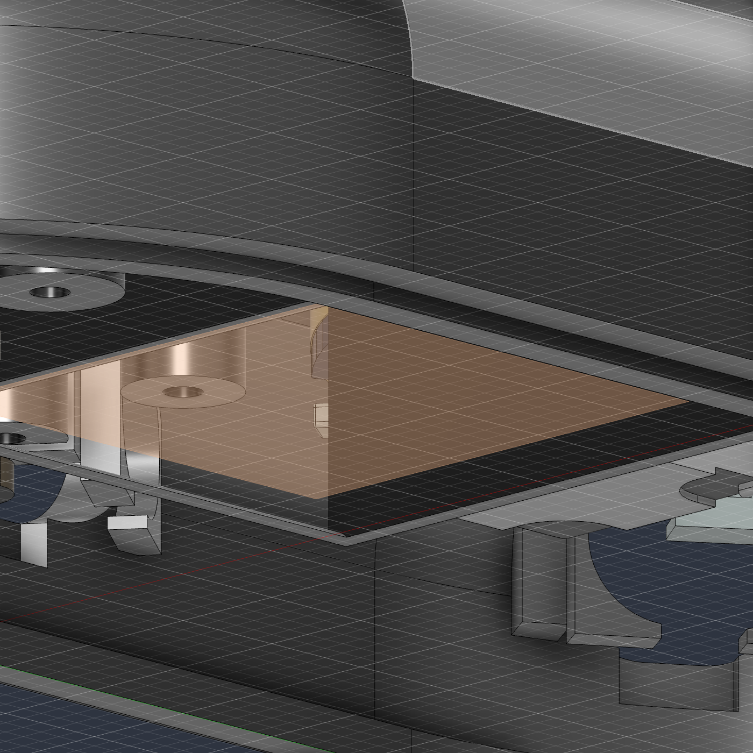
hardware/case/renders/pass13_post_root_closeup.png
