jakeholland/firefly/hardware/case/renders/pass14_current_front.png

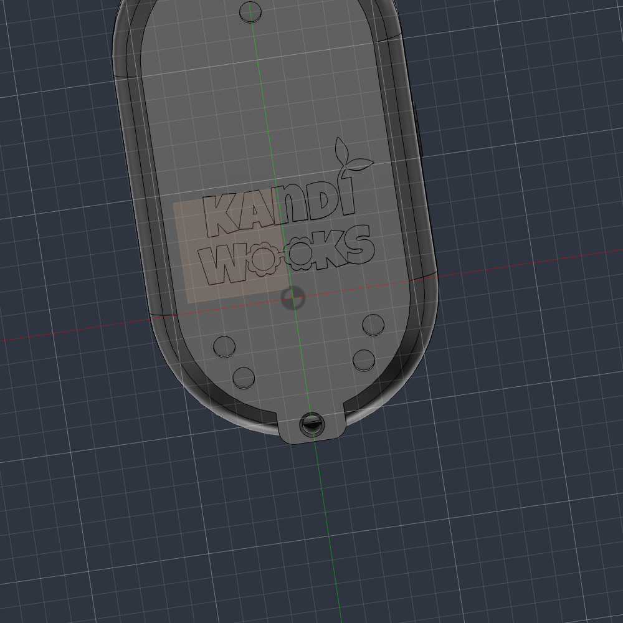
hardware/case/renders/pass14_current_front.png
