jakeholland/firefly/hardware/case/renders/pass14_top_corner_blocks.png

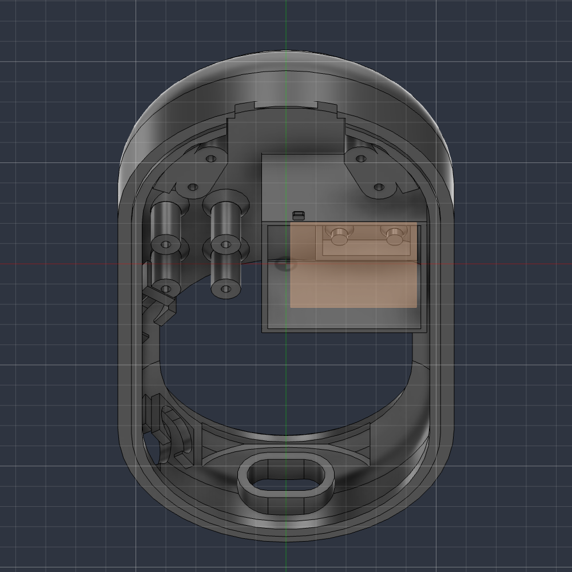
hardware/case/renders/pass14_top_corner_blocks.png
