jakeholland/firefly/hardware/case/renders/pass14_top_inside.png

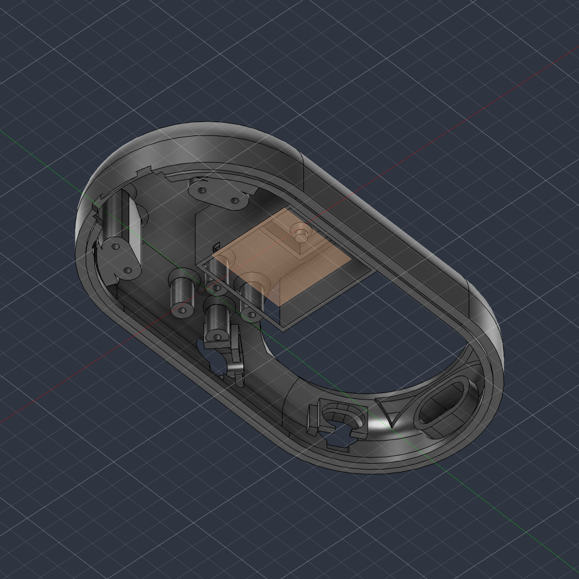
hardware/case/renders/pass14_top_inside.png
