jakeholland/firefly/hardware/case/renders/pass14_trim_front.png

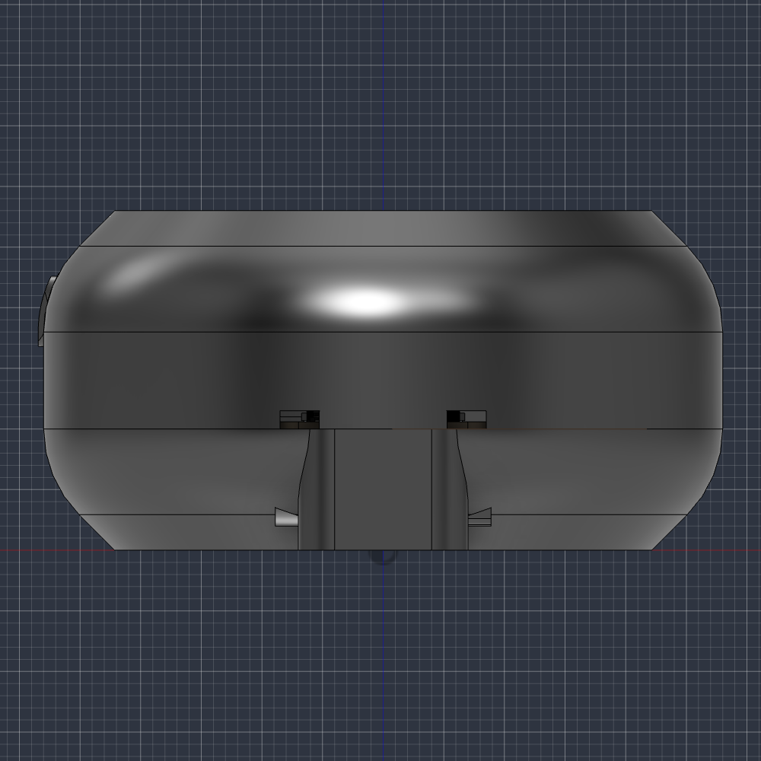
hardware/case/renders/pass14_trim_front.png
