jakeholland/firefly/hardware/case/renders/pass14_trim_iso.png

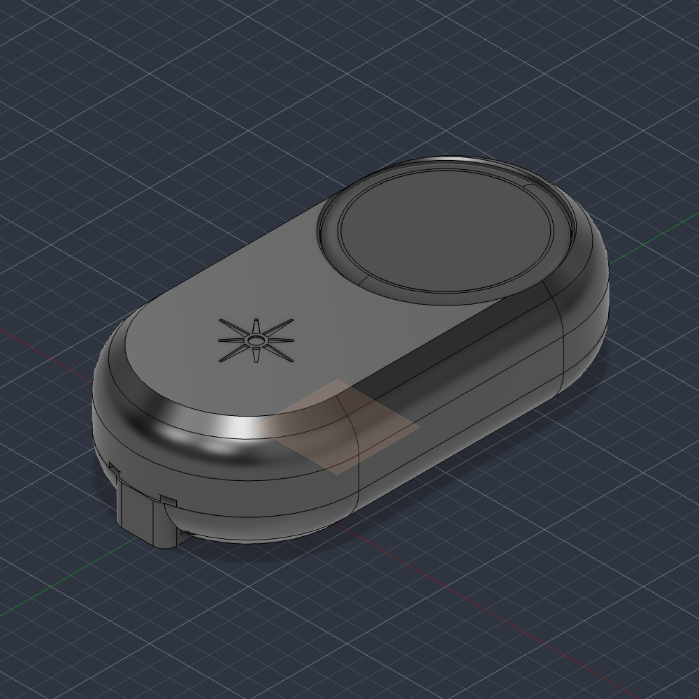
hardware/case/renders/pass14_trim_iso.png
