jakeholland/firefly/hardware/case/renders/pass15_bottom_holes.png

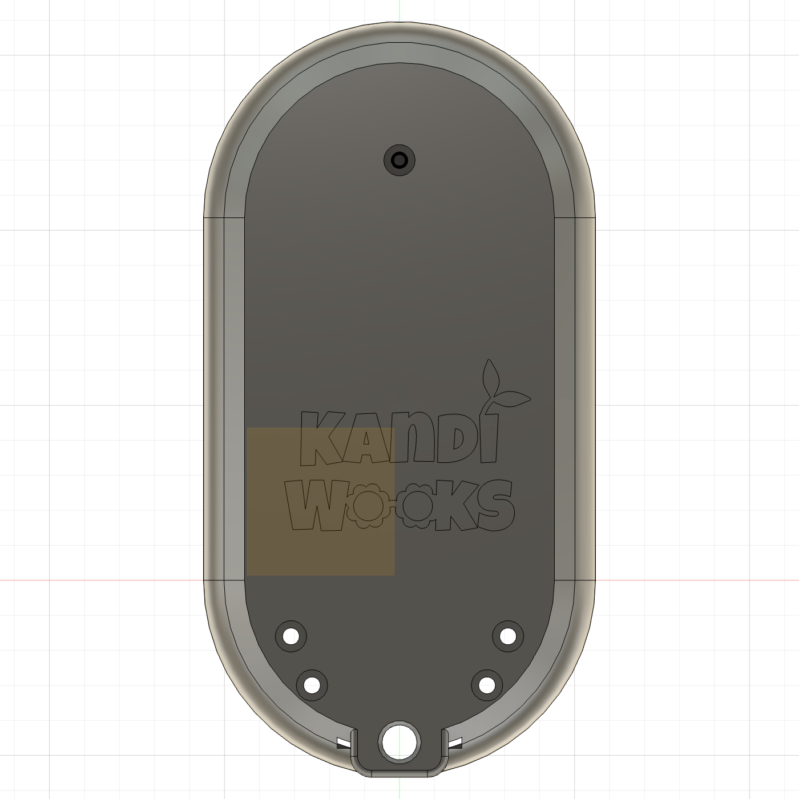
hardware/case/renders/pass15_bottom_holes.png
