jakeholland/firefly/hardware/case/renders/pass15_buttons.png

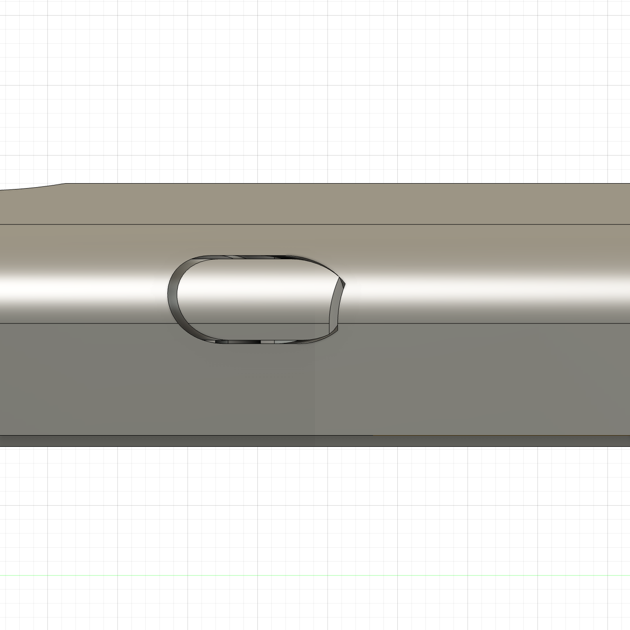
hardware/case/renders/pass15_buttons.png
