jakeholland/firefly/hardware/case/renders/pass15_current_right.png

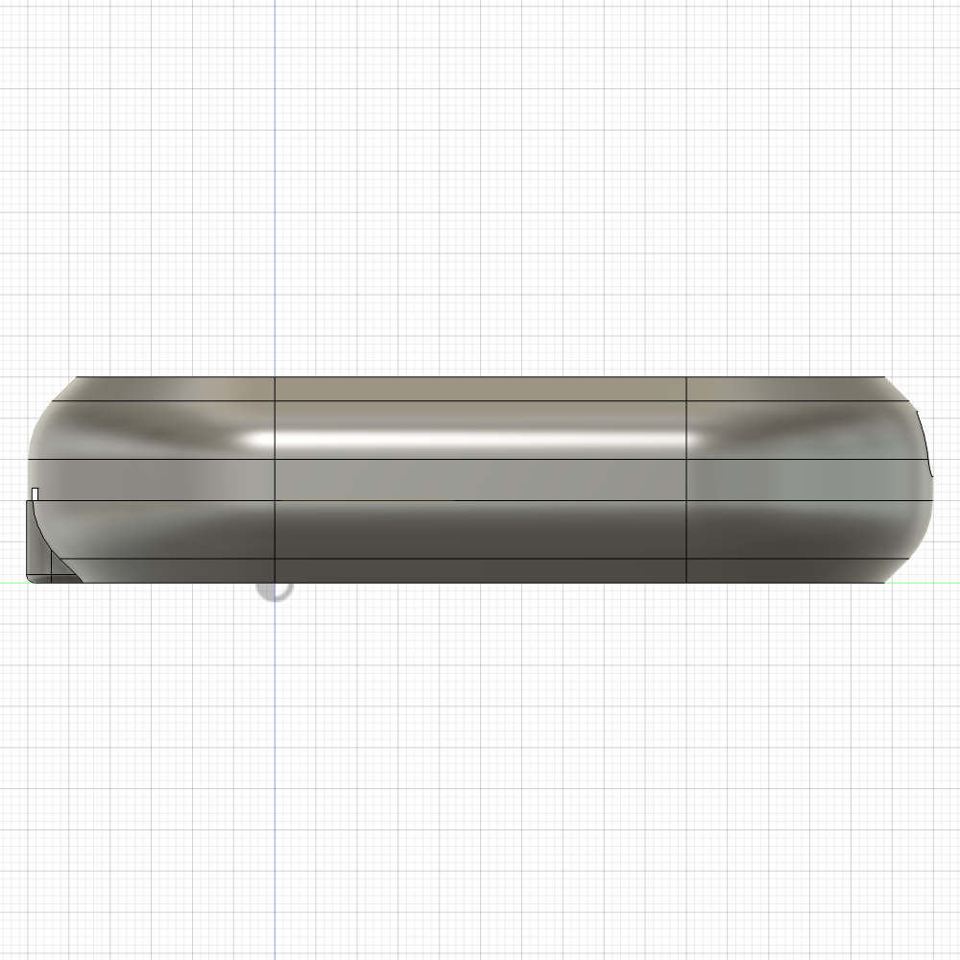
hardware/case/renders/pass15_current_right.png
