jakeholland/firefly/hardware/case/renders/pass15_lug.png

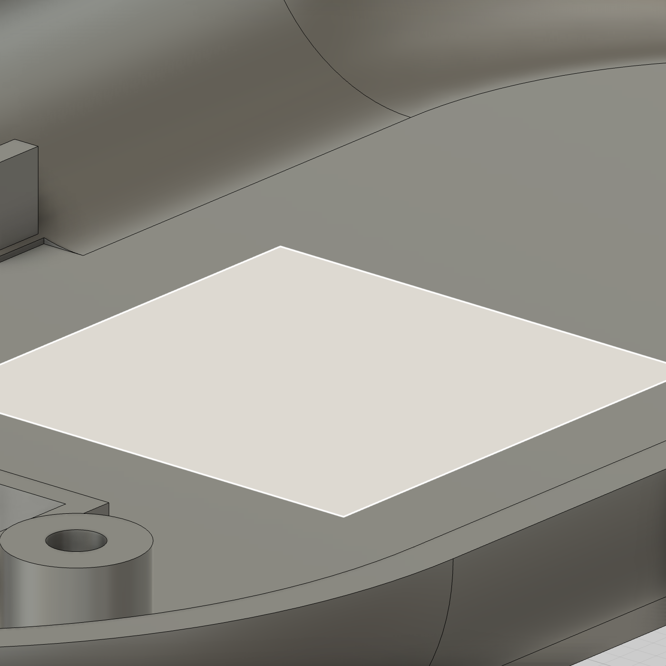
hardware/case/renders/pass15_lug.png
