jakeholland/firefly/hardware/case/renders/pass15_plate_posts.png

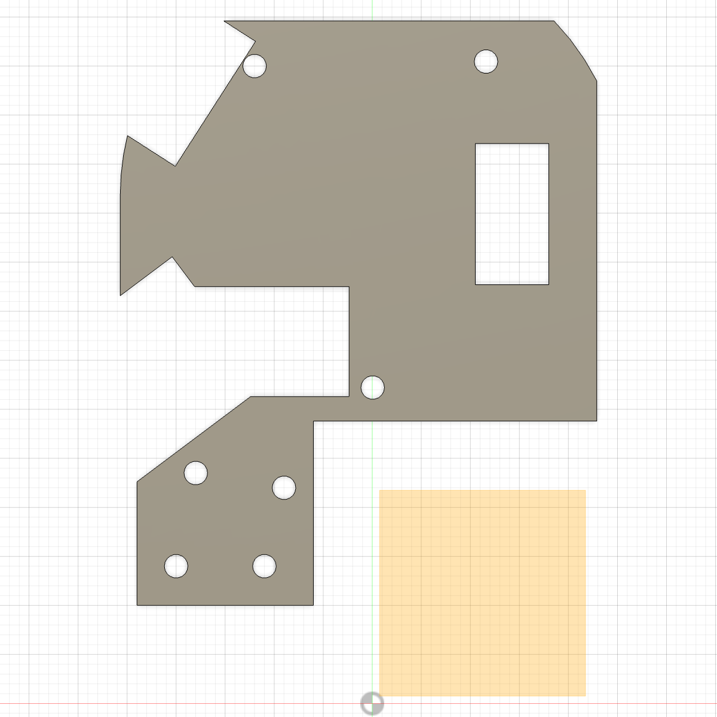
hardware/case/renders/pass15_plate_posts.png
