jakeholland/firefly/hardware/case/renders/pass15_top_inside.png

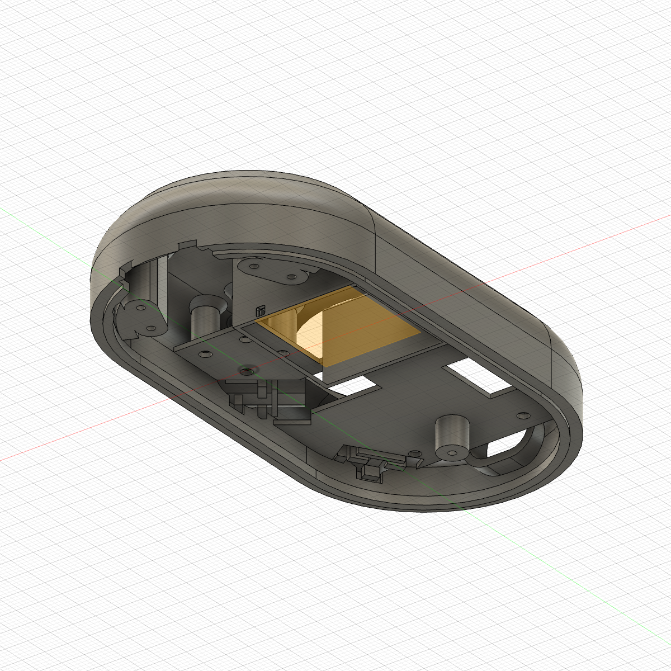
hardware/case/renders/pass15_top_inside.png
