jakeholland/firefly/hardware/case/renders/pass15_top_window_edge.png

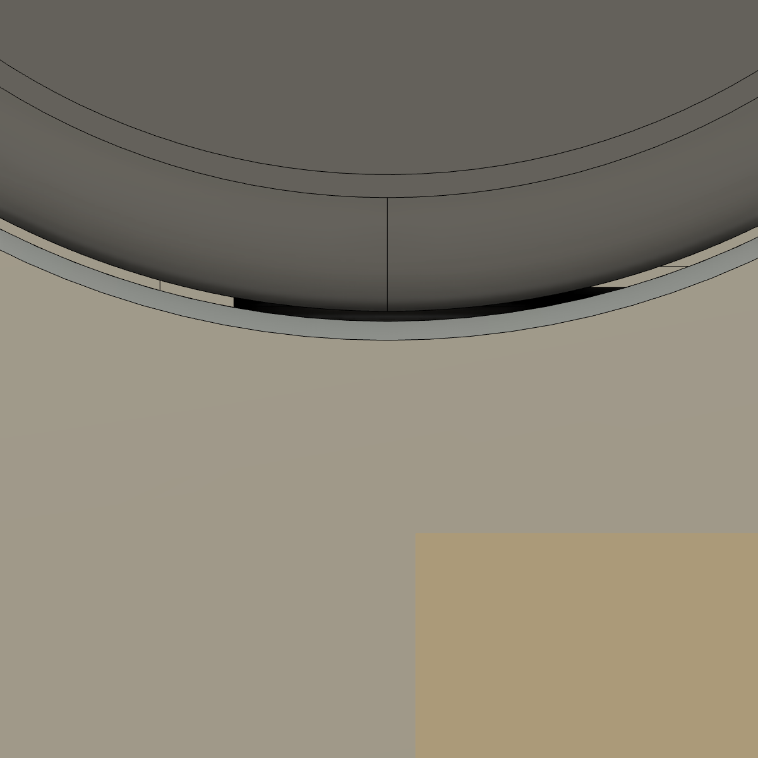
hardware/case/renders/pass15_top_window_edge.png
