jakeholland/firefly/hardware/case/renders/pass15_top_window_edge_wide2.png

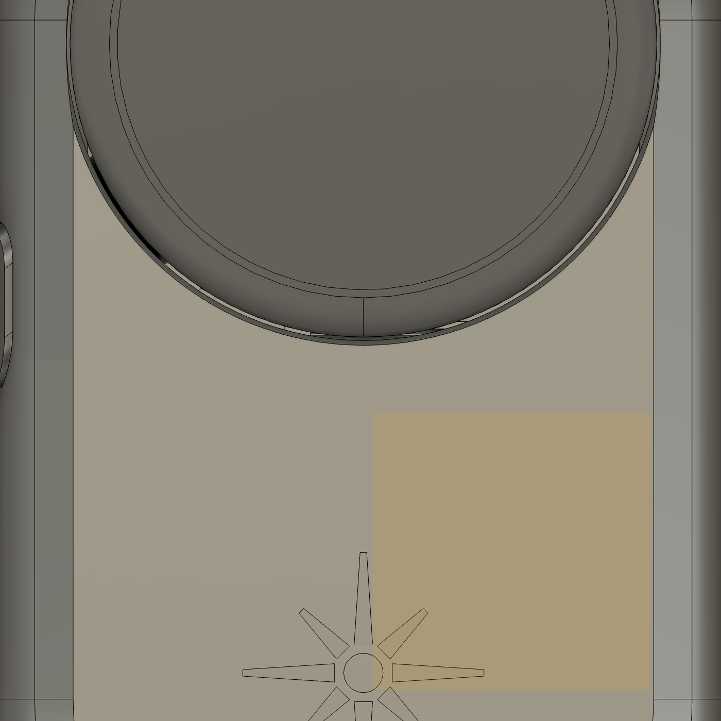
hardware/case/renders/pass15_top_window_edge_wide2.png
