jakeholland/firefly/hardware/case/renders/pass15_top_window_edge_wide.png

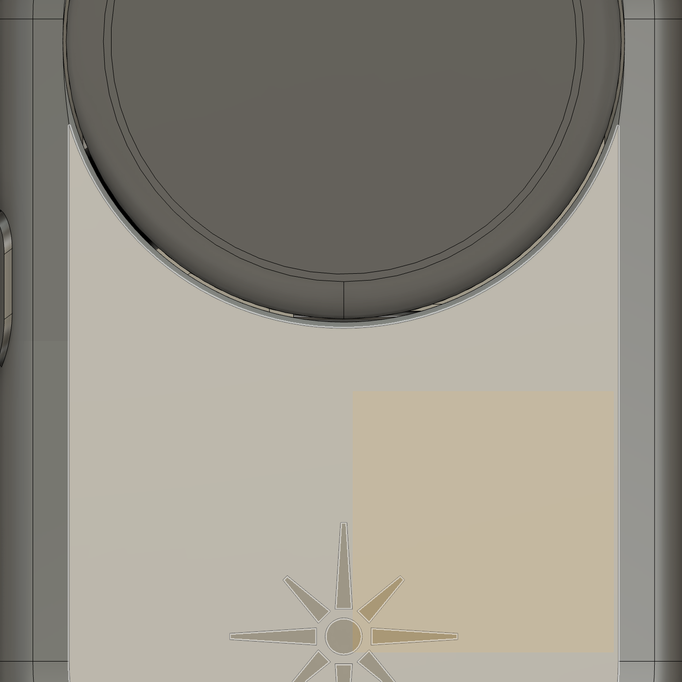
hardware/case/renders/pass15_top_window_edge_wide.png
