jakeholland/firefly/hardware/case/renders/pass15_trim_front.png

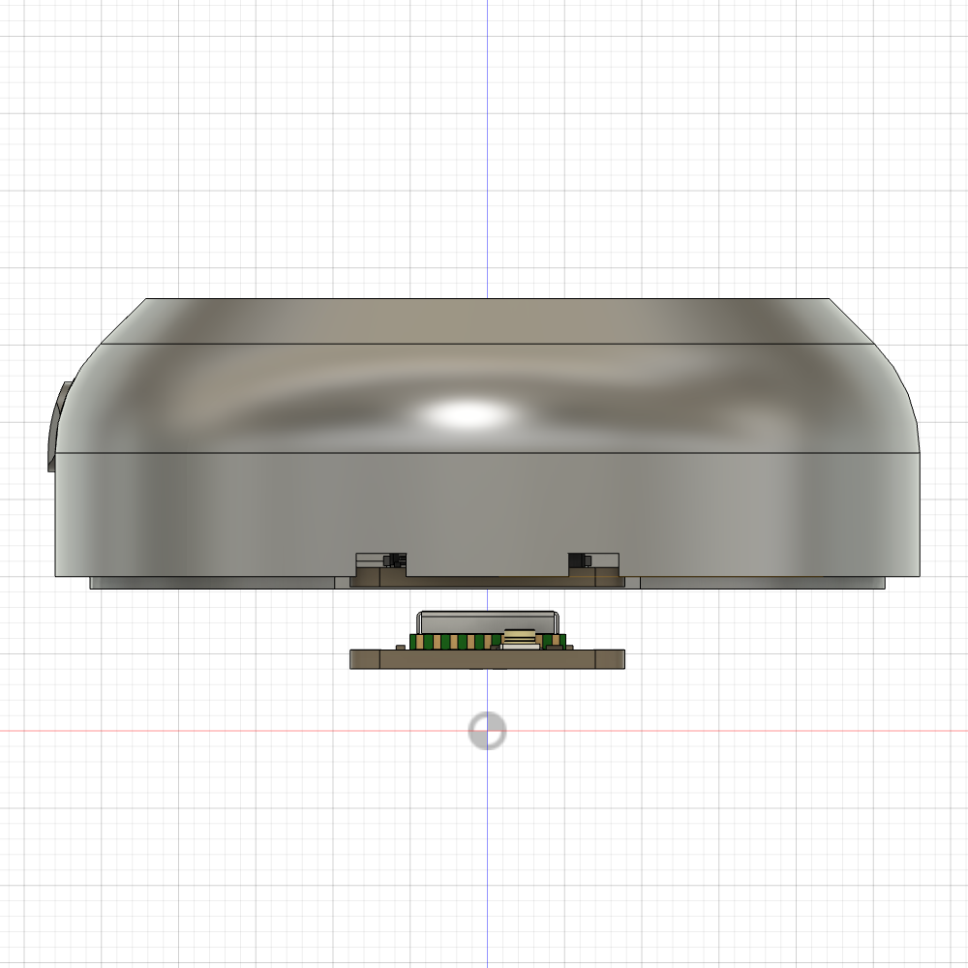
hardware/case/renders/pass15_trim_front.png
