jakeholland/firefly/hardware/case/renders/pass15_trim_iso.png

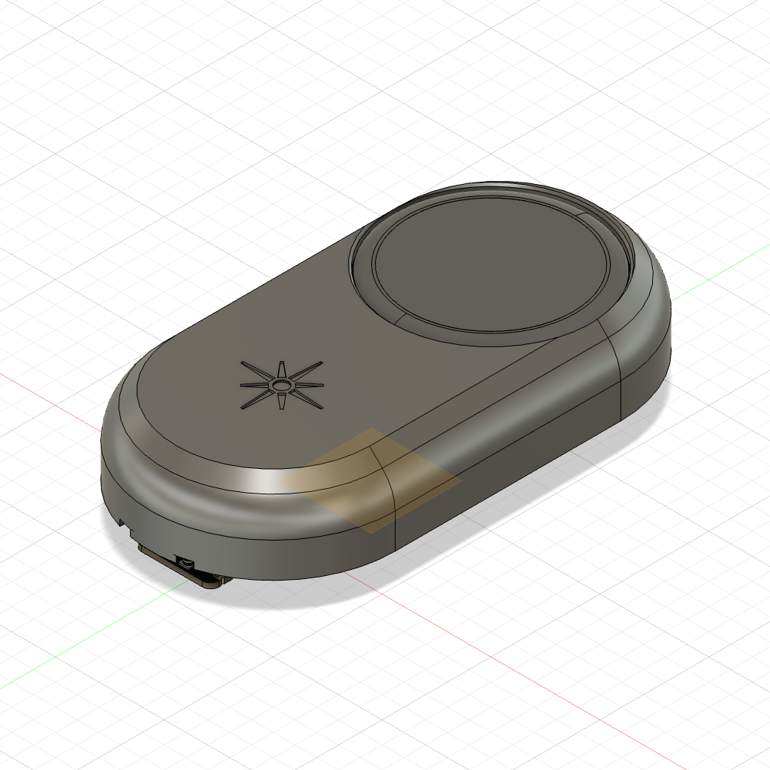
hardware/case/renders/pass15_trim_iso.png
