jakeholland/firefly/hardware/case/renders/pass15_trim_right.png

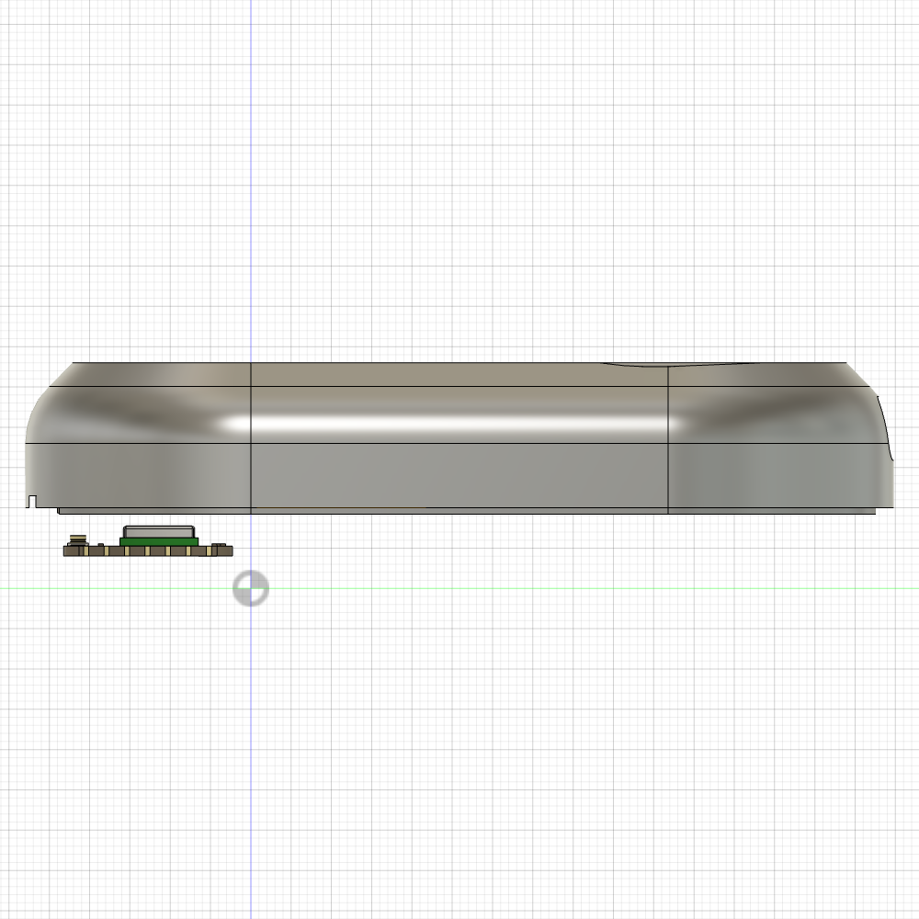
hardware/case/renders/pass15_trim_right.png
