jakeholland/firefly/hardware/case/renders/pass16_trim_front.png

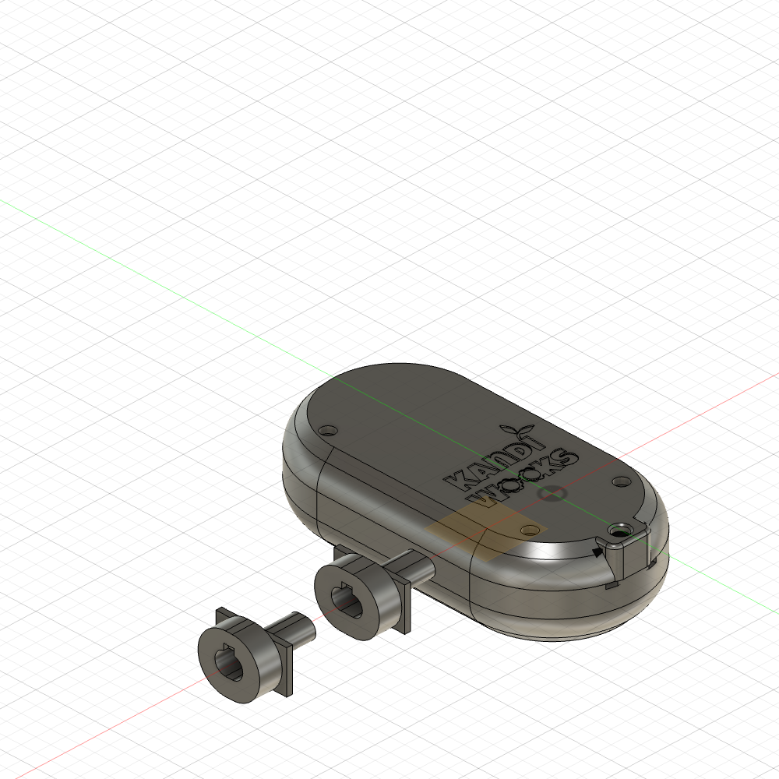
hardware/case/renders/pass16_trim_front.png
