jakeholland/firefly/hardware/case/renders/pass16_trim_top.png

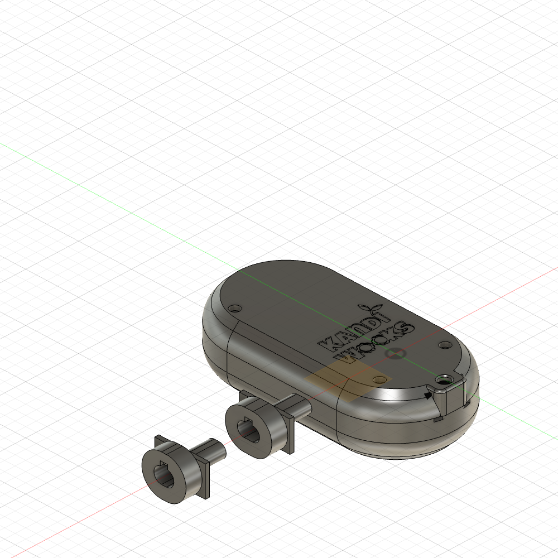
hardware/case/renders/pass16_trim_top.png
