jakeholland/firefly/hardware/case/renders/plate_underside.png

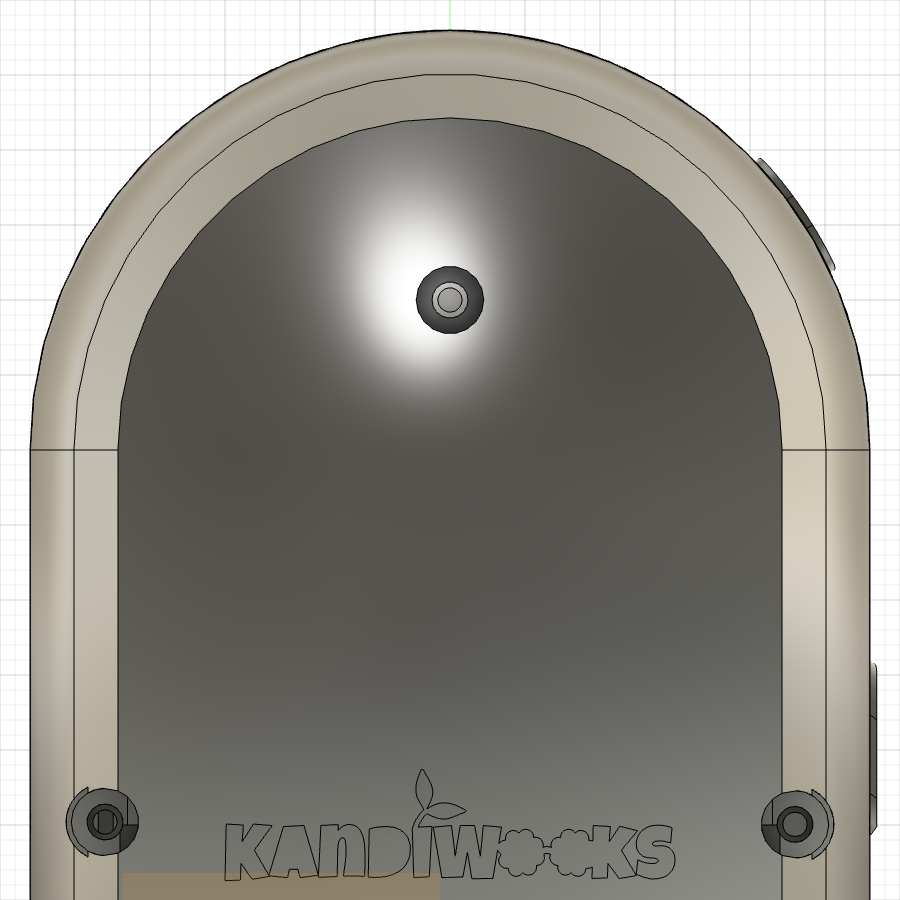
hardware/case/renders/plate_underside.png
