jakeholland/firefly/hardware/case/renders/power_button_ext.png

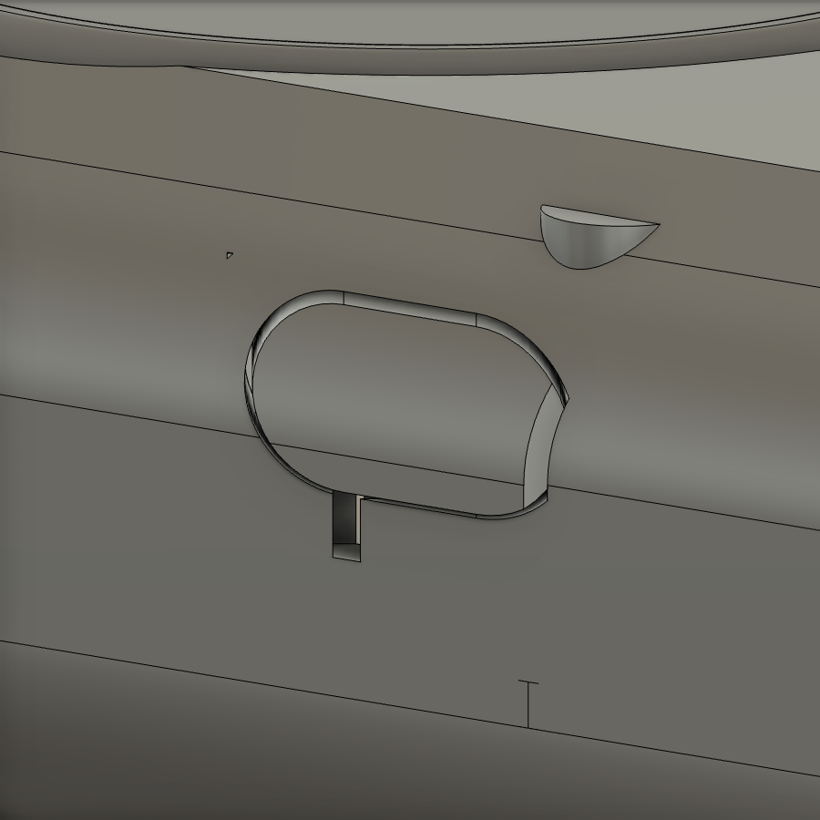
hardware/case/renders/power_button_ext.png
