jakeholland/firefly/hardware/case/renders/rim_lanyard_end.png

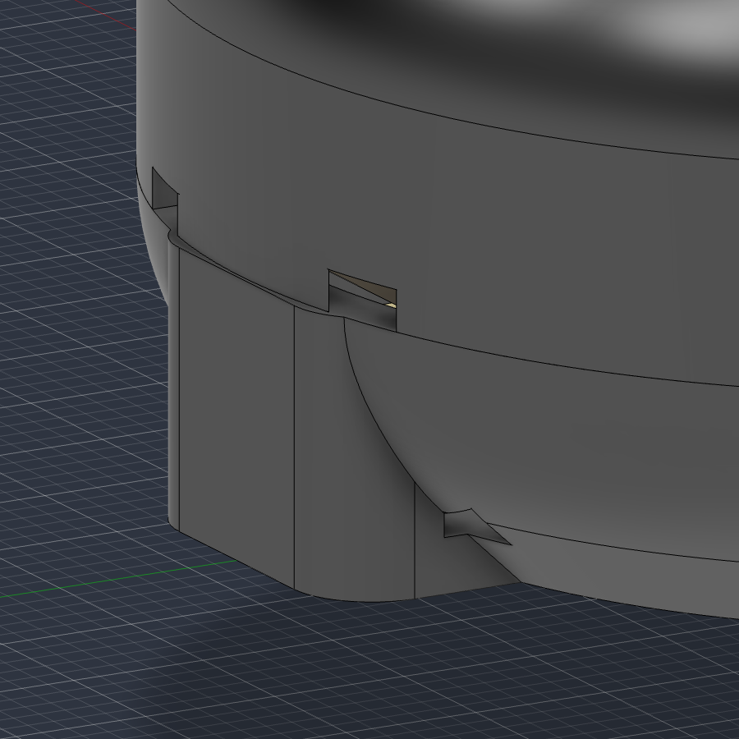
hardware/case/renders/rim_lanyard_end.png
