jakeholland/firefly/hardware/case/renders/rim_usb_end.png

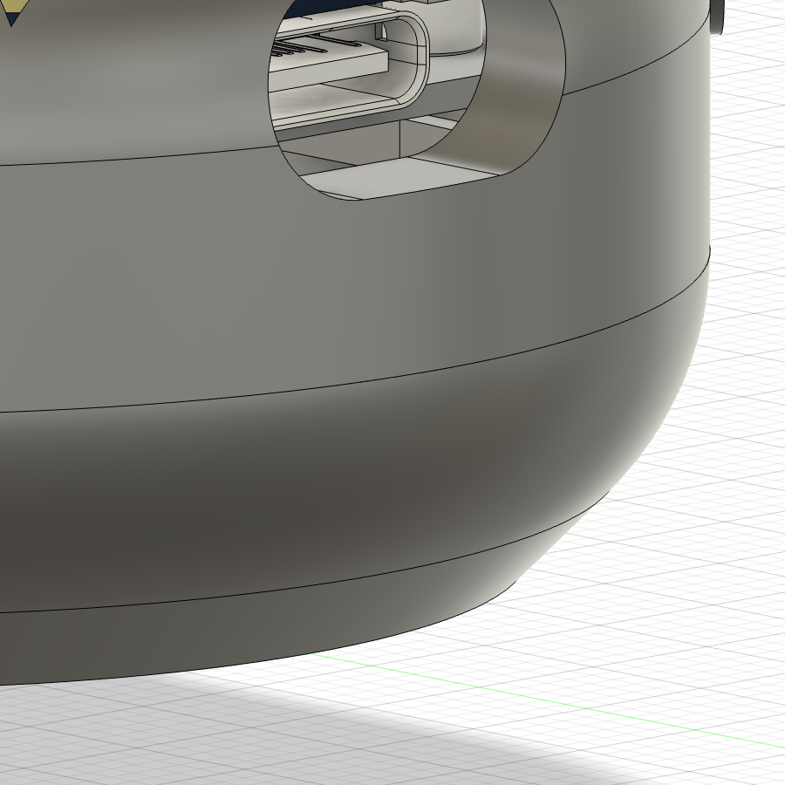
hardware/case/renders/rim_usb_end.png
