jakeholland/firefly/hardware/case/renders/trim_front.png

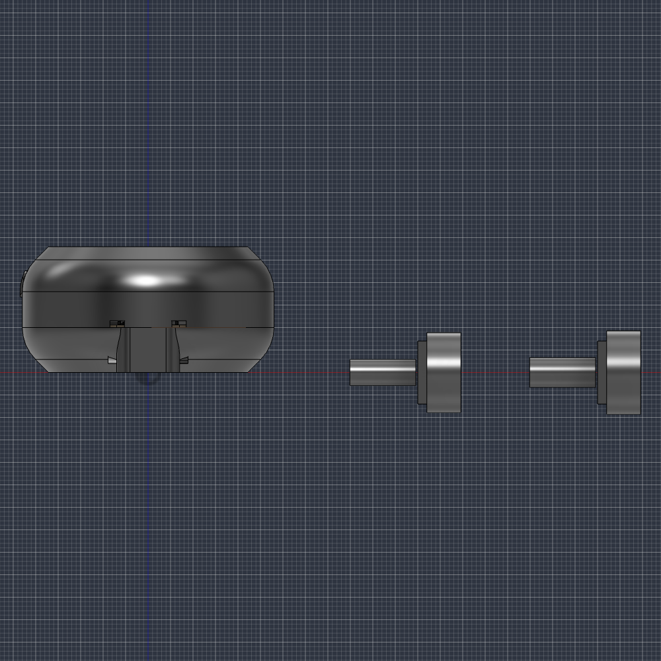
hardware/case/renders/trim_front.png
