jakeholland/firefly/marketing/screenshots/6.9in/01_radar.png

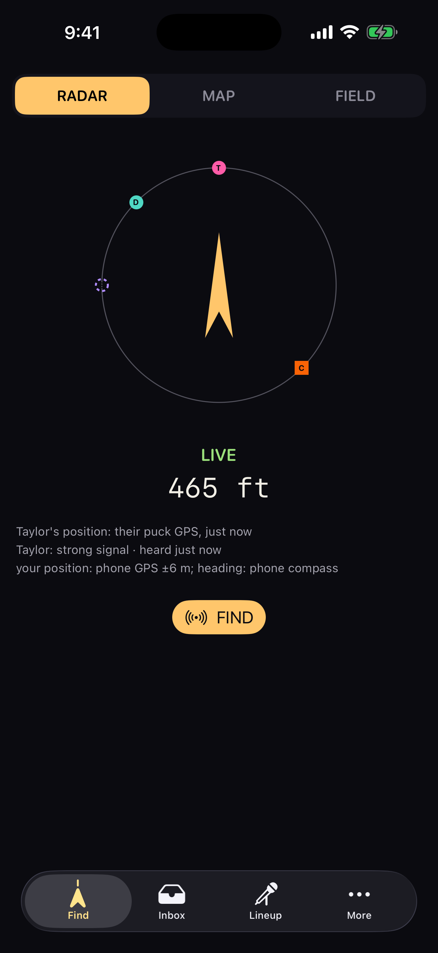
marketing/screenshots/6.9in/01_radar.png
