jakeholland/firefly/marketing/screenshots/6.9in/03_flare.png

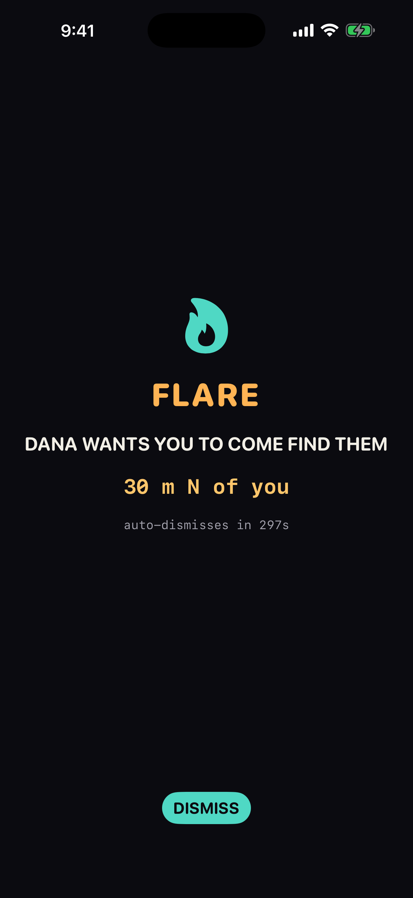
marketing/screenshots/6.9in/03_flare.png
