jakeholland/firefly/marketing/screenshots/6.9in/05_lineup.png

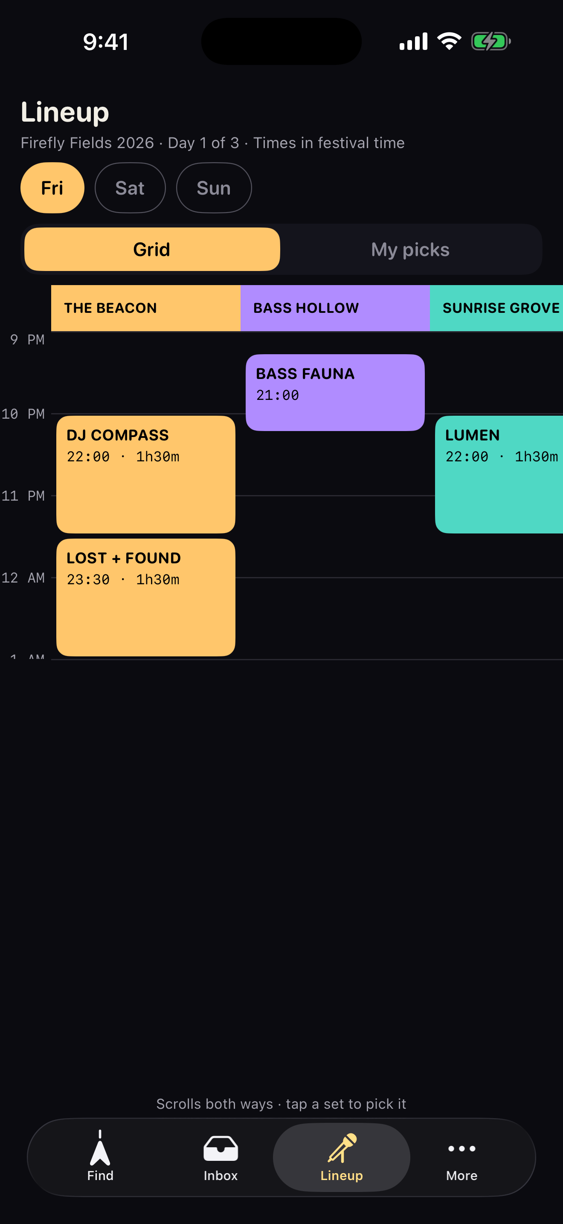
marketing/screenshots/6.9in/05_lineup.png
