jakeholland/firefly/hardware/case/export/coupons/coupon_power_wall.stl

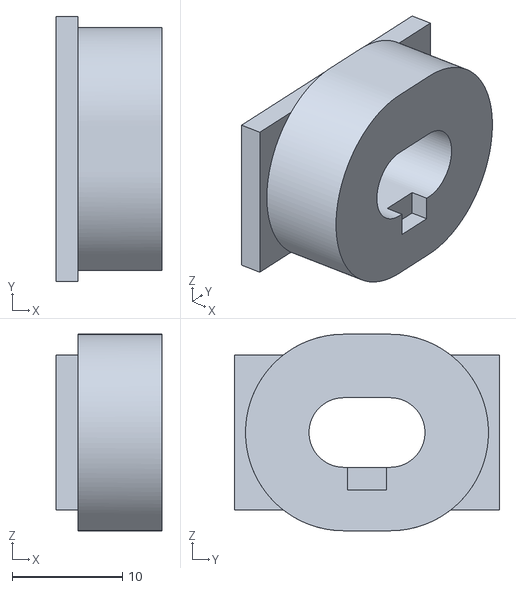
[picture p147: CAD file, 2026-09-07]
hardware/case/export/coupons/coupon_power_wall.stl
9.60 x 24.0 x 17.8
