jakeholland/firefly/hardware/case/export/coupons/coupon_home_wall.stl

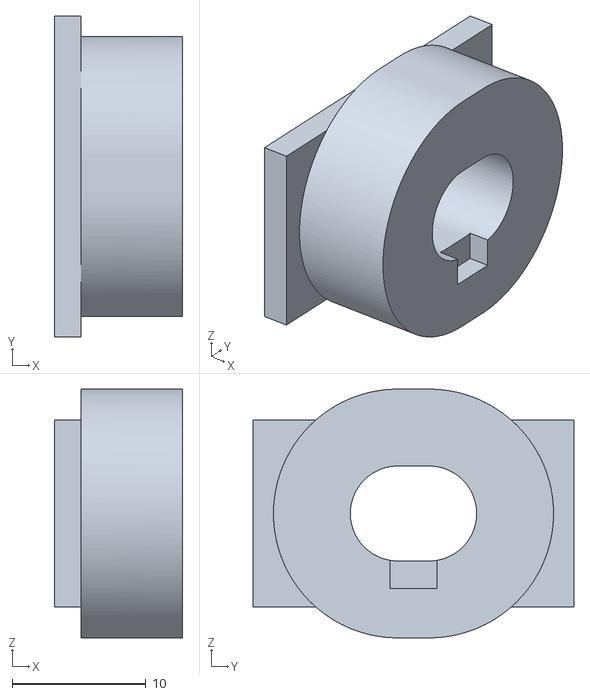
[picture p148: CAD file, 2026-09-07]
hardware/case/export/coupons/coupon_home_wall.stl
9.60 x 24.0 x 18.6
