jakeholland/firefly/firmware/tests/golden/compass_cal_ritual.png

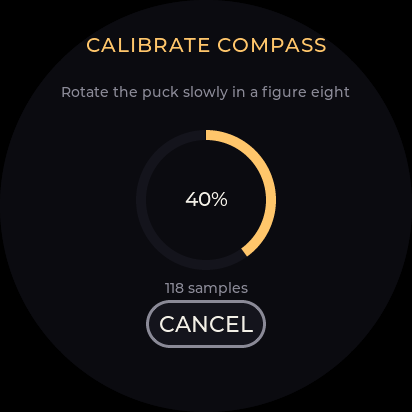
firmware/tests/golden/compass_cal_ritual.png
