jakeholland/firefly/firmware/tests/golden/compass_cal_ritual_ready.png

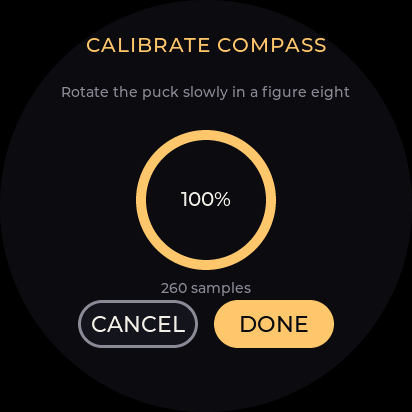
firmware/tests/golden/compass_cal_ritual_ready.png
