jakeholland/firefly/firmware/tests/golden/compose_123.png

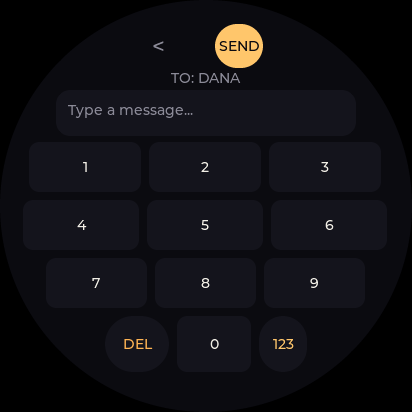
firmware/tests/golden/compose_123.png
