jakeholland/firefly/firmware/tests/golden/compose_pred_artist.png

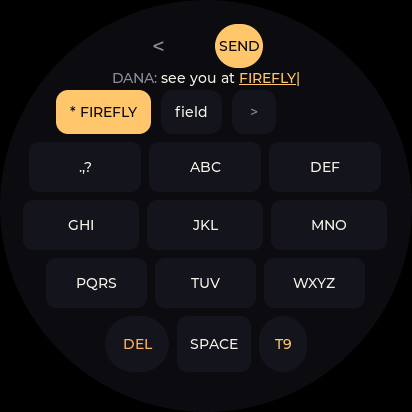
firmware/tests/golden/compose_pred_artist.png
