jakeholland/firefly/firmware/tests/golden/compose_pred_mid.png

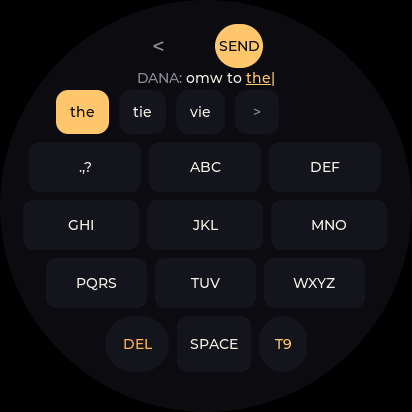
firmware/tests/golden/compose_pred_mid.png
