jakeholland/firefly/firmware/tests/golden/crew_default.png

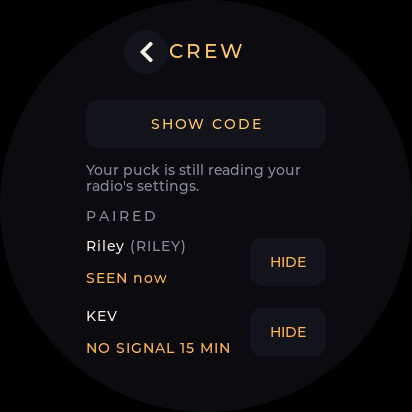
firmware/tests/golden/crew_default.png
