jakeholland/firefly/firmware/tests/golden/crew_empty.png

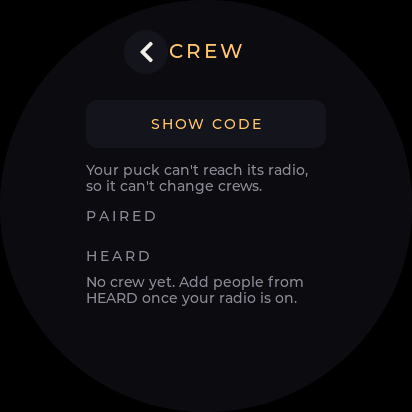
firmware/tests/golden/crew_empty.png
