jakeholland/firefly/firmware/tests/golden/crew_leave_pill.png

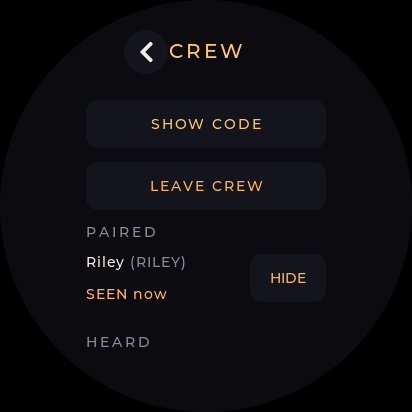
firmware/tests/golden/crew_leave_pill.png
