jakeholland/firefly/firmware/tests/golden/crew_op_confirm_leave.png

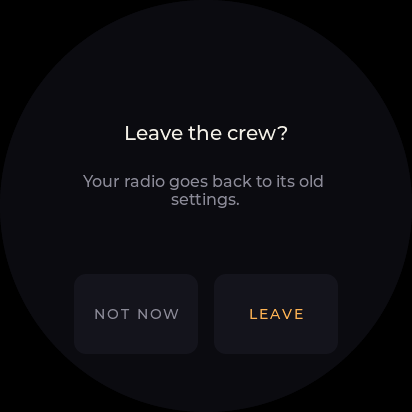
firmware/tests/golden/crew_op_confirm_leave.png
