jakeholland/firefly/firmware/tests/golden/crew_op_confirm_leave_no_snapshot.png

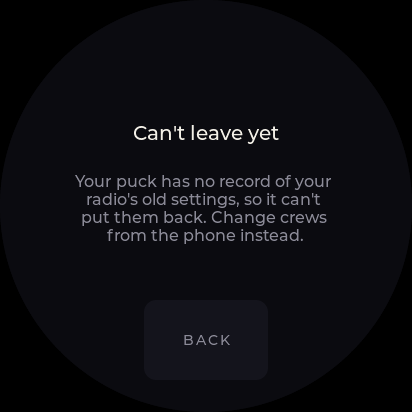
firmware/tests/golden/crew_op_confirm_leave_no_snapshot.png
