jakeholland/firefly/firmware/tests/golden/crew_op_confirm_start.png

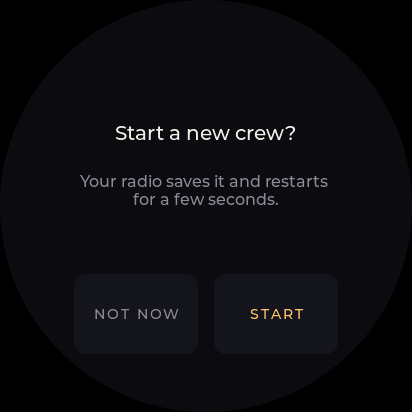
firmware/tests/golden/crew_op_confirm_start.png
