jakeholland/firefly/firmware/tests/golden/crew_op_failed.png

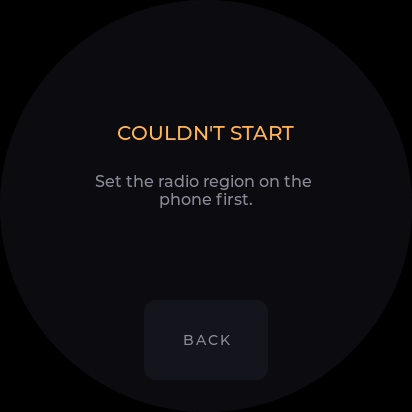
firmware/tests/golden/crew_op_failed.png
