jakeholland/firefly/firmware/tests/golden/crew_op_ready.png

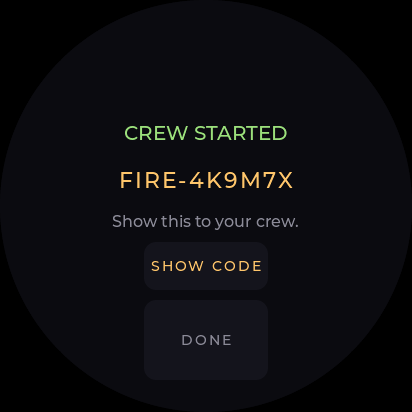
firmware/tests/golden/crew_op_ready.png
