jakeholland/firefly/firmware/tests/golden/crew_op_verifying.png

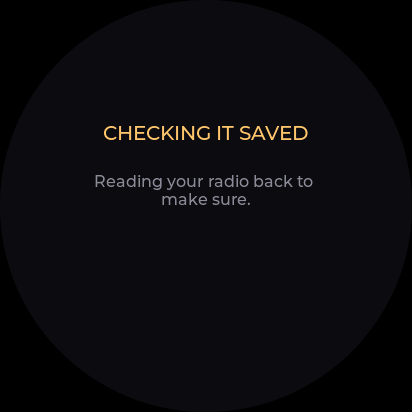
firmware/tests/golden/crew_op_verifying.png
