jakeholland/firefly/firmware/tests/golden/crew_overflow.png

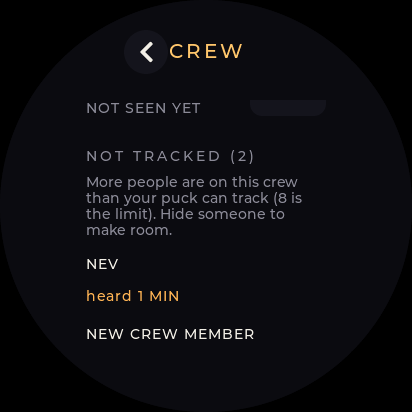
firmware/tests/golden/crew_overflow.png
