jakeholland/firefly/firmware/tests/golden/crew_region_unset.png

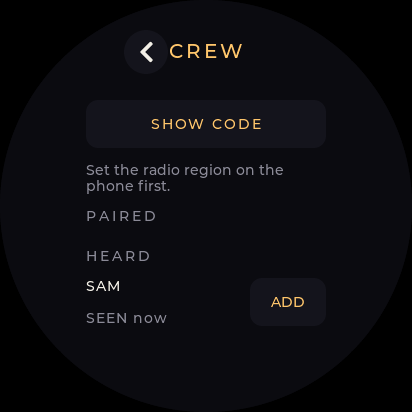
firmware/tests/golden/crew_region_unset.png
