jakeholland/firefly/firmware/tests/golden/crew_show_code.png

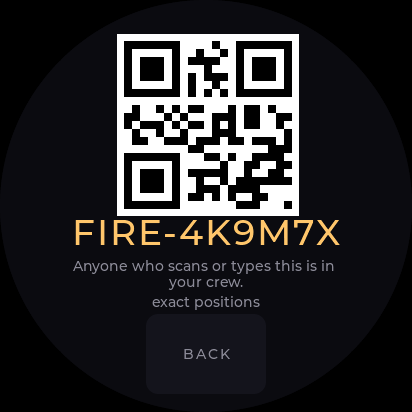
firmware/tests/golden/crew_show_code.png
