jakeholland/firefly/firmware/tests/golden/crew_show_code_none.png

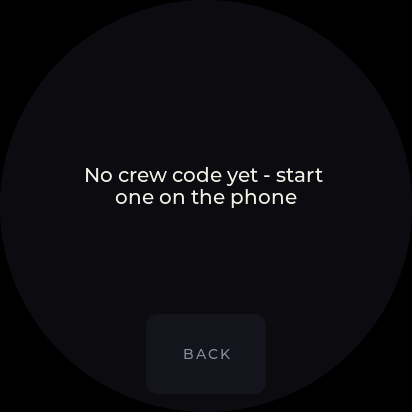
firmware/tests/golden/crew_show_code_none.png
