jakeholland/firefly/firmware/tests/golden/flare_takeover.png

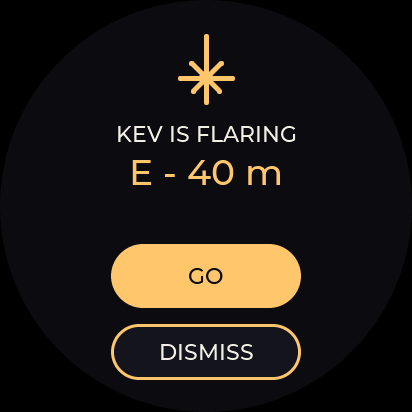
firmware/tests/golden/flare_takeover.png
