jakeholland/firefly/firmware/tests/golden/flaring_self.png

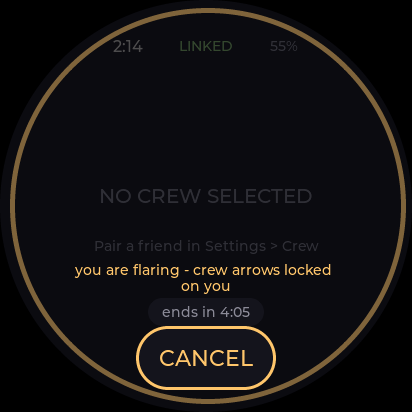
firmware/tests/golden/flaring_self.png
