jakeholland/firefly/firmware/tests/golden/inbox_all_stale.png

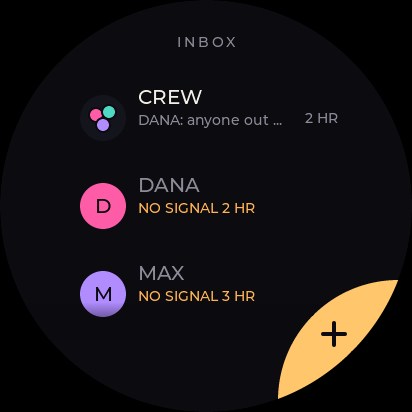
firmware/tests/golden/inbox_all_stale.png
