jakeholland/firefly/firmware/tests/golden/inbox_inbox.png

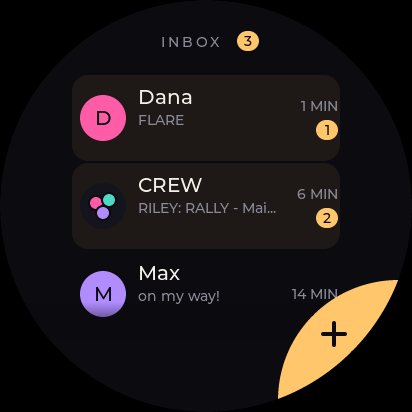
firmware/tests/golden/inbox_inbox.png
