jakeholland/firefly/firmware/tests/golden/inbox_picker.png

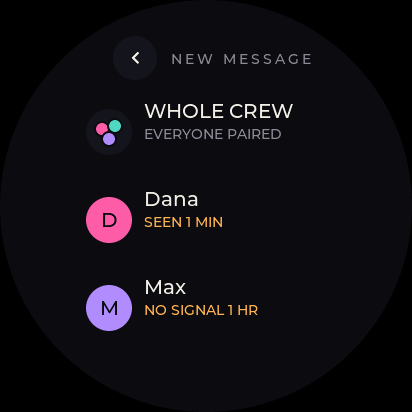
firmware/tests/golden/inbox_picker.png
