jakeholland/firefly/firmware/tests/golden/inbox_popup.png

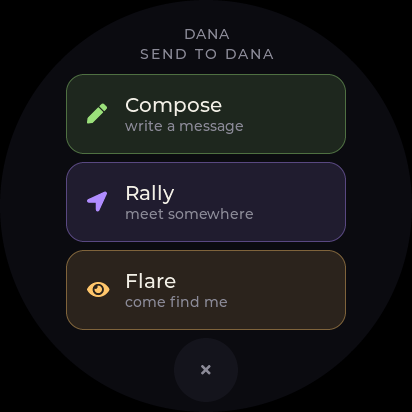
firmware/tests/golden/inbox_popup.png
