jakeholland/firefly/firmware/tests/golden/inbox_rally.png

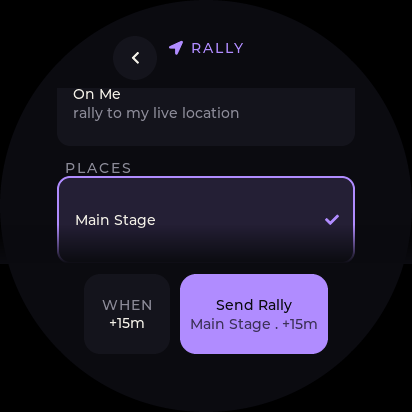
firmware/tests/golden/inbox_rally.png
