jakeholland/firefly/firmware/tests/golden/inbox_rally_nofix.png

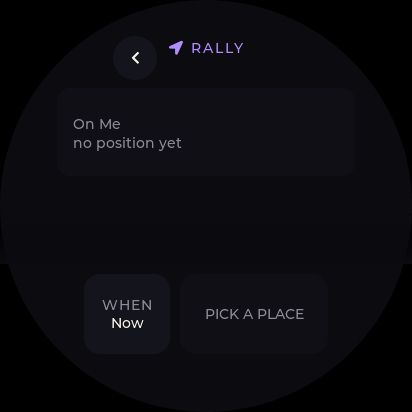
firmware/tests/golden/inbox_rally_nofix.png
