jakeholland/firefly/firmware/tests/golden/inbox_thread_crew.png

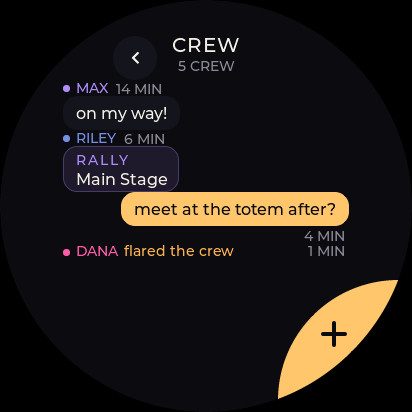
firmware/tests/golden/inbox_thread_crew.png
