jakeholland/firefly/firmware/tests/golden/inbox_thread_crew_long.png

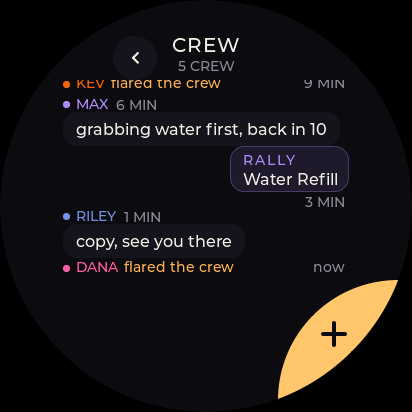
firmware/tests/golden/inbox_thread_crew_long.png
