jakeholland/firefly/firmware/tests/golden/inbox_thread_direct.png

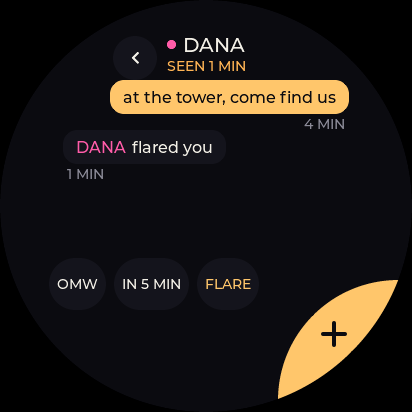
firmware/tests/golden/inbox_thread_direct.png
