jakeholland/firefly/firmware/tests/golden/inbox_thread_outbox_states.png

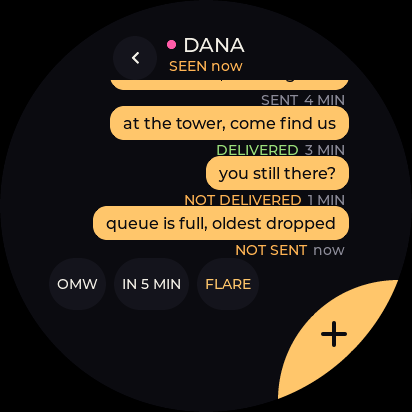
firmware/tests/golden/inbox_thread_outbox_states.png
