jakeholland/firefly/firmware/tests/golden/inbox_thread_short.png

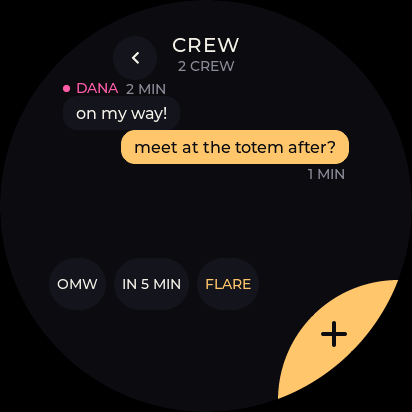
firmware/tests/golden/inbox_thread_short.png
