jakeholland/firefly/firmware/tests/golden/launcher.png

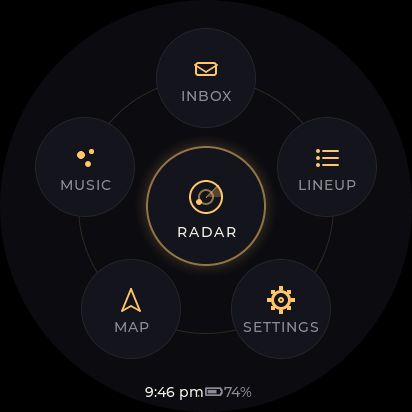
firmware/tests/golden/launcher.png
