jakeholland/firefly/firmware/tests/golden/lineup_empty.png

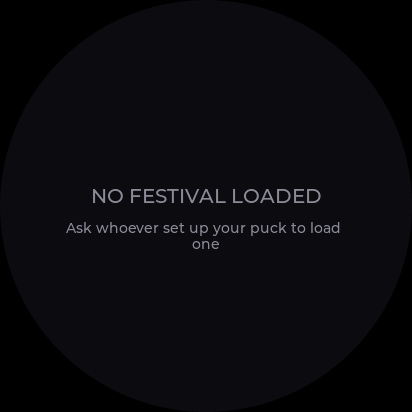
firmware/tests/golden/lineup_empty.png
