jakeholland/firefly/firmware/tests/golden/lineup_live.png

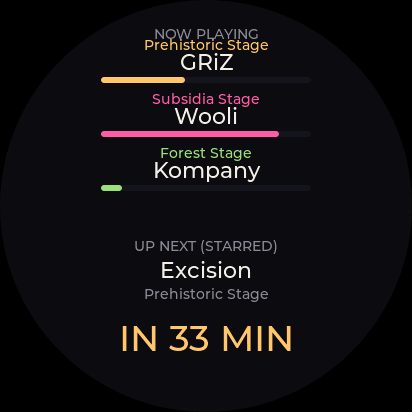
firmware/tests/golden/lineup_live.png
