jakeholland/firefly/firmware/tests/golden/lineup_live_unknown_end.png

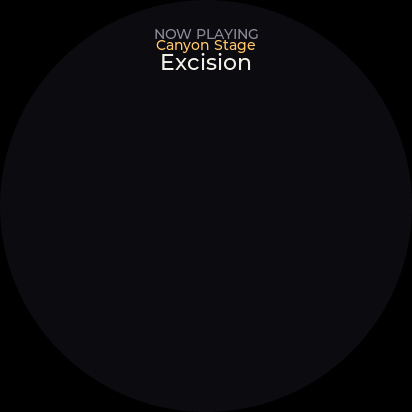
firmware/tests/golden/lineup_live_unknown_end.png
