jakeholland/firefly/firmware/tests/golden/lineup_mixed.png

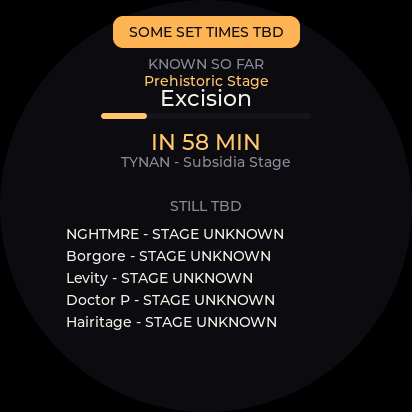
firmware/tests/golden/lineup_mixed.png
