jakeholland/firefly/firmware/tests/golden/lineup_nothing_live.png

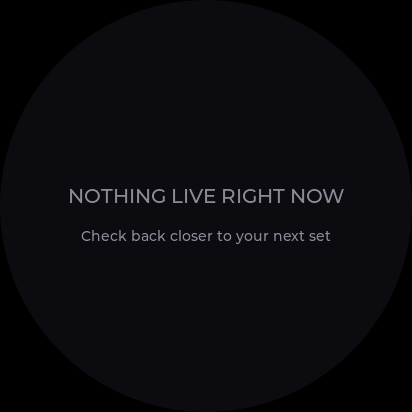
firmware/tests/golden/lineup_nothing_live.png
