jakeholland/firefly/firmware/tests/golden/lineup_tbd.png

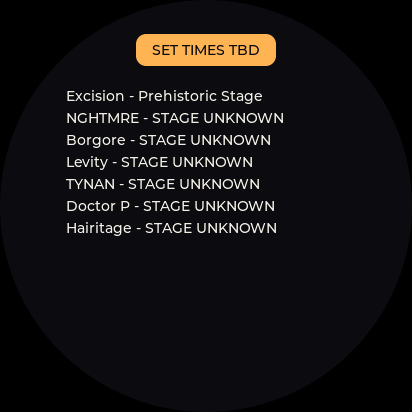
firmware/tests/golden/lineup_tbd.png
