jakeholland/firefly/firmware/tests/golden/map_clip_stress.png

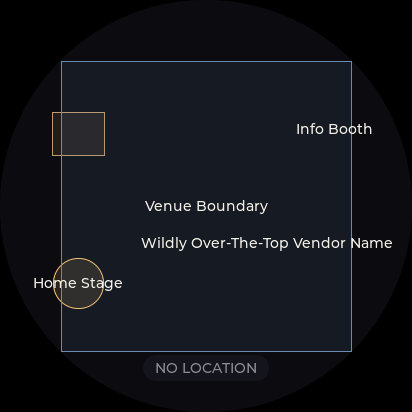
firmware/tests/golden/map_clip_stress.png
