jakeholland/firefly/firmware/tests/golden/map_concave.png

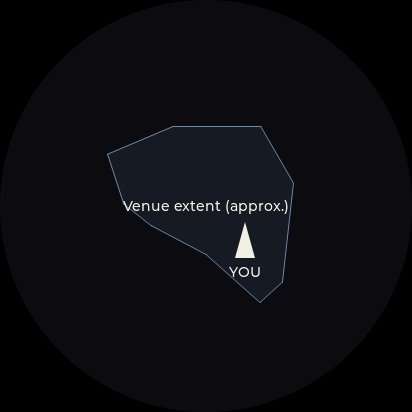
firmware/tests/golden/map_concave.png
