jakeholland/firefly/firmware/tests/golden/map_heading.png

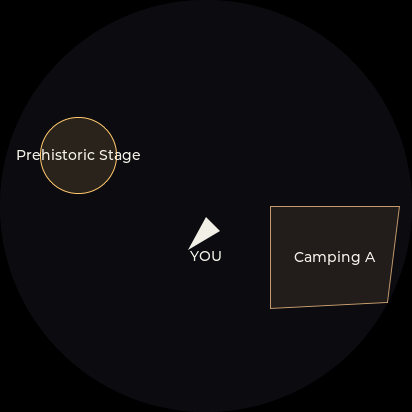
firmware/tests/golden/map_heading.png
