jakeholland/firefly/firmware/tests/golden/map_nofix.png

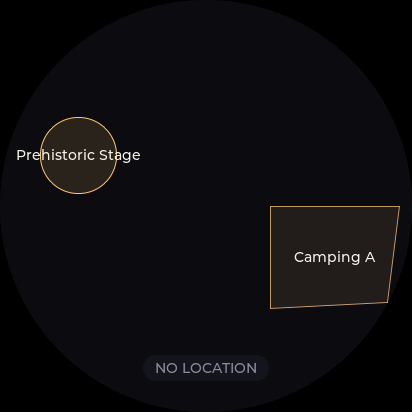
firmware/tests/golden/map_nofix.png
