jakeholland/firefly/firmware/tests/golden/map_real_lost_lands.png

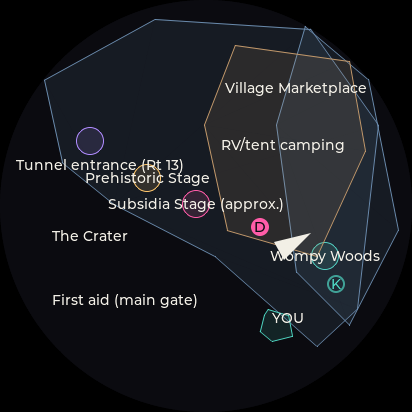
firmware/tests/golden/map_real_lost_lands.png
