jakeholland/firefly/firmware/tests/golden/map_traced.png

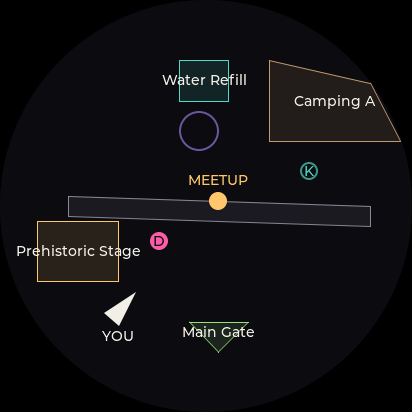
firmware/tests/golden/map_traced.png
