jakeholland/firefly/firmware/tests/golden/map_untraced.png

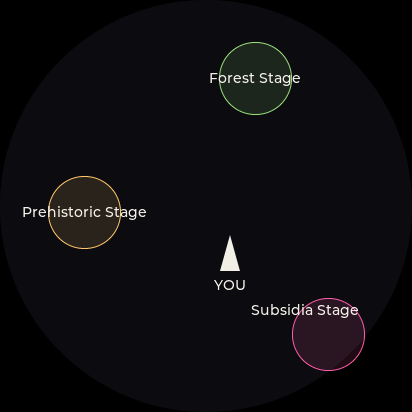
firmware/tests/golden/map_untraced.png
