jakeholland/firefly/firmware/tests/golden/music_swarm_imu.png

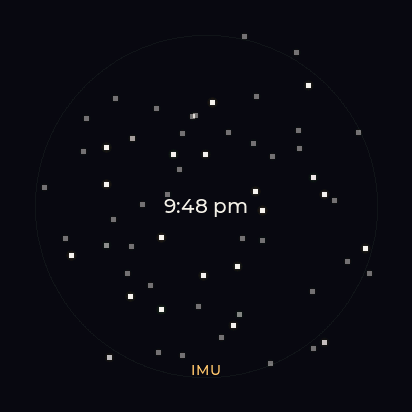
firmware/tests/golden/music_swarm_imu.png
