jakeholland/firefly/firmware/tests/golden/music_swarm_loud.png

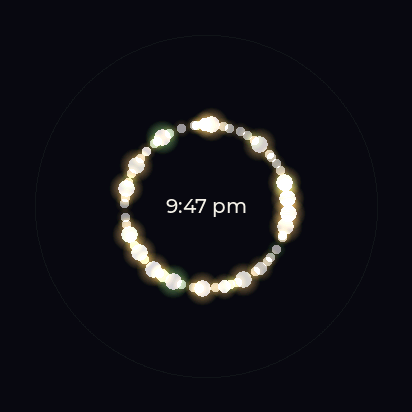
firmware/tests/golden/music_swarm_loud.png
