jakeholland/firefly/firmware/tests/golden/radar_close.png

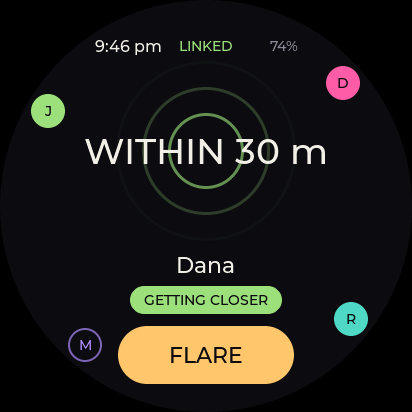
firmware/tests/golden/radar_close.png
