jakeholland/firefly/firmware/tests/golden/radar_cluster.png

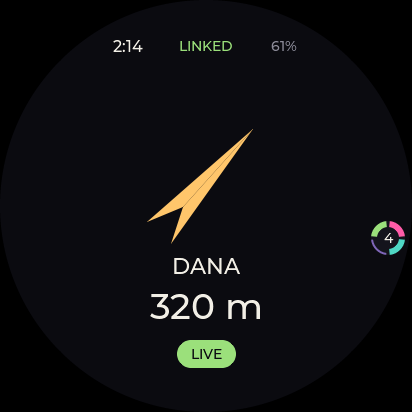
firmware/tests/golden/radar_cluster.png
