jakeholland/firefly/firmware/tests/golden/radar_cluster_stale.png

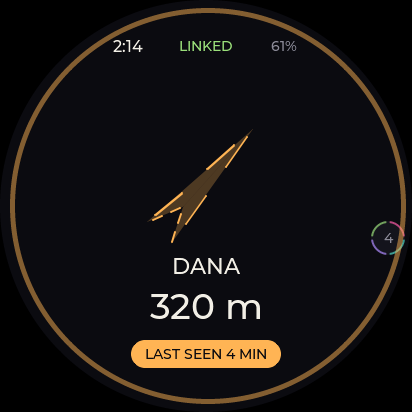
firmware/tests/golden/radar_cluster_stale.png
