jakeholland/firefly/firmware/tests/golden/radar_crew8.png

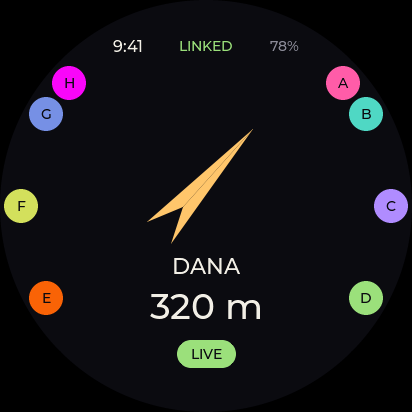
firmware/tests/golden/radar_crew8.png
