jakeholland/firefly/firmware/tests/golden/radar_flare_locked.png

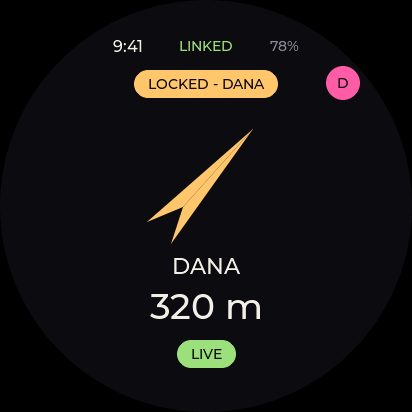
firmware/tests/golden/radar_flare_locked.png
