jakeholland/firefly/firmware/tests/golden/radar_flare_locked_north.png

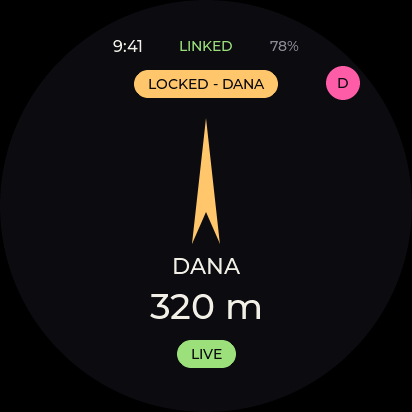
firmware/tests/golden/radar_flare_locked_north.png
