jakeholland/firefly/firmware/tests/golden/radar_imprecise.png

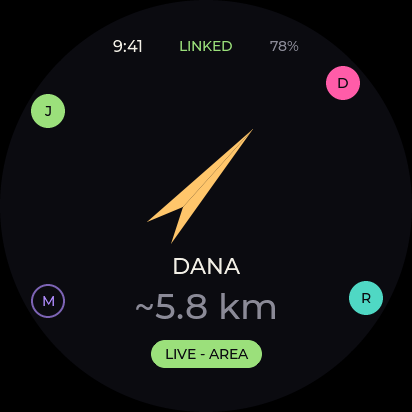
firmware/tests/golden/radar_imprecise.png
