jakeholland/firefly/firmware/tests/golden/radar_never.png

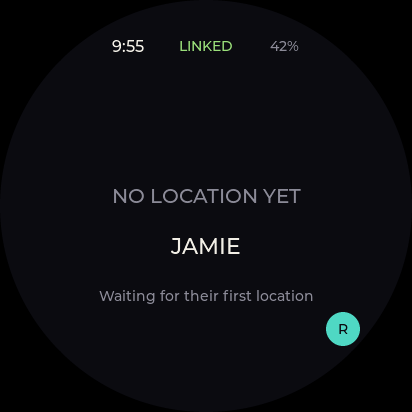
firmware/tests/golden/radar_never.png
