jakeholland/firefly/firmware/tests/golden/radar_nofix.png

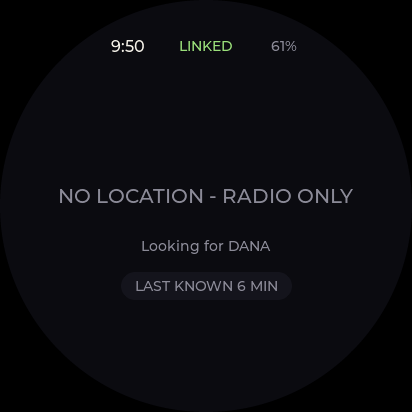
firmware/tests/golden/radar_nofix.png
