jakeholland/firefly/firmware/tests/golden/radar_nohdg.png

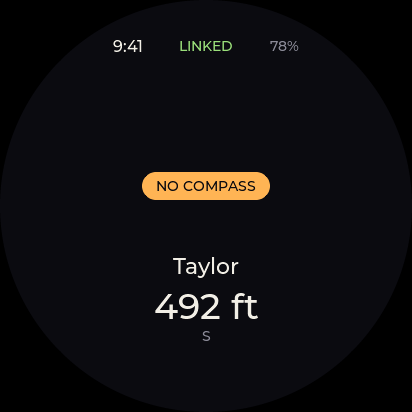
firmware/tests/golden/radar_nohdg.png
