jakeholland/firefly/firmware/tests/golden/radar_nohdg_stale.png

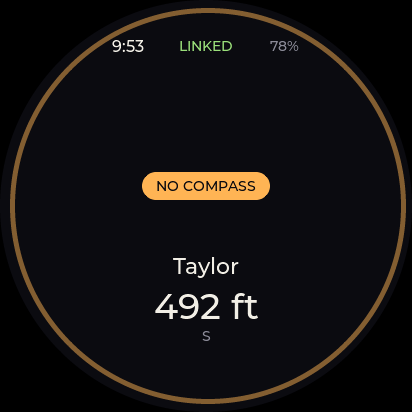
firmware/tests/golden/radar_nohdg_stale.png
