jakeholland/firefly/firmware/tests/golden/radar_nosel.png

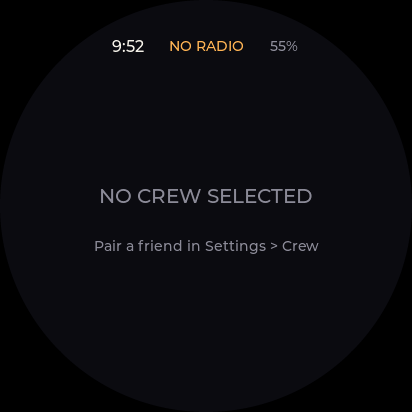
firmware/tests/golden/radar_nosel.png
