jakeholland/firefly/firmware/tests/golden/radar_place.png

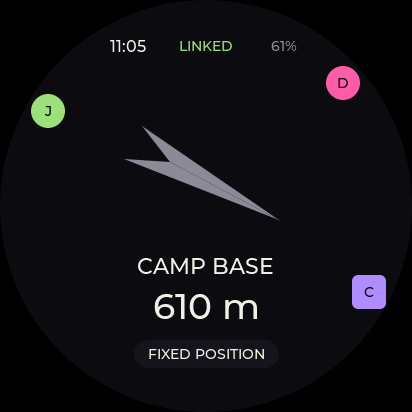
firmware/tests/golden/radar_place.png
