jakeholland/firefly/firmware/tests/golden/settings_brightness.png

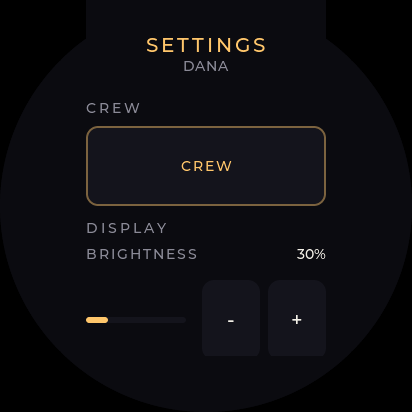
firmware/tests/golden/settings_brightness.png
