jakeholland/firefly/firmware/tests/golden/settings_diag_full.png

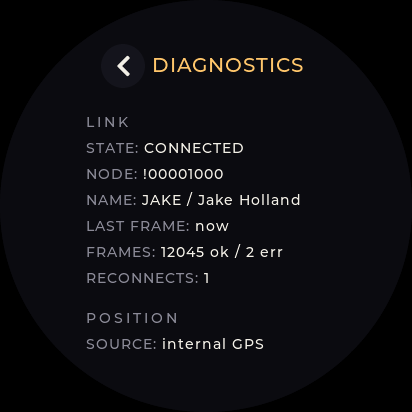
firmware/tests/golden/settings_diag_full.png
