jakeholland/firefly/firmware/tests/golden/settings_diag_unknown.png

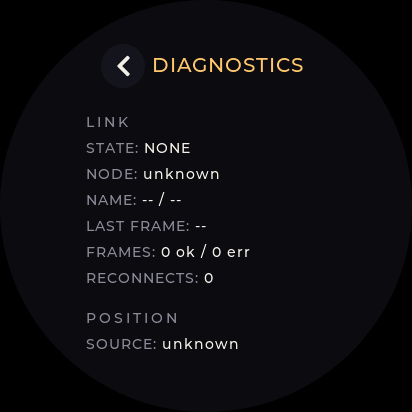
firmware/tests/golden/settings_diag_unknown.png
