jakeholland/firefly/firmware/tests/golden/settings_name_confirmed.png

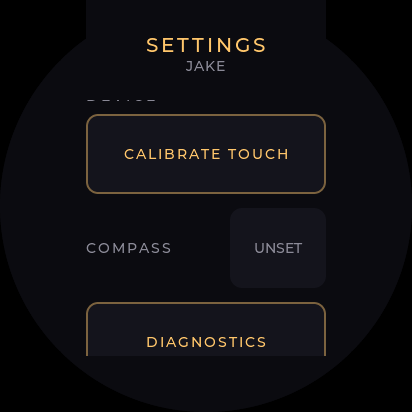
firmware/tests/golden/settings_name_confirmed.png
