jakeholland/firefly/firmware/tests/golden/settings_name_edit.png

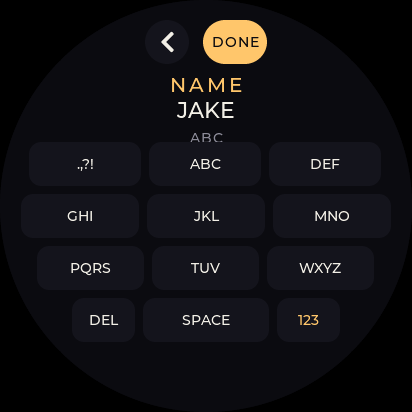
firmware/tests/golden/settings_name_edit.png
