jakeholland/firefly/firmware/tests/golden/settings_scrolled_bottom.png

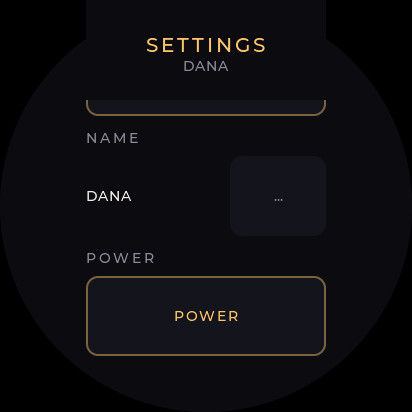
firmware/tests/golden/settings_scrolled_bottom.png
