jakeholland/firefly/firmware/tests/golden/settings_scrolled_mid.png

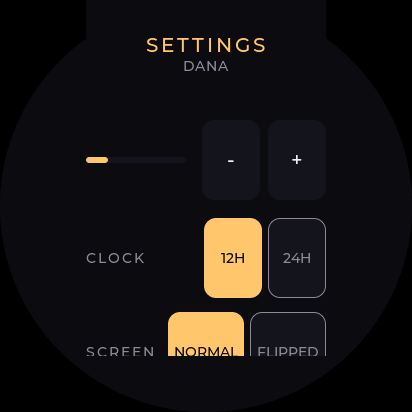
firmware/tests/golden/settings_scrolled_mid.png
