jakeholland/firefly/firmware/targets/esp32s3/components/ff_compass/ff_compass.c

/**
 * ff_compass.c — S15: GY-273 magnetometer + onboard QMI8658 accel,
 * tilt-compensated heading via ff_geo_heading_deg. See ff_compass.h for
 * the full hardware contract, the honesty contract, and the
 * calibration seam.
 */
#include "ff_compass.h"

#include <stdint.h>
#include <string.h>

#include "esp_log.h"
#include "esp_timer.h" /* esp_timer_get_time() — invalid-data/re-init timing, matching ff_display.c/ff_power.c's own now_ms convention */
#include "ff_display.h" /* ff_display_i2c_bus_lock/unlock — the touch-vs-compass shared I2C bus mutex, see that function's doc comment */
#include "freertos/FreeRTOS.h"
#include "freertos/task.h"

static const char *TAG = "ff_compass";

/* I2C transaction timeout for every read/write below. This runs in the
 * main render-loop task (app_main.c's FF_COMPASS_SAMPLE_PERIOD_MS tick,
 * 10 Hz) on the SAME i2c_master_bus_handle_t the SPD2010 touch driver
 * uses (ff_display_i2c_bus()) — a transaction that blocks here also
 * blocks touch reads on that shared handle. A successful transaction
 * at 400 kHz for a handful of bytes completes in well under 1 ms, so
 * there is no happy-path cost to keeping this short; a genuinely
 * wedged bus degrades to the -1 "unknown" sentinel quickly instead of
 * costing up to 2x this driver's own sample period (and stalling
 * touch along with it) on every affected tick. PR #212 review finding
 * #1: was 100 ms. */
#define FF_COMPASS_I2C_TIMEOUT_MS 20

/* Timeout for acquiring ff_display's shared I2C bus lock
 * (ff_display_i2c_bus_lock, ff_display.h) before this sample's mag+imu
 * reads — see that function's doc comment for the touch-vs-compass
 * interleaving bug this closes. Same 20 ms budget as
 * FF_COMPASS_I2C_TIMEOUT_MS just above, for the same reason: the
 * touch driver's own multi-transaction read normally finishes in a
 * fraction of a millisecond, so there is no happy-path cost, and a
 * genuinely wedged touch path degrades THIS sample to -1 quickly
 * instead of blocking the main render-loop task. */
#define FF_COMPASS_I2C_BUS_LOCK_TIMEOUT_MS 20

/* Per-device SCL ceiling handed to i2c_master_bus_add_device — a cap on
 * THIS device's own transactions, not a bus reconfigure (the bus itself
 * was already brought up by ff_display_expander_init at its own
 * FF_I2C_HZ, 400000). All three candidate chips here are rated for
 * standard/fast-mode I2C well above this. */
#define FF_COMPASS_I2C_HZ 400000u

/* =====================================================================
 * QMI8658 (onboard IMU) — register map + bring-up bytes, cited from
 * Waveshare's own ESP-IDF 5.3.2 reference demo for this exact board:
 * https://github.com/yaosy1997/ESP32-S3-Touch-LCD-1.46-Test/blob/main/main/QMI8658/QMI8658.c
 * and QMI8658.h (register addresses, WHO_AM_I value, and the bit-layout
 * #defines the CTRL2 byte below is computed from).
 * ===================================================================== */
#define FF_QMI8658_ADDR_PRIMARY 0x6B
#define FF_QMI8658_ADDR_ALT 0x6A

#define FF_QMI8658_REG_WHO_AM_I 0x00
#define FF_QMI8658_WHO_AM_I_VAL 0x05
#define FF_QMI8658_REG_CTRL1 0x02
#define FF_QMI8658_REG_CTRL2 0x03
#define FF_QMI8658_REG_CTRL7 0x08
#define FF_QMI8658_REG_STATUS0 0x2E /* Output Data Status Register, Table 27 */
#define FF_QMI8658_REG_RESET 0x60   /* Soft Reset Register, Table 31 */
#define FF_QMI8658_REG_AX_L 0x35 /* 6-byte burst: AX_L,AX_H,AY_L,AY_H,AZ_L,AZ_H */

/* Second-board bring-up hardening (2026-09-07 bench evidence: a factory-
 * fresh QMI8658 identified correctly at WHO_AM_I but then produced
 * 0x8000/0x7FFF sentinel accel samples forever — the accel engine never
 * actually started, even though every bring-up write returned ESP_OK).
 * Register facts below are cited from the QST QMI8658C datasheet
 * (Rev 0.9, "© 2022 QST Corporation", fetched 2026-09-07 via
 * https://files.waveshare.com/wiki/common/QMI8658A.pdf — Waveshare's own
 * mirror of the part datasheet for this exact board):
 *
 * - "RESET  w  96  0x60  Soft Reset Register - Write 0xB0 to this
 *   register from any modes, will trigger the sensor reset process
 *   immediately." (Table 31, section 5.8)
 * - "STATUS0  r  46  0x2E  Output Data Over Run and Data Availability."
 *   (Table 27), bit-field table: bit0 aDA "Accelerometer new data
 *   available: 0 = No updates since last read, 1 = New data available."
 *   (section on STATUS0, same page)
 * - Section 7.1/7.2 ("General Mode Transitioning"/"Transition Times"):
 *   "Upon exiting the No Power state ... or exiting a Software Reset
 *   state, the part will enter the Power-On Default state" — System Turn
 *   On Time t0 is typ. 150 ms (Table 7 note 8), then Accel Turn On Time
 *   adds t2 (typ. 3 ms) + t5 (3/ODR). This driver does NOT block boot for
 *   that full worst-case sum: FF_QMI8658_RESET_SETTLE_MS below only
 *   guarantees the RESET register's own hardware-reset window has
 *   cleared before the bring-up writes land (matching this task's
 *   bench-verified minimum); FF_QMI8658_DATA_READY_TIMEOUT_MS's STATUS0
 *   poll is what actually gates the first trusted read, so it — not a
 *   fixed sleep — absorbs whatever the real accel turn-on time is on a
 *   given part.
 */
#define FF_QMI8658_RESET_VAL 0xB0
#define FF_QMI8658_RESET_SETTLE_MS 15 /* >= the reset-to-command-acceptance minimum this task specifies */
#define FF_QMI8658_STATUS0_ADA_BIT 0x01u /* STATUS0 bit0 — accel new-data-available */
#define FF_QMI8658_DATA_READY_POLL_MS 5
#define FF_QMI8658_DATA_READY_TIMEOUT_MS 200 /* generous bound over the datasheet's typ. accel turn-on time */

/* Runtime data validation + rate-limited re-init (see this file's
 * ff_compass_imu_validate/ff_compass_imu_maybe_reinit). A raw axis
 * sitting exactly at the int16 rail (0x8000 or 0x7FFF) is QMI8658's own
 * ADC/analog-engine sentinel/saturation pattern, never a real sample;
 * the magnitude band below is a plausibility check on top of that,
 * bounding "gravity plus whatever tilt+noise a handheld puck sees" at
 * the CTRL2-configured ±4g range (8192 LSB/g, QMI8658C datasheet Table 7
 * "Sensitivity Scale Factor" row "±4g -> 8,192"). 0.3g/3g are this
 * task's own thresholds, not a datasheet value. */
#define FF_QMI8658_ACCEL_SENTINEL_MIN ((int16_t)-32768) /* 0x8000 */
#define FF_QMI8658_ACCEL_SENTINEL_MAX ((int16_t)32767)  /* 0x7FFF */
#define FF_QMI8658_ACCEL_LSB_PER_G 8192.0f               /* at CTRL2's configured ACC_RANGE_4G */
#define FF_QMI8658_ACCEL_MIN_G 0.3f
#define FF_QMI8658_ACCEL_MAX_G 3.0f

#define FF_QMI8658_REINIT_INVALID_MS 2000u  /* re-run bring-up once invalid data persists this long */
#define FF_QMI8658_REINIT_RATE_LIMIT_MS 5000u /* never attempt a re-init more often than this */
#define FF_QMI8658_REINIT_MAX_ATTEMPTS 5      /* give up after this many consecutive failed re-inits */

/* CTRL1 bit6 = address auto-increment, needed for the 6-byte AX_L..AZ_H
 * burst read below. Cited verbatim from the reference driver's own
 * init: `ctrl1 |= 0x40`. */
#define FF_QMI8658_CTRL1_VAL 0x40

/* CTRL2 = (ASCALE << QMI8658_ASCALE_OFFSET) | AODR, per the reference
 * header's own bit layout (QMI8658_ASCALE_OFFSET=4, ACC_RANGE_4G=0x1,
 * acc_odr_norm_30=0x8): (0x1 << 4) | 0x8 = 0x18. 30 Hz comfortably
 * covers this driver's own 10 Hz poll rate (app_main.c's
 * FF_COMPASS_SAMPLE_PERIOD_MS) while staying in the chip's "normal"
 * (not low-power) accel mode family. */
#define FF_QMI8658_CTRL2_VAL 0x18

/* CTRL7 = aEN | sys_hs. The reference driver writes 0x43 (aEN(bit0) |
 * gEN(bit1) | sys_hs(bit6)) because its own demo also runs the gyro;
 * ff_geo_heading_deg takes mag + accel only, so this driver has no use
 * for gyro data and leaves gEN off. bit6 (sys_hs, "high-speed internal
 * clock" vs. an ODR-derived clock per QST's own datasheet) is NOT
 * gyro-related, so it is kept rather than dropped along with gEN —
 * matching the reference driver's own clock source rather than
 * introducing an unverified deviation on a path this PR's own bench
 * note already flags as not independently verified (PR #212 review
 * finding #3). 0x43 & ~0x02 (gEN) = 0x41. */
#define FF_QMI8658_CTRL7_VAL 0x41

/* =====================================================================
 * QMC5883L — the far more common chip on a GY-273 board even when
 * silkscreened "HMC5883L". Register map + CTRL1 byte per the QMC5883L
 * datasheet ("Register 09H — Control Register 1", "Register 0BH —
 * SET/RESET Period", "Register 0DH — Chip ID").
 * ===================================================================== */
#define FF_QMC5883L_ADDR 0x0D

#define FF_QMC5883L_REG_DATA 0x00 /* 6-byte burst: XL,XH,YL,YH,ZL,ZH */
#define FF_QMC5883L_REG_SETRESET 0x0B
#define FF_QMC5883L_REG_CTRL1 0x09
#define FF_QMC5883L_REG_CHIPID 0x0D

#define FF_QMC5883L_CHIPID_VAL 0xFF
#define FF_QMC5883L_SETRESET_VAL 0x01 /* datasheet's own fixed recommended value */

/* CTRL1 (0x09) field layout, per the datasheet: OSR[7:6] | RNG[5:4] |
 * ODR[3:2] | MODE[1:0]. OSR=00 (512), RNG=00 (2 Gauss), ODR=00 (10 Hz),
 * MODE=01 (continuous) -> 0b00000001. */
#define FF_QMC5883L_CTRL1_VAL 0x01

/* =====================================================================
 * HMC5883L — the genuine part some GY-273 boards actually carry.
 * Register map + CRA/CRB/mode bytes per the HMC5883L datasheet
 * ("Configuration Register A/B", "Mode Register", "Identification
 * Register A/B/C", "Data Output X/Y/Z Registers").
 * ===================================================================== */
#define FF_HMC5883L_ADDR 0x1E

#define FF_HMC5883L_REG_CRA 0x00
#define FF_HMC5883L_REG_CRB 0x01
#define FF_HMC5883L_REG_MODE 0x02
#define FF_HMC5883L_REG_DATA 0x03 /* X_MSB,X_LSB,Z_MSB,Z_LSB,Y_MSB,Y_LSB — datasheet's own X,Z,Y order, NOT X,Y,Z */
#define FF_HMC5883L_REG_ID_A 0x0A /* ID A/B/C read back ASCII "H43" */

#define FF_HMC5883L_CRA_VAL 0x70  /* 8-sample average, 15 Hz ODR, normal measurement — datasheet default */
#define FF_HMC5883L_CRB_VAL 0x20  /* GN2:0=001, +-1.3 Ga, 1090 LSB/Gauss -- true POR default (PR #212 review: was 0xA0/+-4.7 Ga/390 LSB/Gauss, which is GN2:0=101, not the default, and throws away resolution Earth's field (~0.25-0.65 Ga) doesn't need) */
#define FF_HMC5883L_MODE_VAL 0x00 /* continuous-measurement mode */

/* =====================================================================
 * QMC5883P — QST's successor to the QMC5883L, confirmed on the
 * coordinator's own bench (2026-09-05, real puck, GY-273 module wired
 * and powered): the console `i2c` scan shows a device at 0x2C that is
 * neither the QMC5883L (0x0D) nor HMC5883L (0x1E) this driver already
 * probes. Register map, bit layout, and the two application-note bytes
 * (0x29 axis-sign, the specific CTRL1/CTRL2 values below) are all
 * cited from the QMC5883P datasheet, QST document #13-52-19 Rev A
 * (https://www.icbase.com/File/news/download/QMC5883P_Datasheet.pdf,
 * fetched 2026-09-05) — table/section numbers below refer to that PDF.
 * ===================================================================== */
#define FF_QMC5883P_ADDR 0x2C /* datasheet section 5.4: "The default I2C address for QMC5883P is 2CH" */

#define FF_QMC5883P_REG_CHIPID 0x00 /* Table 14/15: read-only, POR default 0x80 (section 9.2.1) */
#define FF_QMC5883P_REG_DATA 0x01   /* Table 14/15: 6-byte burst XL,XH,YL,YH,ZL,ZH, little-endian per axis, 2's complement */
#define FF_QMC5883P_REG_STATUS 0x09 /* Table 16: bit0 DRDY, bit1 OVFL, bits 7:2 RFU — read only */
#define FF_QMC5883P_REG_CTRL1 0x0A  /* Table 17: OSR2[7:6] | OSR1[5:4] | ODR[3:2] | MODE[1:0] */
#define FF_QMC5883P_REG_CTRL2 0x0B  /* Table 18: SOFT_RST[7] | SELF_TEST[6] | RFU[5:4] | RNG[3:2] | SET/RESET_MODE[1:0] */
#define FF_QMC5883P_REG_SIGN 0x29   /* NOT in the register map table (9.1) — an undocumented-but-load-bearing register the datasheet's own "Application Examples" (7.1-7.3) write before every mode setup: "Write Register 29H by 0x06 (Define the sign for X Y and Z axis)" */

#define FF_QMC5883P_CHIPID_VAL 0x80

/* CTRL1 = OSR2<<6 | OSR1<<4 | ODR<<2 | MODE (Table 17's own field layout).
 * Values picked per this task's spec, each a literal Table 17 column:
 *   OSR2 = 8   -> column "11" (Table 17: 00=1,01=2,10=4,11=8)        -> 0b11 << 6 = 0xC0
 *   OSR1 = 8   -> column "00" (Table 17: 00=8,01=4,10=2,11=1)        -> 0b00 << 4 = 0x00
 *   ODR  = 50Hz-> column "01" (Table 17: 00=10Hz,01=50Hz,10=100Hz,11=200Hz) -> 0b01 << 2 = 0x04
 *   MODE = continuous -> column "11" (Table 17: 00=Suspend,01=Normal,10=Single,11=Continuous) -> 0b11 = 0x03
 * CTRL1 = 0xC0 | 0x00 | 0x04 | 0x03 = 0xC7. This driver polls at 10 Hz
 * (app_main.c's FF_COMPASS_SAMPLE_PERIOD_MS); 50 Hz ODR comfortably
 * covers that with headroom, matching the other two parts' own
 * "sample faster than we poll" margin. */
#define FF_QMC5883P_CTRL1_VAL 0xC7

/* CTRL2 = SOFT_RST<<7 | SELF_TEST<<6 | RNG<<2 | SET/RESET_MODE (Table
 * 18's own field layout, bits 5:4 RFU).
 *   RNG            = 2G  -> column "11" (Table 18: 00=30G,01=12G,10=8G,11=2G) -> 0b11 << 2 = 0x0C
 *   SET/RESET_MODE = on  -> column "00" ("Set and reset on")                 -> 0b00 = 0x00
 * CTRL2 = 0x0C | 0x00 = 0x0C (SOFT_RST and SELF_TEST both 0 for normal
 * operation). Soft reset itself is the datasheet's own "Soft Reset
 * Example" (7.6): write CTRL2 = 0x80 (SOFT_RST bit alone) BEFORE this
 * configuring write. */
#define FF_QMC5883P_CTRL2_VAL 0x0C
#define FF_QMC5883P_SOFT_RST_VAL 0x80 /* datasheet 7.6: "Write Register 0BH by 0x80" */
#define FF_QMC5883P_SIGN_VAL 0x06     /* datasheet 7.1/7.2/7.3: "Write Register 29H by 0x06" — verified in this datasheet's own worked examples, not just an app note */

/* Sensitivity at the 2G range configured above: 15000 LSB/Gauss
 * (datasheet Table 2, "Sensitivity", row "Field Range = ±2G"). Not
 * used in any arithmetic here — ff_geo_heading_deg's atan2 is
 * scale-invariant across all three magnetometers — kept only so a
 * reader has the same units reference the QMC5883L/HMC5883L sections
 * above document for their own ranges. */

/* =====================================================================
 * Axis mapping: sensor frame -> board frame (ff_geo.h's own convention:
 * +x right, +y forward/"top of puck", +z up out of the screen;
 * stationary level accel reads ~(0,0,+1g)). ONE table, two small
 * per-axis (source, sign) pairs below — flip a _SIGN or swap a _SRC
 * here to correct after a bench check; nothing else in this file
 * encodes either mapping.
 *
 * Magnetometer (GY-273, QMC5883L/HMC5883L): ASSUMED mounting,
 * unverified on real hardware — the module sits flat against the case
 * wall at the lanyard end, silkscreen component-side facing the same
 * way as the main board's (both toward the glass), with the module's
 * printed +X arrow pointing toward the puck's own +y (away from the
 * lanyard, toward the top of the puck as worn) and its +Y arrow toward
 * the puck's own -x. That mounting is a 90-degree rotation about the
 * shared +z axis: mag +x -> board +y, mag +y -> board -x, mag +z ->
 * board +z (both boards' components face the glass, so no z-flip).
 * VERIFY ON BENCH — if the Radar arrow turns the wrong way (or 90/180
 * degrees off) when the puck is rotated flat, this is the first place
 * to look; see this driver's introducing PR body for the bench
 * procedure.
 *
 * Magnetometer (GY-273, QMC5883P): its OWN row, `FF_MAG_QMC5883P_BOARD_*`
 * below — NOT the same table as the L/HMC pair above. QST's own
 * Package 3-D View (QMC5883P datasheet section 3.1) draws this part's
 * +X/+Y/+Z arrows in a different arrangement than the L's package
 * marking, and since a real bench GY-273 clone board is not guaranteed
 * to reprint its own silkscreen consistently between the two chip
 * options it ships, this driver does NOT assume the P's mounting
 * produces the same board-frame result as the L/HMC row.
 *
 * 2026-09-10 (hardware/case pass 10, REDONE same day): the module's
 * mounting CHANGED — the coordinator rejected the first pass-10 fix (a
 * fenced pocket standing on edge at the lanyard end) for putting a boxy
 * bump on the case's outer silhouette. It now hangs COMPONENTS-DOWN from
 * the TOP's own inner ceiling, directly above the GPS patch antenna's
 * frame (no pocket, no brow, no outer-wall contact at all) — see
 * hardware/case/README.md's pass-10 section for the placement/verify
 * numbers.
 *
 * 2026-09-11 (hardware/case pass 11, defect 2): the mount's ORIENTATION
 * FLIPPED — Jake's review of the pass-10b renders found the header/wire
 * edge pointing toward the display end, with the fence only ~1mm from
 * the window bore's own true rim there and the wires exiting straight
 * into that gap. The mount is now shifted and re-oriented (see
 * `firefly_case.py`'s `mag_module` orientation comment and README's
 * pass-11 section for the full derivation) so the header/wire edge
 * points toward the LANYARD end instead, with >=4mm clear of both the
 * window bore and the display module's own back-side bbox. The PCB-frame
 * mapping below is UPDATED for this flip (local +x now maps to puck -y,
 * not +y as pass 10 had it) — the row's numeric axis-source/sign values
 * are still an OLD guess (from before EITHER real mounting existed) and
 * remain NOT valid for either mounting; they are left in place only so
 * the driver keeps building, and MUST be re-derived on the bench (or
 * from the QMC5883P's own datasheet Package 3-D View) before trusting a
 * single heading reading. What IS fixed by the mount's own geometry is
 * the module's PCB-frame mapping into the puck's own (x,y,z) — i.e.
 * which physical edge of the module points which way, NOT yet which
 * sensor axis that is (that still needs the chip's silkscreen/datasheet
 * orientation on top of this):
 *   - module's long PCB edge, HEADER side (local +x, 18.6mm axis)
 *     -> puck -y (pass 11: was +y — toward the LANYARD end now, the
 *     short wire run to the back header's SDA/SCL/3V3/G no longer
 *     points at the display/window)
 *   - module's long PCB edge, MOUNTING-HOLE side (local -x)
 *     -> puck +y (pass 11: was -y — toward the display end now; both
 *     ceiling pegs are here)
 *   - module's short PCB edge, local +y -> puck +x
 *   - module's short PCB edge, local -y -> puck -x
 *     (this axis is an arbitrary handedness choice, UNCHANGED by pass
 *     11 — the mount places both pegs and both rest pads by explicit
 *     (x,y) pairs, not by a directional rule, so it carries no
 *     functional constraint)
 *   - module's COMPONENT/sensor face (local +z) -> puck -z (DOWN,
 *     toward the GPS patch/Bottom — the module is mounted
 *     components-down, hanging off two Ø2.7 ceiling pegs + two rest
 *     pads; UNCHANGED by pass 11)
 *   - module's SOLDER/header face (local -z) -> puck +z (UP, toward
 *     the Top's ceiling — both mounting holes share local x=-7.21, i.e.
 *     the same local z=0 plane, so both pegs land flush against the
 *     same ceiling standoff; UNCHANGED by pass 11)
 * Bench procedure: with this mapping known, place the sensor flat on a
 * known heading, read raw XYZ, and solve for (src, sign) per axis the
 * same way the L/HMC row above was derived — do NOT assume the values
 * below are a safe starting guess anymore, the whole mounting geometry
 * changed. Kept as an independently-editable row so this bench check
 * (docs/hardware/comms-brain.md's "Compass" section) can correct it on
 * its own without touching the L/HMC mapping. VERIFY ON BENCH,
 * same procedure as above, once a QMC5883P board is on hand.
 *
 * IMU (onboard QMI8658): BENCH-VERIFIED 2026-09-05 to be mounted
 * upside-down relative to the board frame — the identity mapping this
 * row used to carry (on the working assumption that the IMU's
 * silkscreen axes already match the board's own, since it's soldered
 * to the SAME rigid PCB as the screen) produced a rejected heading on
 * real hardware. With the puck lying flat, face-up, raw QMI8658 accel
 * read (-1721, -260, -7877); under the (then-)identity map that lands
 * almost entirely on board -z (~-1g), which `ff_geo_heading_deg` reads
 * as a ~166 degree tilt — past the tilt-reject threshold, so every
 * sample was thrown out (heading -1 always). Flipping the IMU's X and
 * Z signs (Y unchanged) gives accel (1714, -257, 7862) -> board +z ~=
 * +1g, level, and a steady heading of 104 degrees. Flipping X together
 * with Z keeps the frame right-handed: this is a 180-degree rotation
 * about the board's own +y axis, i.e. the chip is effectively soldered
 * upside-down relative to ff_geo.h's board frame (+x right, +y
 * forward/top of puck, +z up out of the screen).
 * TILT CHECK STILL PENDING: only the face-up/face-down (z) sense has
 * bench evidence so far. The IMU's x/y sense under an actual physical
 * tilt (nose up/down, left/right roll) has NOT been separately
 * verified — if tilt-compensation looks inverted or rotated 90 degrees
 * when the puck is tipped, check FF_IMU_BOARD_X_SRC/Y_SRC (axis swap)
 * here before assuming the sign is wrong again.
 */
typedef enum { FF_AXIS_X = 0, FF_AXIS_Y = 1, FF_AXIS_Z = 2 } ff_compass_axis_t;

#define FF_MAG_BOARD_X_SRC FF_AXIS_Y
#define FF_MAG_BOARD_X_SIGN ((int8_t)-1)
#define FF_MAG_BOARD_Y_SRC FF_AXIS_X
#define FF_MAG_BOARD_Y_SIGN ((int8_t)1)
#define FF_MAG_BOARD_Z_SRC FF_AXIS_Z
#define FF_MAG_BOARD_Z_SIGN ((int8_t)1)

/* QMC5883P's own row — see this block's comment above for why it is
 * separate from FF_MAG_BOARD_* rather than shared with it. */
#define FF_MAG_QMC5883P_BOARD_X_SRC FF_AXIS_Y
#define FF_MAG_QMC5883P_BOARD_X_SIGN ((int8_t)-1)
#define FF_MAG_QMC5883P_BOARD_Y_SRC FF_AXIS_X
#define FF_MAG_QMC5883P_BOARD_Y_SIGN ((int8_t)1)
#define FF_MAG_QMC5883P_BOARD_Z_SRC FF_AXIS_Z
#define FF_MAG_QMC5883P_BOARD_Z_SIGN ((int8_t)1)

#define FF_IMU_BOARD_X_SRC FF_AXIS_X
#define FF_IMU_BOARD_X_SIGN ((int8_t)-1)
#define FF_IMU_BOARD_Y_SRC FF_AXIS_Y
#define FF_IMU_BOARD_Y_SIGN ((int8_t)1)
#define FF_IMU_BOARD_Z_SRC FF_AXIS_Z
#define FF_IMU_BOARD_Z_SIGN ((int8_t)-1)

static float ff_compass_axis_get(ff_vec3_t v, ff_compass_axis_t a)
{
    switch (a) {
    case FF_AXIS_X: return v.x;
    case FF_AXIS_Y: return v.y;
    case FF_AXIS_Z: return v.z;
    }
    return 0.0f; /* unreachable for a value from this file's own enum, but -Werror wants a return on every path */
}

static ff_vec3_t ff_compass_remap(ff_vec3_t raw, ff_compass_axis_t xs, int8_t xsign, ff_compass_axis_t ys,
                                   int8_t ysign, ff_compass_axis_t zs, int8_t zsign)
{
    ff_vec3_t out;
    out.x = (float)xsign * ff_compass_axis_get(raw, xs);
    out.y = (float)ysign * ff_compass_axis_get(raw, ys);
    out.z = (float)zsign * ff_compass_axis_get(raw, zs);
    return out;
}

/* =====================================================================
 * State — module-private, mirroring ff_power.c's own file-scope-static
 * discipline for HAL handles.
 * ===================================================================== */
static i2c_master_dev_handle_t s_mag_dev;
static i2c_master_dev_handle_t s_imu_dev;
static ff_compass_mag_kind_t s_mag_kind = FF_COMPASS_MAG_NONE;
static bool s_imu_present;

/* imu=ok|no-data|absent (ff_compass.h) — ABSENT until/unless
 * ff_compass_probe_imu identifies the chip at all; NO_DATA once
 * identified and configured but every accel sample so far has failed
 * ff_compass_imu_validate (the second-board defect this driver now
 * detects instead of silently fabricating a level reading forever); OK
 * once at least one sample has validated. Only ever moves ABSENT ->
 * {NO_DATA, OK} or NO_DATA <-> OK — never back to ABSENT while s_imu_dev
 * stays open, since a re-init that fails a WHO_AM_I re-check tears the
 * device down and this driver treats that as staying NO_DATA (a chip
 * that answered once is not "absent", it is unhealthy). */
static ff_compass_imu_state_t s_imu_state = FF_COMPASS_IMU_ABSENT;

/* Runtime re-init bookkeeping for ff_compass_imu_maybe_reinit — see that
 * function's own doc comment. All three are in units of
 * esp_timer_get_time()/1000 milliseconds (ff_display.c/ff_power.c's own
 * now_ms convention); 0 is a valid sentinel for
 * "not currently in an invalid streak" / "never attempted yet" since
 * esp_timer_get_time() is relative to boot, never exactly 0 by the time
 * this driver's first sample runs. */
static uint32_t s_imu_invalid_since_ms;
static uint32_t s_imu_last_reinit_ms;
static int s_imu_reinit_attempts;

static ff_geo_cal_t s_cal;
static bool s_cal_valid;

/* Last heading `ff_compass_read()` returned, for `ff_compass_status()`'s
 * one-shot diagnostic snapshot (ff_compass.h). Explicitly -1 ("unknown"
 * — the SAME sentinel `ff_compass_read()` itself uses), not the
 * zero-init a plain `static float` would give: 0 deg is a real,
 * fabricated-looking heading (due north) and would be dishonest as a
 * "nothing has been read yet" default. */
static float s_last_heading_deg = -1.0f;

/* S12 step 3 — the board-frame magnetometer vector (post axis-remap,
 * BEFORE calibration) from the most recent `ff_compass_read()` call,
 * for `ff_compass_last_mag_board()` (see that function's own doc
 * comment for why this exists: the calibration ritual needs the EXACT
 * same vector `ff_geo_heading_deg` is handed, not a second I2C
 * transaction of its own). Zero-vector default is honest: "no real
 * reading yet" and "a degenerate/absent magnetometer" both correctly
 * read as (0,0,0) here, matching `ff_compass_read()`'s own "no mag
 * present" early-return, which never touches this variable at all. */
static ff_vec3_t s_last_mag_board = {0.0f, 0.0f, 0.0f};

/* S31 Music/Swarm — the board-frame ACCELEROMETER vector (post
 * axis-remap, the same `accel_board` `ff_geo_heading_deg` was handed)
 * from the most recent `ff_compass_read()` call, for
 * `ff_compass_last_accel_board()` — the small accessor S31's own spec
 * asked for ("ff_compass for the IMU accel access — add a small
 * accessor if there is none"; there was none before this). Same
 * "most recent, not a fresh transaction" / "honest zero before any
 * real reading" contract as `s_last_mag_board` above, and the same
 * assumed-level fallback ((0,0,1) — see this file's own "Honesty
 * contract" top-of-header comment) when the IMU never identified or
 * has no trustworthy data yet: this accessor mirrors whatever
 * `ff_compass_read()` actually fed the heading math, never a second,
 * independently-sourced reading. */
static ff_vec3_t s_last_accel_board = {0.0f, 0.0f, 0.0f};

/* ff_compass_read() runs at 10 Hz (app_main.c's own
 * FF_COMPASS_SAMPLE_PERIOD_MS) from the main render-loop task — a bus
 * fault (NACK/timeout) on that path can repeat every tick for as long
 * as the fault persists. Log the first occurrence of each failure kind
 * so it isn't silent, then go quiet rather than spamming the log at
 * 10 Hz for the rest of the session (PR #212 review: gate on this). */
static bool s_mag_read_warned;
static bool s_imu_read_warned;
static bool s_imu_invalid_warned; /* same "log once" posture, for ff_compass_imu_validate rejections */
static bool s_i2c_lock_warned; /* same "log once" posture, for a failed ff_display_i2c_bus_lock acquire */

/* =====================================================================
 * Small I2C helpers shared by every probe/bring-up/read below.
 * ===================================================================== */
static esp_err_t ff_compass_add_dev(i2c_master_bus_handle_t bus, uint16_t addr, i2c_master_dev_handle_t *out)
{
    i2c_device_config_t const cfg = {
        .dev_addr_length = I2C_ADDR_BIT_LEN_7,
        .device_address = addr,
        .scl_speed_hz = FF_COMPASS_I2C_HZ,
    };
    return i2c_master_bus_add_device(bus, &cfg, out);
}

static esp_err_t ff_compass_reg_write(i2c_master_dev_handle_t dev, uint8_t reg, uint8_t val)
{
    uint8_t const buf[2] = {reg, val};
    return i2c_master_transmit(dev, buf, sizeof(buf), FF_COMPASS_I2C_TIMEOUT_MS);
}

static esp_err_t ff_compass_reg_read(i2c_master_dev_handle_t dev, uint8_t reg, uint8_t *out, size_t n)
{
    return i2c_master_transmit_receive(dev, &reg, 1, out, n, FF_COMPASS_I2C_TIMEOUT_MS);
}

/* =====================================================================
 * Probe + bring-up: onboard QMI8658 IMU.
 * ===================================================================== */

/* Address the IMU identified at, kept so a runtime re-init
 * (ff_compass_imu_maybe_reinit) can re-run the SAME bring-up sequence on
 * the SAME already-open device handle without re-probing both
 * candidate addresses again. Meaningless while s_imu_dev is NULL. */
static uint16_t s_imu_addr;

/* ff_compass_imu_bringup — the QMI8658 bring-up sequence proper, run
 * against an already-open `dev` at `addr` (for logging only): soft
 * reset, settle, re-verify WHO_AM_I, then CTRL1/CTRL2/CTRL7. Shared by
 * the initial probe (ff_compass_probe_imu) and the runtime re-init path
 * (ff_compass_imu_maybe_reinit) — see this file's FF_QMI8658_REG_RESET
 * block comment for the datasheet citations behind every step and every
 * timing constant used here. Returns ESP_OK only if every step
 * succeeded AND the post-reset WHO_AM_I re-read still matches; any
 * failure leaves `dev`'s registers in whatever partial state the failed
 * write left them in (same posture the pre-existing code already had
 * for a bring-up write failure) — the caller decides whether that means
 * "treat as absent" (first probe) or "still configured, try again
 * later" (re-init). */
static esp_err_t ff_compass_imu_bringup(i2c_master_dev_handle_t dev, uint16_t addr)
{
    /* 1. Soft reset (RESET=0x60, write 0xB0 — QMI8658C datasheet Table
     * 31, cited in full on FF_QMI8658_REG_RESET above). */
    esp_err_t const rst = ff_compass_reg_write(dev, FF_QMI8658_REG_RESET, FF_QMI8658_RESET_VAL);
    if (rst != ESP_OK) {
        ESP_LOGW(TAG, "QMI8658 @0x%02X: soft-reset write failed (%s)", addr, esp_err_to_name(rst));
        return rst;
    }

    /* 2. Settle — see FF_QMI8658_RESET_SETTLE_MS's own comment for why
     * this is NOT the datasheet's full ~150 ms System Turn On Time. */
    vTaskDelay(pdMS_TO_TICKS(FF_QMI8658_RESET_SETTLE_MS));

    /* 3. Re-verify WHO_AM_I post-reset — a chip that just reset should
     * still identify the same way; if it doesn't (NACK, wrong value),
     * something is wrong with the reset itself and writing config on
     * top of it would be building on an unverified foundation. */
    uint8_t who = 0;
    esp_err_t const who_err = ff_compass_reg_read(dev, FF_QMI8658_REG_WHO_AM_I, &who, 1);
    if (who_err != ESP_OK || who != FF_QMI8658_WHO_AM_I_VAL) {
        ESP_LOGW(TAG, "QMI8658 @0x%02X: post-reset WHO_AM_I re-check failed (err=%s who=0x%02X)", addr,
                 esp_err_to_name(who_err), who);
        return (who_err != ESP_OK) ? who_err : ESP_ERR_INVALID_RESPONSE;
    }

    /* 4-6. CTRL1 (address auto-increment), CTRL2 (accel range/ODR),
     * CTRL7 (aEN|sys_hs) — same bytes/citations the pre-existing code
     * already used, just now run after a verified reset rather than
     * straight after the first WHO_AM_I. */
    esp_err_t const c1 = ff_compass_reg_write(dev, FF_QMI8658_REG_CTRL1, FF_QMI8658_CTRL1_VAL);
    esp_err_t const c2 = ff_compass_reg_write(dev, FF_QMI8658_REG_CTRL2, FF_QMI8658_CTRL2_VAL);
    esp_err_t const c7 = ff_compass_reg_write(dev, FF_QMI8658_REG_CTRL7, FF_QMI8658_CTRL7_VAL);
    if (c1 != ESP_OK || c2 != ESP_OK || c7 != ESP_OK) {
        ESP_LOGW(TAG, "QMI8658 @0x%02X: bring-up write failed (CTRL1=%s CTRL2=%s CTRL7=%s)", addr,
                 esp_err_to_name(c1), esp_err_to_name(c2), esp_err_to_name(c7));
        return ESP_FAIL;
    }
    return ESP_OK;
}

/* ff_compass_imu_wait_data_ready — poll STATUS0 (0x2E) bit0 (aDA) until
 * it reads 1 or `timeout_ms` elapses, per this file's FF_QMI8658_REG_RESET
 * block comment. Returns true iff aDA was observed set — this is a
 * diagnostic wait for the BOOT log/initial state only
 * (ff_compass_probe_imu); ff_compass_read() does its own per-sample
 * validation regardless of what this returned, so a false here degrades
 * the reported imu_state (NO_DATA instead of OK) rather than ever
 * blocking a real read. */
static bool ff_compass_imu_wait_data_ready(i2c_master_dev_handle_t dev, uint32_t timeout_ms)
{
    uint32_t waited_ms = 0;
    while (waited_ms <= timeout_ms) {
        uint8_t status0 = 0;
        if (ff_compass_reg_read(dev, FF_QMI8658_REG_STATUS0, &status0, 1) == ESP_OK &&
            (status0 & FF_QMI8658_STATUS0_ADA_BIT) != 0) {
            return true;
        }
        vTaskDelay(pdMS_TO_TICKS(FF_QMI8658_DATA_READY_POLL_MS));
        waited_ms += FF_QMI8658_DATA_READY_POLL_MS;
    }
    return false;
}

static void ff_compass_probe_imu(i2c_master_bus_handle_t bus)
{
    uint16_t const addrs[2] = {FF_QMI8658_ADDR_PRIMARY, FF_QMI8658_ADDR_ALT};

    for (size_t i = 0; i < 2; i++) {
        i2c_master_dev_handle_t dev = NULL;
        if (ff_compass_add_dev(bus, addrs[i], &dev) != ESP_OK) {
            continue;
        }

        uint8_t who = 0;
        esp_err_t err = ff_compass_reg_read(dev, FF_QMI8658_REG_WHO_AM_I, &who, 1);
        if (err == ESP_OK && who == FF_QMI8658_WHO_AM_I_VAL) {
            if (ff_compass_imu_bringup(dev, addrs[i]) == ESP_OK) {
                s_imu_dev = dev;
                s_imu_addr = addrs[i];
                s_imu_present = true;
                bool const ready = ff_compass_imu_wait_data_ready(dev, FF_QMI8658_DATA_READY_TIMEOUT_MS);
                s_imu_state = ready ? FF_COMPASS_IMU_OK : FF_COMPASS_IMU_NO_DATA;
                ESP_LOGI(TAG,
                         "QMI8658 IMU found @0x%02X (WHO_AM_I=0x%02X) — accel up (CTRL2=0x%02X CTRL7=0x%02X), "
                         "data-ready=%s",
                         addrs[i], who, FF_QMI8658_CTRL2_VAL, FF_QMI8658_CTRL7_VAL, ready ? "yes" : "NOT YET");
                if (!ready) {
                    ESP_LOGW(TAG,
                             "QMI8658 @0x%02X: STATUS0 aDA never set within %u ms of bring-up — accel engine may "
                             "not have started (bench evidence, 2026-09-07: this happens on a real board even "
                             "though every bring-up write returned ESP_OK); ff_compass_read will keep validating "
                             "every sample and re-run bring-up if data never becomes real",
                             addrs[i], (unsigned)FF_QMI8658_DATA_READY_TIMEOUT_MS);
                }
                return;
            }
            ESP_LOGW(TAG, "QMI8658 @0x%02X identified but bring-up failed — treating as absent", addrs[i]);
        }
        i2c_master_bus_rm_device(dev);
    }

    ESP_LOGW(TAG, "compass: no IMU — assuming level (tilt compensation unavailable on this path)");
}

/* ff_compass_imu_validate — true iff `raw` (sensor-frame, pre-remap) is
 * plausible real accelerometer data at the CTRL2-configured ±4g range:
 * no axis sits exactly at the int16 rail (the QMI8658's own
 * saturation/never-converted sentinel pattern — this file's
 * FF_QMI8658_REG_RESET block comment cites where 0.3g/3g come from) and
 * the vector's magnitude falls within [0.3g, 3g]. Comparing squared
 * magnitude against squared bounds avoids a sqrtf on this file's 10 Hz
 * hot path for no behavioral difference (both sides are non-negative by
 * construction). */
static bool ff_compass_imu_validate(int16_t rx, int16_t ry, int16_t rz)
{
    if (rx == FF_QMI8658_ACCEL_SENTINEL_MIN || rx == FF_QMI8658_ACCEL_SENTINEL_MAX ||
        ry == FF_QMI8658_ACCEL_SENTINEL_MIN || ry == FF_QMI8658_ACCEL_SENTINEL_MAX ||
        rz == FF_QMI8658_ACCEL_SENTINEL_MIN || rz == FF_QMI8658_ACCEL_SENTINEL_MAX) {
        return false;
    }

    float const min_lsb = FF_QMI8658_ACCEL_MIN_G * FF_QMI8658_ACCEL_LSB_PER_G;
    float const max_lsb = FF_QMI8658_ACCEL_MAX_G * FF_QMI8658_ACCEL_LSB_PER_G;
    float const mag_sq = (float)rx * (float)rx + (float)ry * (float)ry + (float)rz * (float)rz;
    return mag_sq >= (min_lsb * min_lsb) && mag_sq <= (max_lsb * max_lsb);
}

/* ff_compass_imu_maybe_reinit — called from ff_compass_read() only while
 * the current sample just failed ff_compass_imu_validate. Tracks how
 * long the invalid streak has run (`now_ms`) and, once it exceeds
 * FF_QMI8658_REINIT_INVALID_MS, re-runs ff_compass_imu_bringup on the
 * SAME device handle — rate-limited to at most once per
 * FF_QMI8658_REINIT_RATE_LIMIT_MS and capped at
 * FF_QMI8658_REINIT_MAX_ATTEMPTS total attempts, so a permanently dead
 * accel engine (this task's own bench case) logs a bounded number of
 * retries rather than hammering the shared I2C bus forever. Every
 * attempt and its outcome is logged — never silent. Leaves s_imu_state
 * at NO_DATA regardless of outcome; ff_compass_read's own caller moves
 * it back to OK the moment a subsequent sample validates. */
static void ff_compass_imu_maybe_reinit(uint32_t now_ms)
{
    if (s_imu_invalid_since_ms == 0) {
        s_imu_invalid_since_ms = (now_ms != 0) ? now_ms : 1; /* 0 stays reserved for "no streak" */
        return;
    }
    if ((now_ms - s_imu_invalid_since_ms) < FF_QMI8658_REINIT_INVALID_MS) {
        return;
    }
    if (s_imu_reinit_attempts >= FF_QMI8658_REINIT_MAX_ATTEMPTS) {
        return; /* already gave up — logged once, on the attempt that hit the cap below */
    }
    if (s_imu_last_reinit_ms != 0 && (now_ms - s_imu_last_reinit_ms) < FF_QMI8658_REINIT_RATE_LIMIT_MS) {
        return;
    }

    s_imu_last_reinit_ms = (now_ms != 0) ? now_ms : 1;
    s_imu_reinit_attempts++;
    esp_err_t const err = ff_compass_imu_bringup(s_imu_dev, s_imu_addr);
    ESP_LOGW(TAG, "QMI8658 @0x%02X: accel data invalid for >%u ms — re-init attempt %d/%d: %s", s_imu_addr,
             (unsigned)FF_QMI8658_REINIT_INVALID_MS, s_imu_reinit_attempts, FF_QMI8658_REINIT_MAX_ATTEMPTS,
             (err == ESP_OK) ? "bring-up ok, watching next samples" : esp_err_to_name(err));
    if (s_imu_reinit_attempts >= FF_QMI8658_REINIT_MAX_ATTEMPTS) {
        ESP_LOGW(TAG, "QMI8658 @0x%02X: giving up after %d re-init attempts — imu=no-data until next boot",
                 s_imu_addr, s_imu_reinit_attempts);
    }
}

/* =====================================================================
 * Probe + bring-up: GY-273 magnetometer (QMC5883L, then HMC5883L).
 * ===================================================================== */
static bool ff_compass_probe_qmc5883l(i2c_master_bus_handle_t bus)
{
    i2c_master_dev_handle_t dev = NULL;
    if (ff_compass_add_dev(bus, FF_QMC5883L_ADDR, &dev) != ESP_OK) {
        return false;
    }

    uint8_t chip_id = 0;
    if (ff_compass_reg_read(dev, FF_QMC5883L_REG_CHIPID, &chip_id, 1) == ESP_OK &&
        chip_id == FF_QMC5883L_CHIPID_VAL) {
        esp_err_t const sr = ff_compass_reg_write(dev, FF_QMC5883L_REG_SETRESET, FF_QMC5883L_SETRESET_VAL);
        esp_err_t const c1 = ff_compass_reg_write(dev, FF_QMC5883L_REG_CTRL1, FF_QMC5883L_CTRL1_VAL);
        if (sr == ESP_OK && c1 == ESP_OK) {
            s_mag_dev = dev;
            s_mag_kind = FF_COMPASS_MAG_QMC5883L;
            ESP_LOGI(TAG,
                     "QMC5883L magnetometer found @0x%02X (chip id 0x%02X) — continuous, 10 Hz, 2G, OSR 512 "
                     "(CTRL1=0x%02X)",
                     FF_QMC5883L_ADDR, chip_id, FF_QMC5883L_CTRL1_VAL);
            return true;
        }
        ESP_LOGW(TAG, "QMC5883L identified but a bring-up write failed — treating as absent");
    }
    i2c_master_bus_rm_device(dev);
    return false;
}

static bool ff_compass_probe_hmc5883l(i2c_master_bus_handle_t bus)
{
    i2c_master_dev_handle_t dev = NULL;
    if (ff_compass_add_dev(bus, FF_HMC5883L_ADDR, &dev) != ESP_OK) {
        return false;
    }

    uint8_t id[3] = {0};
    if (ff_compass_reg_read(dev, FF_HMC5883L_REG_ID_A, id, sizeof(id)) == ESP_OK && id[0] == 'H' &&
        id[1] == '4' && id[2] == '3') {
        esp_err_t const cra = ff_compass_reg_write(dev, FF_HMC5883L_REG_CRA, FF_HMC5883L_CRA_VAL);
        esp_err_t const crb = ff_compass_reg_write(dev, FF_HMC5883L_REG_CRB, FF_HMC5883L_CRB_VAL);
        esp_err_t const mode = ff_compass_reg_write(dev, FF_HMC5883L_REG_MODE, FF_HMC5883L_MODE_VAL);
        if (cra == ESP_OK && crb == ESP_OK && mode == ESP_OK) {
            s_mag_dev = dev;
            s_mag_kind = FF_COMPASS_MAG_HMC5883L;
            ESP_LOGI(TAG,
                     "HMC5883L magnetometer found @0x%02X (id \"%c%c%c\") — continuous mode (CRA=0x%02X "
                     "CRB=0x%02X)",
                     FF_HMC5883L_ADDR, id[0], id[1], id[2], FF_HMC5883L_CRA_VAL, FF_HMC5883L_CRB_VAL);
            return true;
        }
        ESP_LOGW(TAG, "HMC5883L identified but a bring-up write failed — treating as absent");
    }
    i2c_master_bus_rm_device(dev);
    return false;
}

static bool ff_compass_probe_qmc5883p(i2c_master_bus_handle_t bus)
{
    i2c_master_dev_handle_t dev = NULL;
    if (ff_compass_add_dev(bus, FF_QMC5883P_ADDR, &dev) != ESP_OK) {
        return false;
    }

    uint8_t chip_id = 0;
    if (ff_compass_reg_read(dev, FF_QMC5883P_REG_CHIPID, &chip_id, 1) != ESP_OK) {
        /* Nothing ACKed at 0x2C at all — not this chip. */
        i2c_master_bus_rm_device(dev);
        return false;
    }
    if (chip_id != FF_QMC5883P_CHIPID_VAL) {
        /* Something answers at 0x2C but its chip id isn't the QMC5883P's
         * documented 0x80 (datasheet section 9.2.1) — log what it
         * actually said and walk away rather than guessing which chip
         * this is (honesty contract, ff_compass.h: no fabricated
         * heading from an unidentified device). */
        ESP_LOGW(TAG,
                 "device @0x%02X answered but chip id 0x%02X != QMC5883P's 0x%02X — not treating as a "
                 "magnetometer",
                 FF_QMC5883P_ADDR, chip_id, FF_QMC5883P_CHIPID_VAL);
        i2c_master_bus_rm_device(dev);
        return false;
    }

    /* Bring-up order per the datasheet's own worked examples (7.1/7.2,
     * "Continuous/Normal Mode Setup Example") plus the soft-reset step
     * (7.6) FIRST so a warm-boot re-probe (e.g. after a watchdog reset
     * that never power-cycled the sensor) starts from POR defaults
     * rather than whatever mode a previous boot left it in. */
    esp_err_t const rst = ff_compass_reg_write(dev, FF_QMC5883P_REG_CTRL2, FF_QMC5883P_SOFT_RST_VAL);
    esp_err_t const sign = ff_compass_reg_write(dev, FF_QMC5883P_REG_SIGN, FF_QMC5883P_SIGN_VAL);
    esp_err_t const c2 = ff_compass_reg_write(dev, FF_QMC5883P_REG_CTRL2, FF_QMC5883P_CTRL2_VAL);
    esp_err_t const c1 = ff_compass_reg_write(dev, FF_QMC5883P_REG_CTRL1, FF_QMC5883P_CTRL1_VAL);
    if (rst == ESP_OK && sign == ESP_OK && c2 == ESP_OK && c1 == ESP_OK) {
        s_mag_dev = dev;
        s_mag_kind = FF_COMPASS_MAG_QMC5883P;
        ESP_LOGI(TAG,
                 "QMC5883P magnetometer found @0x%02X (chip id 0x%02X) — continuous, 50 Hz, 2G, OSR1=8 OSR2=8 "
                 "(CTRL1=0x%02X CTRL2=0x%02X)",
                 FF_QMC5883P_ADDR, chip_id, FF_QMC5883P_CTRL1_VAL, FF_QMC5883P_CTRL2_VAL);
        return true;
    }
    ESP_LOGW(TAG, "QMC5883P identified but a bring-up write failed — treating as absent");
    i2c_master_bus_rm_device(dev);
    return false;
}

static void ff_compass_probe_mag(i2c_master_bus_handle_t bus)
{
    /* QMC5883L first — the far more common chip on a GY-273 board even
     * when silkscreened HMC (see ff_compass.h's top comment). */
    if (ff_compass_probe_qmc5883l(bus)) {
        return;
    }
    if (ff_compass_probe_hmc5883l(bus)) {
        return;
    }
    if (ff_compass_probe_qmc5883p(bus)) {
        return;
    }

    ESP_LOGW(TAG,
             "compass: no magnetometer found (checked QMC5883L @0x%02X, HMC5883L @0x%02X, QMC5883P @0x%02X) — "
             "heading will read unknown (-1) forever",
             FF_QMC5883L_ADDR, FF_HMC5883L_ADDR, FF_QMC5883P_ADDR);
}

/* =====================================================================
 * Public API.
 * ===================================================================== */
esp_err_t ff_compass_init(i2c_master_bus_handle_t bus)
{
    s_mag_dev = NULL;
    s_imu_dev = NULL;
    s_mag_kind = FF_COMPASS_MAG_NONE;
    s_imu_present = false;
    s_imu_addr = 0;
    s_imu_state = FF_COMPASS_IMU_ABSENT;
    s_imu_invalid_since_ms = 0;
    s_imu_last_reinit_ms = 0;
    s_imu_reinit_attempts = 0;

    if (bus == NULL) {
        ESP_LOGE(TAG, "ff_compass_init called with a NULL I2C bus handle (ff_display_i2c_bus not up yet?)");
        return ESP_ERR_INVALID_ARG;
    }

    ff_compass_probe_imu(bus);
    ff_compass_probe_mag(bus);

    /* Non-fatal either way — see this function's own doc comment
     * (ff_compass.h) and ff_power_batt_init's matching "log and
     * continue" posture. */
    return ESP_OK;
}

bool ff_compass_present(void)
{
    return s_mag_kind != FF_COMPASS_MAG_NONE;
}

ff_compass_mag_kind_t ff_compass_mag_kind(void)
{
    return s_mag_kind;
}

char const *ff_compass_mag_kind_name(ff_compass_mag_kind_t kind)
{
    switch (kind) {
    case FF_COMPASS_MAG_QMC5883L: return "qmc5883l";
    case FF_COMPASS_MAG_HMC5883L: return "hmc5883l";
    case FF_COMPASS_MAG_QMC5883P: return "qmc5883p";
    case FF_COMPASS_MAG_NONE: return "none";
    }
    return "none"; /* unreachable for a value from this file's own enum, but -Werror wants a return on every path */
}

char const *ff_compass_imu_state_name(ff_compass_imu_state_t state)
{
    switch (state) {
    case FF_COMPASS_IMU_ABSENT: return "absent";
    case FF_COMPASS_IMU_NO_DATA: return "no-data";
    case FF_COMPASS_IMU_OK: return "ok";
    }
    return "absent"; /* unreachable for a value from this file's own enum, but -Werror wants a return on every path */
}

bool ff_compass_imu_present(void)
{
    return s_imu_present;
}

void ff_compass_set_cal(ff_geo_cal_t const *cal)
{
    if (cal == NULL) {
        s_cal_valid = false;
        return;
    }
    s_cal = *cal;
    s_cal_valid = true;
}

float ff_compass_read(void)
{
    if (s_mag_kind == FF_COMPASS_MAG_NONE || s_mag_dev == NULL) {
        s_last_heading_deg = -1.0f; /* honest "unknown" — no magnetometer, never a fabricated heading */
        return -1.0f;
    }

    /* Touch-vs-compass I2C fix: fence this ENTIRE multi-transaction
     * sample (mag read + imu read below, both against the shared bus
     * ff_display_i2c_bus() returns) against the touch driver's own
     * multi-transaction SPD2010 read (ff_display.c's
     * ff_touch_gate_read_cb) — see ff_display_i2c_bus_lock's doc
     * comment (ff_display.h) for the bench evidence this closes. A
     * failed lock (touch mid-poll) degrades this sample to the same
     * honest -1 "unknown" sentinel a NACK/timeout already produces,
     * rather than block the main render-loop task or risk an
     * interleaved read. Held until every return below — unlocked right
     * before each one. */
    if (!ff_display_i2c_bus_lock(FF_COMPASS_I2C_BUS_LOCK_TIMEOUT_MS)) {
        if (!s_i2c_lock_warned) {
            s_i2c_lock_warned = true;
            ESP_LOGW(TAG, "shared I2C bus busy (touch mid-read) — heading reports -1 this sample (logged once)");
        }
        s_last_heading_deg = -1.0f;
        return -1.0f;
    }

    ff_vec3_t mag_raw = {0};
    uint8_t buf[6];

    if (s_mag_kind == FF_COMPASS_MAG_QMC5883L) {
        if (ff_compass_reg_read(s_mag_dev, FF_QMC5883L_REG_DATA, buf, sizeof(buf)) != ESP_OK) {
            if (!s_mag_read_warned) {
                s_mag_read_warned = true;
                ESP_LOGW(TAG, "magnetometer read failed (NACK/timeout) — heading reports -1 until it recovers "
                              "(logged once)");
            }
            s_last_heading_deg = -1.0f; /* -1 sentinel, never a stale heading */
            ff_display_i2c_bus_unlock();
            return -1.0f;
        }
        mag_raw.x = (float)(int16_t)((buf[1] << 8) | buf[0]);
        mag_raw.y = (float)(int16_t)((buf[3] << 8) | buf[2]);
        mag_raw.z = (float)(int16_t)((buf[5] << 8) | buf[4]);
    } else if (s_mag_kind == FF_COMPASS_MAG_HMC5883L) {
        if (ff_compass_reg_read(s_mag_dev, FF_HMC5883L_REG_DATA, buf, sizeof(buf)) != ESP_OK) {
            if (!s_mag_read_warned) {
                s_mag_read_warned = true;
                ESP_LOGW(TAG, "magnetometer read failed (NACK/timeout) — heading reports -1 until it recovers "
                              "(logged once)");
            }
            s_last_heading_deg = -1.0f; /* -1 sentinel, never a stale heading */
            ff_display_i2c_bus_unlock();
            return -1.0f;
        }
        /* HMC5883L's own data order is X, Z, Y (not X,Y,Z), big-endian
         * per axis — see this file's FF_HMC5883L_REG_DATA comment. */
        mag_raw.x = (float)(int16_t)((buf[0] << 8) | buf[1]);
        mag_raw.z = (float)(int16_t)((buf[2] << 8) | buf[3]);
        mag_raw.y = (float)(int16_t)((buf[4] << 8) | buf[5]);
    } else { /* FF_COMPASS_MAG_QMC5883P */
        if (ff_compass_reg_read(s_mag_dev, FF_QMC5883P_REG_DATA, buf, sizeof(buf)) != ESP_OK) {
            if (!s_mag_read_warned) {
                s_mag_read_warned = true;
                ESP_LOGW(TAG, "magnetometer read failed (NACK/timeout) — heading reports -1 until it recovers "
                              "(logged once)");
            }
            s_last_heading_deg = -1.0f; /* -1 sentinel, never a stale heading */
            ff_display_i2c_bus_unlock();
            return -1.0f;
        }
        /* QMC5883P's data order is X,Y,Z, little-endian per axis, same
         * shape as the QMC5883L (datasheet Table 15). */
        mag_raw.x = (float)(int16_t)((buf[1] << 8) | buf[0]);
        mag_raw.y = (float)(int16_t)((buf[3] << 8) | buf[2]);
        mag_raw.z = (float)(int16_t)((buf[5] << 8) | buf[4]);
    }

    ff_vec3_t accel_board;
    if (s_imu_present && s_imu_dev != NULL) {
        uint8_t abuf[6];
        if (ff_compass_reg_read(s_imu_dev, FF_QMI8658_REG_AX_L, abuf, sizeof(abuf)) == ESP_OK) {
            int16_t const rx = (int16_t)((abuf[1] << 8) | abuf[0]);
            int16_t const ry = (int16_t)((abuf[3] << 8) | abuf[2]);
            int16_t const rz = (int16_t)((abuf[5] << 8) | abuf[4]);

            if (ff_compass_imu_validate(rx, ry, rz)) {
                ff_vec3_t const accel_raw = {.x = (float)rx, .y = (float)ry, .z = (float)rz};
                accel_board = ff_compass_remap(accel_raw, FF_IMU_BOARD_X_SRC, FF_IMU_BOARD_X_SIGN,
                                                FF_IMU_BOARD_Y_SRC, FF_IMU_BOARD_Y_SIGN, FF_IMU_BOARD_Z_SRC,
                                                FF_IMU_BOARD_Z_SIGN);
                s_imu_state = FF_COMPASS_IMU_OK;
                s_imu_invalid_since_ms = 0;
                s_imu_reinit_attempts = 0; /* a real sample recovered — a future fault gets a fresh backoff budget */
            } else {
                /* Sentinel (0x8000/0x7FFF) or out-of-[0.3g,3g] data —
                 * the second-board defect this driver now catches
                 * instead of feeding ff_geo_heading_deg a fabricated
                 * level vector forever (this file's FF_QMI8658_REG_RESET
                 * block comment has the bench evidence and datasheet
                 * citations). Degrade exactly like a transient NACK
                 * (assumed level, never a fabricated tilt), but ALSO
                 * track how long this has been going on so a
                 * permanently-stuck accel engine gets a bounded re-init
                 * retry rather than reading "assumed level" forever. */
                if (!s_imu_invalid_warned) {
                    s_imu_invalid_warned = true;
                    ESP_LOGW(TAG,
                             "IMU accel data invalid (raw (%d,%d,%d) — sentinel or outside [%.1fg,%.1fg]) — "
                             "assuming level this sample (logged once; re-init retried if this persists)",
                             rx, ry, rz, (double)FF_QMI8658_ACCEL_MIN_G, (double)FF_QMI8658_ACCEL_MAX_G);
                }
                s_imu_state = FF_COMPASS_IMU_NO_DATA;
                accel_board = (ff_vec3_t){0.0f, 0.0f, 1.0f};
                ff_compass_imu_maybe_reinit((uint32_t)(esp_timer_get_time() / 1000));
            }
        } else {
            /* A transient read failure degrades to level-assumed rather
             * than feeding ff_geo_heading_deg stale/garbage tilt data. */
            if (!s_imu_read_warned) {
                s_imu_read_warned = true;
                ESP_LOGW(TAG, "IMU accel read failed (NACK/timeout) — assuming level this sample (logged once)");
            }
            accel_board = (ff_vec3_t){0.0f, 0.0f, 1.0f};
        }
    } else {
        accel_board = (ff_vec3_t){0.0f, 0.0f, 1.0f}; /* assume level — logged once at init, see ff_compass_probe_imu */
    }

    /* QMC5883P gets its OWN axis-map row (FF_MAG_QMC5883P_BOARD_*) — see
     * that table's own comment for why it is not shared with the
     * QMC5883L/HMC5883L row (FF_MAG_BOARD_*) used for the other two. */
    ff_vec3_t const mag_board = (s_mag_kind == FF_COMPASS_MAG_QMC5883P)
        ? ff_compass_remap(mag_raw, FF_MAG_QMC5883P_BOARD_X_SRC, FF_MAG_QMC5883P_BOARD_X_SIGN,
                            FF_MAG_QMC5883P_BOARD_Y_SRC, FF_MAG_QMC5883P_BOARD_Y_SIGN,
                            FF_MAG_QMC5883P_BOARD_Z_SRC, FF_MAG_QMC5883P_BOARD_Z_SIGN)
        : ff_compass_remap(mag_raw, FF_MAG_BOARD_X_SRC, FF_MAG_BOARD_X_SIGN, FF_MAG_BOARD_Y_SRC,
                            FF_MAG_BOARD_Y_SIGN, FF_MAG_BOARD_Z_SRC, FF_MAG_BOARD_Z_SIGN);

    s_last_mag_board = mag_board; /* S12 step 3 — see ff_compass_last_mag_board()'s doc comment */
    s_last_accel_board = accel_board; /* S31 Music/Swarm — see ff_compass_last_accel_board()'s doc comment */

    float const heading = ff_geo_heading_deg(mag_board, accel_board, s_cal_valid ? &s_cal : NULL);
    s_last_heading_deg = heading;
    ff_display_i2c_bus_unlock();
    return heading;
}

ff_compass_status_t ff_compass_status(void)
{
    ff_compass_status_t st = {0};
    st.mag_present = ff_compass_present();
    st.mag_kind = ff_compass_mag_kind();
    st.imu_present = ff_compass_imu_present();
    st.imu_state = s_imu_state;
    st.heading_valid = (s_last_heading_deg >= 0.0f);
    st.last_heading_deg = s_last_heading_deg;
    return st;
}

ff_vec3_t ff_compass_last_mag_board(void)
{
    return s_last_mag_board;
}

ff_vec3_t ff_compass_last_accel_board(void)
{
    return s_last_accel_board;
}
