jakeholland/firefly/firmware/targets/esp32s3/components/esp_lcd_touch_spd2010/esp_lcd_touch_spd2010.c

/*
 * SPDX-FileCopyrightText: 2023 Espressif Systems (Shanghai) CO LTD
 *
 * SPDX-License-Identifier: Apache-2.0
 */

/*
 * FIREFLY VENDORED COPY of espressif/esp_lcd_touch_spd2010 v2.0.1
 * (esp-iot-solution commit c29b0042d4011d907f78a484f12ed187e65cbeab).
 *
 * WHY VENDORED (do not "clean up" back to the managed component):
 * The stock driver reads registers with `esp_lcd_panel_io_rx_param(tp->io,
 * 0, buf, len)` — i.e. lcd_cmd = 0, not -1. Under ESP-IDF 5.3.x's NEW
 * i2c_master driver, esp_lcd's i2c panel IO (esp_lcd_panel_io_i2c_v2.c)
 * treats any lcd_cmd != -1 as "send a command first", so it calls
 * i2c_master_transmit_receive() with a ZERO-length write phase (control
 * phase is disabled and lcd_cmd_bits = 0 in ESP_LCD_TOUCH_IO_I2C_SPD2010_
 * CONFIG). i2c_master_transmit_receive() rejects write_size == 0 with
 * ESP_ERR_INVALID_ARG ("i2c transmit buffer or size invalid"), so
 * read_fw_version() fails and esp_lcd_touch_new_i2c_spd2010() aborts —
 * the exact STAGE-3 failure seen on the bench. The SPD2010 protocol is a
 * write (sets the register pointer) followed by a SEPARATE pure read; the
 * correct panel-IO idiom for a pure read is lcd_cmd = -1, which routes to
 * i2c_master_receive(). The registry has no newer version fixing this
 * (2.0.1 is latest as of 2026-08-26), so the one-line fix lives here.
 *
 * FUNCTIONAL CHANGES FROM UPSTREAM v2.0.1 (FIVE sites — a future re-sync to a
 * fixed release must account for ALL of them; each is marked "FIREFLY PATCH"
 * inline):
 *   1. `i2c_read` macro: lcd_cmd 0 -> -1 (the init-read fix described above).
 *   2. `read_data`: a failed/no-data read reports 0 points + ESP_OK instead of
 *      propagating an error, so polling mode (int_gpio_num = -1) doesn't
 *      panic-loop via esp_lvgl_port's ESP_ERROR_CHECK — matches Waveshare's
 *      demo, which polls and ignores the return.
 *   3. `read_tp_hdp`: guard the zero-length i2c read (read_len == 0).
 *   4. `read_tp_hdp` remain-data path: guard the zero-length i2c read
 *      (next_packet_len == 0).
 *   5. `read_data`: drop any point whose x/y falls outside
 *      tp->config.x_max/y_max before it ever reaches tp->data.coords —
 *      a corrupted read (bench-confirmed cause: unfenced I2C
 *      interleaving with another device on the same shared bus, see
 *      ff_display_i2c_bus_lock's doc comment in ff_display.h) can
 *      return ESP_OK with a nonzero touch_num and an out-of-range
 *      coordinate, which upstream would report as a genuine press.
 * (2)-(4) are the read-side twins of the same new-i2c_master zero-length-
 * transfer rejection that (1) fixes on the init path. Everything else is
 * byte-for-byte upstream.
 *
 *   6. `read_data`: a failed `tp_read_data()` now also counts toward a
 *      running touch-read-failure health counter (per-minute rate +
 *      lifetime total, `esp_lcd_touch_spd2010_touch_health()`) and emits
 *      ITS OWN rate-limited (>= 1/s) summary line instead of letting a
 *      failing bus (cracked panel, bench-observed 2026-09-08 — a failed
 *      multi-transaction read roughly every 40 ms) flood the console with
 *      four raw ESP_LOGE lines per failure (two from this file's own
 *      ESP_RETURN_ON_ERROR chain, TAG "SPD2010"; two more from ESP-IDF's
 *      i2c_master/lcd_panel.io.i2c layers underneath). The three
 *      underlying tags are muted to ESP_LOG_NONE once, at the end of a
 *      successful `esp_lcd_touch_new_i2c_spd2010()` (so an INIT-time
 *      failure still logs normally) — see that function's own comment for
 *      why NONE, not WARN, is required to actually silence an ESP_LOGE
 *      call, and for the one real tradeoff (a *different* device sharing
 *      the bus loses the generic i2c.master line too; ff_compass.c logs
 *      its own failures under its own tag regardless, so no signal is
 *      actually lost — see this component's QA-hardening PR body).
 */

#include <inttypes.h>
#include <stdio.h>
#include <string.h>
#include <stdint.h>

#include "freertos/FreeRTOS.h"
#include "freertos/task.h"
#include "driver/gpio.h"
#include "driver/i2c.h"
#include "esp_system.h"
#include "esp_err.h"
#include "esp_log.h"
#include "esp_check.h"
#include "esp_timer.h" /* FIREFLY PATCH #6 — esp_timer_get_time() for the health-counter window/log rate-limit */
#include "esp_lcd_panel_io.h"
#include "esp_lcd_touch.h"

static const char *TAG = "SPD2010";
/* FIREFLY PATCH #6 — a separate tag for this driver's OWN rate-limited
 * summary line, deliberately NOT "SPD2010": esp_lcd_touch_new_i2c_spd2010
 * mutes "SPD2010" to ESP_LOG_NONE once init succeeds (see that function),
 * and a summary log sharing that tag would silence itself along with the
 * raw per-call spam it exists to replace. */
static const char *HEALTH_TAG = "spd2010_health";

/* FIREFLY PATCH #6 — touch-read health counter (S15/QA-hardening).
 * `window_fail`/`window_start_ms` track the CURRENTLY OPEN ~60 s window;
 * `last_rate_per_min` is the count from the last window that actually
 * CLOSED — reporting the open window instead would understate an ongoing
 * flood that hasn't reached 60 s yet. Not a true sliding window (a fixed
 * fixed-size bucket that rolls over every 60 s), which is an honest
 * approximation good enough for a bench "how bad is it" reading, not a
 * precision rate meter. */
typedef struct {
    uint32_t total_fail;        /* lifetime failed tp_read_data() calls */
    uint32_t window_fail;       /* failures counted in the still-open window */
    uint32_t window_start_ms;   /* esp_timer ms this window started (0 == never started) */
    uint32_t last_rate_per_min; /* the most recently CLOSED window's failure count */
} spd2010_touch_health_t;

static spd2010_touch_health_t s_touch_health;
static int64_t s_touch_fail_log_last_us;

#define SPD2010_HEALTH_WINDOW_MS ((uint32_t)60u * 1000u)
#define SPD2010_FAIL_LOG_MIN_GAP_MS ((int64_t)1000) /* our own summary: at most 1/s, vs. the ~40ms raw flood */

/**
 * [api] Touch-read health, for the Diagnostics page / bench `diag` console
 * line (2026-09-08 QA-hardening ask: "touch read failures per minute").
 * Either output pointer may be NULL. `*out_fail_per_min` is honestly 0
 * both when nothing has ever failed AND for the first (still-open) ~60 s
 * after a failure starts — see the struct's own doc comment.
 */
void esp_lcd_touch_spd2010_touch_health(uint32_t *out_total_fail, uint32_t *out_fail_per_min)
{
    if (out_total_fail != NULL) {
        *out_total_fail = s_touch_health.total_fail;
    }
    if (out_fail_per_min != NULL) {
        *out_fail_per_min = s_touch_health.last_rate_per_min;
    }
}

typedef struct {
    uint8_t none0;
    uint8_t none1;
    uint8_t none2;
    uint8_t cpu_run;
    uint8_t tint_low;
    uint8_t tic_in_cpu;
    uint8_t tic_in_bios;
    uint8_t tic_busy;
} tp_status_high_t;

typedef struct {
    uint8_t pt_exist;
    uint8_t gesture;
    uint8_t key;
    uint8_t aux;
    uint8_t keep;
    uint8_t raw_or_pt;
    uint8_t none6;
    uint8_t none7;
} tp_status_low_t;

typedef struct {
    tp_status_low_t status_low;
    tp_status_high_t status_high;
    uint16_t read_len;
} tp_status_t;

typedef struct {
    uint8_t id;
    uint16_t x;
    uint16_t y;
    uint8_t weight;
} tp_report_t;

typedef struct {
    tp_report_t rpt[10];
    uint8_t touch_num;
    uint8_t pack_code;
    uint8_t down;
    uint8_t up;
    uint8_t gesture;
    uint16_t down_x;
    uint16_t down_y;
    uint16_t up_x;
    uint16_t up_y;
} tp_touch_t;

typedef struct {
    uint8_t status;
    uint16_t next_packet_len;
} tp_hdp_status_t;

static esp_err_t read_data(esp_lcd_touch_handle_t tp);
static bool get_xy(esp_lcd_touch_handle_t tp, uint16_t *x, uint16_t *y, uint16_t *strength, uint8_t *point_num, uint8_t max_point_num);
static esp_err_t del(esp_lcd_touch_handle_t tp);
static esp_err_t reset(esp_lcd_touch_handle_t tp);

static esp_err_t write_tp_point_mode_cmd(esp_lcd_touch_handle_t tp);
static esp_err_t write_tp_start_cmd(esp_lcd_touch_handle_t tp);
static esp_err_t write_tp_cpu_start_cmd(esp_lcd_touch_handle_t tp);
static esp_err_t write_tp_clear_int_cmd(esp_lcd_touch_handle_t tp);
static esp_err_t read_tp_status_length(esp_lcd_touch_handle_t tp, tp_status_t *tp_status);
static esp_err_t read_tp_hdp(esp_lcd_touch_handle_t tp, tp_status_t *tp_status, tp_touch_t *touch);
static esp_err_t read_tp_hdp_status(esp_lcd_touch_handle_t tp, tp_hdp_status_t *tp_hdp_status);
static esp_err_t read_fw_version(esp_lcd_touch_handle_t tp);
static esp_err_t tp_read_data(esp_lcd_touch_handle_t tp, tp_touch_t *touch);

esp_err_t esp_lcd_touch_new_i2c_spd2010(const esp_lcd_panel_io_handle_t io, const esp_lcd_touch_config_t *config, esp_lcd_touch_handle_t *tp)
{
    ESP_RETURN_ON_FALSE(io, ESP_ERR_INVALID_ARG, TAG, "Invalid io");
    ESP_RETURN_ON_FALSE(config, ESP_ERR_INVALID_ARG, TAG, "Invalid config");
    ESP_RETURN_ON_FALSE(tp, ESP_ERR_INVALID_ARG, TAG, "Invalid touch handle");

    /* Prepare main structure */
    esp_err_t ret = ESP_OK;
    esp_lcd_touch_handle_t spd2010 = calloc(1, sizeof(esp_lcd_touch_t));
    ESP_GOTO_ON_FALSE(spd2010, ESP_ERR_NO_MEM, err, TAG, "Touch handle malloc failed");

    /* Communication interface */
    spd2010->io = io;
    /* Only supported callbacks are set */
    spd2010->read_data = read_data;
    spd2010->get_xy = get_xy;
    spd2010->del = del;
    /* Mutex */
    spd2010->data.lock.owner = portMUX_FREE_VAL;
    /* Save config */
    memcpy(&spd2010->config, config, sizeof(esp_lcd_touch_config_t));

    /* Prepare pin for touch interrupt */
    if (config->int_gpio_num != GPIO_NUM_NC) {
        const gpio_config_t int_gpio_config = {
            .mode = GPIO_MODE_INPUT,
            .intr_type = (config->levels.interrupt) ? GPIO_INTR_POSEDGE : GPIO_INTR_NEGEDGE,
            .pin_bit_mask = BIT64(config->int_gpio_num)
        };
        ESP_GOTO_ON_ERROR(gpio_config(&int_gpio_config), err, TAG, "GPIO intr config failed");

        /* Register interrupt callback */
        if (config->interrupt_callback) {
            esp_lcd_touch_register_interrupt_callback(spd2010, config->interrupt_callback);
        }
    }
    /* Prepare pin for touch controller reset */
    if (config->rst_gpio_num != GPIO_NUM_NC) {
        const gpio_config_t rst_gpio_config = {
            .mode = GPIO_MODE_OUTPUT,
            .pin_bit_mask = BIT64(config->rst_gpio_num)
        };
        ESP_GOTO_ON_ERROR(gpio_config(&rst_gpio_config), err, TAG, "GPIO reset config failed");
    }
    /* Reset controller */
    ESP_GOTO_ON_ERROR(reset(spd2010), err, TAG, "Reset failed");
    ESP_GOTO_ON_ERROR(read_fw_version(spd2010), err, TAG, "Read version failed");

    ESP_LOGI(TAG, "Touch panel create success, version: %d.%d.%d", ESP_LCD_TOUCH_SPD2010_VER_MAJOR,
             ESP_LCD_TOUCH_SPD2010_VER_MINOR, ESP_LCD_TOUCH_SPD2010_VER_PATCH);

    /* FIREFLY PATCH #6 — mute the raw per-transaction error logs a failing
     * bus would otherwise flood every ~40 ms (see this file's top comment
     * and read_data()'s own health-counter block). Deliberately AFTER the
     * success log above and only on this success path: an INIT-time
     * failure (reset/read_fw_version above) still logs normally via the
     * `err:` label's ESP_LOGE, which runs before this line is ever
     * reached. ESP_LOG_NONE, not ESP_LOG_WARN — esp_log_level_set filters
     * AT OR BELOW the given level (NONE < ERROR < WARN < ...), so nothing
     * short of NONE silences an ESP_LOGE call. Idempotent / safe to set
     * more than once (there is only ever one touch controller on this
     * board, so this runs once in practice). */
    esp_log_level_set(TAG, ESP_LOG_NONE);
    esp_log_level_set("i2c.master", ESP_LOG_NONE);
    esp_log_level_set("lcd_panel.io.i2c", ESP_LOG_NONE);

    *tp = spd2010;

    return ESP_OK;
err:
    if (spd2010) {
        del(spd2010);
    }
    ESP_LOGE(TAG, "Initialization failed!");
    return ret;
}

static esp_err_t read_data(esp_lcd_touch_handle_t tp)
{
    uint8_t touch_cnt = 0;

    tp_touch_t touch = {0};
    /* FIREFLY PATCH (S15b polling read path): Waveshare's OWN ESP-IDF-5.3.2
     * demo (ESP32-S3-Touch-LCD-1.46, Touch_Driver/Touch_SPD2010.c,
     * Touch_Read_Data) POLLS this exact chain from LVGL's indev read_cb and
     * IGNORES tp_read_data's return entirely — a poll with no finger down
     * simply yields touch_num == 0, never an error. esp_lvgl_port wraps
     * esp_lcd_touch_read_data() in ESP_ERROR_CHECK (managed_components/
     * espressif__esp_lvgl_port/src/lvgl9/esp_lvgl_port_touch.c:127), so a
     * propagated error here PANIC-LOOPS the device on every empty poll in
     * polling mode (int_gpio_num = -1). Match the demo: a failed / no-data
     * read reports zero points and returns ESP_OK — 0 points is the honest
     * "no touch". A real press still fills touch.touch_num below. */
    if (tp_read_data(tp, &touch) != ESP_OK) {
        touch.touch_num = 0;

        /* FIREFLY PATCH #6 — health counter + our own rate-limited
         * summary, replacing the raw per-call ESP_LOGE flood (silenced
         * below, once, at the end of esp_lcd_touch_new_i2c_spd2010). */
        uint32_t const now_ms = (uint32_t)(esp_timer_get_time() / 1000);
        if (s_touch_health.window_start_ms == 0u) {
            s_touch_health.window_start_ms = now_ms; /* first failure ever */
        } else if ((uint32_t)(now_ms - s_touch_health.window_start_ms) >= SPD2010_HEALTH_WINDOW_MS) {
            s_touch_health.last_rate_per_min = s_touch_health.window_fail;
            s_touch_health.window_fail = 0u;
            s_touch_health.window_start_ms = now_ms;
        }
        s_touch_health.window_fail++;
        s_touch_health.total_fail++;

        int64_t const fail_now_us = esp_timer_get_time();
        if (s_touch_fail_log_last_us == 0 ||
            (fail_now_us - s_touch_fail_log_last_us) >= SPD2010_FAIL_LOG_MIN_GAP_MS * 1000) {
            s_touch_fail_log_last_us = fail_now_us;
            ESP_LOGW(HEALTH_TAG,
                     "touch read failing (bus fault or panel damage?) - %" PRIu32 " total, ~%" PRIu32
                     "/min last window (raw i2c/SPD2010 error logs suppressed below ERROR to avoid flooding)",
                     s_touch_health.total_fail, s_touch_health.last_rate_per_min);
        }
    }

    portENTER_CRITICAL(&tp->data.lock);
    /* Expect Number of touched points */
    touch_cnt = (touch.touch_num > CONFIG_ESP_LCD_TOUCH_MAX_POINTS ? CONFIG_ESP_LCD_TOUCH_MAX_POINTS : touch.touch_num);

    /* FIREFLY PATCH (touch-vs-compass I2C fix): x_max/y_max (this
     * driver's config, set to the panel's own resolution by
     * ff_display_touch_start) is the only coordinate range a genuine
     * touch on THIS glass can ever report. A corrupted read (e.g. the
     * shared-I2C-bus interleaving ff_display_i2c_bus_lock's doc comment
     * describes) can still make tp_read_data() return ESP_OK with a
     * nonzero touch_num and garbage rpt[].x/.y outside that range — the
     * bench-observed phantom press. Drop any such point here, at the
     * source, rather than let it reach LVGL as a "real" press that only
     * a downstream clamp happens to make look plausible: compact the
     * valid points to the front and shrink the reported count, so an
     * all-garbage read degrades to the same honest "0 points" a
     * NACK/timeout already produces. */
    uint8_t valid_cnt = 0;
    for (int i = 0; i < touch_cnt; i++) {
        if (touch.rpt[i].x < tp->config.x_max && touch.rpt[i].y < tp->config.y_max) {
            tp->data.coords[valid_cnt].x = touch.rpt[i].x;
            tp->data.coords[valid_cnt].y = touch.rpt[i].y;
            tp->data.coords[valid_cnt].strength = touch.rpt[i].weight;
            valid_cnt++;
        }
    }
    tp->data.points = valid_cnt;
    portEXIT_CRITICAL(&tp->data.lock);

    return ESP_OK;
}

static bool get_xy(esp_lcd_touch_handle_t tp, uint16_t *x, uint16_t *y, uint16_t *strength, uint8_t *point_num, uint8_t max_point_num)
{
    portENTER_CRITICAL(&tp->data.lock);
    /* Count of points */
    *point_num = (tp->data.points > max_point_num ? max_point_num : tp->data.points);
    for (size_t i = 0; i < *point_num; i++) {
        x[i] = tp->data.coords[i].x;
        y[i] = tp->data.coords[i].y;

        if (strength) {
            strength[i] = tp->data.coords[i].strength;
        }
    }
    /* Clear available touch points count */
    tp->data.points = 0;
    portEXIT_CRITICAL(&tp->data.lock);

    return (*point_num > 0);
}

static esp_err_t del(esp_lcd_touch_handle_t tp)
{
    /* Reset GPIO pin settings */
    if (tp->config.int_gpio_num != GPIO_NUM_NC) {
        gpio_reset_pin(tp->config.int_gpio_num);
    }
    if (tp->config.rst_gpio_num != GPIO_NUM_NC) {
        gpio_reset_pin(tp->config.rst_gpio_num);
        if (tp->config.interrupt_callback) {
            gpio_isr_handler_remove(tp->config.int_gpio_num);
        }
    }
    /* Release memory */
    free(tp);

    return ESP_OK;
}

static esp_err_t reset(esp_lcd_touch_handle_t tp)
{
    TickType_t delay_tick = 0;

    if (tp->config.rst_gpio_num != GPIO_NUM_NC) {
        ESP_RETURN_ON_ERROR(gpio_set_level(tp->config.rst_gpio_num, tp->config.levels.reset), TAG, "GPIO set level failed");
        delay_tick = pdMS_TO_TICKS(2);
        vTaskDelay((delay_tick > 0) ? delay_tick : 1);
        ESP_RETURN_ON_ERROR(gpio_set_level(tp->config.rst_gpio_num, !tp->config.levels.reset), TAG, "GPIO set level failed");
        delay_tick = pdMS_TO_TICKS(22);
        vTaskDelay((delay_tick > 0) ? delay_tick : 1);
    }

    return ESP_OK;
}

#define i2c_write(data_p, len)      ESP_RETURN_ON_ERROR(esp_lcd_panel_io_tx_param(tp->io, 0, data_p, len), TAG, "Tx failed");
/* FIREFLY PATCH: lcd_cmd -1 (was 0) -> a PURE i2c read (i2c_master_receive),
 * no zero-length write phase. See the file-header note. The preceding
 * i2c_write() already latched the register pointer; this reads from it. */
#define i2c_read(data_p, len)       ESP_RETURN_ON_ERROR(esp_lcd_panel_io_rx_param(tp->io, -1, data_p, len), TAG, "Rx failed");

static esp_err_t write_tp_point_mode_cmd(esp_lcd_touch_handle_t tp)
{
    uint8_t sample_data[4];

    sample_data[0] = 0x50;
    sample_data[1] = 0x00;
    sample_data[2] = 0x00;
    sample_data[3] = 0x00;

    i2c_write(&sample_data[0], sizeof(sample_data));
    esp_rom_delay_us(200);
    return ESP_OK;
}

static esp_err_t write_tp_start_cmd(esp_lcd_touch_handle_t tp)
{
    uint8_t sample_data[4];

    sample_data[0] = 0x46;
    sample_data[1] = 0x00;
    sample_data[2] = 0x00;
    sample_data[3] = 0x00;

    i2c_write(&sample_data[0], sizeof(sample_data));
    esp_rom_delay_us(200);
    return ESP_OK;
}

static esp_err_t write_tp_cpu_start_cmd(esp_lcd_touch_handle_t tp)
{
    uint8_t sample_data[4];

    sample_data[0] = 0x04;
    sample_data[1] = 0x00;
    sample_data[2] = 0x01;
    sample_data[3] = 0x00;

    i2c_write(&sample_data[0], sizeof(sample_data));
    esp_rom_delay_us(200);
    return ESP_OK;
}

static esp_err_t write_tp_clear_int_cmd(esp_lcd_touch_handle_t tp)
{
    uint8_t sample_data[4];

    sample_data[0] = 0x02;
    sample_data[1] = 0x00;
    sample_data[2] = 0x01;
    sample_data[3] = 0x00;

    i2c_write(&sample_data[0], sizeof(sample_data));
    esp_rom_delay_us(200);
    return ESP_OK;
}

static esp_err_t read_tp_status_length(esp_lcd_touch_handle_t tp, tp_status_t *tp_status)
{
    uint8_t sample_data[4];

    sample_data[0] = 0x20;
    sample_data[1] = 0x00;

    i2c_write(&sample_data[0], 2);
    esp_rom_delay_us(200);
    i2c_read(&sample_data[0], sizeof(sample_data));
    esp_rom_delay_us(200);
    tp_status->status_low.pt_exist = (sample_data[0] & 0x01);
    tp_status->status_low.gesture = (sample_data[0] & 0x02);
    tp_status->status_high.tic_busy = ((sample_data[1] & 0x80) >> 7);
    tp_status->status_high.tic_in_bios = ((sample_data[1] & 0x40) >> 6);
    tp_status->status_high.tic_in_cpu = ((sample_data[1] & 0x20) >> 5);
    tp_status->status_high.tint_low = ((sample_data[1] & 0x10) >> 4);
    tp_status->status_high.cpu_run = ((sample_data[1] & 0x08) >> 3);
    tp_status->status_low.aux = ((sample_data[0] & 0x08)); //aux, cytang

    tp_status->read_len = (sample_data[3] << 8 | sample_data[2]);
    return ESP_OK;
}

static esp_err_t read_tp_hdp(esp_lcd_touch_handle_t tp, tp_status_t *tp_status, tp_touch_t *touch)
{
    uint8_t sample_data[4 + (10 * 6)]; // 4 Bytes Header + 10 Finger * 6 Bytes
    uint8_t i, offset;
    uint8_t check_id;

    /* FIREFLY PATCH (S15b): read_len is the HDP byte count the status
     * register (0x2000) just reported. Under ESP-IDF 5.3.x's new i2c_master
     * a zero-length i2c_master_receive() returns ESP_ERR_INVALID_ARG (the
     * read-side twin of the zero-length-write bug documented in this file's
     * header) — which, propagated up, panic-loops esp_lvgl_port's
     * ESP_ERROR_CHECK when the chip flags a point but has no HDP payload
     * ready yet (e.g. the release edge). No bytes to read == no touch:
     * report zero points instead of issuing the zero-length read. */
    if (tp_status->read_len == 0) {
        touch->touch_num = 0x00;
        touch->gesture = 0x00;
        return ESP_OK;
    }

    sample_data[0] = 0x00;
    sample_data[1] = 0x03;

    i2c_write(&sample_data[0], 2);
    esp_rom_delay_us(200);
    i2c_read(&sample_data[0], tp_status->read_len);
    esp_rom_delay_us(200);

    check_id = sample_data[4];

    if ((check_id <= 0x0A) && tp_status->status_low.pt_exist) {
        touch->touch_num = ((tp_status->read_len - 4) / 6);
        touch->gesture = 0x00;

        for (i = 0; i < touch->touch_num; i++) {
            offset = i * 6;
            touch->rpt[i].id = sample_data[4 + offset];
            touch->rpt[i].x = (((sample_data[7 + offset] & 0xF0) << 4) | sample_data[5 + offset]);
            touch->rpt[i].y = (((sample_data[7 + offset] & 0x0F) << 8) | sample_data[6 + offset]);
            touch->rpt[i].weight = sample_data[8 + offset];
        }

        /* For slide gesture recognize */
        if ((touch->rpt[0].weight != 0) && (touch->down != 1)) {
            touch->down = 1;
            touch->up = 0 ;
            touch->down_x = touch->rpt[0].x;
            touch->down_y = touch->rpt[0].y;
        } else if ((touch->rpt[0].weight == 0) && (touch->down == 1)) {
            touch->up = 1;
            touch->down = 0;
            touch->up_x = touch->rpt[0].x;
            touch->up_y = touch->rpt[0].y;
        }

        /* Dump Log */
        for (uint8_t finger_num = 0; finger_num < touch->touch_num; finger_num++) {
            ESP_LOGD(TAG, "ID[%d], X[%d], Y[%d], Weight[%d]\n",
                     touch->rpt[finger_num].id,
                     touch->rpt[finger_num].x,
                     touch->rpt[finger_num].y,
                     touch->rpt[finger_num].weight);
        }
    } else if ((check_id == 0xF6) && tp_status->status_low.gesture) {
        touch->touch_num = 0x00;
        touch->up = 0;
        touch->down = 0;
        touch->gesture = sample_data[6] & 0x07;
        ESP_LOGD(TAG, "gesture : 0x%02x\n", touch->gesture);
    } else {
        touch->touch_num = 0x00;
        touch->gesture = 0x00;
    }
    return ESP_OK;
}

static esp_err_t read_tp_hdp_status(esp_lcd_touch_handle_t tp, tp_hdp_status_t *tp_hdp_status)
{
    uint8_t sample_data[8];

    sample_data[0] = 0xFC;
    sample_data[1] = 0x02;

    i2c_write(&sample_data[0], 2);
    esp_rom_delay_us(200);
    i2c_read(&sample_data[0], sizeof(sample_data));
    esp_rom_delay_us(200);

    tp_hdp_status->status = sample_data[5];
    tp_hdp_status->next_packet_len = (sample_data[2] | sample_data[3] << 8);
    return ESP_OK;
}

static esp_err_t Read_HDP_REMAIN_DATA(esp_lcd_touch_handle_t tp, tp_hdp_status_t *tp_hdp_status)
{
    uint8_t sample_data[32];

    /* FIREFLY PATCH (S15b): same zero-length-read guard as read_tp_hdp —
     * next_packet_len == 0 means the HDP drain is done, so there is nothing
     * left to fetch; issuing a zero-length i2c_master_receive() would fail
     * under the new i2c_master driver and abort the poll. */
    if (tp_hdp_status->next_packet_len == 0) {
        return ESP_OK;
    }

    sample_data[0] = 0x00;
    sample_data[1] = 0x03;

    i2c_write(&sample_data[0], 2);
    esp_rom_delay_us(200);
    i2c_read(&sample_data[0], tp_hdp_status->next_packet_len);
    esp_rom_delay_us(200);
    return ESP_OK;
}
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
